mirdej/synkie/eagle/sk200-vcf-singlepole/sk200-vcf-singlepole.pdf

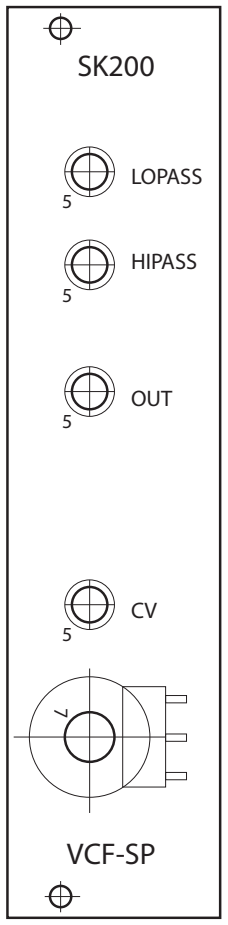
[picture p21: figure]
LOPASS; HIPASS; OUT; VCF-SP
