mirdej/synkie/kicad/synkie_footprint_models/PTL20-10G0-103B2.STEP

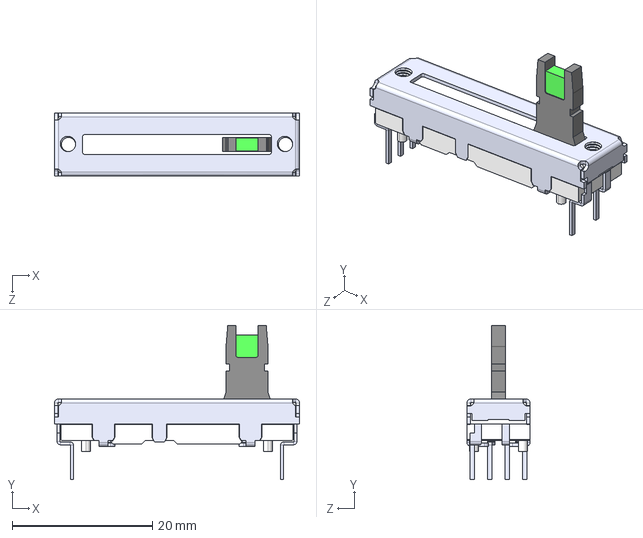
[picture p37: CAD file, 2025-10-26]
kicad/synkie_footprint_models/PTL20-10G0-103B2.STEP
35.0 x 22.0 x 9.00 mm
