mirdej/synkie/kicad/synkie_footprint_models/RK09K1130A70.stp

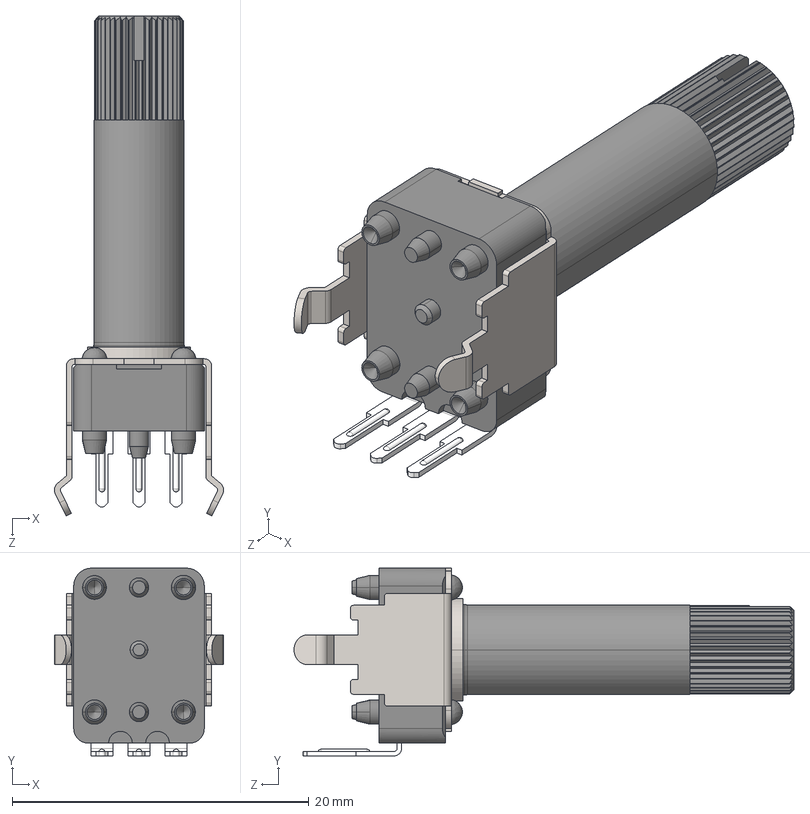
[picture p38: CAD file, 2025-10-26]
kicad/synkie_footprint_models/RK09K1130A70.stp
11.4 x 12.7 x 33.7 mm
