mirdej/synkie/kicad/synkie_footprint_models/SKQGAKE010.stp

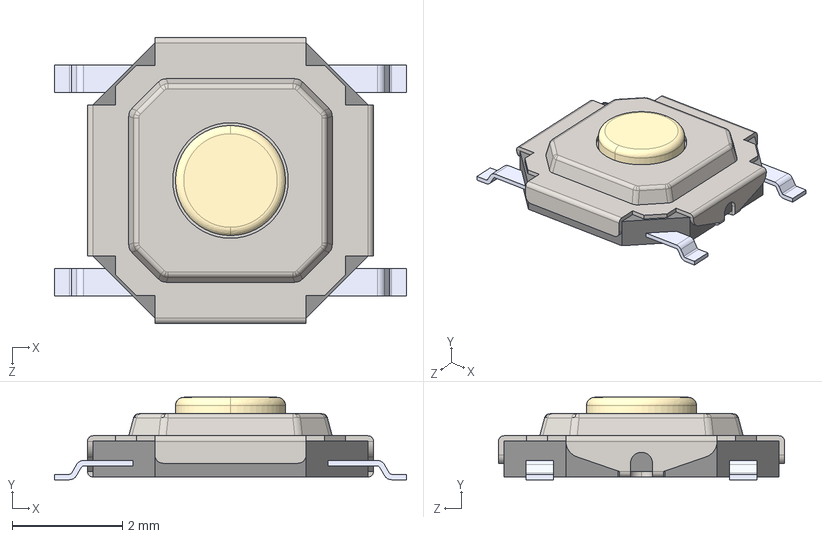
[picture p39: CAD file, 2025-10-26]
kicad/synkie_footprint_models/SKQGAKE010.stp
6.40 x 1.50 x 5.20 mm
SKQGADE010
SKQGADE010_4
SKQGADE010_3
SKQGADE010_7
SKQGADE010_2
SKQGADE010_6
SKQGADE010_5
