mirdej/synkie/kicad/synkie_footprint_models/PJ301M-12 Thonkiconn v0.2.stp

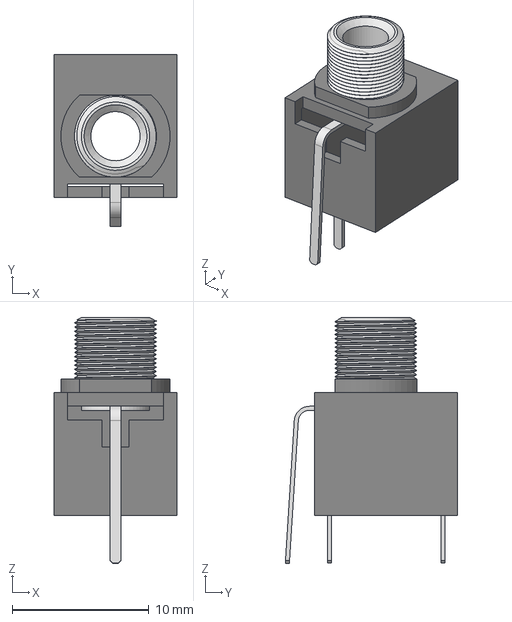
[picture p40: CAD file, 2025-10-26]
kicad/synkie_footprint_models/PJ301M-12 Thonkiconn v0.2.stp
9.00 x 12.6 x 18.0 mm
