mirdej/synkie/eagle/sk160-6channel-mixer/sk160-6channel-faders_pcb.pdf

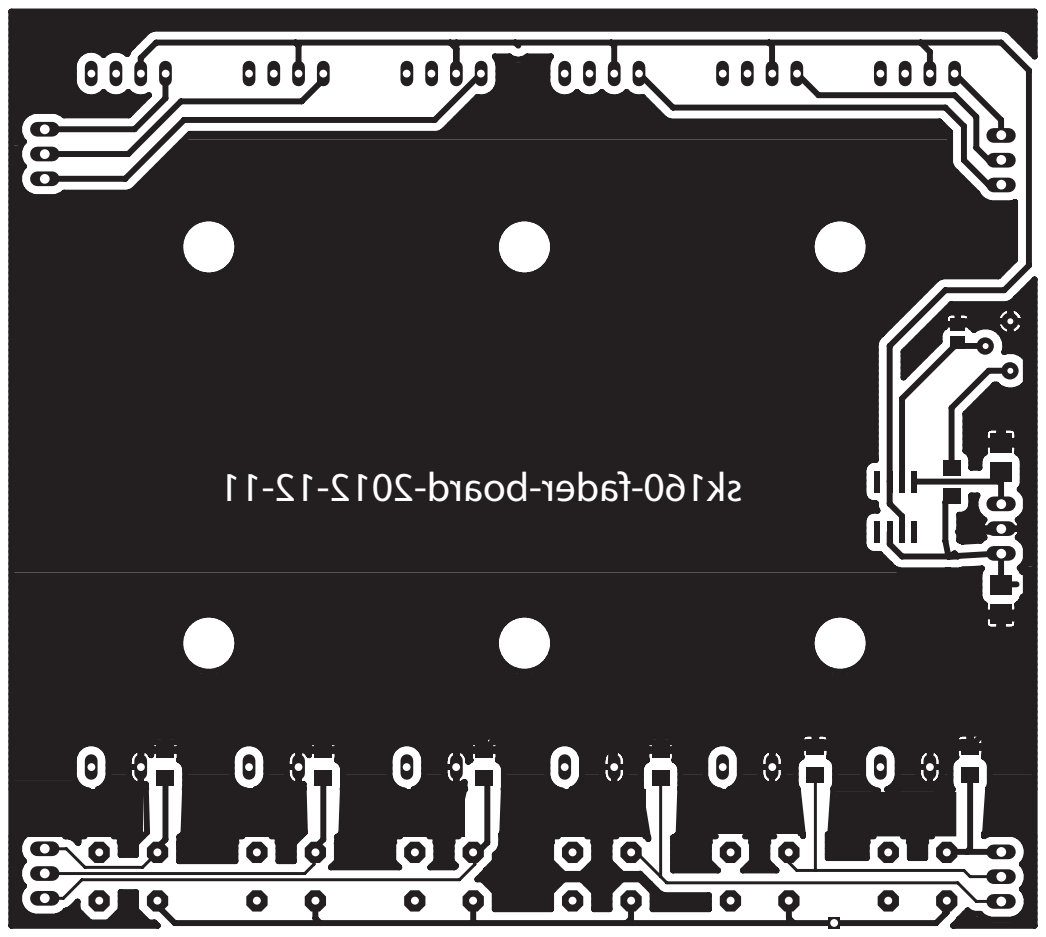
[picture p41: page 1]
sk160-fader-board-2012-12-11
