mirdej/synkie/kicad/digipotitest/digipotitest-F.Cu.pdf

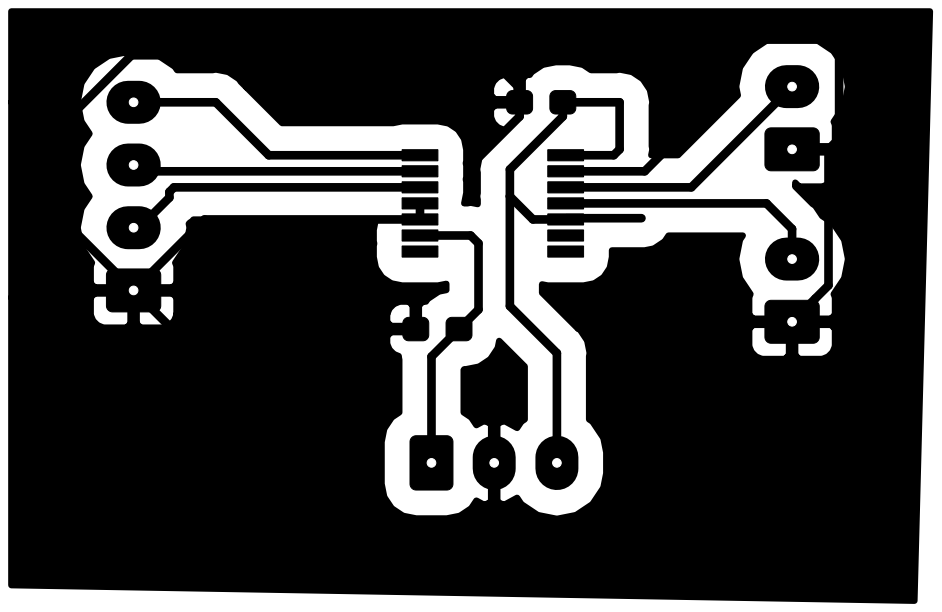
[picture p49: page 1]
