mirdej/synkie/kicad/digipotitest/digipotitest-F.Mask.pdf

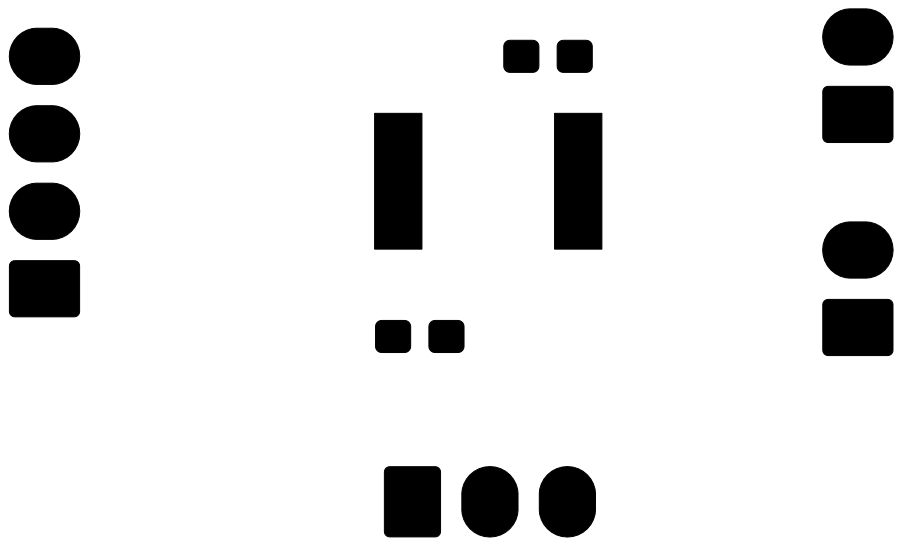
[picture p50: page 1]
