mirdej/synkie/kicad/digipotitest/digipotitest-F.Paste.pdf

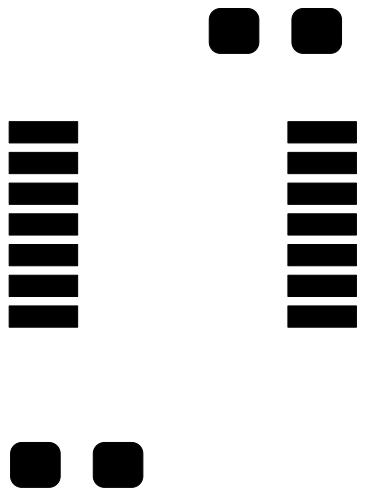
[picture p51: page 1]
