mirdej/synkie/kicad/digipotitest/digipotitest-F.SilkS.pdf

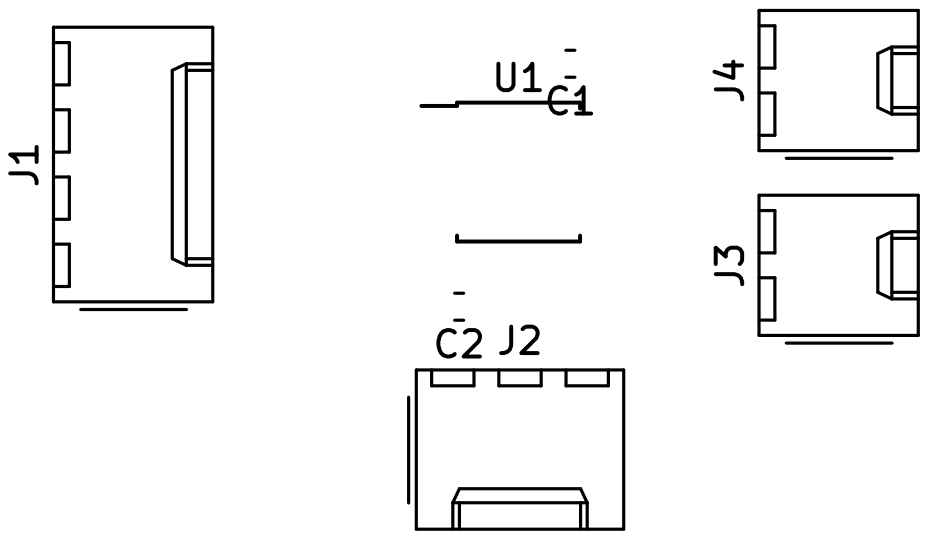
[picture p52: page 1]
