mirdej/synkie/kicad/sk950-teensy-osc/sk950-teensy-osc-B.Cu.pdf

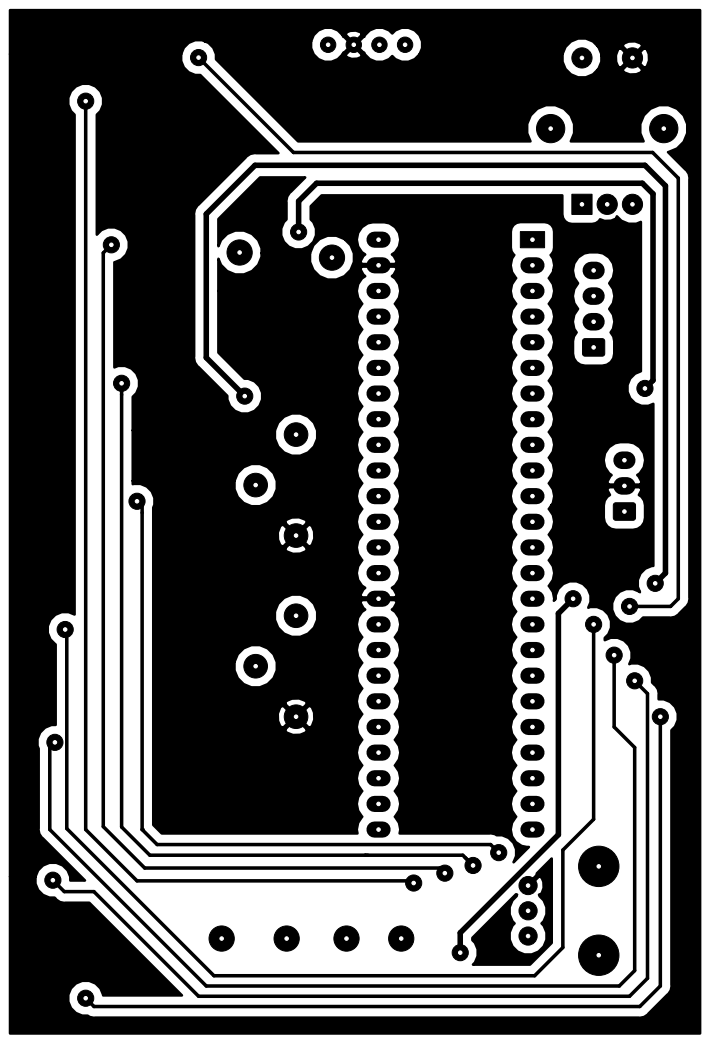
[picture p53: page 1]
