mirdej/synkie/kicad/sk950-teensy-osc/sk950-teensy-osc-F.Cu.pdf

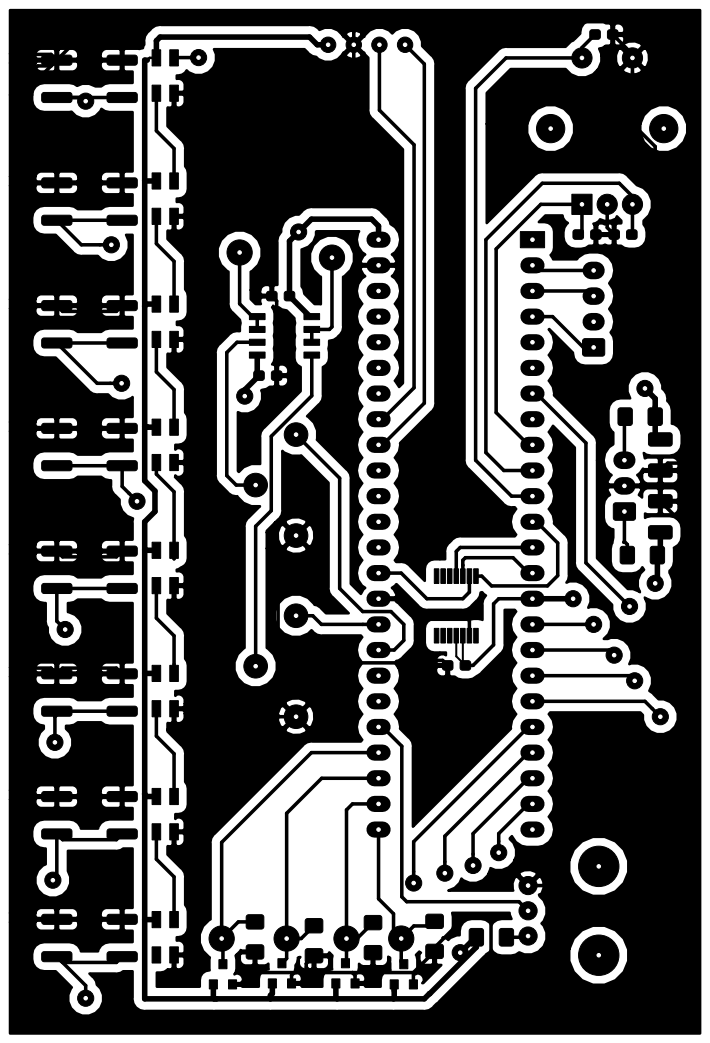
[picture p54: page 1]
