mirdej/synkie/eagle/sk53-audio2cv/sk53-frontplate.pdf

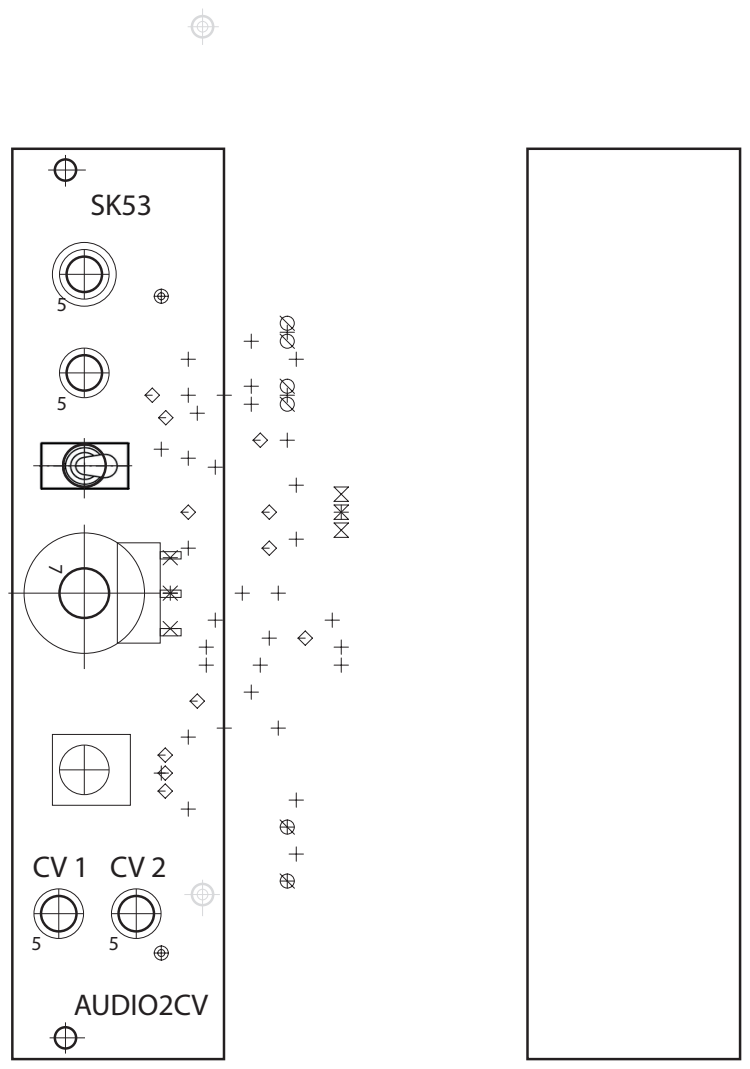
[picture p55: page 1]
AUDIO2CV
