mirdej/synkie/eagle/sk800-rgb/sk800-rgb-frontplate.pdf

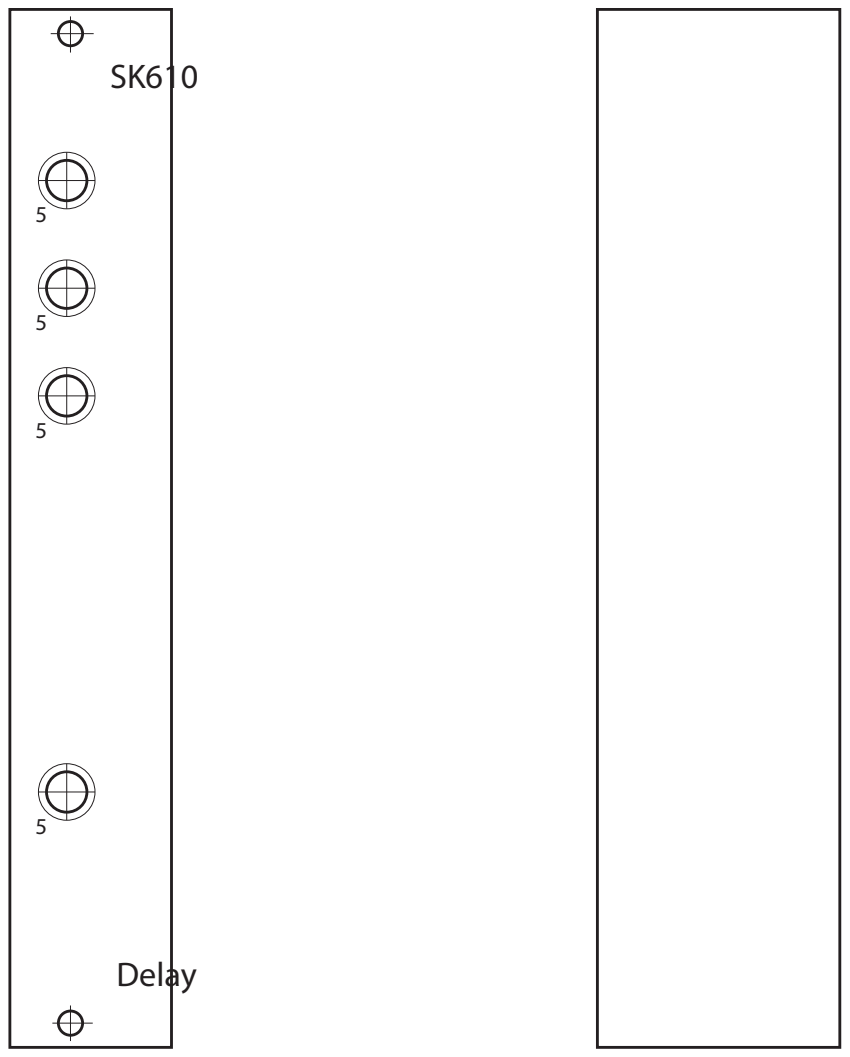
[picture p57: page 1]
Delay
