mirdej/synkie/eagle/sk500-6-cv-pots/sk500-6-cv-pots.pdf

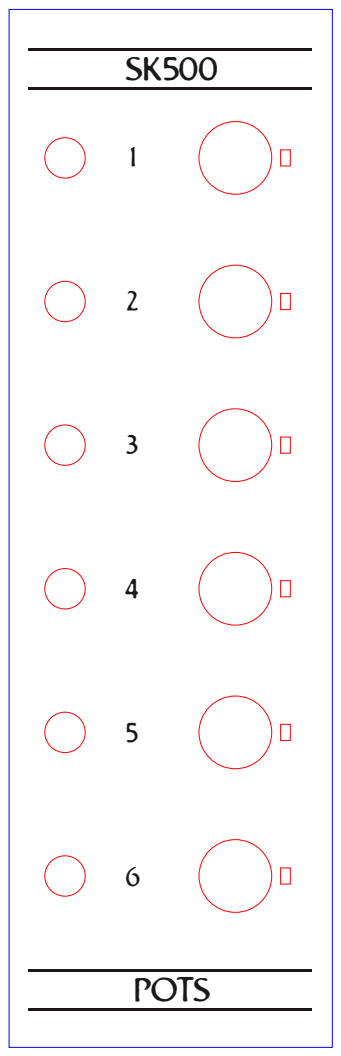
[picture p58: page 1]
SCABI; POTS
