mirdej/synkie/eagle/sk506-cv-looper/sk506-frontplate.pdf

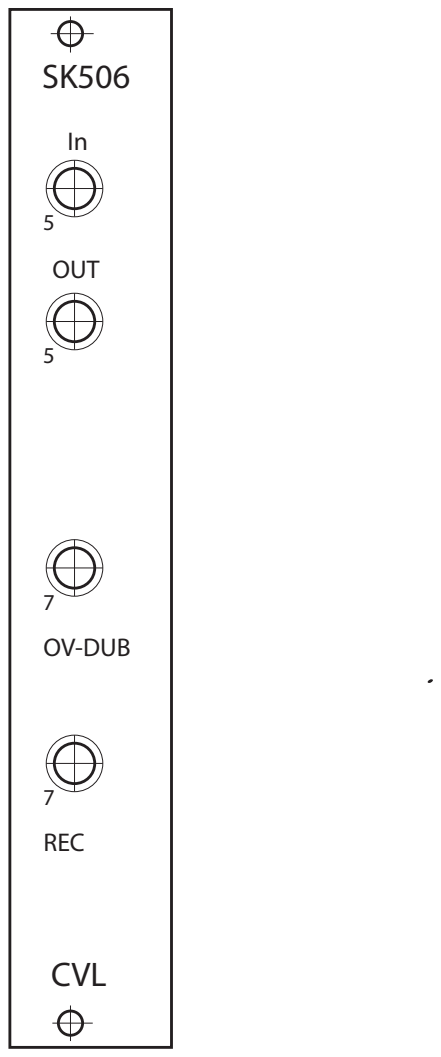
[picture p59: page 1]
REC; OV-DUB; OUT; CVL
