mirdej/synkie/eagle/sk505-lut/sk505-lut-frontplate.pdf

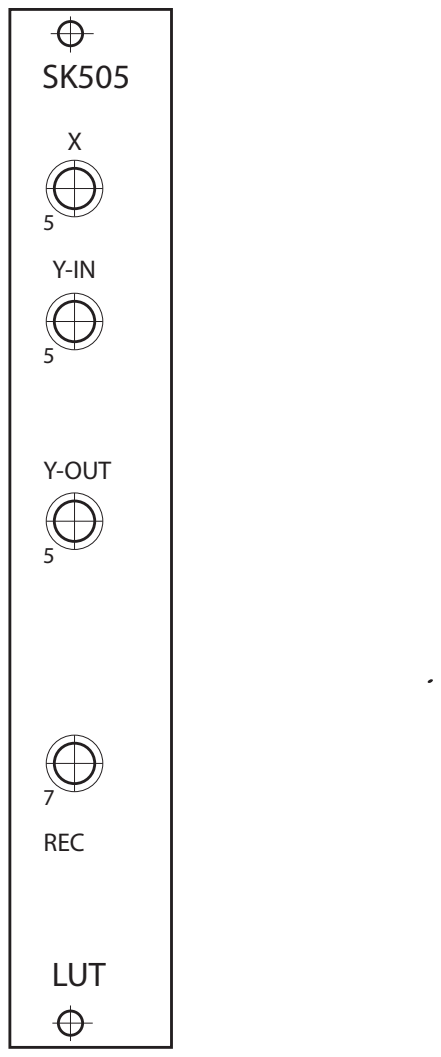
[picture p60: page 1]
Y-OUT; REC; LUT
