mirdej/synkie/eagle/sk610-delay/sk610-delay-frontplate.pdf

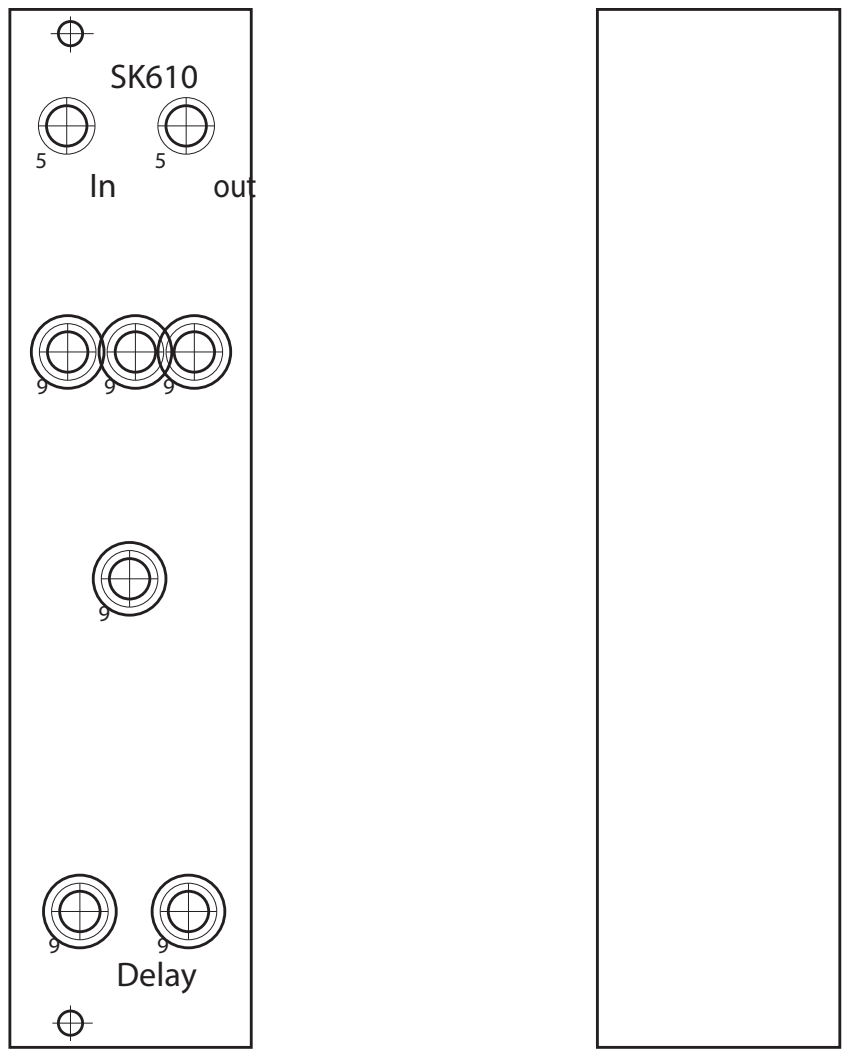
[picture p61: page 1]
Delay; out
