mirdej/synkie/eagle/sk535-audio-envelope/sk535-frontplate.pdf

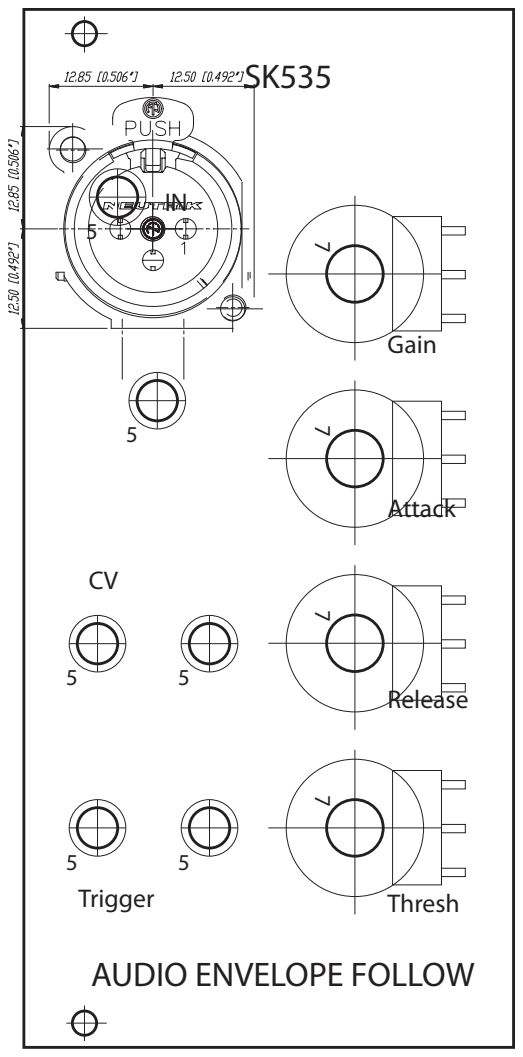
[picture p62: page 1]
Gain; Attack; Release; Thresh

Trigger
AUDIO ENVELOPE FOLLOW
