mirdej/synkie/eagle/sk08-inverter/sk08-inverter.pdf

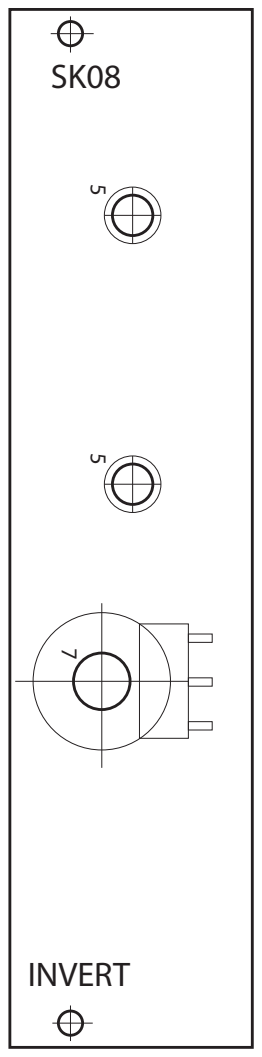
[picture p63: page 1]
INVERT
