mirdej/synkie/eagle/sk50-lfo_triple/sk50-lfo-frontplate.pdf

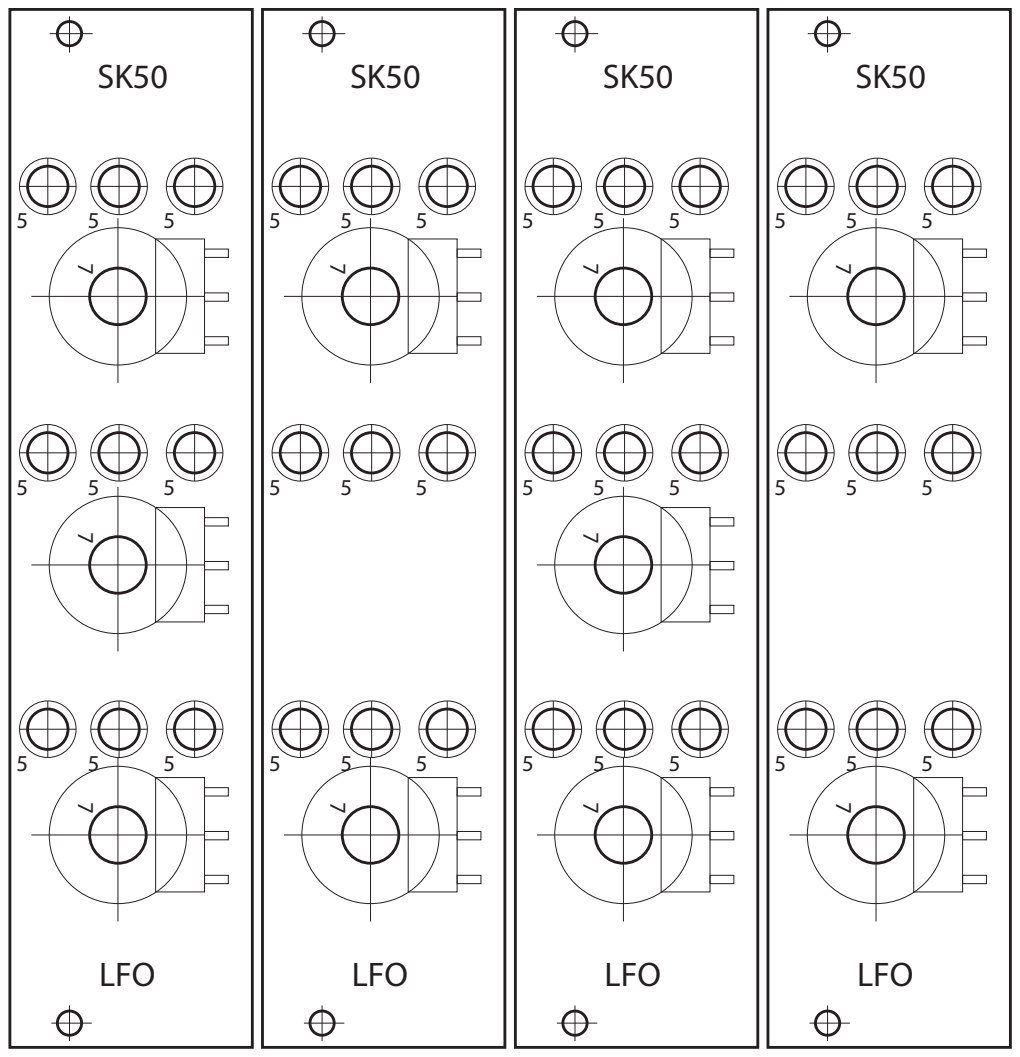
[picture p64: page 1]
LFO
