mirdej/synkie/eagle/sk165-3x3-matrix-mixer/sk165-3x3-matrix.pdf

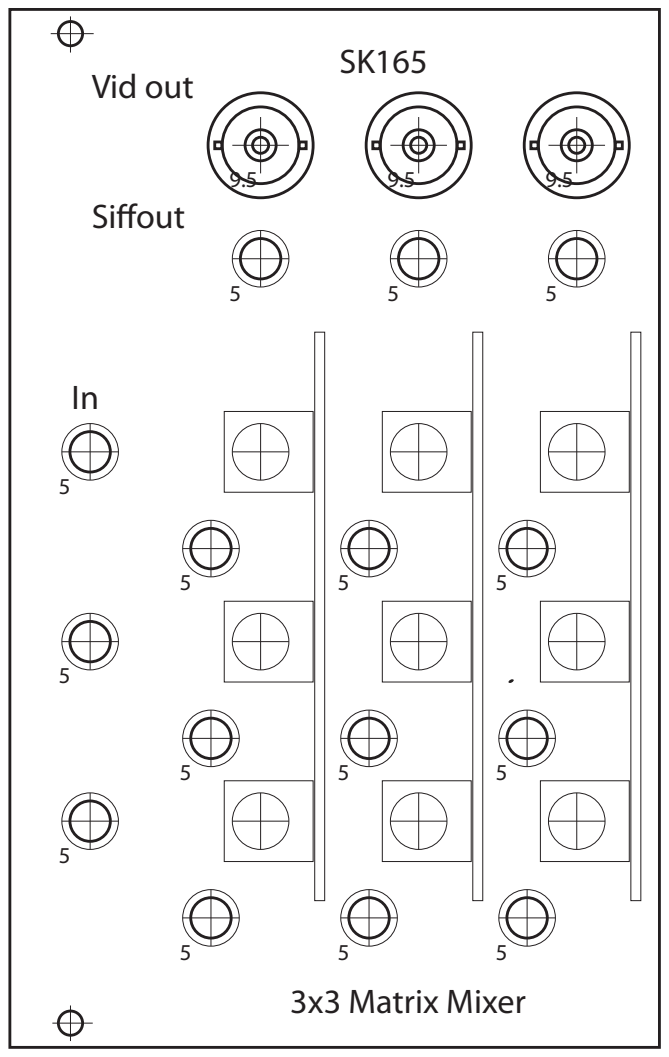
[picture p65: page 1]
Vid out; Siout; 3x3 Matrix Mixer
