mirdej/synkie/eagle/sk160-6channel-mixer/sk160-frontplate.pdf

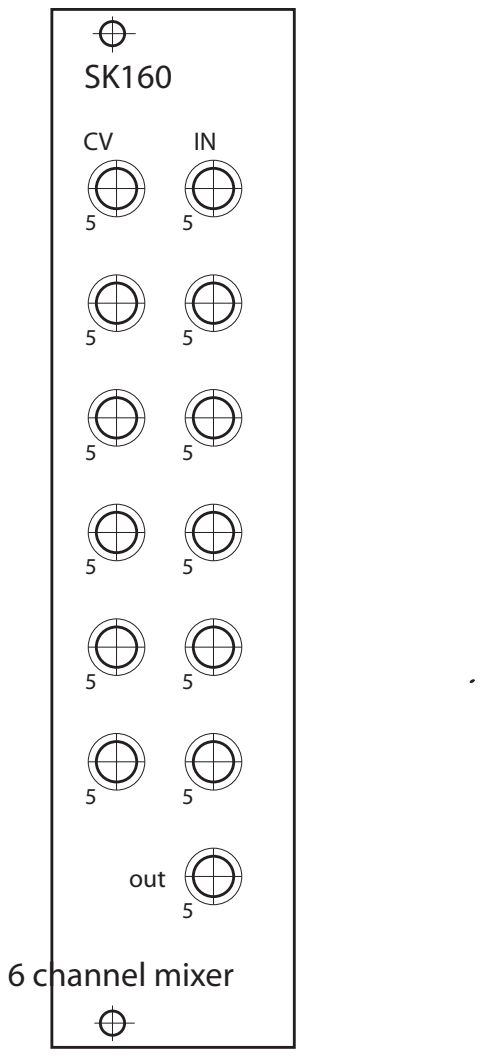
[picture p66: page 1]
out; 6 channel mixer
