mirdej/synkie/eagle/sk109-scale-bias/top_place.pdf

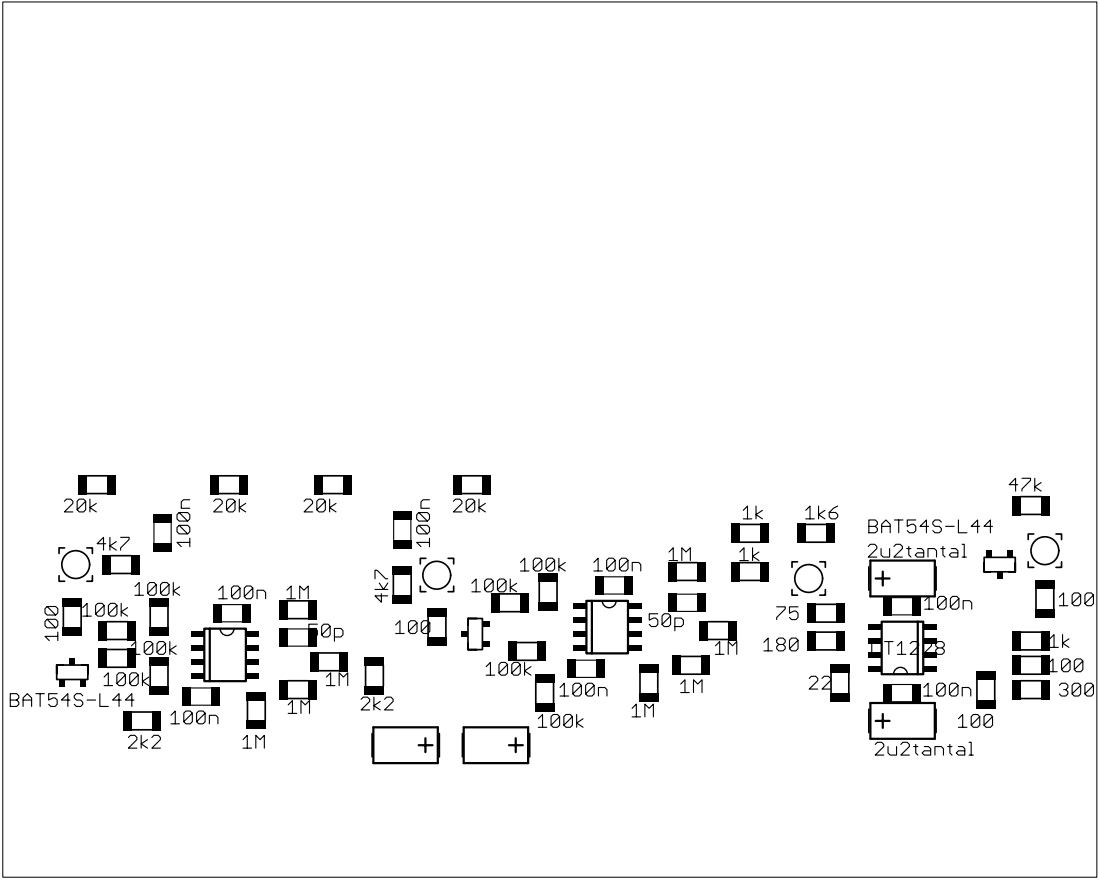
[picture p67: page 1]
