mirdej/synkie/eagle/sk00-supply/sk00-supply.pdf

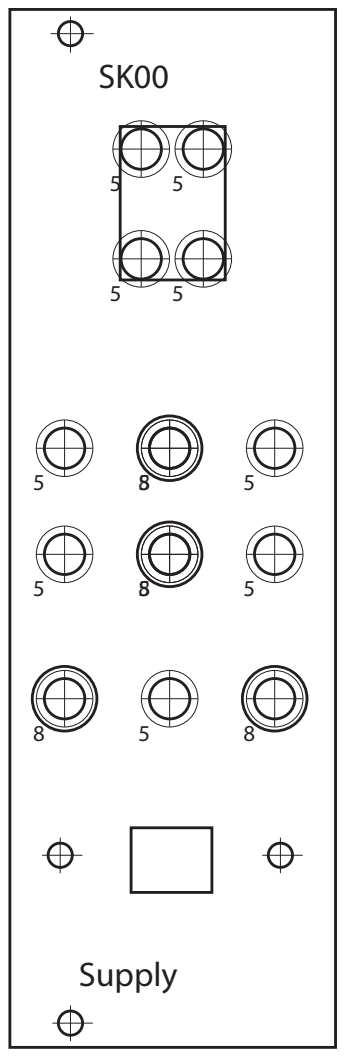
[picture p68: page 1]
Supply
