mirdej/synkie/eagle/sk130-gamma/sk130-gamma-frontplate.pdf

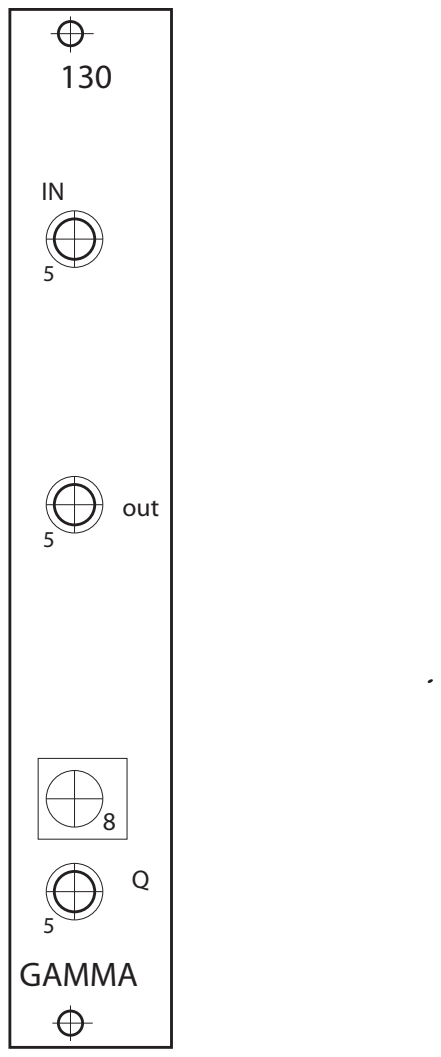
[picture p69: page 1]
out; GAMMA
