mirdej/synkie/eagle/sk210-state-variable-filter/sk210-state-variable-filter-frontplate.pdf

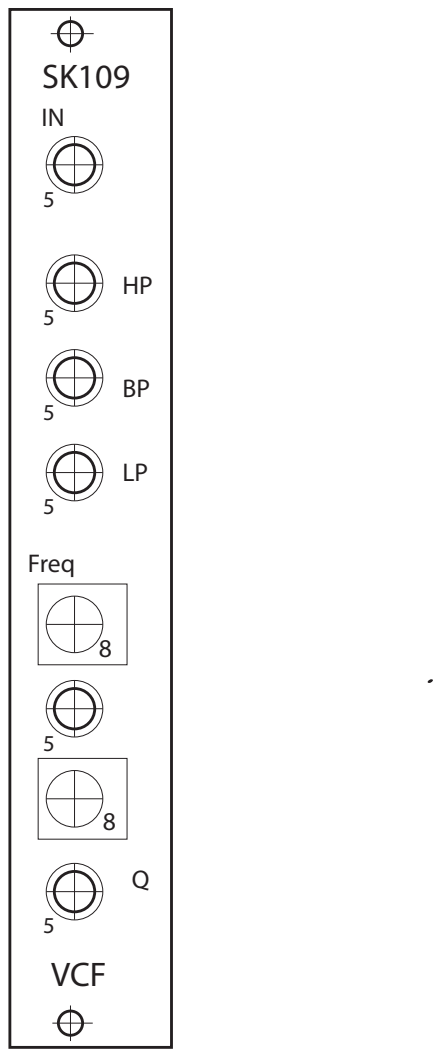
[picture p70: page 1]
Freq; VCF
