mirdej/synkie/eagle/sk-base-bus/sk-base-bus-pcb.pdf

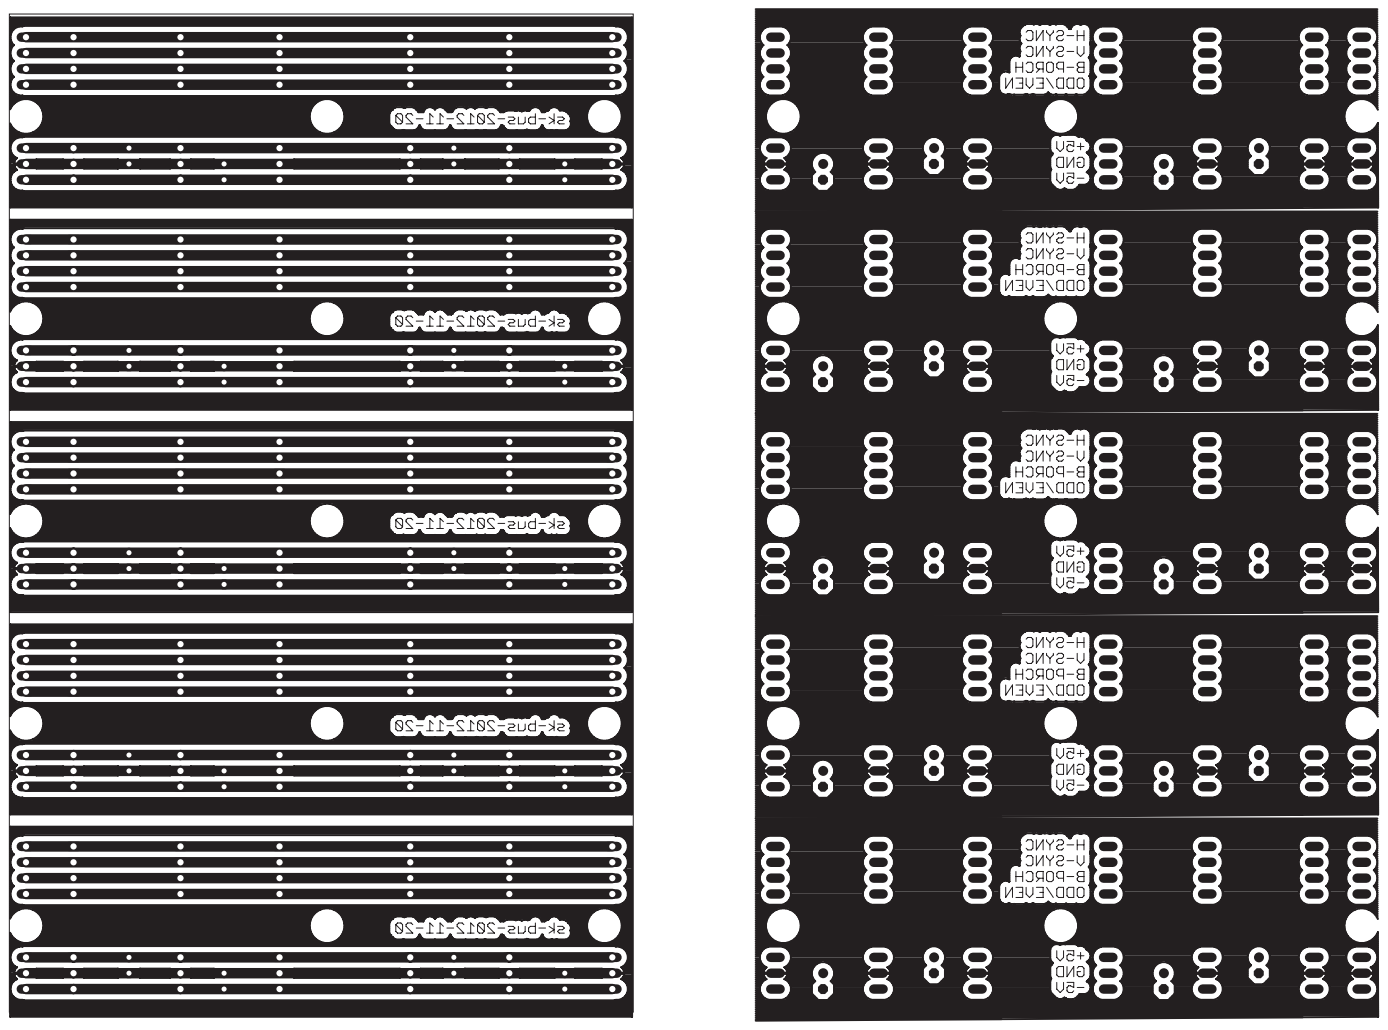
[picture p71: page 1]
