mirdej/synkie/eagle/sk520-adsr/sk520-frontplate.pdf

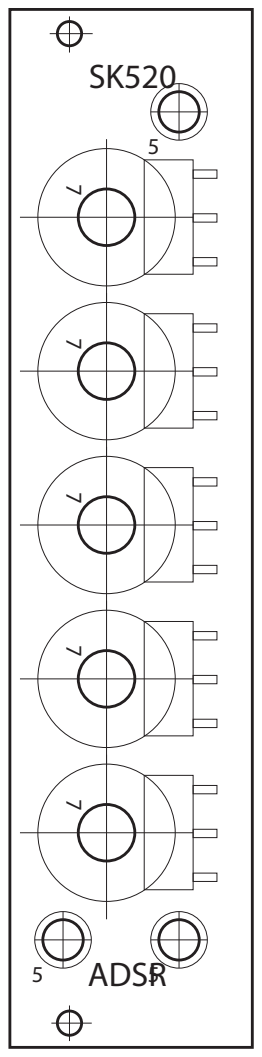
[picture p72: page 1]
ADSR
