mirdej/synkie/eagle/sk109-scale-bias/sk109-scale-bias.pdf

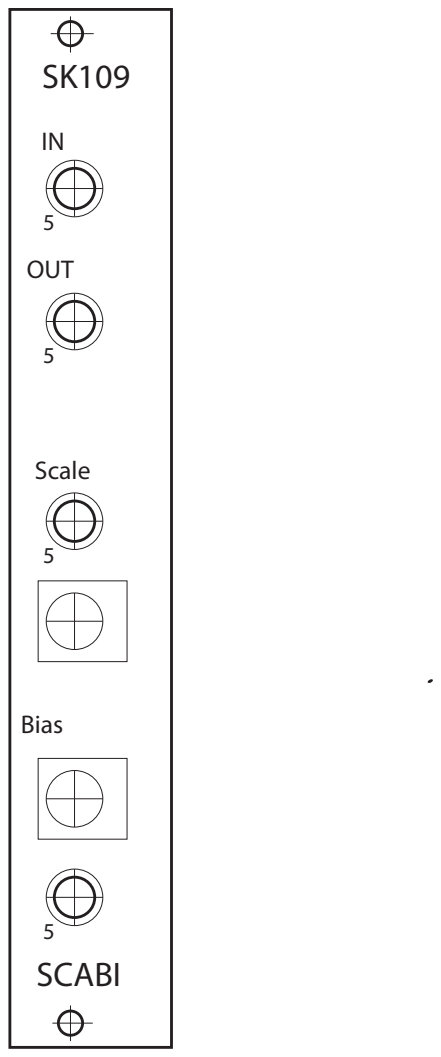
[picture p73: page 1]
Scale; Bias; OUT; SCABI
