mirdej/synkie/eagle/sk100-vca/sk100-vca-frontplate.pdf

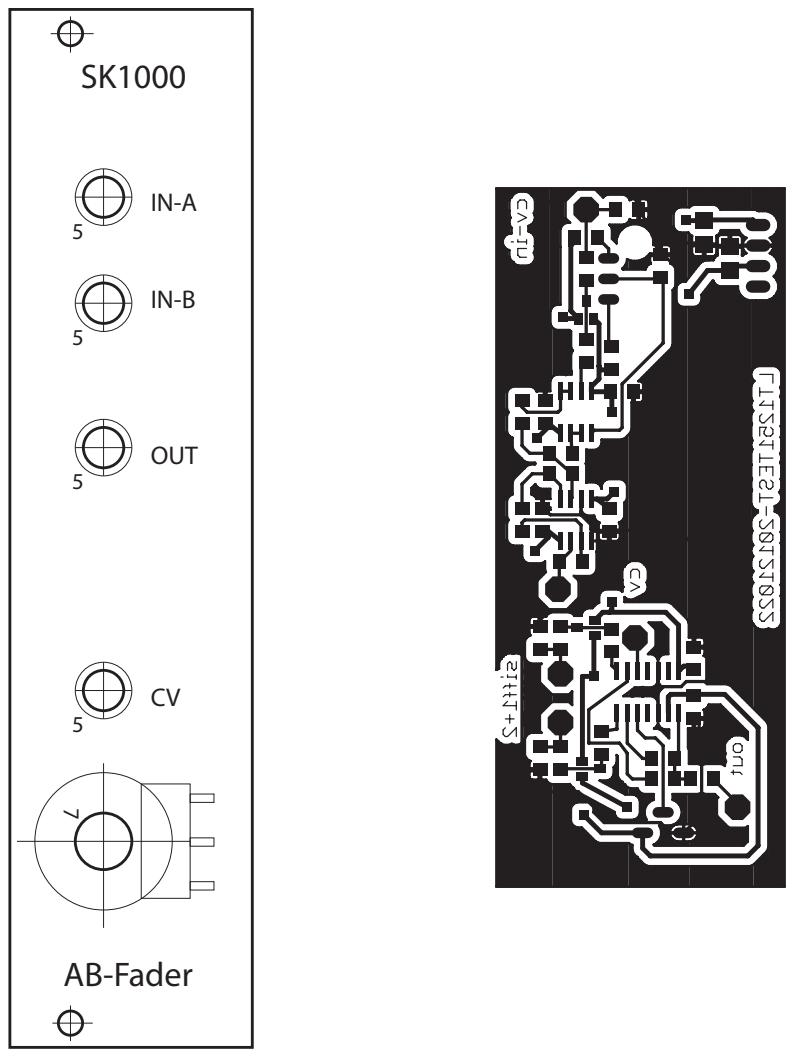
[picture p74: page 1]
OUT; AB-Fader
