mirdej/synkie/eagle/sk006-sync-buf/sk006-frontplate.pdf

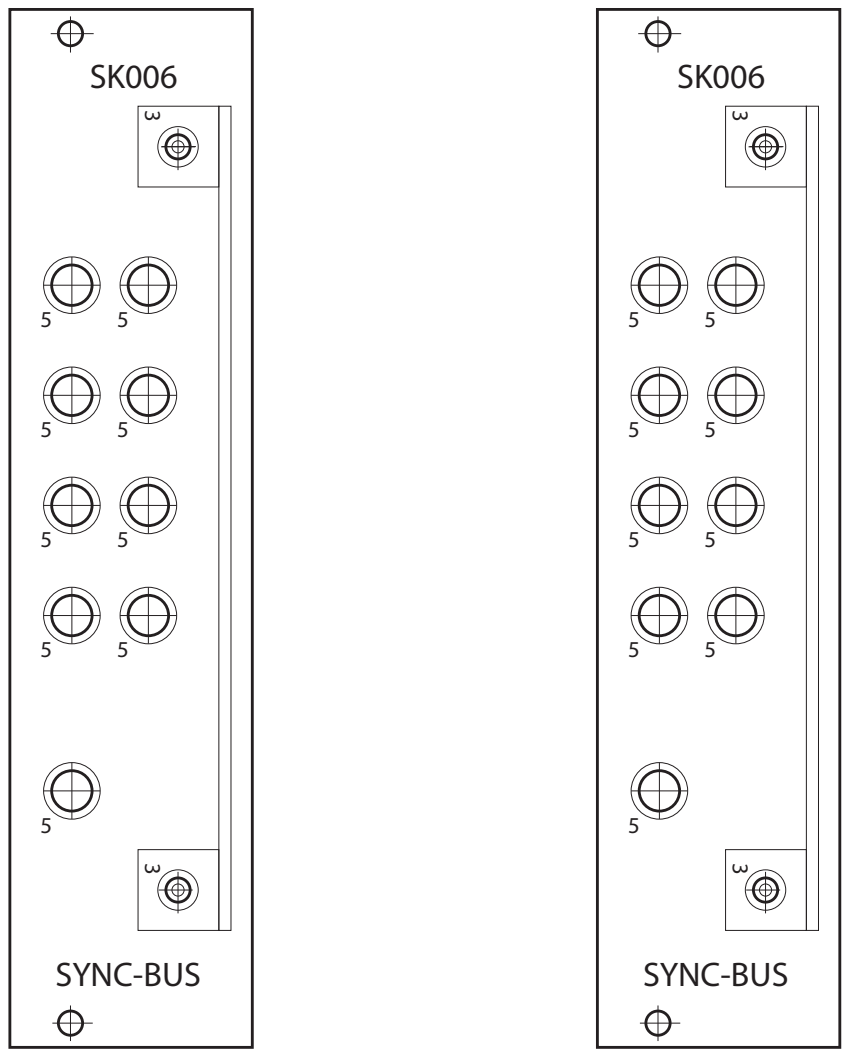
[picture p75: page 1]
SYNC-BUS
