mirdej/synkie/kicad/sk101-inAndOut-frontplate/sk101-inAndOut-frontplate.kicad_pcb

## KiCad design kicad/sk101-inAndOut-frontplate/sk101-inAndOut-frontplate.kicad_pcb (2026-09-02)

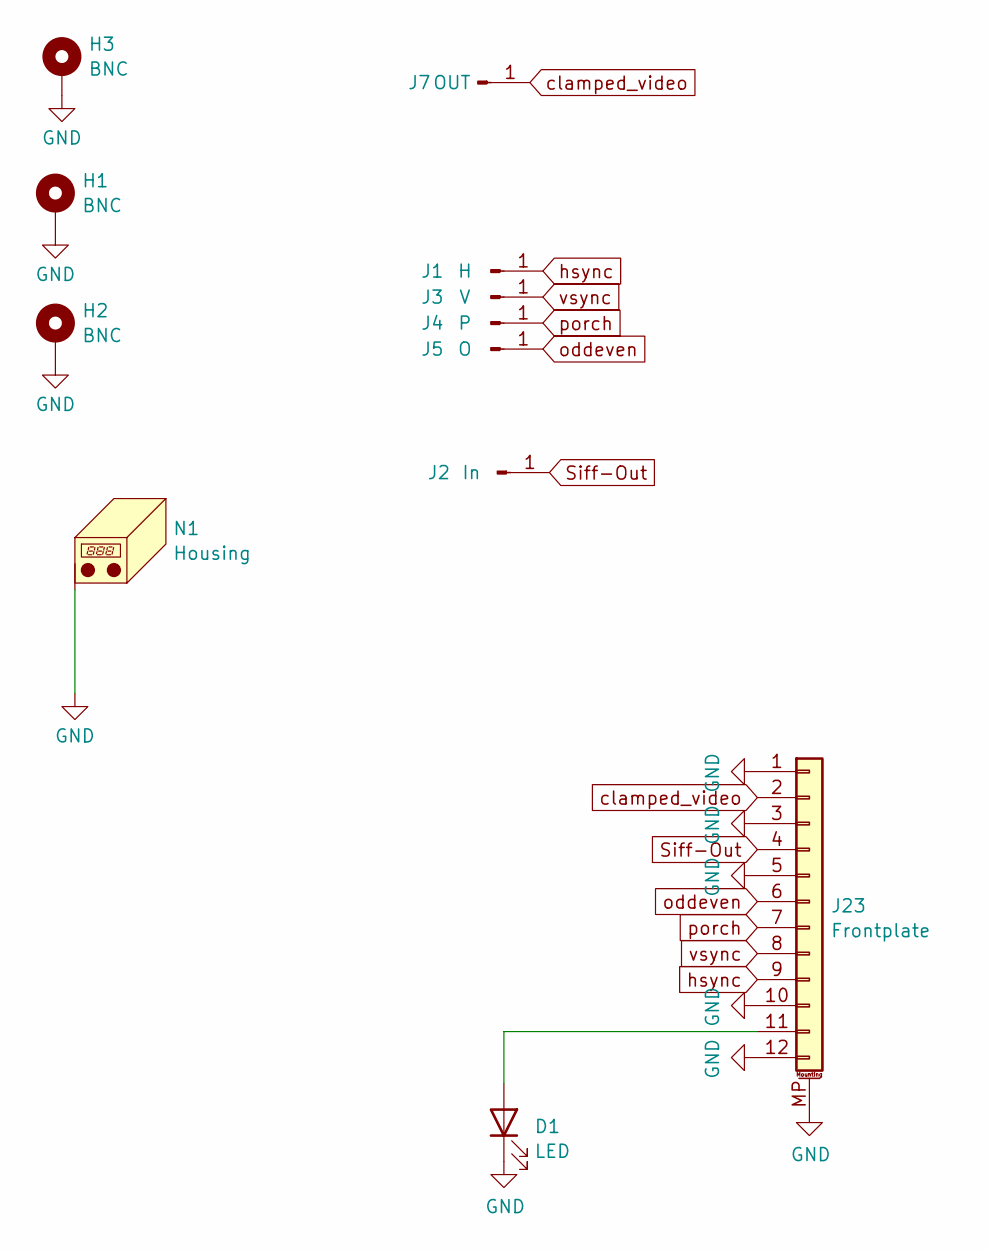
[picture p115: schematic sk101-inAndOut-frontplate.kicad_sch]

Parts:
D1: LED; LED_1206_3216Metric_ReverseMount_Hole1.8x2.4mm; LCSC C125108
H1, H2, H3: BNC; BNC_Ali_Frontplate
J1: H; Banana2mm-Löthülse
J2: In; Banana2mm-Löthülse
J3: V; Banana2mm-Löthülse
J4: P; Banana2mm-Löthülse
J5: O; Banana2mm-Löthülse
J7: OUT; Banana2mm-Löthülse
J23: Frontplate; AFC04-S12FCC-00; LCSC C21275
N1: Housing; Frontplate_20mm

Connections:
GND: D1.1 (K), H1.1 (1_1), H2.1 (1_1), H3.1 (1_1), J23.1, J23.3, J23.5, J23.10, J23.12, J23.MP (MountPin), N1.1 (PAD_1)
unnamed: D1.2 (A), J23.11
Siff-Out: J2.1 (Pin_1_1), J23.4
clamped_video: J7.1 (Pin_1_1), J23.2
hsync: J1.1 (Pin_1_1), J23.9
oddeven: J5.1 (Pin_1_1), J23.6
porch: J4.1 (Pin_1_1), J23.7
vsync: J3.1 (Pin_1_1), J23.8

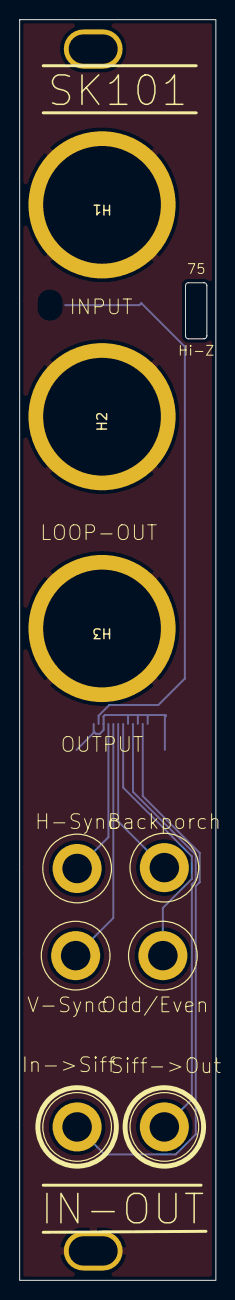
[picture p116: board sk101-inAndOut-frontplate.kicad_pcb from above]

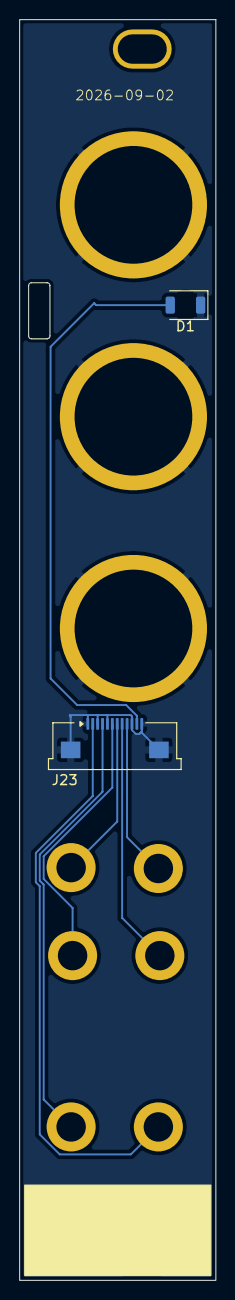
[picture p117: board sk101-inAndOut-frontplate.kicad_pcb from below]

Board: 2 copper layers, 20.0 x 128.5 mm, 12 parts (2 on the bottom side), 8 nets.
