mirdej/synkie/kicad/sk532-verticals/sk532-verticals.kicad_pcb

## KiCad design kicad/sk532-verticals/sk532-verticals.kicad_pcb (2026-09-01)

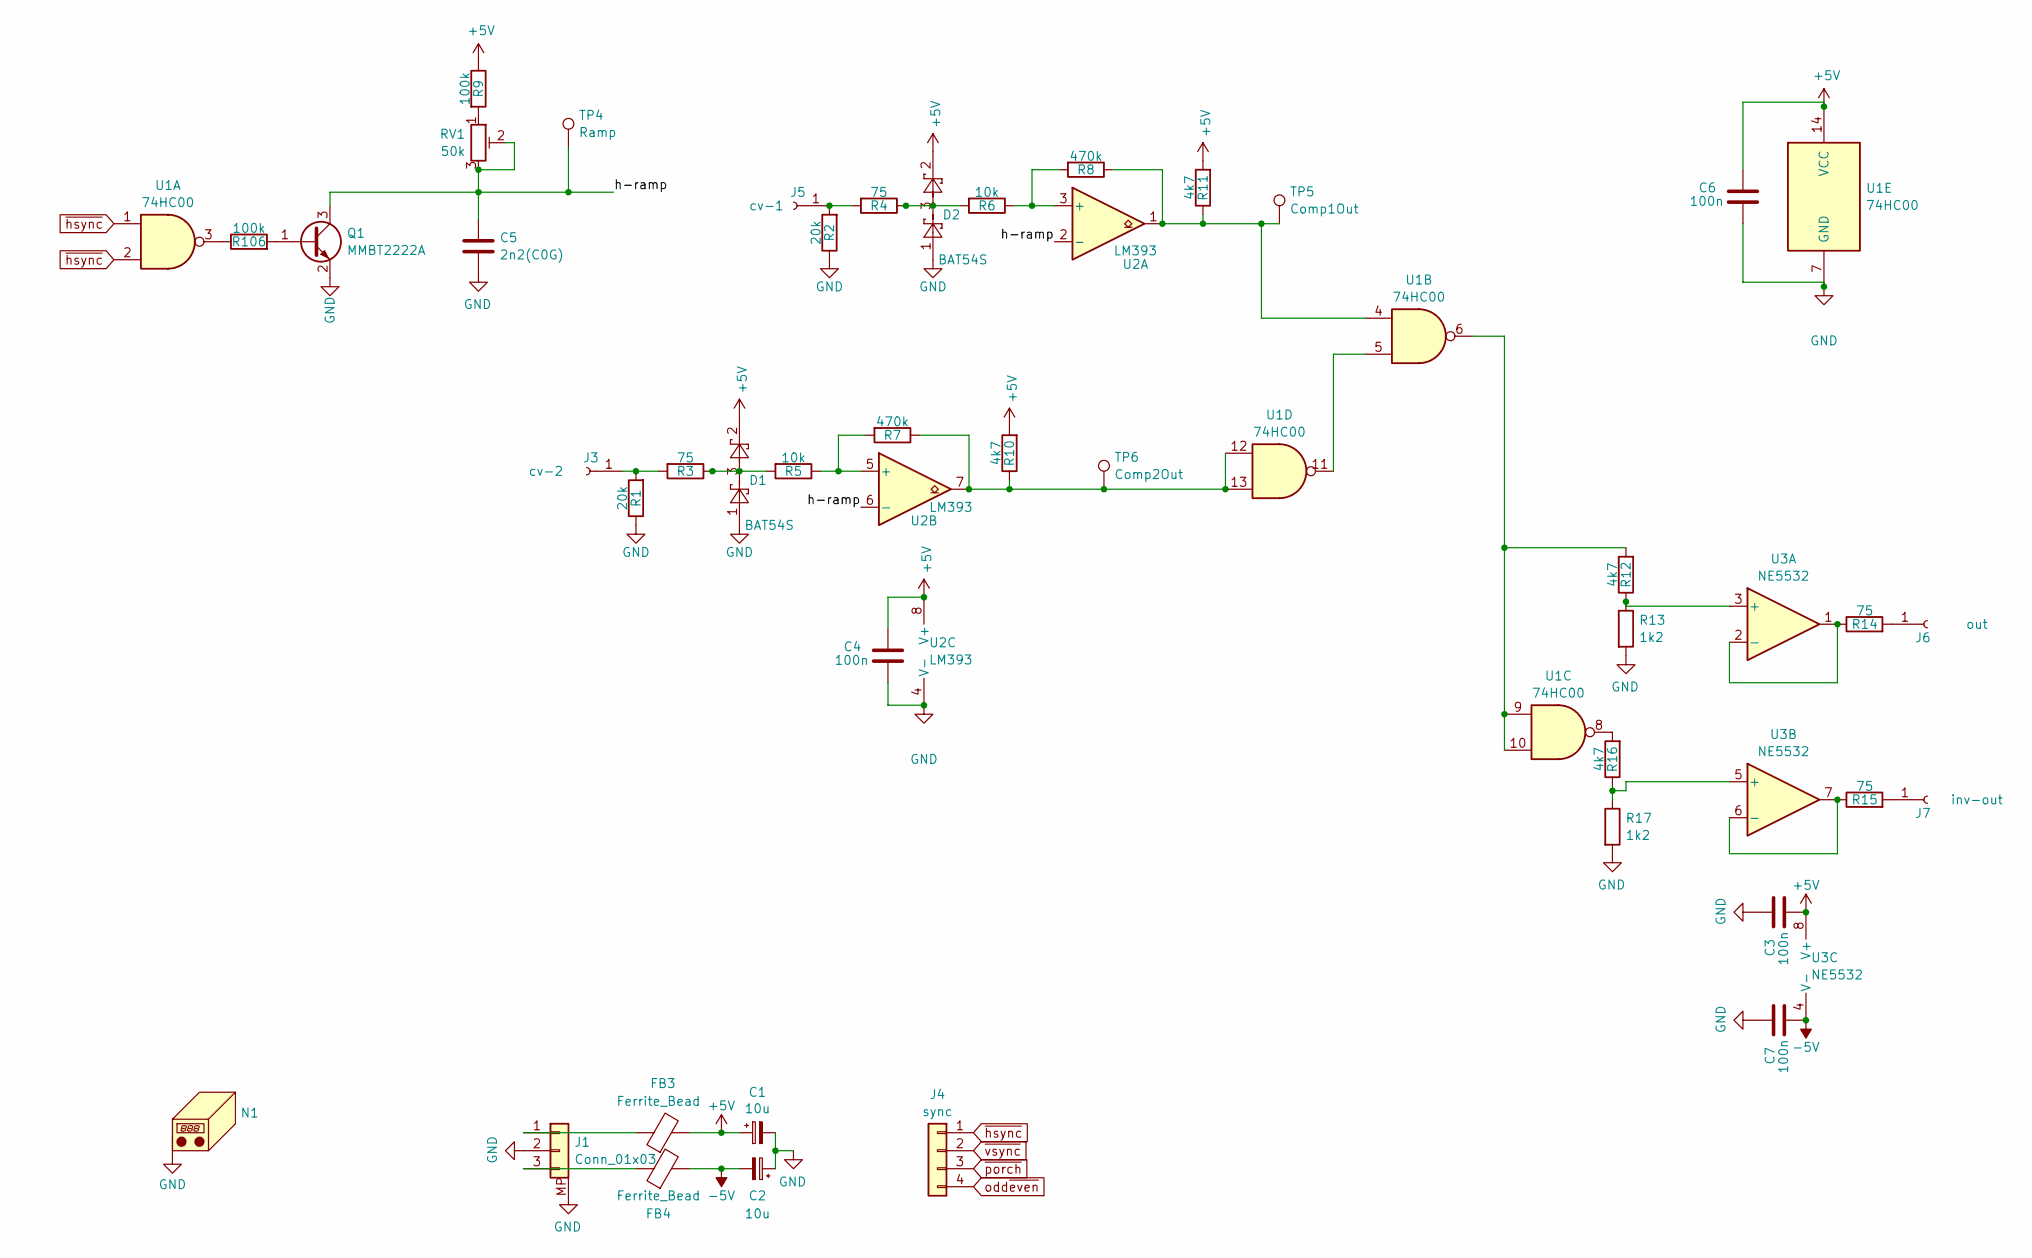
[picture p118: schematic sk532-verticals.kicad_sch]

Parts:
C1, C2: 10u; C_0805_2012Metric; LCSC C15850
C3, C4, C6, C7: 100n; C_0603_1608Metric; LCSC C14663
C5: 2n2(C0G); C_0805_2012Metric; LCSC C28260
D1, D2: BAT54S; SOT-23; LCSC C8592
FB3, FB4: Ferrite_Bead; L_0805_2012Metric; LCSC C1017
J1: Conn_01x03; Molex_PicoBlade_53398-0371_1x03-1MP_P1.25mm_Vertical; LCSC C293633
J3: cv-2; Banana2mm-Löthülse
J4: sync; Molex_PicoBlade_53398-0471_1x04-1MP_P1.25mm_Vertical; LCSC C17617036
J5: cv-1; Banana2mm-Löthülse
J6: out; Banana2mm-Löthülse
J7: inv-out; Banana2mm-Löthülse
N1: Housing_Pad; Frontplate_10mm
Q1: MMBT2222A; SOT-23; LCSC C8512
R1, R2: 20k; R_0603_1608Metric; LCSC C4184
R3, R4, R14, R15: 75; R_0603_1608Metric; LCSC C4275
R5, R6: 10k; R_0603_1608Metric; LCSC C25804
R7, R8: 470k; R_0603_1608Metric; LCSC C23178
R9, R106: 100k; R_0603_1608Metric; LCSC C25803
R10, R11, R12, R16: 4k7; R_0603_1608Metric; LCSC C23162
R13, R17: 1k2; LCSC C22765
RV1: 50k; Potentiometer_Bourns_3314J_Vertical; LCSC C50895
TP4: Ramp; TestPoint_Pad_D1.0mm
TP5: Comp1Out; TestPoint_Pad_D1.0mm
TP6: Comp2Out; TestPoint_Pad_D1.0mm
U1: 74HC00; SOIC-14_3.9x8.7mm_P1.27mm; LCSC C10090
U2: LM393; SOIC-8_3.9x4.9mm_P1.27mm; LCSC C7955
U3: NE5532; SOIC-8_3.9x4.9mm_P1.27mm; LCSC C7426

Connections:
+5V: C1.1, C3.2, C4.1, C6.1, D1.2, D2.2, FB3.2, R9.1, R10.2, R11.2, U1.14 (VCC), U2.8 (V+), U3.8 (V+)
-5V: C2.2, C7.2, FB4.2, U3.4 (V-)
/h-ramp: C5.1, Q1.3 (C), RV1.2, RV1.3, TP4.1 (1_1), U2.2 (-), U2.6 (-)
GND: C1.2, C2.1, C3.1, C4.2, C5.2, C6.2, C7.1, D1.1, D2.1, J1.2, J1.MP, N1.1 (PAD_1), Q1.2 (E), R1.1, R2.1, R13.2, R17.2, U1.7 (GND), U2.4 (V-)
unnamed: D1.3, R3.1, R5.2
unnamed: D2.3, R4.1, R6.2
unnamed: FB3.1, J1.1
unnamed: FB4.1, J1.3
unnamed: J3.1 (Pin_1_1), R1.2, R3.2
unnamed: J5.1 (Pin_1_1), R2.2, R4.2
unnamed: J6.1 (Pin_1_1), R14.2
unnamed: J7.1 (Pin_1_1), R15.2
unnamed: Q1.1 (B), R106.2
unnamed: R9.2, RV1.1
unnamed: R7.1, R10.1, TP6.1 (1_1), U1.12, U1.13, U2.7
unnamed: R8.1, R11.1, TP5.1 (1_1), U1.4, U2.1
unnamed: R12.2, U1.6, U1.9, U1.10
unnamed: R16.2, U1.8
unnamed: R106.1, U1.3
unnamed: U1.5, U1.11
unnamed: R6.1, R8.2, U2.3 (+)
unnamed: R5.1, R7.2, U2.5 (+)
unnamed: R12.1, R13.1, U3.3 (+)
unnamed: R14.1, U3.1, U3.2 (-)
unnamed: R16.1, R17.1, U3.5 (+)
unnamed: R15.1, U3.6 (-), U3.7
odd~even: J4.4
~hsync: J4.1, U1.1, U1.2
~porch: J4.3
~vsync: J4.2

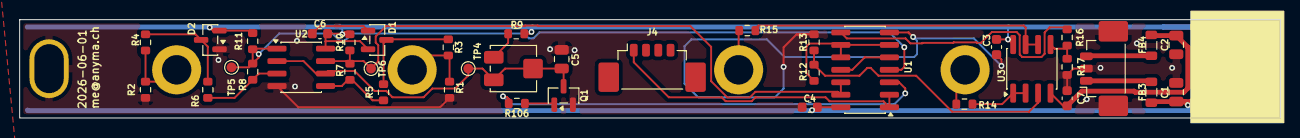
[picture p119: board sk532-verticals.kicad_pcb from above]

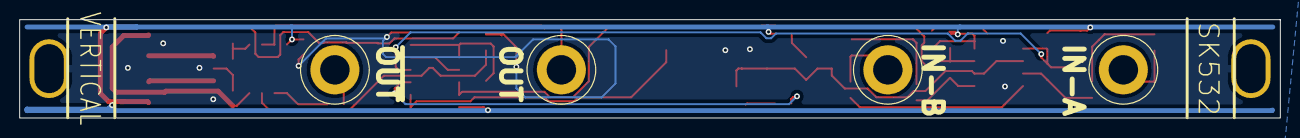
[picture p120: board sk532-verticals.kicad_pcb from below]

Board: 2 copper layers, 128.5 x 10.0 mm, 44 parts (5 on the bottom side), 27 nets.
