mirdej/synkie/kicad/sk003a-outputs-frontplate/sk003a-outputs-frontplate.kicad_pcb

## KiCad design kicad/sk003a-outputs-frontplate/sk003a-outputs-frontplate.kicad_pcb (2026-08-08)

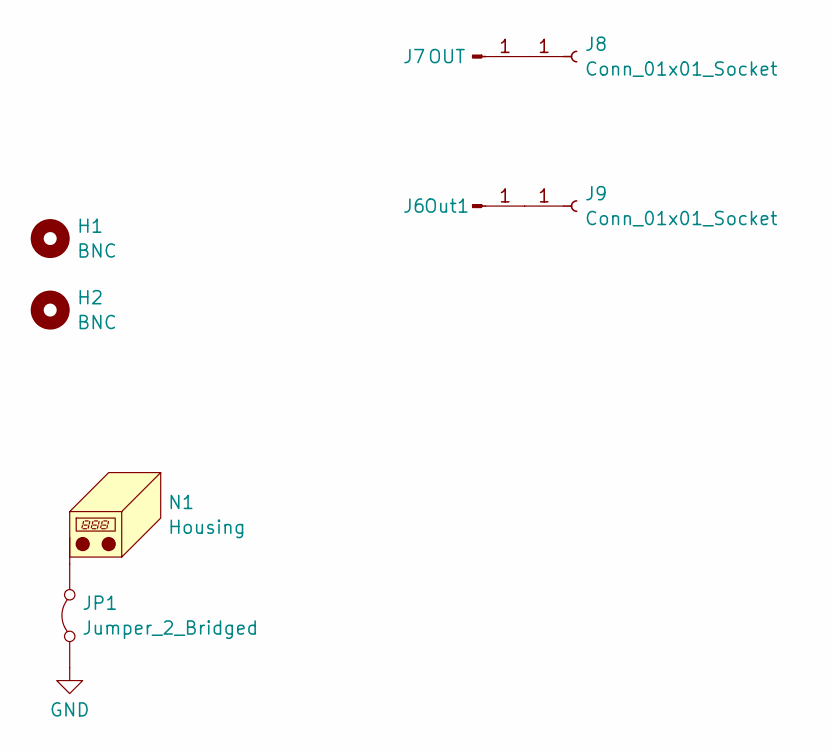
[picture p121: schematic sk003a-outputs-frontplate.kicad_sch]

Parts:
H1, H2: BNC; MolexBNCFrontpanel
J6: Out1; Banana2mm-Löthülse
J7: OUT; Banana2mm-Löthülse
J8, J9: Conn_01x01_Socket; smd-1pin
JP1: Jumper_2_Bridged; SolderJumper-2_P1.3mm_Bridged2Bar_Pad1.0x1.5mm
N1: Housing; Frontplate_20mm

Connections:
GND: JP1.1 (A)
unnamed: J6.1 (Pin_1_1), J9.1 (Pin_1_1)
unnamed: J7.1 (Pin_1_1), J8.1 (Pin_1_1)
unnamed: JP1.2 (B), N1.1 (PAD_1)

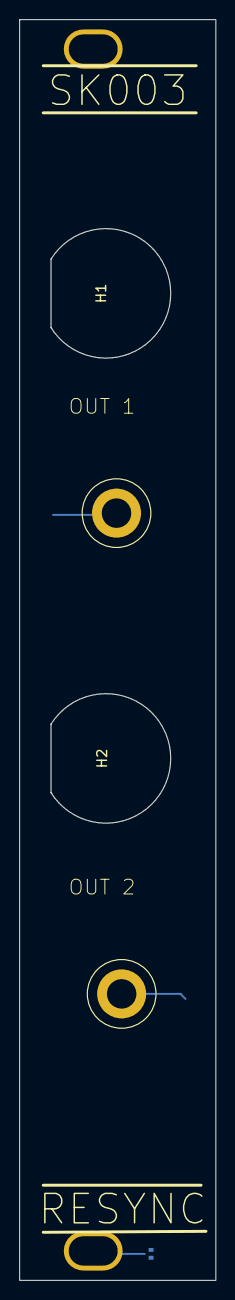
[picture p122: board sk003a-outputs-frontplate.kicad_pcb from above]

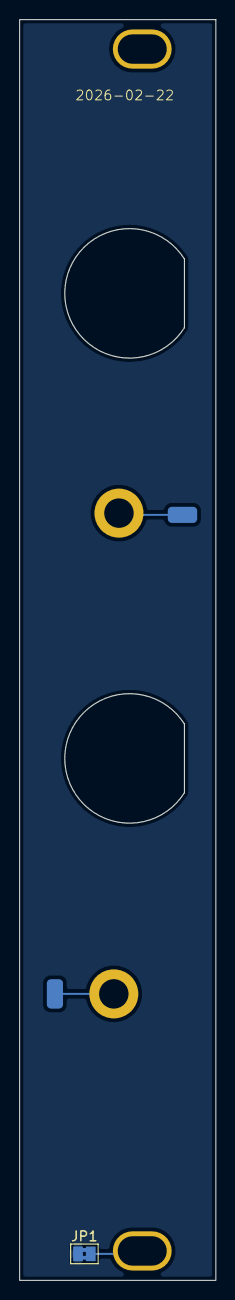
[picture p123: board sk003a-outputs-frontplate.kicad_pcb from below]

Board: 2 copper layers, 20.0 x 128.5 mm, 8 parts (3 on the bottom side), 3 nets.
