mirdej/synkie/kicad/sk003a-outbasic/sk003a-outbasic.kicad_pcb

## KiCad design kicad/sk003a-outbasic/sk003a-outbasic.kicad_pcb (2026-08-08)

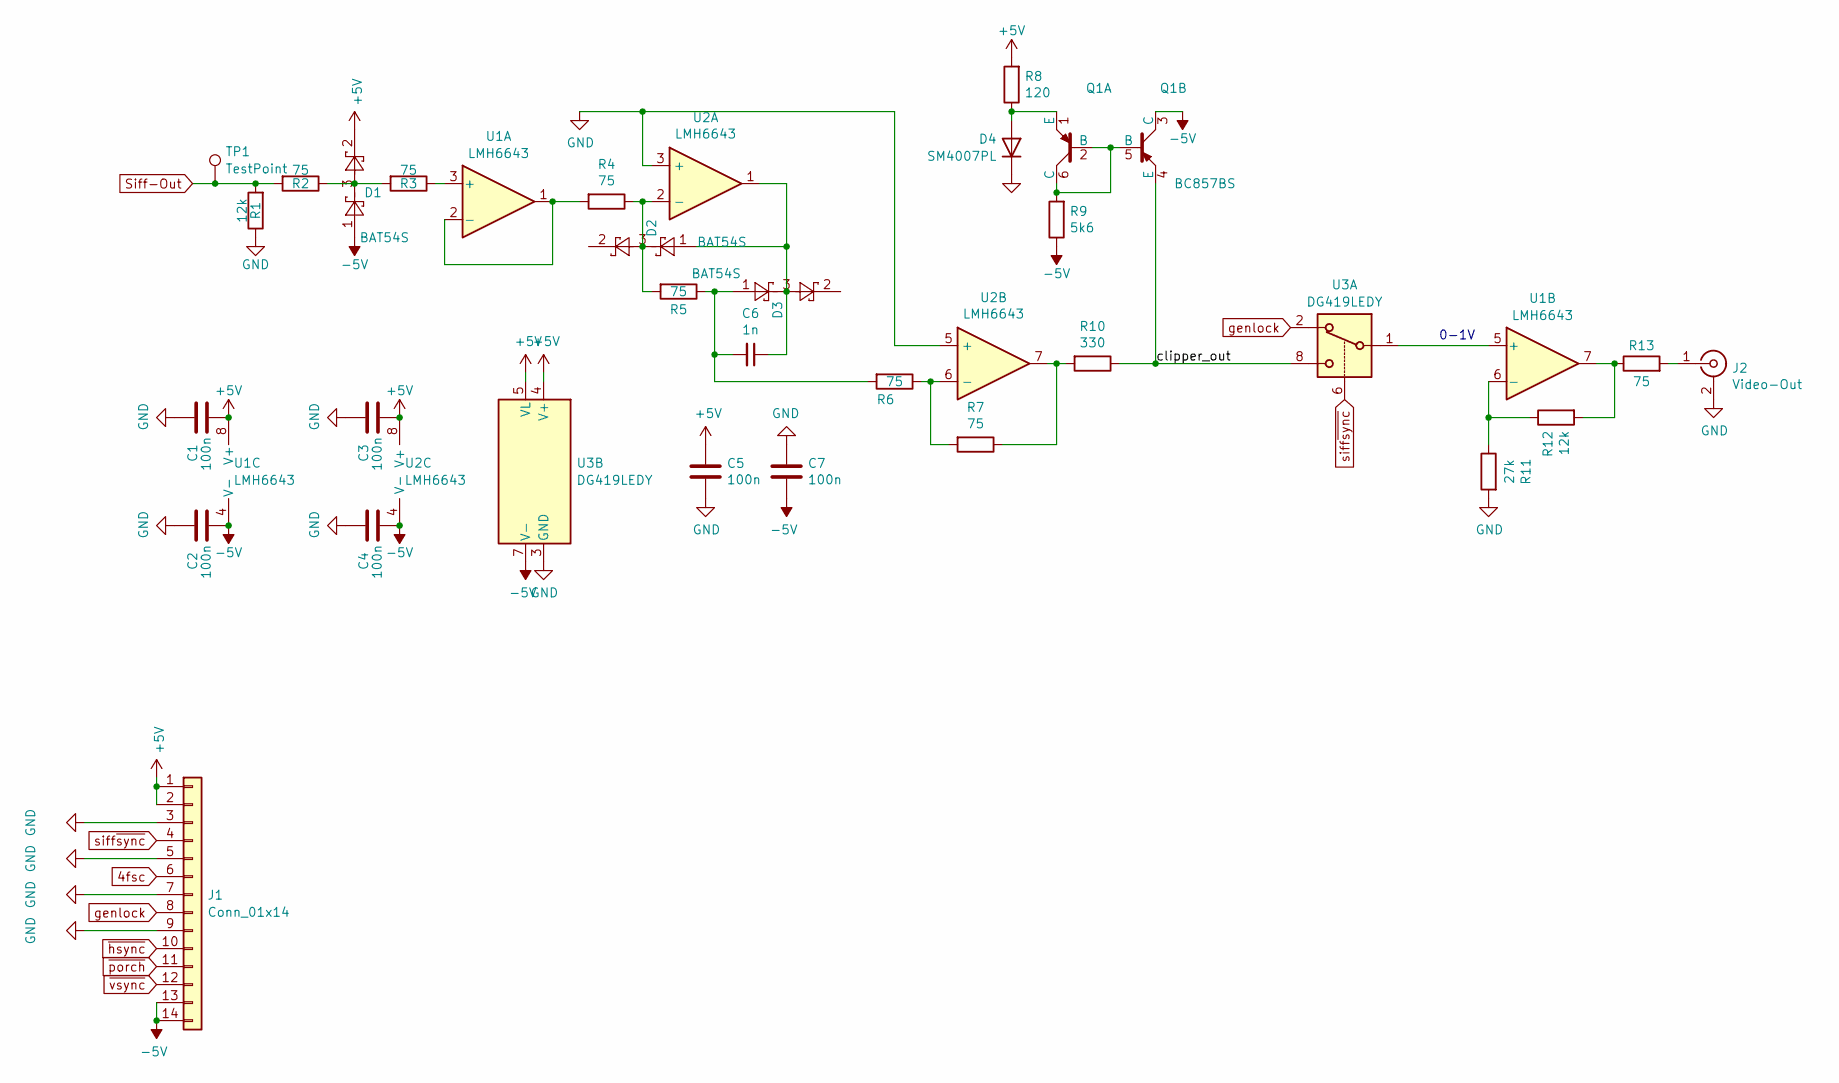
[picture p124: schematic sk003a-outbasic.kicad_sch]

Parts:
C1, C2, C3, C4, C5, C7: 100n; C_0603_1608Metric; LCSC C14663
C6: 1n; C_0603_1608Metric; LCSC C1588
D1, D2, D3: BAT54S; SOT-23; LCSC C7420333
D4: SM4007PL; D_SOD-123F; LCSC C64898
J1: Conn_01x14; SYNKIE-BUS.v3
J2: Video-Out; BNC_Aliexpress
Q1: BC857BS; SOT-363_SC-70-6_Handsoldering; LCSC C22381405
R1, R12: 12k; R_0603_1608Metric; LCSC C22790
R2, R3, R4, R5, R6, R7, R13: 75; R_0603_1608Metric; LCSC C4275
R8: 120; R_0603_1608Metric; LCSC C22787
R9: 5k6; R_0603_1608Metric; LCSC C23189
R10: 330; R_0603_1608Metric; LCSC C23138
R11: 27k; R_0603_1608Metric; LCSC C22967
TP1: TestPoint; TestPoint_THTPad_D4.0mm_Drill2.0mm
U1, U2: LMH6643; VSSOP-8_3x3mm_P0.65mm; LCSC C478382
U3: DG419LEDY; SOIC-8_3.9x4.9mm_P1.27mm; LCSC C2673265

Connections:
4fsc: J1.6
+5V: C1.2, C3.2, C5.1, D1.2, J1.1, J1.2, R8.2, U1.8 (V+), U2.8 (V+), U3.4 (V+), U3.5 (VL)
-5V: C2.2, C4.2, C7.2, D1.1, J1.13, J1.14, Q1.3 (C), R9.1, U1.4 (V-), U2.4 (V-), U3.7 (V-)
/clipper_out: Q1.4 (E), R10.1, U3.8
GND: C1.1, C2.1, C3.1, C4.1, C5.2, C7.1, D4.1 (K), J1.3, J1.5, J1.7, J1.9, J2.2 (Ext), R1.1, R11.2, U2.3 (+), U2.5 (+), U3.3 (GND)
unnamed: C6.1, D2.1, D3.3, U2.1
unnamed: C6.2, D3.1, R5.1, R6.2
unnamed: D1.3, R2.1, R3.2
unnamed: D4.2 (A), Q1.1 (E), R8.1
unnamed: J2.1 (In), R13.2
unnamed: Q1.2 (B), Q1.5 (B), Q1.6 (C), R9.2
unnamed: R7.1, R10.2, U2.7
unnamed: R12.2, R13.1, U1.7
unnamed: R3.1, U1.3 (+)
unnamed: R4.2, U1.1, U1.2 (-)
unnamed: U1.5 (+), U3.1
unnamed: R11.1, R12.1, U1.6 (-)
unnamed: D2.3, R4.1, R5.2, U2.2 (-)
unnamed: R6.1, R7.2, U2.6 (-)
Siff-Out: R1.2, R2.2, TP1.1 (1_1)
genlock: J1.8, U3.2
siff~sync: J1.4, U3.6
~hsync: J1.10
~porch: J1.11
~vsync: J1.12

Notes on the sheet:
0-1V

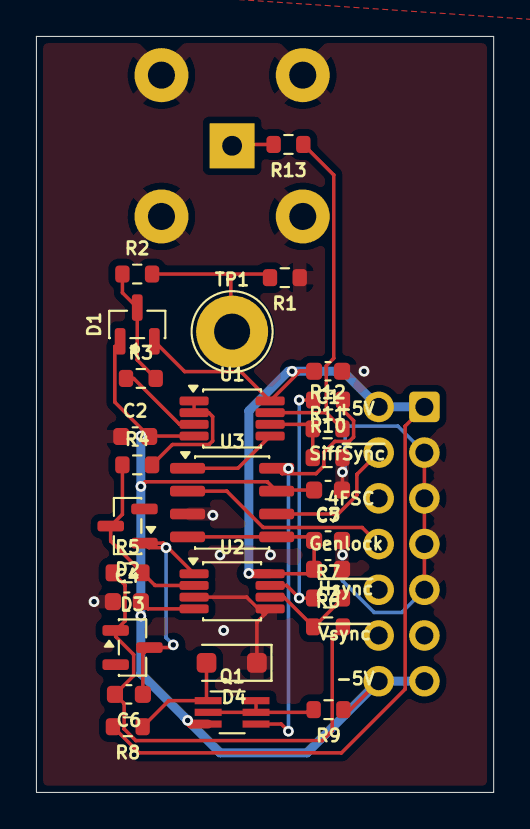
[picture p125: board sk003a-outbasic.kicad_pcb from above]

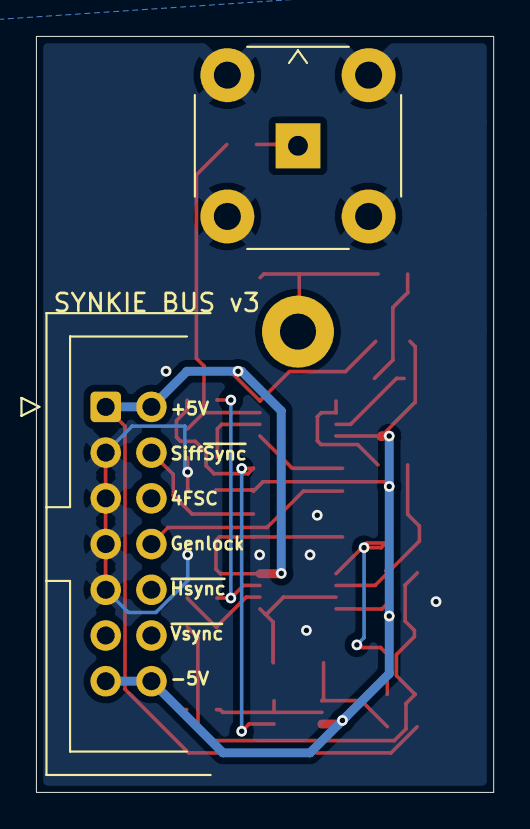
[picture p126: board sk003a-outbasic.kicad_pcb from below]

Board: 2 copper layers, 25.4 x 42.0 mm, 31 parts (2 on the bottom side), 21 nets.
