mirdej/synkie/kicad/sk300-Jack/sk300-Jack.kicad_pcb

## KiCad design kicad/sk300-Jack/sk300-Jack.kicad_pcb (2026-08-08)

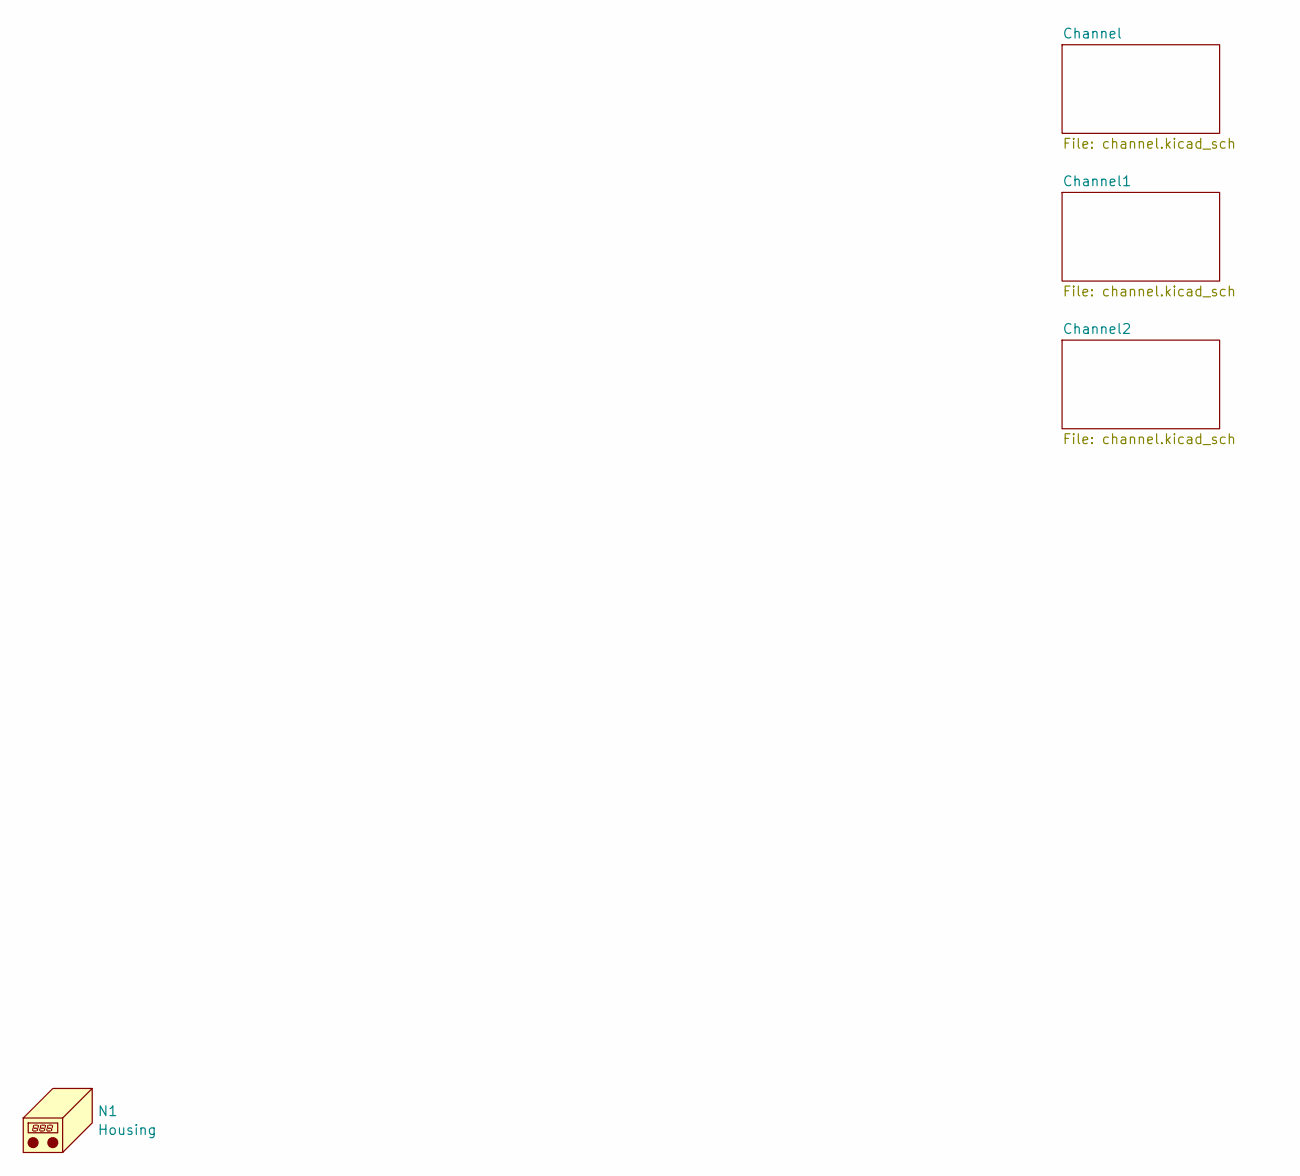
[picture p127: schematic sk300-Jack.kicad_sch]

Parts:
N1: Housing; Frontplate_15mm

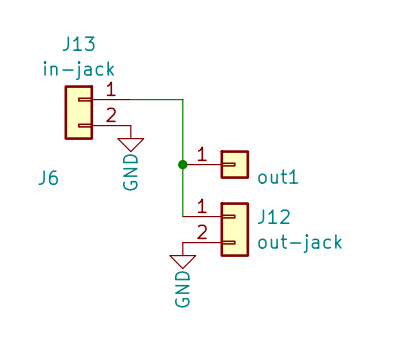
[picture p128: schematic channel.kicad_sch]

Parts:
J6: out1; Banana2mm-Löthülse
J12: out-jack; MiniJack-PJ301M_1
J13: in-jack; MiniJack-PJ301M_1

Connections:
GND: J12.2, J13.2; also elsewhere on the board
unnamed: J6.1 (Pin_1_1), J12.1, J13.1

Parts of its further copies:
J7, J8: out1; Banana2mm-Löthülse
J14, J16: in-jack; MiniJack-PJ301M_1
J15, J17: out-jack; MiniJack-PJ301M_1

Connections of its further copies:
GND: J14.2, J15.2, J16.2, J17.2; also elsewhere on the board
unnamed: J7.1 (Pin_1_1), J14.1, J15.1
unnamed: J8.1 (Pin_1_1), J16.1, J17.1

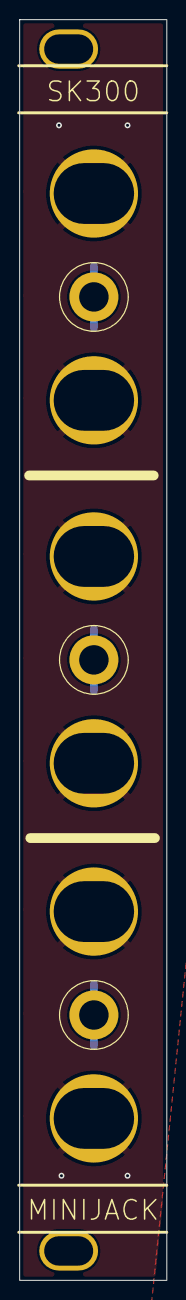
[picture p129: board sk300-Jack.kicad_pcb from above]

Board: 2 copper layers, 15.0 x 128.5 mm, 10 parts (0 on the bottom side), 4 nets.
