mirdej/synkie/kicad/sk166-poor-mans-matrix-mixer/sk166-poor-mans-matrix-mixer.kicad_pcb

## KiCad design kicad/sk166-poor-mans-matrix-mixer/sk166-poor-mans-matrix-mixer.kicad_pcb (2026-08-08)

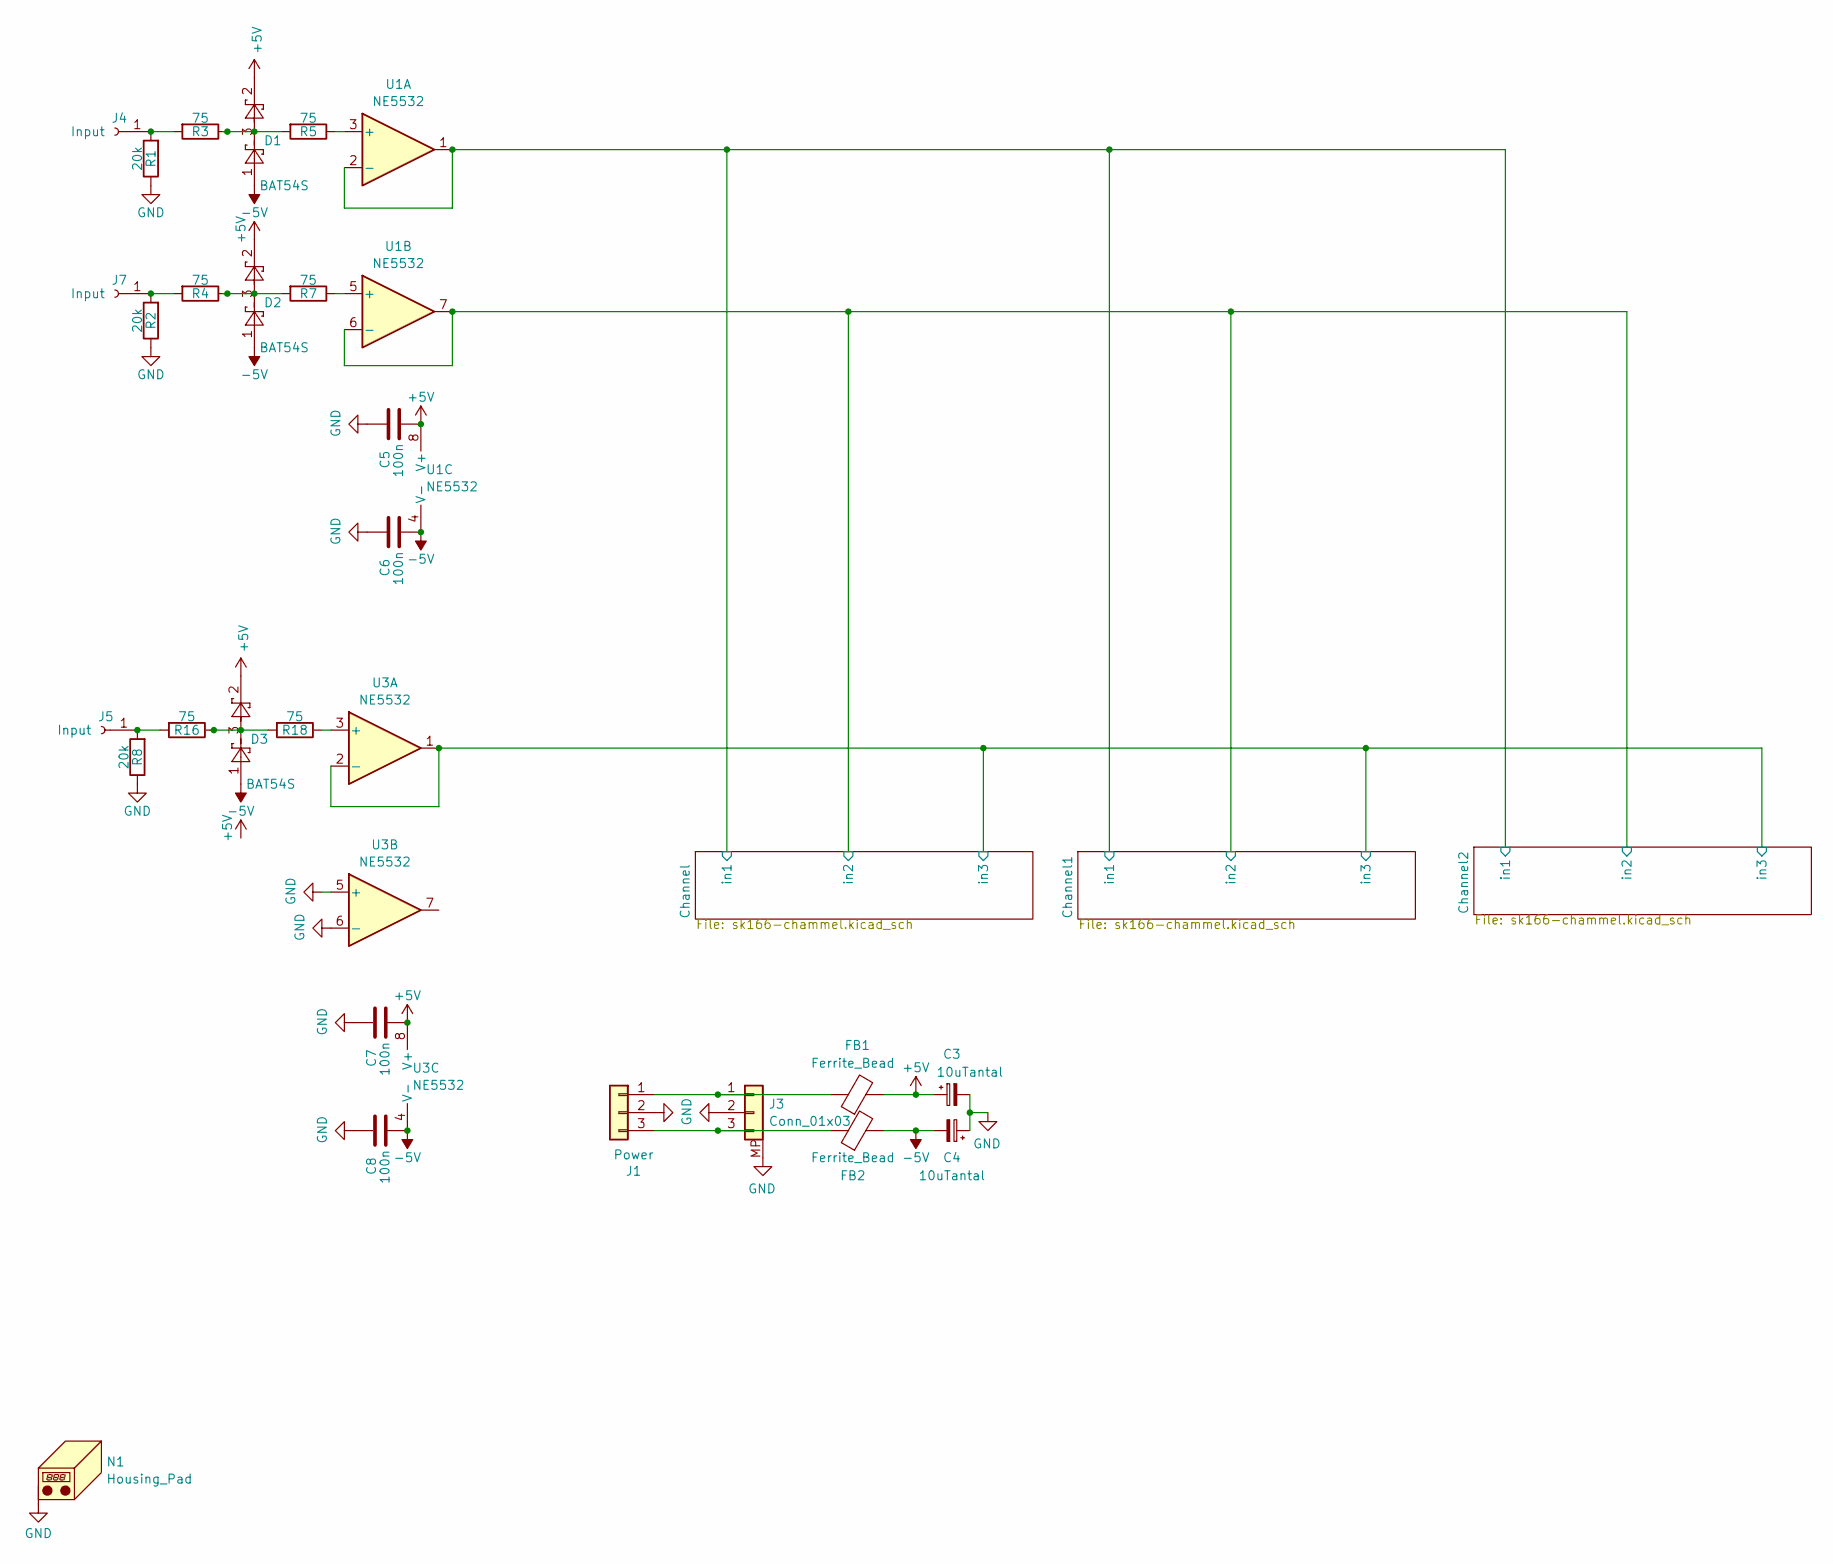
[picture p130: schematic sk166-poor-mans-matrix-mixer.kicad_sch]

Parts:
C3, C4: 10uTantal; CP_EIA-3216-18_Kemet-A; LCSC C7171
C5, C6, C7, C8: 100n; C_0603_1608Metric; LCSC C14663
D1, D2, D3: BAT54S; SOT-23; LCSC C7420333
FB1, FB2: Ferrite_Bead; L_0805_2012Metric; LCSC C1017
J1: Power; Molex_KK-254_AE-6410-03A_1x03_P2.54mm_Vertical_SMD
J3: Conn_01x03; Molex_PicoBlade_53398-0371_1x03-1MP_P1.25mm_Vertical; LCSC C293633
J4, J5, J7: Input; Banana2mm-Löthülse
N1: Housing_Pad; Frontplate_40mm
R1, R2, R8: 20k; R_0603_1608Metric; LCSC C4184
R3, R4, R5, R7, R16, R18: 75; R_0603_1608Metric; LCSC C4275
U1, U3: NE5532; SOIC-8_3.9x4.9mm_P1.27mm; LCSC C7426

Connections:
+5V: C3.1, C5.2, C7.2, D1.2, D2.2, D3.2, FB1.2, U1.8 (V+), U3.8 (V+); also elsewhere on the board
-5V: C4.2, C6.2, C8.2, D1.1, D2.1, D3.1, FB2.2, U1.4 (V-), U3.4 (V-); also elsewhere on the board
/Channel/in1: U1.1, U1.2 (-); also elsewhere on the board
/Channel/in2: U1.6 (-), U1.7; also elsewhere on the board
/Channel/in3: U3.1, U3.2 (-); also elsewhere on the board
GND: C3.2, C4.1, C5.1, C6.1, C7.1, C8.1, J1.2, J3.2, J3.MP, N1.1 (PAD_1), R1.1, R2.1, R8.1, U3.5 (+), U3.6 (-); also elsewhere on the board
unnamed: D1.3, R3.1, R5.2
unnamed: D2.3, R4.1, R7.2
unnamed: D3.3, R16.1, R18.2
unnamed: FB1.1, J1.1, J3.1
unnamed: FB2.1, J1.3, J3.3
unnamed: J4.1 (Pin_1_1), R1.2, R3.2
unnamed: J5.1 (Pin_1_1), R8.2, R16.2
unnamed: J7.1 (Pin_1_1), R2.2, R4.2
unnamed: R5.1, U1.3 (+)
unnamed: R7.1, U1.5 (+)
unnamed: R18.1, U3.3 (+)

Parts of its further copies:
C12: 100n; C_0603_1608Metric; LCSC C14663
R26: 75; R_0603_1608Metric; LCSC C4275

Connections of its further copies:
-5V: C12.2; also elsewhere on the board
GND: C12.1; also elsewhere on the board
unnamed 14: R26.1; also elsewhere on the board
unnamed 26: R26.2; also elsewhere on the board

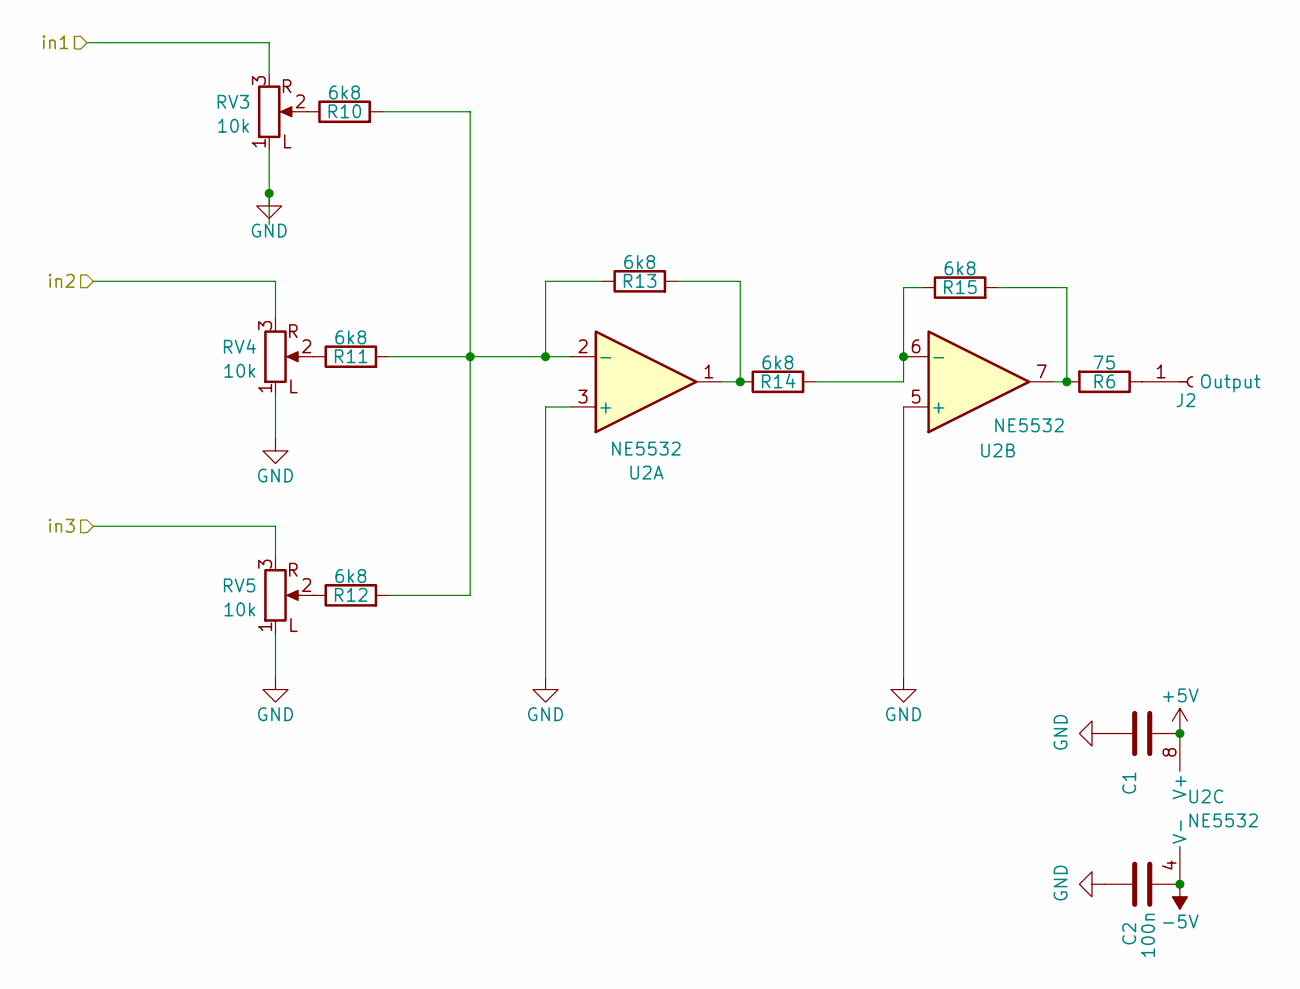
[picture p131: schematic sk166-chammel.kicad_sch]

Parts:
C1, C2: 100n; C_0402_1005Metric; LCSC C1525
J2: Output; Banana2mm-Löthülse
R6: 75; R_0603_1608Metric; LCSC C4275
R10, R11, R12, R13, R14, R15: 6k8; R_0603_1608Metric; LCSC C23212
RV3, RV4, RV5: 10k; Alps_RK097_Frontplate; LCSC C115340
U2: NE5532; SOIC-8_3.9x4.9mm_P1.27mm; LCSC C7426

Connections:
+5V: C1.2, U2.8 (V+); also elsewhere on the board
-5V: C2.2, U2.4 (V-); also elsewhere on the board
/Channel/in1: RV3.3; also elsewhere on the board
/Channel/in2: RV4.3; also elsewhere on the board
/Channel/in3: RV5.3; also elsewhere on the board
GND: C1.1, C2.1, RV3.1 (L), RV4.1 (L), RV5.1 (L), U2.3 (+), U2.5 (+); also elsewhere on the board
unnamed: J2.1 (Pin_1_1), R6.1
unnamed: R10.1, RV3.2
unnamed: R11.1, RV4.2
unnamed: R12.1, RV5.2
unnamed: R13.2, R14.1, U2.1
unnamed: R6.2, R15.2, U2.7
unnamed: R10.2, R11.2, R12.2, R13.1, U2.2 (-)
unnamed: R14.2, R15.1, U2.6 (-)

Parts of its further copies:
C9, C10, C11, C12: 100n; C_0402_1005Metric; LCSC C1525
J6, J9: Output; Banana2mm-Löthülse
R20, R21, R22, R23, R24, R25, R27, R28, R29, R30, R31, R32: 6k8; R_0603_1608Metric; LCSC C23212
R26, R33: 75; R_0603_1608Metric; LCSC C4275
RV6, RV7, RV8, RV9, RV10, RV11: 10k; Alps_RK097_Frontplate; LCSC C115340
U4, U5: NE5532; SOIC-8_3.9x4.9mm_P1.27mm; LCSC C7426

Connections of its further copies:
+5V: C9.2, C11.2, U4.8 (V+), U5.8 (V+); also elsewhere on the board
-5V: C10.2, C12.2, U4.4 (V-), U5.4 (V-); also elsewhere on the board
/Channel/in1: RV6.3, RV9.3; also elsewhere on the board
/Channel/in2: RV7.3, RV10.3; also elsewhere on the board
/Channel/in3: RV8.3, RV11.3; also elsewhere on the board
GND: C9.1, C10.1, C11.1, C12.1, RV6.1 (L), RV7.1 (L), RV8.1 (L), RV9.1 (L), RV10.1 (L), RV11.1 (L), U4.3 (+), U4.5 (+), U5.3 (+), U5.5 (+); also elsewhere on the board
unnamed: J6.1 (Pin_1_1), R26.1
unnamed: J9.1 (Pin_1_1), R33.1
unnamed: R20.1, RV6.2
unnamed: R21.1, RV7.2
unnamed: R22.1, RV8.2
unnamed: R23.2, R24.1, U4.1
unnamed: R25.2, R26.2, U4.7
unnamed: R27.1, RV9.2
unnamed: R28.1, RV10.2
unnamed: R29.1, RV11.2
unnamed: R30.2, R31.1, U5.1
unnamed: R32.2, R33.2, U5.7
unnamed: R20.2, R21.2, R22.2, R23.1, U4.2 (-)
unnamed: R24.2, R25.1, U4.6 (-)
unnamed: R27.2, R28.2, R29.2, R30.1, U5.2 (-)
unnamed: R31.2, R32.1, U5.6 (-)

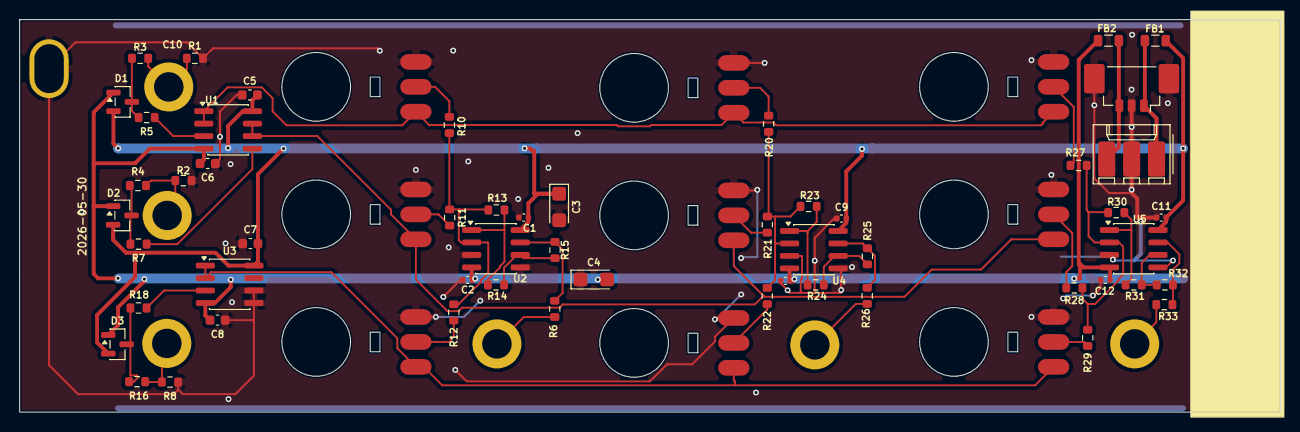
[picture p132: board sk166-poor-mans-matrix-mixer.kicad_pcb from above]

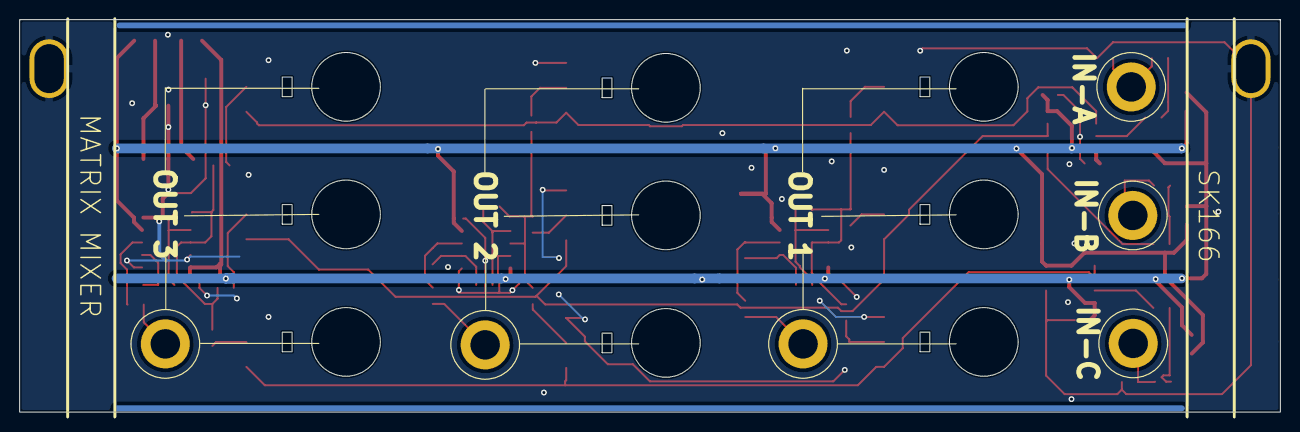
[picture p133: board sk166-poor-mans-matrix-mixer.kicad_pcb from below]

Board: 2 copper layers, 128.5 x 40.0 mm, 70 parts (16 on the bottom side), 41 nets.
