mirdej/synkie/kicad/building blocks/building blocks.kicad_pcb

## KiCad design kicad/building blocks/building blocks.kicad_pcb (2026-06-17)

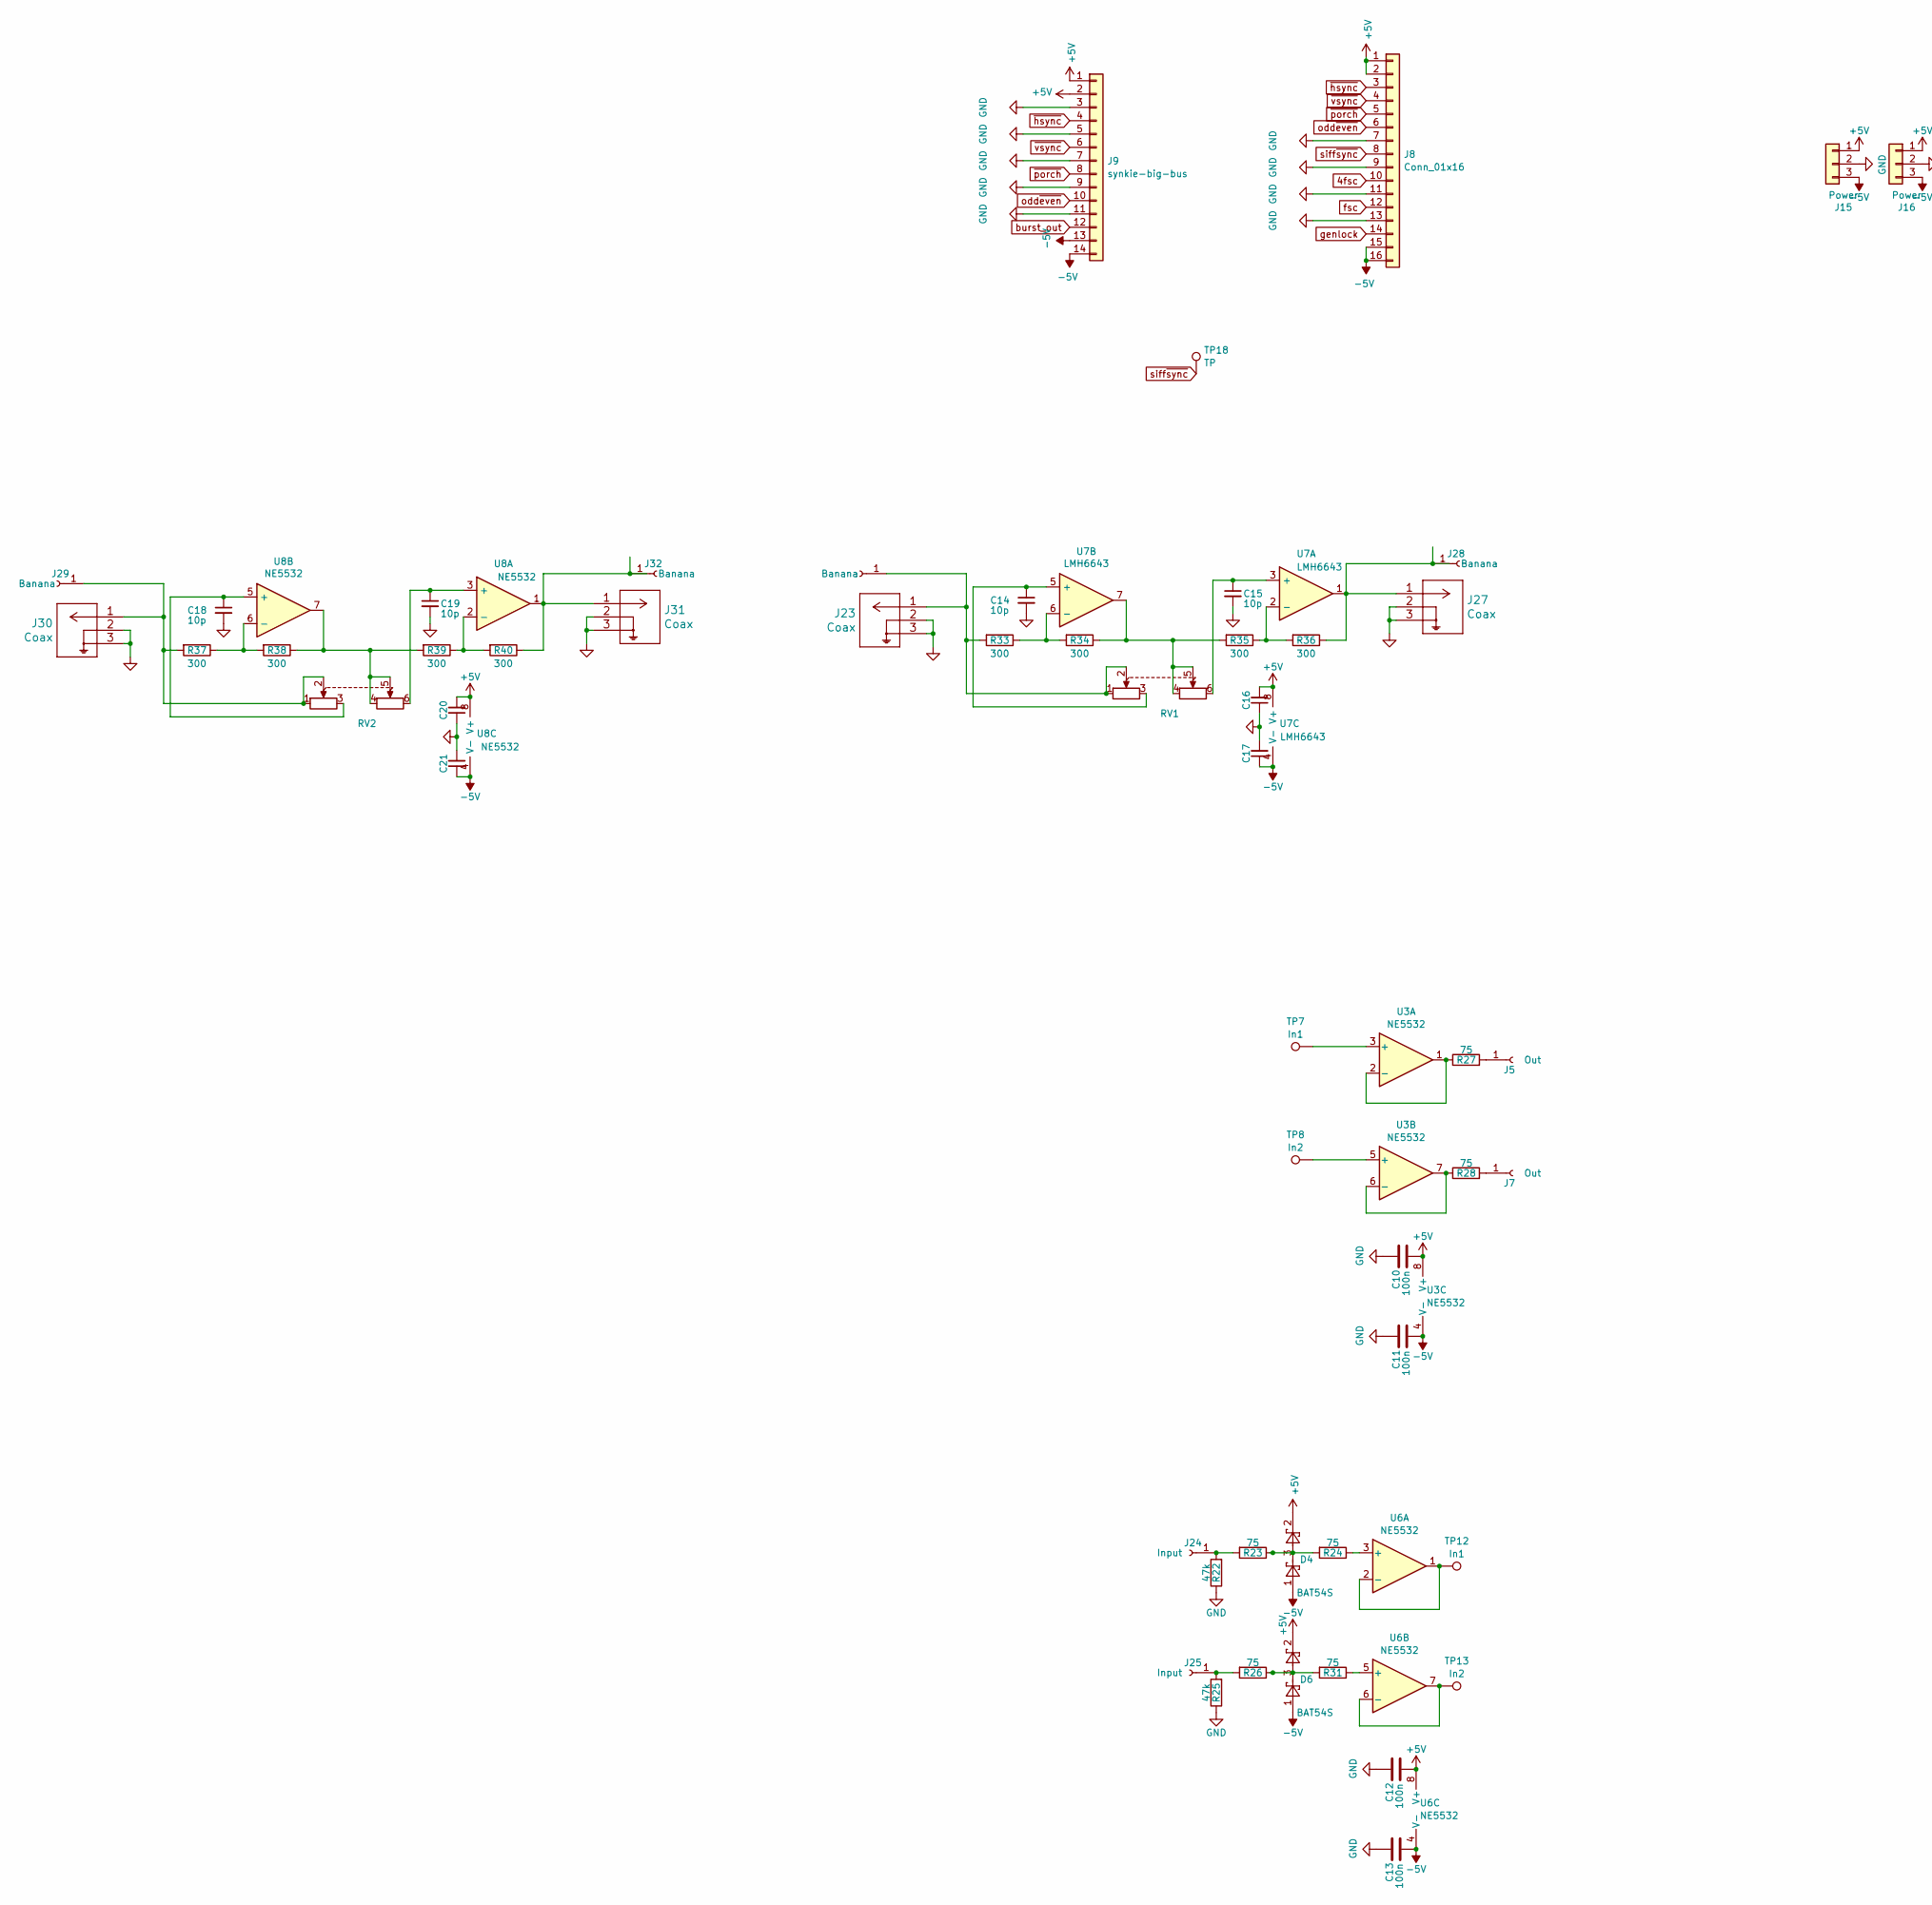
[picture p134: schematic building blocks.kicad_sch, part in row 1, column 1]

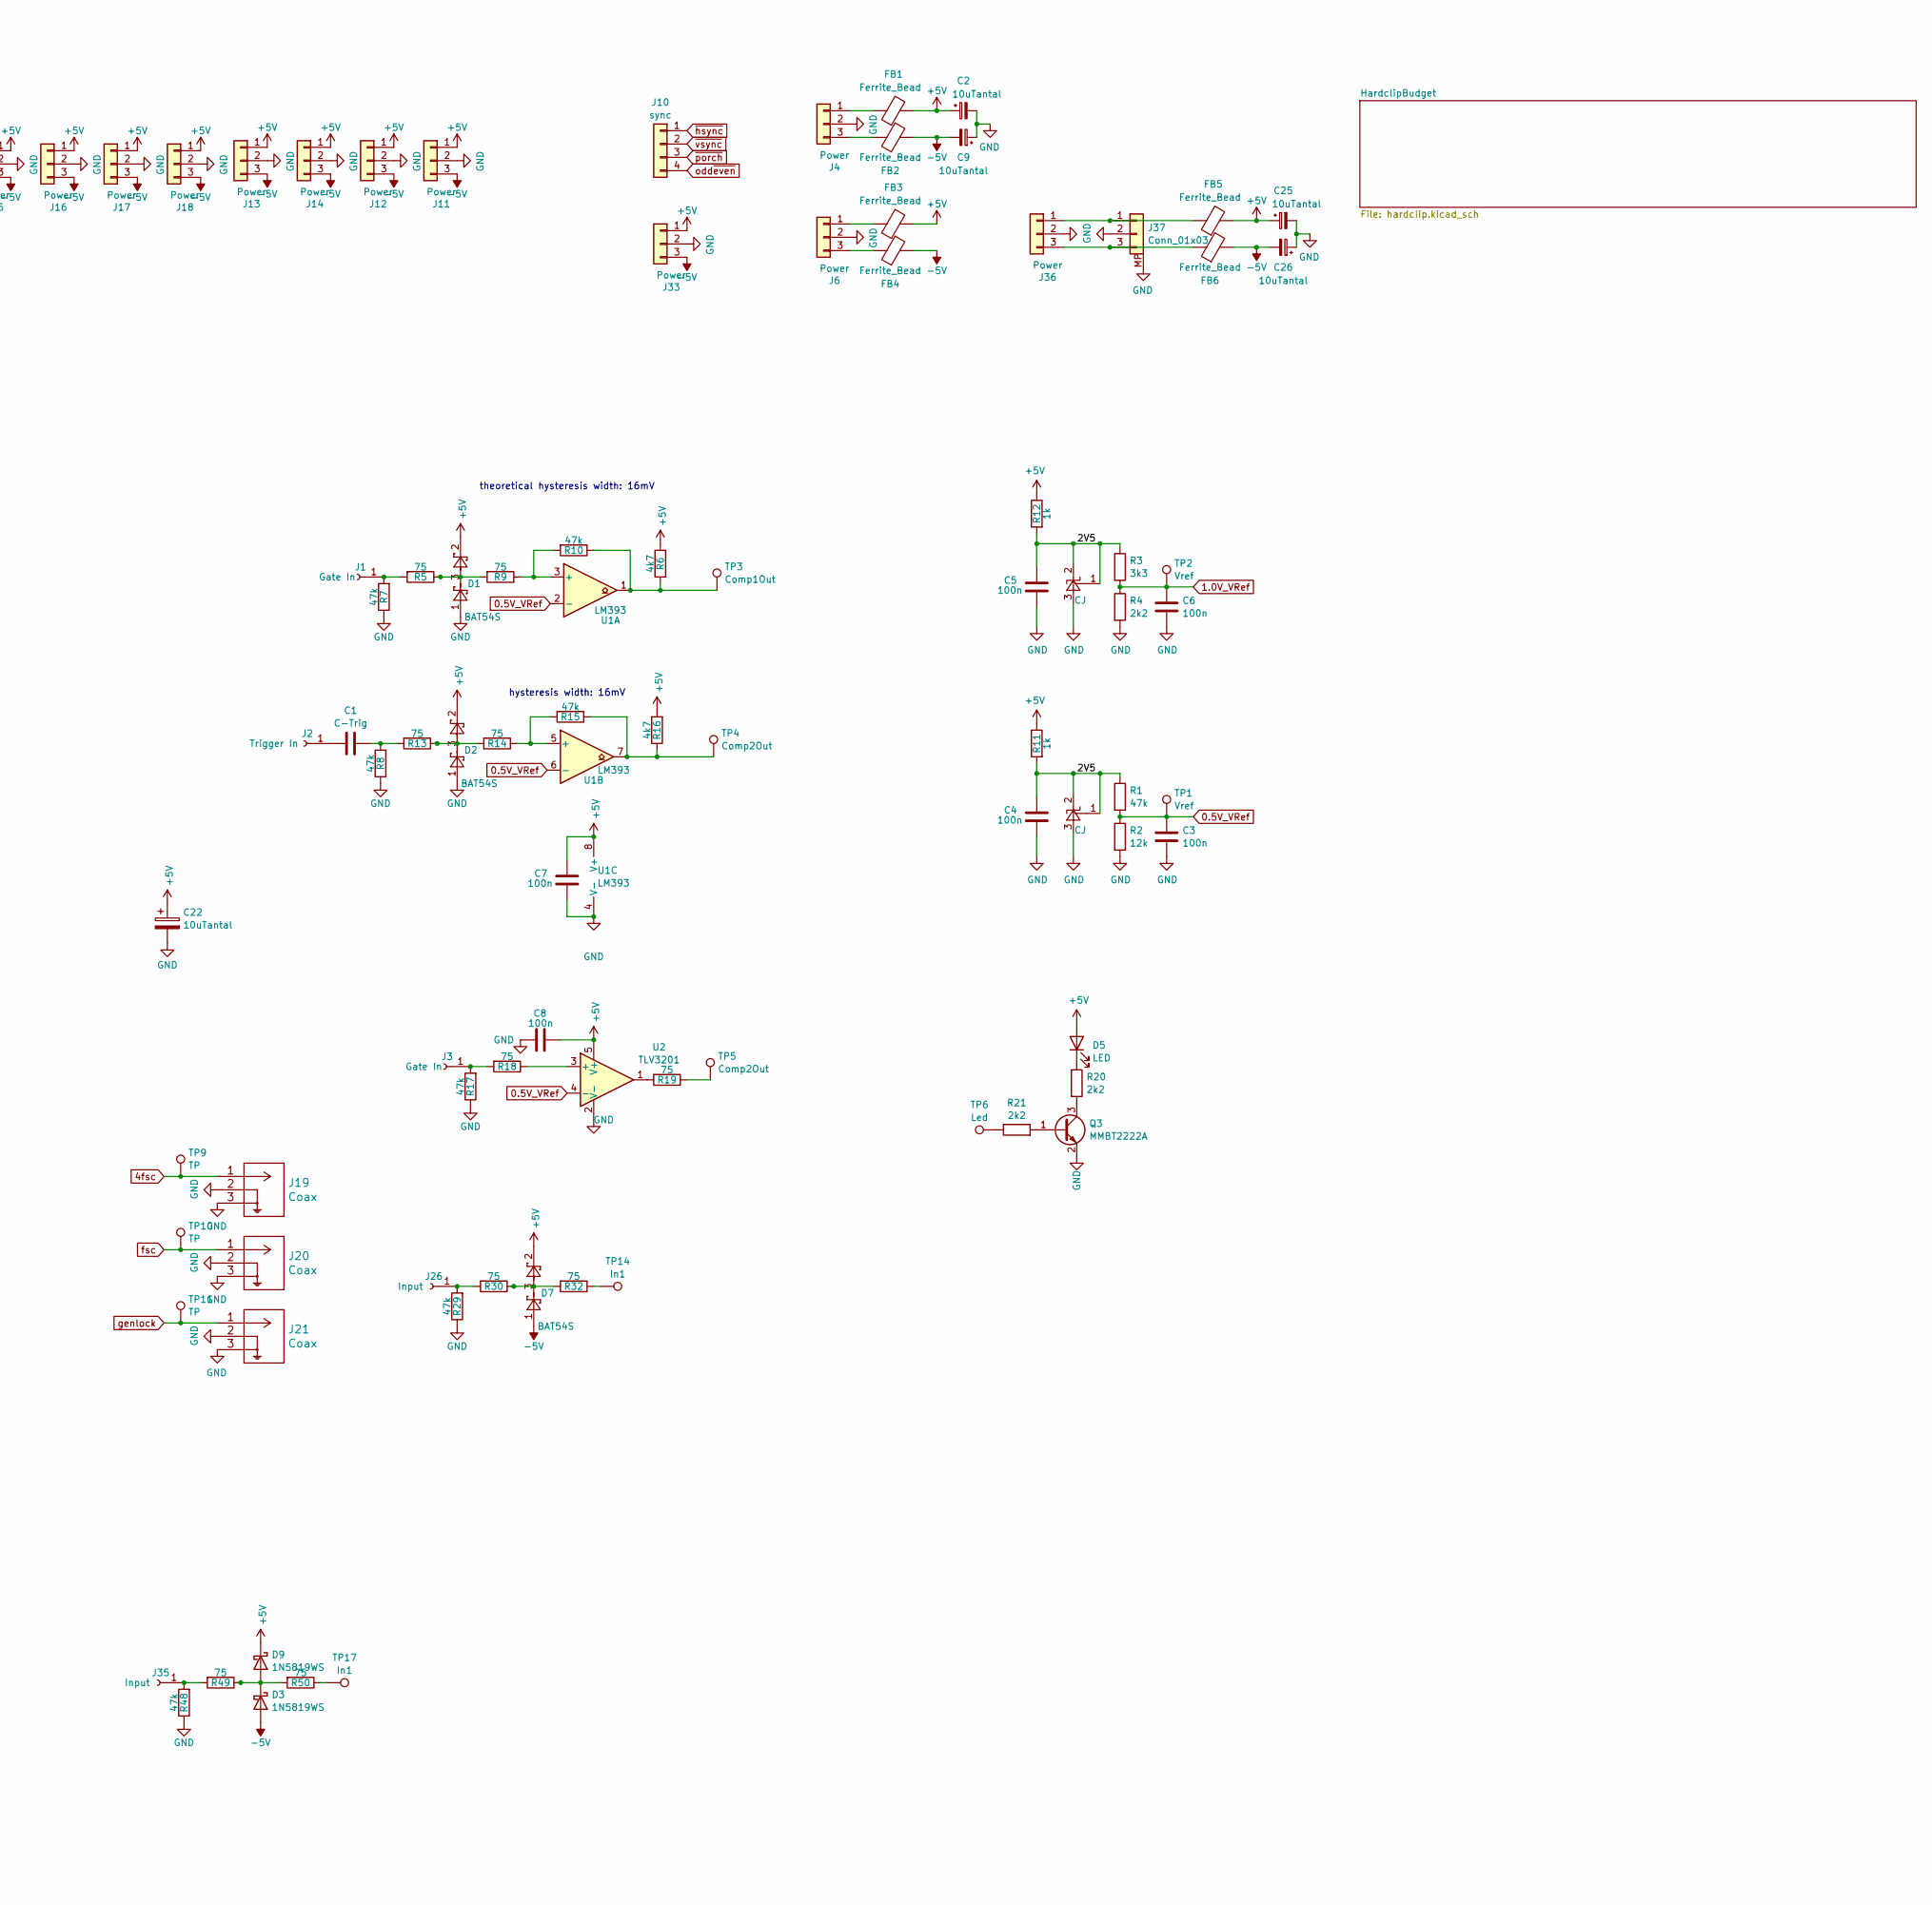
[picture p135: schematic building blocks.kicad_sch, part in row 1, column 2]

Parts:
C1: C-Trig; C_0805_2012Metric
C2, C9, C22, C25, C26: 10uTantal; CP_EIA-3216-18_Kemet-A; LCSC C7171
C3, C4, C5, C6, C7, C8, C10, C11, C12, C13: 100n; C_0603_1608Metric; LCSC C14663
C14, C15, C18, C19: 10p; C_0603_1608Metric; LCSC C1634
C16, C17, C20, C21: 100n; C_0402_1005Metric; LCSC C1525
D1, D2, D4, D6, D7: BAT54S; SOT-23; LCSC C8592
D3, D9: 1N5819WS; D_SOD-323; LCSC C191023
D5: LED; LED_1206_3216Metric_ReverseMount_Hole1.8x2.4mm; LCSC C125108
FB1, FB2, FB3, FB4, FB5, FB6: Ferrite_Bead; L_0805_2012Metric; LCSC C1017
J1, J3: Gate In; TestPoint_THTPad_D4.0mm_Drill2.0mm
J2: Trigger In; TestPoint_THTPad_D4.0mm_Drill2.0mm
J4, J33: Power; Molex_KK-254_AE-6410-03A_1x03_P2.54mm_Vertical
J5, J7: Out; TestPoint_THTPad_D4.0mm_Drill2.0mm
J6, J11, J12, J13, J14, J15, J16, J17, J18: Power; Molex_PicoBlade_53398-0371_1x03-1MP_P1.25mm_Vertical; LCSC C293633
J8: Conn_01x16; IDC-Header_2x08_P2.54mm_Vertical
J9: synkie-big-bus; IDC-Header_2x07_P2.54mm_Vertical
J10: sync; Molex_KK-254_AE-6410-04A_1x04_P2.54mm_Vertical
J19, J20, J21, J23, J27, J30, J31: Coax; TE_UMCC_2337019-1; LCSC C5137195
J22, J28, J29, J32: Banana; TestPoint_THTPad_D4.0mm_Drill2.0mm
J24, J25, J26, J35: Input; TestPoint_THTPad_D4.0mm_Drill2.0mm
J36: Power; Molex_KK-254_AE-6410-03A_1x03_P2.54mm_Vertical_SMD
J37: Conn_01x03; Molex_PicoBlade_53398-0371_1x03-1MP_P1.25mm_Vertical; LCSC C293633
Q3: MMBT2222A; SOT-23; LCSC C8512
R1, R7, R8, R10, R15, R17, R22, R25, R29, R48: 47k; R_0603_1608Metric; LCSC C25819
R2: 12k; R_0603_1608Metric; LCSC C22790
R3: 3k3; R_0603_1608Metric; LCSC C22978
R4, R20, R21: 2k2; R_0603_1608Metric; LCSC C4190
R5, R9, R13, R14, R18, R19, R23, R24, R26, R27, R28, R30, R31, R32, R49, R50: 75; R_0603_1608Metric; LCSC C4275
R6, R16: 4k7; R_0603_1608Metric; LCSC C23162
R11, R12: 1k; R_0603_1608Metric; LCSC C21190
R33, R34, R35, R36, R37, R38, R39, R40: 300; R_0603_1608Metric; LCSC C23025
RV1, RV2: PRS12R-2
TP1, TP2: Vref; TestPoint_THTPad_D4.0mm_Drill2.0mm
TP3: Comp1Out; TestPoint_THTPad_D4.0mm_Drill2.0mm
TP4, TP5: Comp2Out; TestPoint_THTPad_D4.0mm_Drill2.0mm
TP6: Led; TestPoint_THTPad_D4.0mm_Drill2.0mm
TP7, TP12, TP14, TP17: In1; TestPoint_THTPad_D4.0mm_Drill2.0mm
TP8, TP13: In2; TestPoint_THTPad_D4.0mm_Drill2.0mm
TP9, TP10, TP11, TP18: TP; TestPoint_THTPad_D4.0mm_Drill2.0mm
U1: LM393; SOIC-8_3.9x4.9mm_P1.27mm; LCSC C7955
U2: TLV3201; SOT-23-5; LCSC C105188
U3, U6, U8: NE5532; SOIC-8_3.9x4.9mm_P1.27mm; LCSC C7426
U4, U5: CJ; SOT-23; LCSC C3113
U7: LMH6643; VSSOP-8_3x3mm_P0.65mm; LCSC C478382

Connections:
0.5V_VRef: C3.1, R1.2, R2.1, TP1.1 (1_1), U1.2 (-), U1.6 (-), U2.4 (-)
1.0V_VRef: C6.1, R3.2, R4.1, TP2.1 (1_1); also elsewhere on the board
4fsc: J8.10, J19.1, TP9.1 (1_1)
+5V: C2.1, C7.1, C8.2, C10.2, C12.2, C16.2, C20.2, C22.1, C25.1, D1.2, D2.2, D4.2, D5.2 (A), D6.2, D7.2, D9.1 (K), FB1.2, FB3.2, FB5.2, J8.1, J8.2, J9.1, J9.2, J11.1, J12.1, J13.1, J14.1, J15.1, J16.1, J17.1, J18.1, J33.1, R6.2, R11.1, R12.1, R16.2, U1.8 (V+), U2.5 (V+), U3.8 (V+), U6.8 (V+), U7.8 (V+), U8.8 (V+); also elsewhere on the board
-5V: C9.2, C11.2, C13.2, C17.1, C21.1, C26.2, D3.2 (A), D4.1, D6.1, D7.1, FB2.2, FB4.2, FB6.2, J8.15, J8.16, J9.13, J9.14, J11.3, J12.3, J13.3, J14.3, J15.3, J16.3, J17.3, J18.3, J33.3, U3.4 (V-), U6.4 (V-), U7.4 (V-), U8.4 (V-); also elsewhere on the board
/2V5: C4.1, C5.1, R1.1, R3.1, R11.2, R12.2, U4.1 (R), U4.2 (K), U5.1 (R), U5.2 (K)
GND: C2.2, C3.2, C4.2, C5.2, C6.2, C7.2, C8.1, C9.1, C10.1, C11.1, C12.1, C13.1, C14.2, C15.2, C16.1, C17.2, C18.2, C19.2, C20.1, C21.2, C22.2, C25.2, C26.1, D1.1, D2.1, J4.2, J6.2, J8.7, J8.9, J8.11, J8.13, J9.3, J9.5, J9.7, J9.9, J9.11, J11.2, J12.2, J13.2, J14.2, J15.2, J16.2, J17.2, J18.2, J19.2, J19.3, J20.2, J20.3, J21.2, J21.3, J23.2, J23.3, J27.2, J27.3, J30.2, J30.3, J31.2, J31.3, J33.2, J36.2, J37.2, J37.MP, Q3.2 (E), R2.2, R4.2, R7.1, R8.1, R17.1, R22.1, R25.1, R29.1, R48.1, U1.4 (V-), U2.2 (V-), U4.3 (A), U5.3 (A); also elsewhere on the board
unnamed: C1.2, R8.2, R13.2
unnamed: D1.3, R5.1, R9.2
unnamed: D2.3, R13.1, R14.2
unnamed: D3.1 (K), D9.2 (A), R49.1, R50.2
unnamed: D4.3, R23.1, R24.2
unnamed: D5.1 (K), R20.1
unnamed: D6.3, R26.1, R31.2
unnamed: D7.3, R30.1, R32.2
unnamed: J1.1 (Pin_1_1), R5.2, R7.2
unnamed: C1.1, J2.1 (Pin_1_1)
unnamed: J3.1 (Pin_1_1), R17.2, R18.2
unnamed: FB1.1, J4.1
unnamed: FB2.1, J4.3
unnamed: J5.1 (Pin_1_1), R27.2
unnamed: FB3.1, J6.1
unnamed: FB4.1, J6.3
unnamed: J7.1 (Pin_1_1), R28.2
unnamed: J22.1 (Pin_1_1), J23.1, R33.2, RV1.1, RV1.2
unnamed: J24.1 (Pin_1_1), R22.2, R23.2
unnamed: J25.1 (Pin_1_1), R25.2, R26.2
unnamed: J26.1 (Pin_1_1), R29.2, R30.2
unnamed: J27.1, J28.1 (Pin_1_1), R36.1, U7.1
unnamed: J29.1 (Pin_1_1), J30.1, R37.2, RV2.1, RV2.2
unnamed: J31.1, J32.1 (Pin_1_1), R40.1, U8.1
unnamed: J35.1 (Pin_1_1), R48.2, R49.2
unnamed: FB5.1, J36.1, J37.1
unnamed: FB6.1, J36.3, J37.3
unnamed: Q3.1 (B), R21.2
unnamed: Q3.3 (C), R20.2
unnamed: R6.1, R10.1, TP3.1 (1_1), U1.1
unnamed: R15.1, R16.1, TP4.1 (1_1), U1.7
unnamed: R19.1, TP5.1 (1_1)
unnamed: R19.2, U2.1
unnamed: R21.1, TP6.1 (1_1)
unnamed: R32.1, TP14.1 (1_1)
unnamed: R34.1, R35.2, RV1.4, RV1.5, U7.7
unnamed: R38.1, R39.2, RV2.4, RV2.5, U8.7
unnamed: R50.1, TP17.1 (1_1)
unnamed: R9.1, R10.2, U1.3 (+)
unnamed: R14.1, R15.2, U1.5 (+)
unnamed: R18.1, U2.3 (+)
unnamed: TP7.1 (1_1), U3.3 (+)
unnamed: R27.1, U3.1, U3.2 (-)
unnamed: TP8.1 (1_1), U3.5 (+)
unnamed: R28.1, U3.6 (-), U3.7
unnamed: R24.1, U6.3 (+)
unnamed: TP12.1 (1_1), U6.1, U6.2 (-)
unnamed: R31.1, U6.5 (+)
unnamed: TP13.1 (1_1), U6.6 (-), U6.7
unnamed: C15.1, RV1.6, U7.3 (+)
unnamed: R35.1, R36.2, U7.2 (-)
unnamed: C14.1, RV1.3, U7.5 (+)
unnamed: R33.1, R34.2, U7.6 (-)
unnamed: C19.1, RV2.6, U8.3 (+)
unnamed: R39.1, R40.2, U8.2 (-)
unnamed: C18.1, RV2.3, U8.5 (+)
unnamed: R37.1, R38.2, U8.6 (-)
burst_out: J9.12
fsc: J8.12, J20.1, TP10.1 (1_1)
genlock: J8.14, J21.1, TP11.1 (1_1)
odd~even: J8.6, J9.10, J10.4
siff~sync: J8.8, TP18.1 (1_1)
~hsync: J8.3, J9.4, J10.1
~porch: J8.5, J9.8, J10.3
~vsync: J8.4, J9.6, J10.2

Notes on the sheet:
hysteresis width: 16mV
theoretical hysteresis width: 16mV

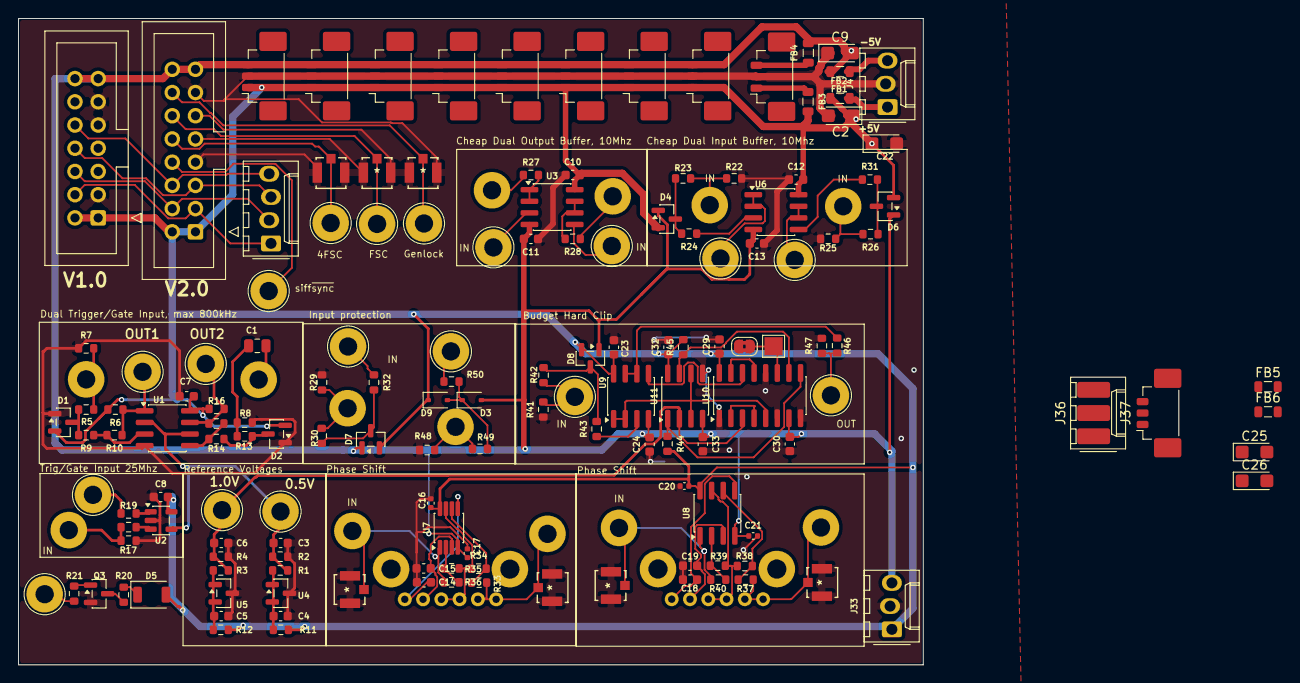
[picture p136: board building blocks.kicad_pcb from above]

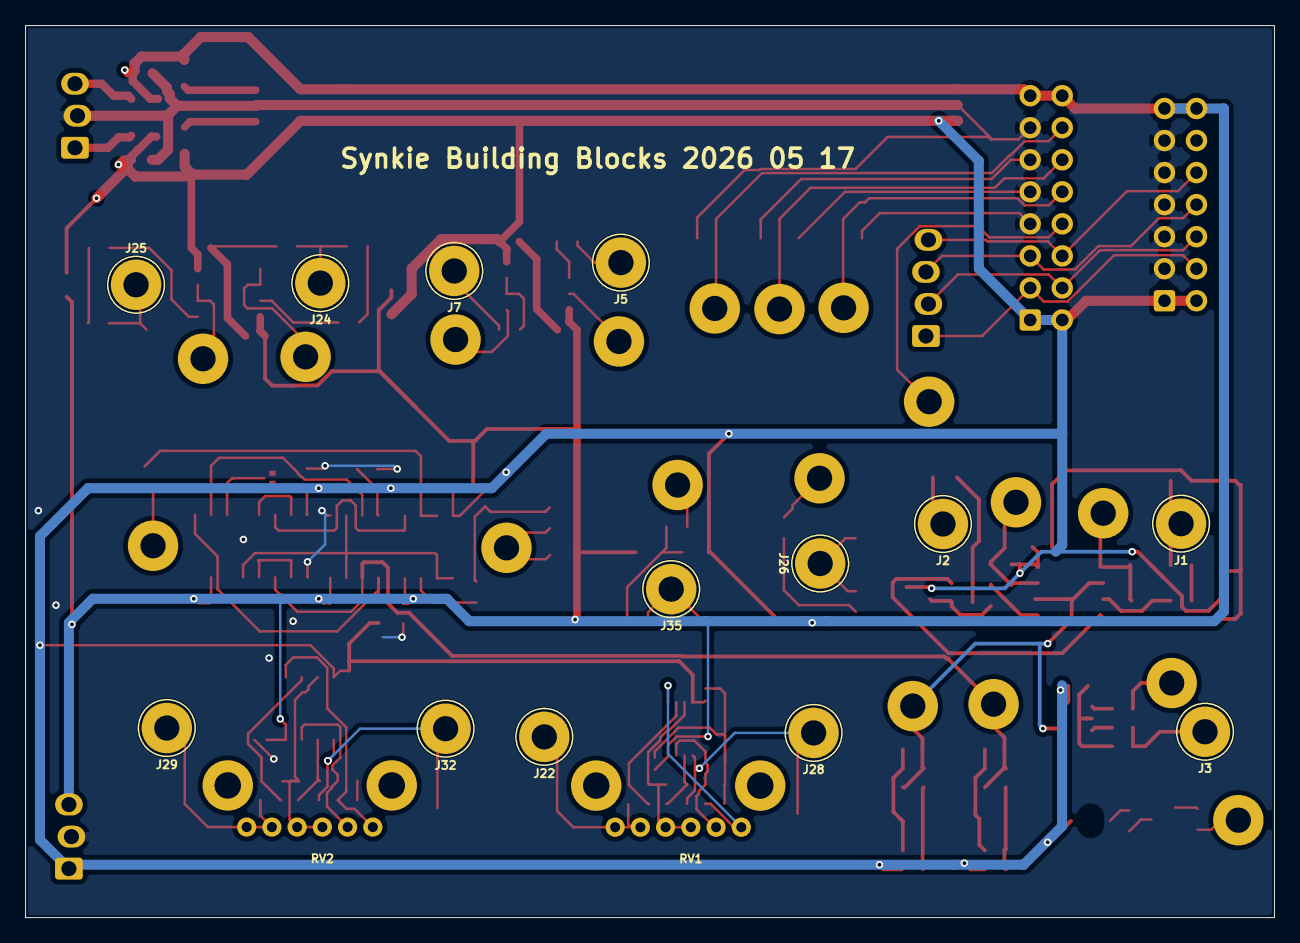
[picture p137: board building blocks.kicad_pcb from below]

Board: 2 copper layers, 99.0 x 70.7 mm, 165 parts (15 on the bottom side), 83 nets.

Other parts of the board:
C23, C24, C29, C30, C32, C33: 100n; C_0603_1608Metric
D8: BAT54S; SOT-23
J34: Input; TestPoint_THTPad_D4.0mm_Drill2.0mm
JP1: Jumper_2_Bridged; SolderJumper-2_P1.3mm_Bridged2Bar_RoundedPad1.0x1.5mm
R41: 47k; R_0603_1608Metric
R42, R43: 75; R_0603_1608Metric
R44, R45: 6k8; R_0603_1608Metric
R46: 4k7; R_0603_1608Metric
R47: 12k; R_0603_1608Metric
TP15: TP; TestPoint_THTPad_D4.0mm_Drill2.0mm
TP16: TestPoint; TestPoint_Pad_2.0x2.0mm
U9: NE5532; SOIC-8_3.9x4.9mm_P1.27mm
U10: TPW4053-SR; SOIC-16_3.9x9.9mm_P1.27mm
U11: LM393; SOIC-8_3.9x4.9mm_P1.27mm

Their connections:
1.0V_VRef: U10.3 (Z1), U11.2 (-); also elsewhere on the board
+5V: C23.2, C29.1, C32.1, D8.2, R44.2, R45.2, U9.8 (V+), U10.16 (VDD), U11.8 (V+); also elsewhere on the board
-5V: C24.2, C30.2, C33.1, D8.1, U9.4 (V-), U10.7 (VEE), U11.4 (V-); also elsewhere on the board
/HardclipBudget/out: R46.1, R47.1, TP15.1 (1_1)
GND: C23.1, C24.1, C29.2, C30.1, C32.2, C33.2, R41.1, R47.2, U10.1 (Y1), U10.6 (Inh), U10.8 (VSS), U10.12 (X0), U11.5 (+); also elsewhere on the board
unnamed: D8.3, R42.1, R43.2
unnamed: J34.1 (Pin_1_1), R41.2, R42.2
unnamed: JP1.2 (B), TP16.1 (1_1), U10.11 (A)
unnamed: R43.1, U9.3 (+)
unnamed: R46.2, U9.6 (-), U9.7
unnamed: R45.1, U10.10 (B), U11.7
unnamed: R44.1, U10.9 (C), U11.1
unnamed: U10.13 (X1), U10.15 (Y)
unnamed: U9.5 (+), U10.14 (X)
unnamed: U10.2 (Y0), U10.4 (Z)
unnamed: U9.1, U9.2 (-), U10.5 (Z0), U11.3 (+), U11.6 (-)
