mirdej/synkie/kicad/sk169-3way-out/sk169-3way-out.kicad_pcb

## KiCad design kicad/sk169-3way-out/sk169-3way-out.kicad_pcb (2026-05-16)

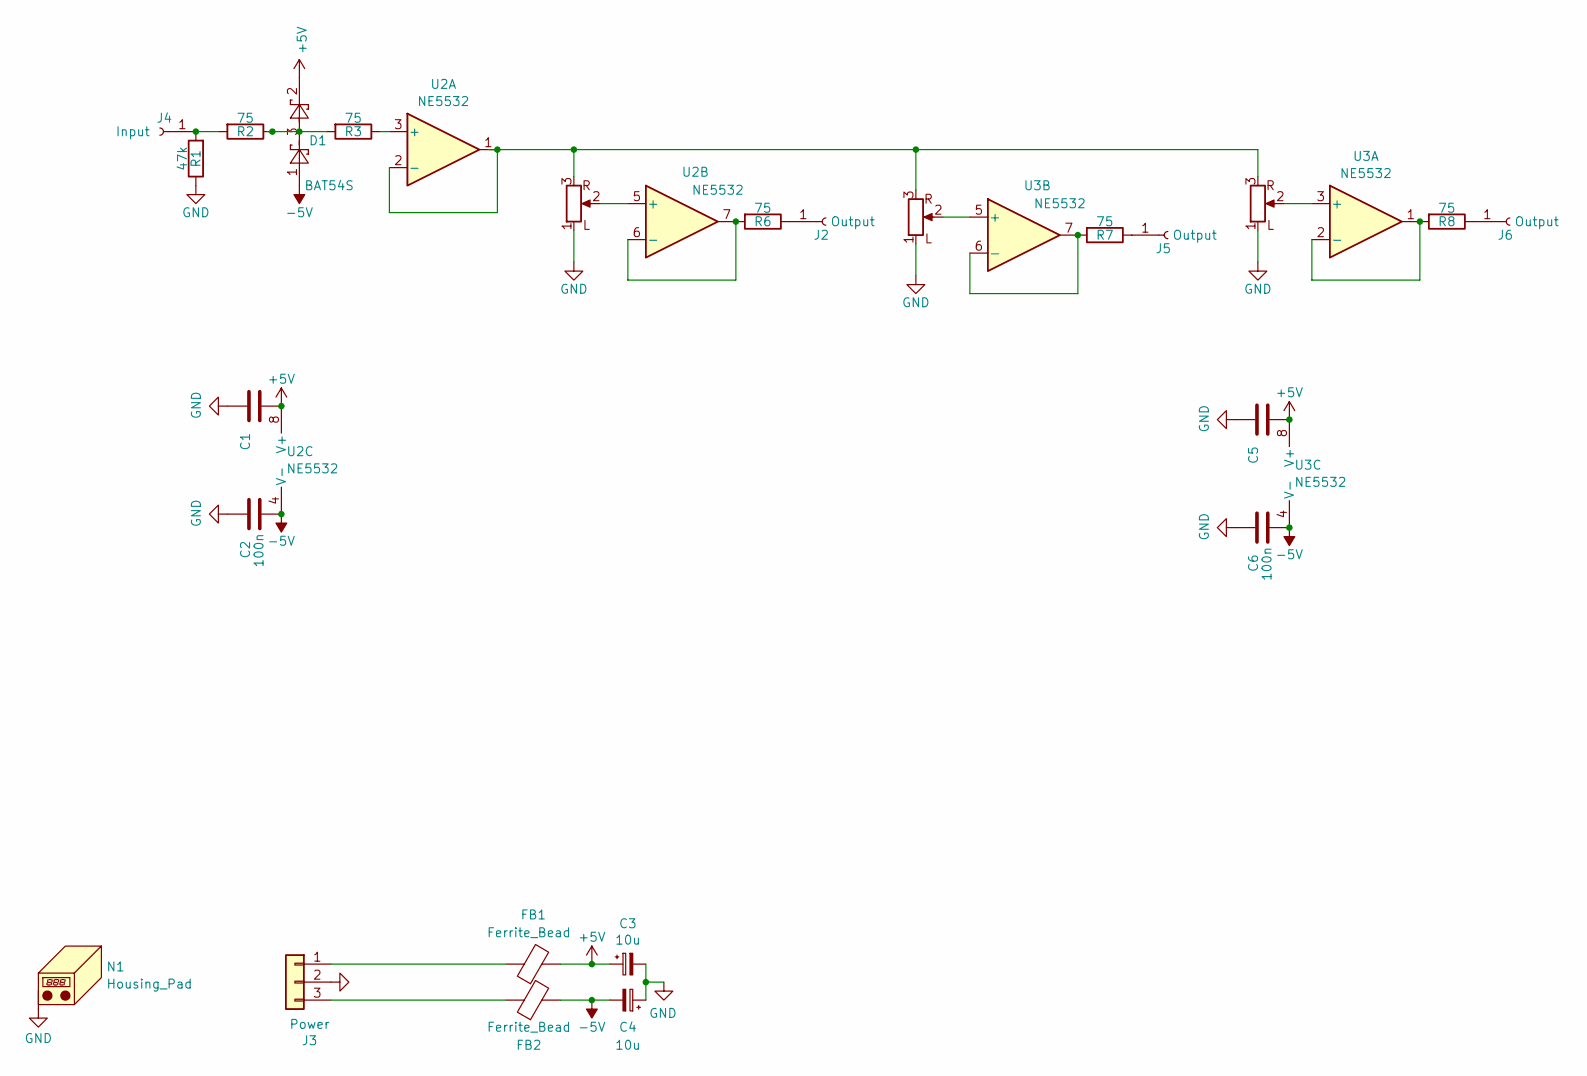
[picture p138: schematic sk169-3way-out.kicad_sch]

Parts:
C1, C2, C5, C6: 100n; C_0402_1005Metric; LCSC C1525
C3, C4: 10u; C_0805_2012Metric; LCSC C15850
D1: BAT54S; SOT-23; LCSC C8592
FB1, FB2: Ferrite_Bead; L_0805_2012Metric; LCSC C1017
J2, J5, J6: Output; Banana2mm-Löthülse
J3: Power; Molex_KK-254_AE-6410-03A_1x03_P2.54mm_Vertical_SMD
J4: Input; Banana2mm-Löthülse
N1: Housing_Pad; Frontplate_10mm
R1: 47k; R_0603_1608Metric; LCSC C25819
R2, R3, R6, R7, R8: 75; R_0603_1608Metric; LCSC C4275
RV3, RV4, RV5: 10k; Alps_RK097_Frontplate
U2, U3: NE5532; SOIC-8_3.9x4.9mm_P1.27mm; LCSC C7426

Connections:
+5V: C1.2, C3.1, C5.2, D1.2, FB1.2, U2.8 (V+), U3.8 (V+)
-5V: C2.2, C4.2, C6.2, D1.1, FB2.2, U2.4 (V-), U3.4 (V-)
GND: C1.1, C2.1, C3.2, C4.1, C5.1, C6.1, J3.2, N1.1 (PAD_1), R1.1, RV3.1 (L), RV4.1 (L), RV5.1 (L)
unnamed: D1.3, R2.1, R3.2
unnamed: J2.1 (Pin_1_1), R6.1
unnamed: FB1.1, J3.1
unnamed: FB2.1, J3.3
unnamed: J4.1 (Pin_1_1), R1.2, R2.2
unnamed: J5.1 (Pin_1_1), R7.1
unnamed: J6.1 (Pin_1_1), R8.1
unnamed: R3.1, U2.3 (+)
unnamed: RV3.3, RV4.3, RV5.3, U2.1, U2.2 (-)
unnamed: RV3.2, U2.5 (+)
unnamed: R6.2, U2.6 (-), U2.7
unnamed: RV5.2, U3.3 (+)
unnamed: R8.2, U3.1, U3.2 (-)
unnamed: RV4.2, U3.5 (+)
unnamed: R7.2, U3.6 (-), U3.7

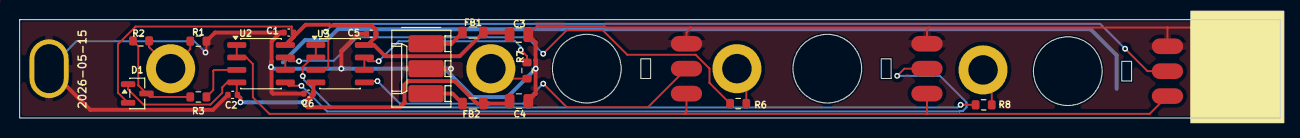
[picture p139: board sk169-3way-out.kicad_pcb from above]

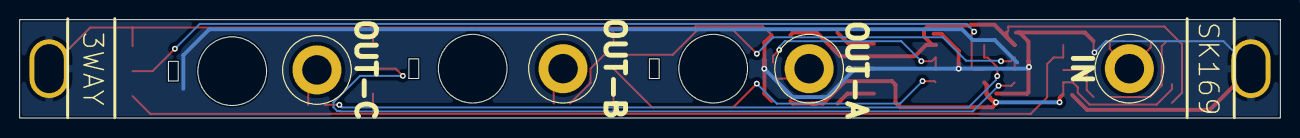
[picture p140: board sk169-3way-out.kicad_pcb from below]

Board: 2 copper layers, 128.5 x 10.0 mm, 26 parts (8 on the bottom side), 18 nets.
