mirdej/synkie/kicad/sk500-pots/sk500-pots.kicad_pcb

## KiCad design kicad/sk500-pots/sk500-pots.kicad_pcb (2026-05-15)

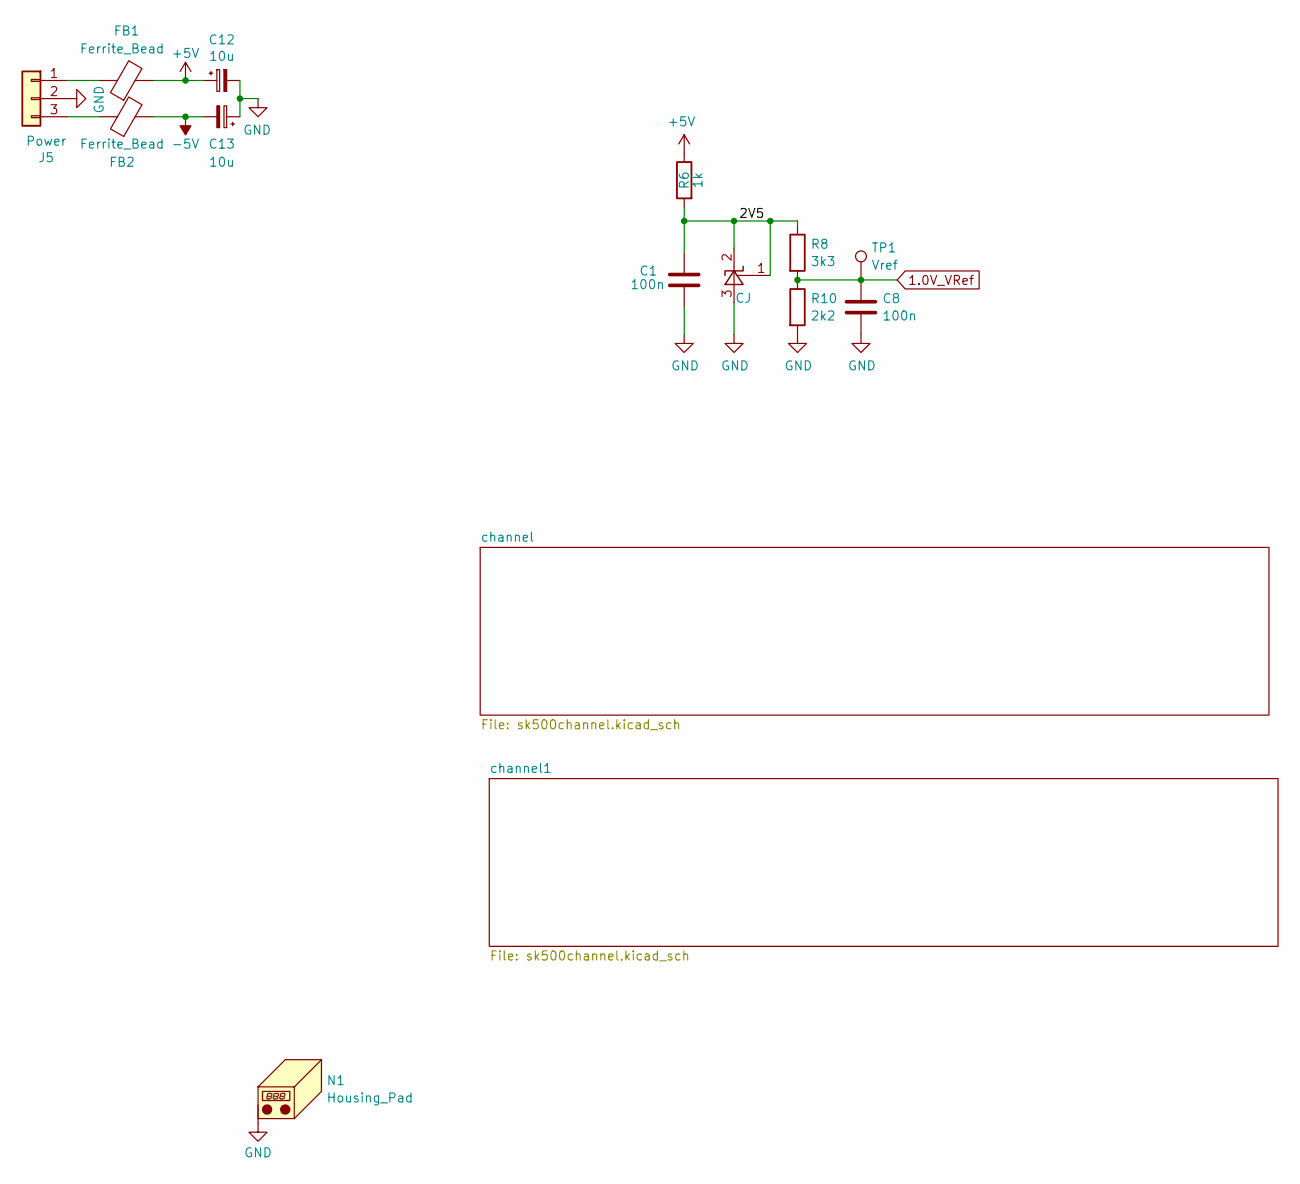
[picture p141: schematic sk500-pots.kicad_sch]

Parts:
C1, C8: 100n; C_0402_1005Metric; LCSC C1525
C12, C13: 10u; C_0805_2012Metric; LCSC C15850
FB1, FB2: Ferrite_Bead; L_0805_2012Metric; LCSC C1017
J5: Power; Molex_KK-254_AE-6410-03A_1x03_P2.54mm_Vertical_SMD
N1: Housing_Pad
R6: 1k; R_0603_1608Metric; LCSC C21190
R8: 3k3; R_0603_1608Metric; LCSC C22978
R10: 2k2; R_0603_1608Metric; LCSC C4190
TP1: Vref; TestPoint_Pad_D1.0mm
U3: CJ; SOT-23; LCSC C3113

Connections:
1.0V_VRef: C8.1, R8.2, R10.1, TP1.1 (1_1); also elsewhere on the board
+5V: C12.1, FB1.2, R6.1; also elsewhere on the board
-5V: C13.2, FB2.2; also elsewhere on the board
/2V5: C1.1, R6.2, R8.1, U3.1 (R), U3.2 (K)
GND: C1.2, C8.2, C12.2, C13.1, J5.2, N1.1 (PAD_1), R10.2, U3.3 (A); also elsewhere on the board
unnamed: FB1.1, J5.1
unnamed: FB2.1, J5.3

Parts of its further copies:
C6: 100n; C_0402_1005Metric; LCSC C1525

Connections of its further copies:
+5V: C6.1; also elsewhere on the board
GND: C6.2; also elsewhere on the board

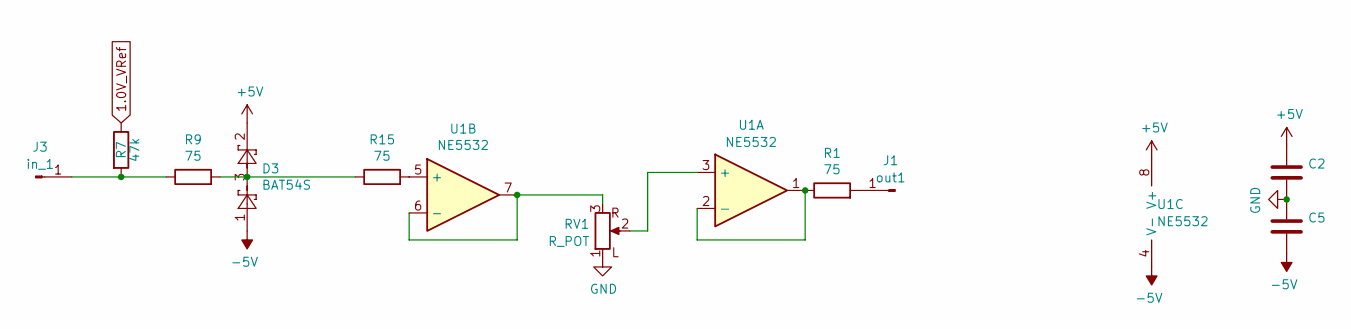
[picture p142: schematic sk500channel.kicad_sch]

Parts:
C2, C5: 100n; C_0402_1005Metric; LCSC C1525
D3: BAT54S; SOT-23; LCSC C8592
J1: out1; Banana2mm-Löthülse
J3: in_1; Banana2mm-Löthülse
R1, R9, R15: 75; R_0603_1608Metric; LCSC C4275
R7: 47k; R_0603_1608Metric; LCSC C25819
RV1: R_POT; Alps_RK097_Frontplate
U1: NE5532; SOIC-8_3.9x4.9mm_P1.27mm; LCSC C7426

Connections:
1.0V_VRef: R7.1; also elsewhere on the board
+5V: C2.1, D3.2, U1.8 (V+); also elsewhere on the board
-5V: C5.2, D3.1, U1.4 (V-); also elsewhere on the board
GND: C2.2, C5.1, RV1.1 (L); also elsewhere on the board
unnamed: D3.3, R9.2, R15.1
unnamed: J1.1 (Pin_1_1), R1.2
unnamed: J3.1 (Pin_1_1), R7.2, R9.1
unnamed: RV1.2, U1.3 (+)
unnamed: R1.1, U1.1, U1.2 (-)
unnamed: R15.2, U1.5 (+)
unnamed: RV1.3, U1.6 (-), U1.7

Parts of its further copies:
C6, C7: 100n; C_0402_1005Metric; LCSC C1525
D2: BAT54S; SOT-23; LCSC C8592
J2: in_1; Banana2mm-Löthülse
J4: out1; Banana2mm-Löthülse
R2: 47k; R_0603_1608Metric; LCSC C25819
R3, R4, R5: 75; R_0603_1608Metric; LCSC C4275
RV2: R_POT; Alps_RK097_Frontplate
U2: NE5532; SOIC-8_3.9x4.9mm_P1.27mm; LCSC C7426

Connections of its further copies:
1.0V_VRef: R2.1; also elsewhere on the board
+5V: C6.1, D2.2, U2.8 (V+); also elsewhere on the board
-5V: C7.2, D2.1, U2.4 (V-); also elsewhere on the board
GND: C6.2, C7.1, RV2.1 (L); also elsewhere on the board
unnamed: D2.3, R3.2, R4.1
unnamed: J2.1 (Pin_1_1), R2.2, R3.1
unnamed: J4.1 (Pin_1_1), R5.2
unnamed: RV2.2, U2.3 (+)
unnamed: R5.1, U2.1, U2.2 (-)
unnamed: R4.2, U2.5 (+)
unnamed: RV2.3, U2.6 (-), U2.7

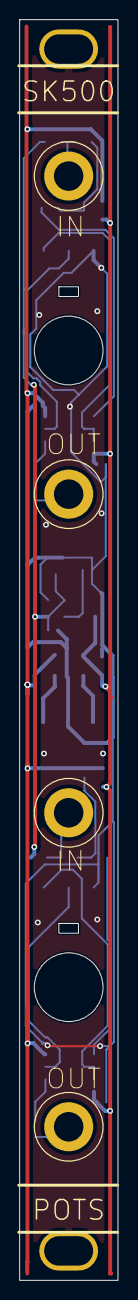
[picture p143: board sk500-pots.kicad_pcb from above]

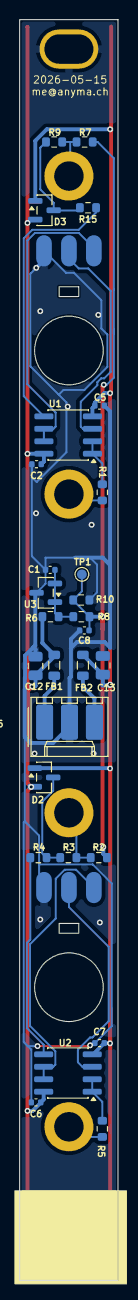
[picture p144: board sk500-pots.kicad_pcb from below]

Board: 2 copper layers, 10.0 x 128.5 mm, 35 parts (28 on the bottom side), 21 nets.
