mirdej/synkie/kicad/SynkieDesignBlocks.kicad_blocks/Power-KK-Picoblade-combined.kicad_block/Power-KK-Picoblade-combined.kicad_pcb

## KiCad design kicad/SynkieDesignBlocks.kicad_blocks/Power-KK-Picoblade-combined.kicad_block/Power-KK-Picoblade-combined.kicad_pcb (2026-05-15)

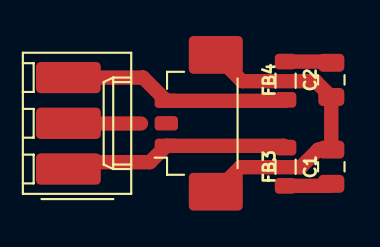
[picture p145: board Power-KK-Picoblade-combined.kicad_pcb from above]

Board: 2 copper layers, 6 parts (0 on the bottom side), 5 nets.

Parts:
C1, C2: 10u; C_0805_2012Metric
FB3, FB4: Ferrite_Bead; L_0805_2012Metric
J1: Conn_01x03; Molex_PicoBlade_53398-0371_1x03-1MP_P1.25mm_Vertical
J2: Power; Molex_KK-254_AE-6410-03A_1x03_P2.54mm_Vertical_SMD

Connections:
+5V: C1.1, FB3.2
-5V: C2.2, FB4.2
GND: C1.2, C2.1, J1.2, J1.MP, J2.2
unnamed: FB3.1, J1.1, J2.1
unnamed: FB4.1, J1.3, J2.3
