mirdej/synkie/kicad/SynkieDesignBlocks.kicad_blocks/ReferenceVoltage_1V.kicad_block/ReferenceVoltage_1V.kicad_pcb

## KiCad design kicad/SynkieDesignBlocks.kicad_blocks/ReferenceVoltage_1V.kicad_block/ReferenceVoltage_1V.kicad_pcb (2026-05-15)

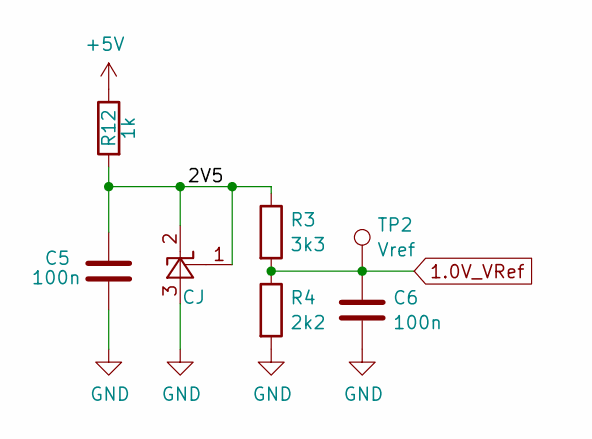
[picture p146: schematic ReferenceVoltage_1V.kicad_sch]

Parts:
C5, C6: 100n; C_0603_1608Metric; LCSC C14663
R3: 3k3; R_0603_1608Metric; LCSC C22978
R4: 2k2; R_0603_1608Metric; LCSC C4190
R12: 1k; R_0603_1608Metric; LCSC C21190
TP2: Vref; TestPoint_Pad_D1.0mm
U5: CJ; SOT-23; LCSC C3113

Connections:
1.0V_VRef: C6.1, R3.2, R4.1, TP2.1 (1_1)
+5V: R12.1
/2V5: C5.1, R3.1, R12.2, U5.1 (R), U5.2 (K)
GND: C5.2, C6.2, R4.2, U5.3 (A)

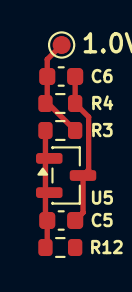
[picture p147: board ReferenceVoltage_1V.kicad_pcb from above]

Board: 2 copper layers, 7 parts (0 on the bottom side), 3 nets.
