mirdej/synkie/kicad/SynkieDesignBlocks.kicad_blocks/Power-MolexKK.kicad_block/Power-MolexKK.kicad_pcb

## KiCad design kicad/SynkieDesignBlocks.kicad_blocks/Power-MolexKK.kicad_block/Power-MolexKK.kicad_pcb (2026-05-15)

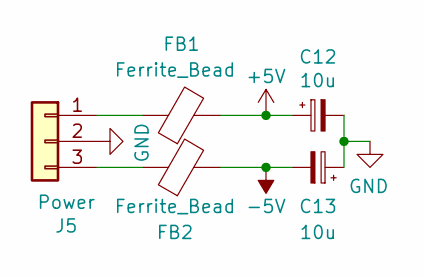
[picture p148: schematic Power-MolexKK.kicad_sch]

Parts:
C12, C13: 10u; C_0805_2012Metric; LCSC C15850
FB1, FB2: Ferrite_Bead; L_0805_2012Metric; LCSC C1017
J5: Power; Molex_KK-254_AE-6410-03A_1x03_P2.54mm_Vertical_SMD

Connections:
+5V: C12.1, FB1.2
-5V: C13.2, FB2.2
GND: C12.2, C13.1, J5.2
unnamed: FB1.1, J5.1
unnamed: FB2.1, J5.3

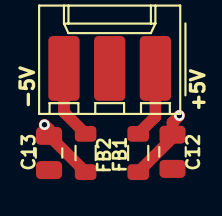
[picture p149: board Power-MolexKK.kicad_pcb from above]

Board: 2 copper layers, 5 parts (0 on the bottom side), 5 nets.
