mirdej/synkie/kicad/SynkieDesignBlocks.kicad_blocks/ReferenceVoltage_0.5V.kicad_block/ReferenceVoltage_0.5V.kicad_pcb

## KiCad design kicad/SynkieDesignBlocks.kicad_blocks/ReferenceVoltage_0.5V.kicad_block/ReferenceVoltage_0.5V.kicad_pcb (2026-05-15)

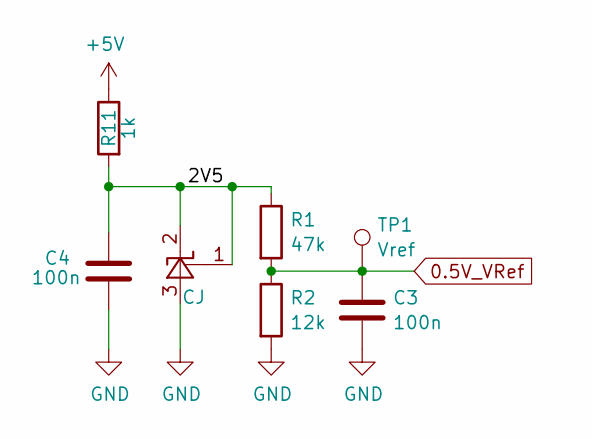
[picture p150: schematic ReferenceVoltage_0.5V.kicad_sch]

Parts:
C3, C4: 100n; C_0603_1608Metric; LCSC C14663
R1: 47k; R_0603_1608Metric; LCSC C25819
R2: 12k; R_0603_1608Metric; LCSC C22790
R11: 1k; R_0603_1608Metric; LCSC C21190
TP1: Vref; TestPoint_Pad_D1.0mm
U4: CJ; SOT-23; LCSC C3113

Connections:
0.5V_VRef: C3.1, R1.2, R2.1, TP1.1 (1_1)
+5V: R11.1
/2V5: C4.1, R1.1, R11.2, U4.1 (R), U4.2 (K)
GND: C3.2, C4.2, R2.2, U4.3 (A)

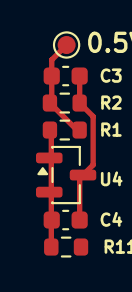
[picture p151: board ReferenceVoltage_0.5V.kicad_pcb from above]

Board: 2 copper layers, 7 parts (0 on the bottom side), 3 nets.
