mirdej/synkie/kicad/sk107-comparator/sk107-comparator.kicad_pcb

## KiCad design kicad/sk107-comparator/sk107-comparator.kicad_pcb (2026-05-13)

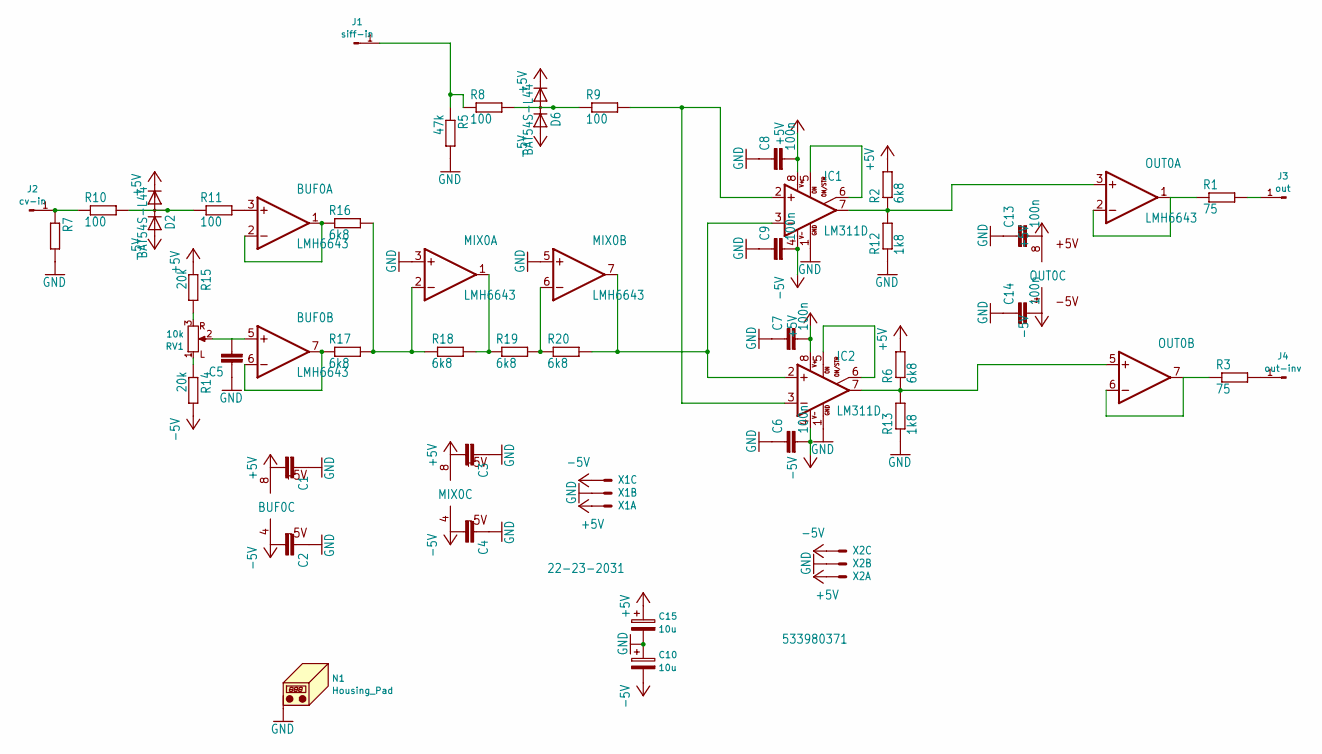
[picture p152: schematic sk107-comparator.kicad_sch]

Parts:
BUF0: LMH6643; VSSOP-8_3x3mm_P0.65mm; LCSC C478382
C1, C2, C3, C4, C5, C6, C7, C8, C9, C13, C14: 100n; C_0603_1608Metric_Pad1.05x0.95mm_HandSolder; LCSC C14663
C10, C15: 10u; C_1206_3216Metric_Pad1.42x1.75mm_HandSolder; LCSC C13585
D2, D6: BAT54S-L44; SOT-23; LCSC C8592
IC1, IC2: LM311D; SOIC-8_3.9x4.9mm_P1.27mm; LCSC C12597
J1: siff-in; Banana2mm-Löthülse
J2: cv-in; Banana2mm-Löthülse
J3: out; Banana2mm-Löthülse
J4: out-inv; Banana2mm-Löthülse
MIX0: LMH6643; VSSOP-8_3x3mm_P0.65mm; LCSC C478382
N1: Housing_Pad; Frontplate_20mm
OUT0: LMH6643; VSSOP-8_3x3mm_P0.65mm; LCSC C478382
R1, R3: 75; R_0603_1608Metric; LCSC C4275
R2, R6, R16, R17, R18, R19, R20: 6k8; R_0603_1608Metric; LCSC C23212
R5, R7: 47k; R_0603_1608Metric; LCSC C25819
R8, R9, R10, R11: 100; R_0603_1608Metric; LCSC C22775
R12, R13: 1k8; R_0603_1608Metric; LCSC C4177
R14, R15: 20k; R_0603_1608Metric; LCSC C4184
RV1: 10k; Alps_RK097_Frontplate
X1: 22-23-2031; Molex_KK-254_AE-6410-03A_1x03_P2.54mm_Vertical_SMD
X2: 533980371; Molex_PicoBlade_53398-0371_1x03-1MP_P1.25mm_Vertical; LCSC C293633

Connections:
+5V: BUF0.8 (+5V), C1.2, C3.2, C7.2, C8.2, C13.2, C15.1, D2.2 (C), D6.2 (C), IC1.8 (V+), IC2.8 (V+), MIX0.8 (+5V), OUT0.8 (+5V), R2.2, R6.2, R15.1, X1.1 (S), X2.1 (S)
-5V: BUF0.4 (-5V), C2.2, C4.2, C6.2, C9.2, C10.2, C14.2, D2.1 (A), D6.1 (A), IC1.4 (V-), IC2.4 (V-), MIX0.4 (-5V), OUT0.4 (-5V), R14.2, X1.3 (S), X2.3 (S)
GND: C1.1, C2.1, C3.1, C4.1, C5.1, C6.1, C7.1, C8.1, C9.1, C10.1, C13.1, C14.1, C15.2, IC1.1 (GND), IC2.1 (GND), MIX0.3 (+IN), MIX0.5 (+IN), N1.1 (PAD_1), R5.2, R7.2, R12.1, R13.1, X1.2 (S), X2.2 (S)
unnamed: BUF0.3 (+IN), R11.2
unnamed: BUF0.1 (OUT), BUF0.2 (-IN), R16.1
unnamed: BUF0.5 (+IN), C5.2, RV1.2
unnamed: BUF0.6 (-IN), BUF0.7 (OUT), R17.1
unnamed: D2.3 (AC), R10.2, R11.1
unnamed: D6.3 (AC), R8.2, R9.1
unnamed: IC1.2 (+IN), IC2.3 (-IN), R9.2
unnamed: IC1.3 (-IN), IC2.2 (+IN), MIX0.7 (OUT), R20.2
unnamed: IC1.5 (ON), IC1.6 (ON/STR)
unnamed: IC1.7 (OUT), OUT0.3 (+IN), R2.1, R12.2
unnamed: IC2.5 (ON), IC2.6 (ON/STR)
unnamed: IC2.7 (OUT), OUT0.5 (+IN), R6.1, R13.2
unnamed: J1.1 (Pin_1_1), R5.1, R8.1
unnamed: J2.1 (Pin_1_1), R7.1, R10.1
unnamed: J3.1 (Pin_1_1), R1.2
unnamed: J4.1 (Pin_1_1), R3.2
unnamed: MIX0.2 (-IN), R16.2, R17.2, R18.1
unnamed: MIX0.1 (OUT), R18.2, R19.1
unnamed: MIX0.6 (-IN), R19.2, R20.1
unnamed: OUT0.1 (OUT), OUT0.2 (-IN), R1.1
unnamed: OUT0.6 (-IN), OUT0.7 (OUT), R3.1
unnamed: R15.2, RV1.3
unnamed: R14.1, RV1.1 (L)

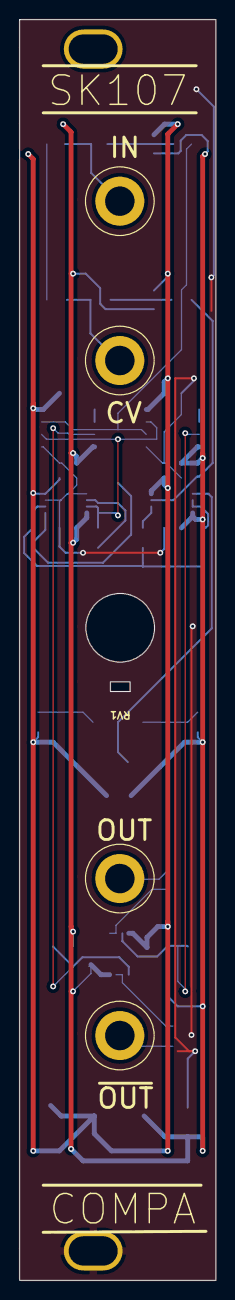
[picture p153: board sk107-comparator.kicad_pcb from above]

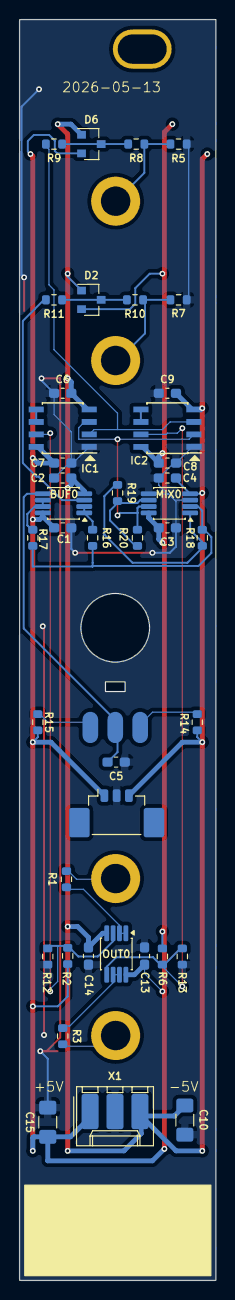
[picture p154: board sk107-comparator.kicad_pcb from below]

Board: 2 copper layers, 20.0 x 128.5 mm, 47 parts (41 on the bottom side), 26 nets.
