mirdej/synkie/kicad/sk009-multiple-bnc/sk009-multiple-bnc.kicad_pcb

## KiCad design kicad/sk009-multiple-bnc/sk009-multiple-bnc.kicad_pcb (2026-04-18)

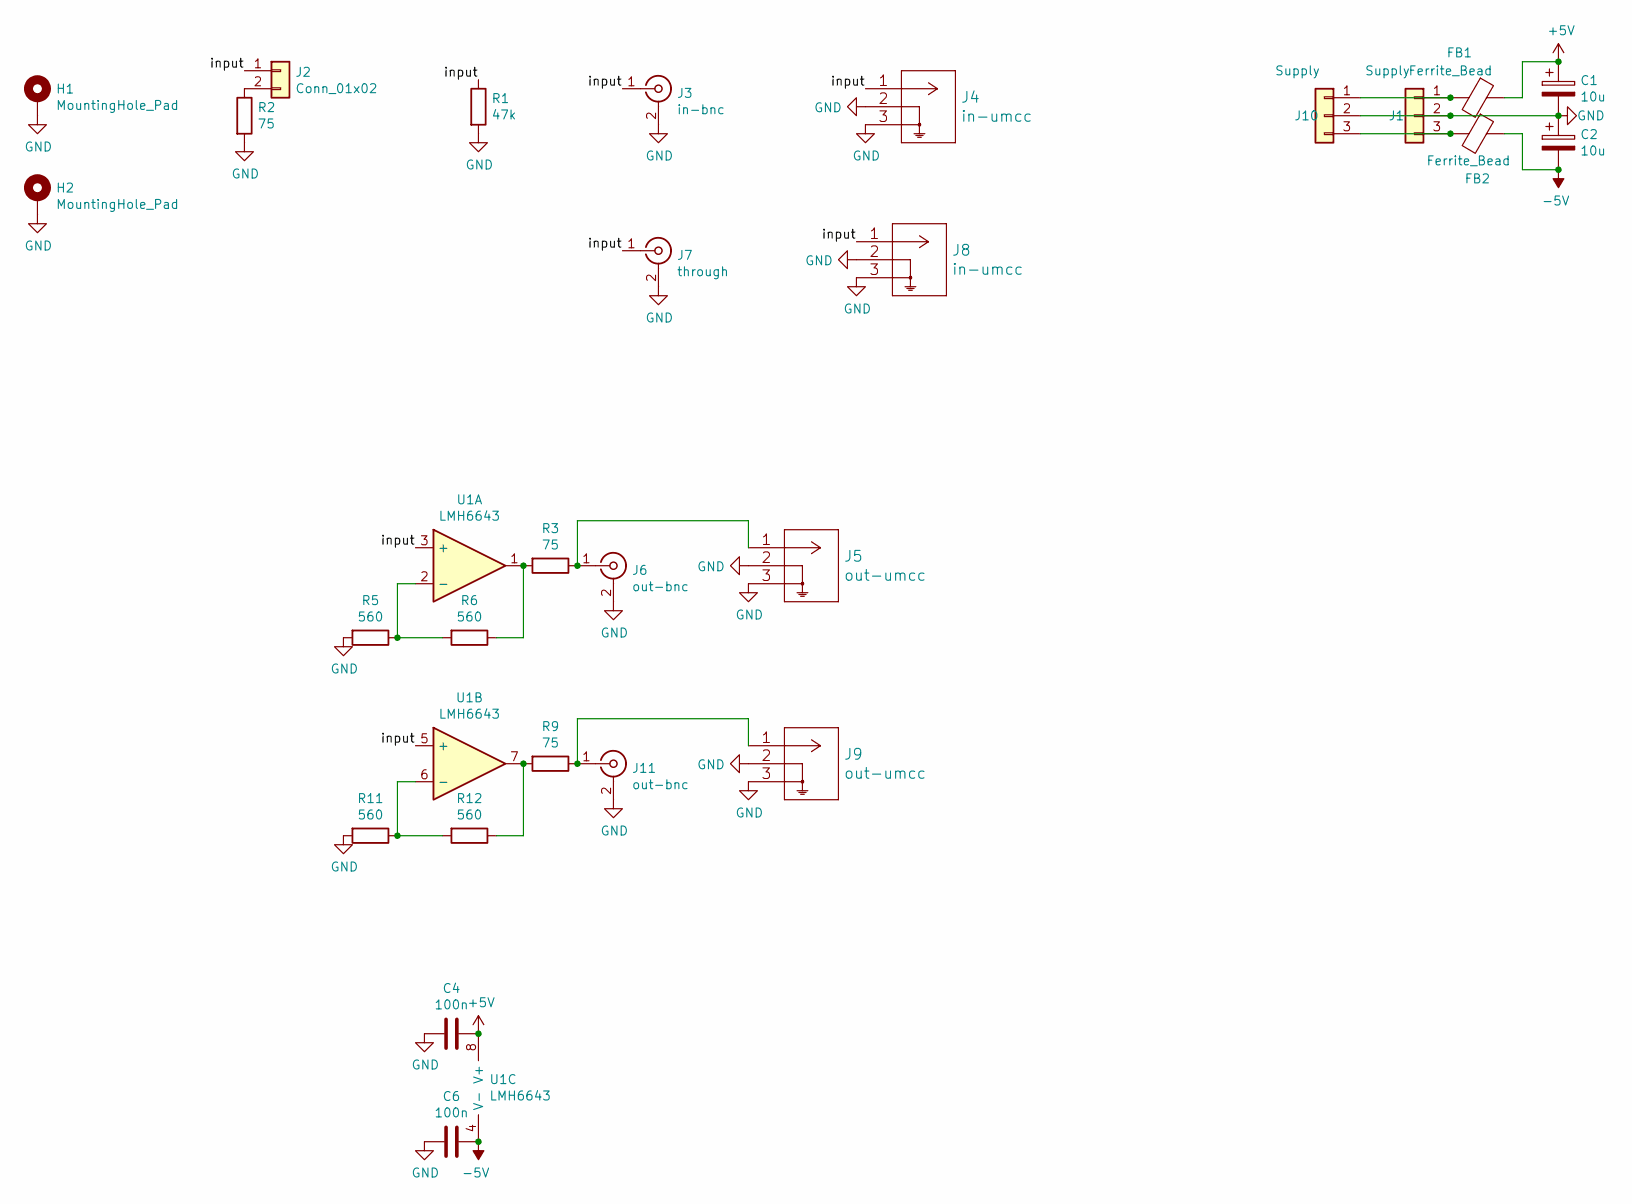
[picture p155: schematic sk009-multiple-bnc.kicad_sch]

Parts:
C1, C2: 10u; C_0805_2012Metric; LCSC C15850
C4, C6: 100n; C_0603_1608Metric; LCSC C14663
FB1, FB2: Ferrite_Bead; L_0805_2012Metric; LCSC C1017
H1, H2: MountingHole_Pad; MountingHole_3.2mm_M3_DIN965_Pad
J1, J10: Supply; Molex_KK-254_AE-6410-03A_1x03_P2.54mm_Vertical
J2: Conn_01x02; PinHeader_1x02_P2.54mm_Vertical
J3: in-bnc; BNC_Aliexpress
J4, J8: in-umcc; TE_UMCC_2337019-1
J5, J9: out-umcc; TE_UMCC_2337019-1
J6, J11: out-bnc; BNC_Aliexpress
J7: through; BNC_Aliexpress
R1: 47k; R_0603_1608Metric; LCSC C25819
R2, R3, R9: 75; R_0603_1608Metric; LCSC C4275
R5, R6, R11, R12: 560; R_0603_1608Metric; LCSC C23204
U1: LMH6643; VSSOP-8_3x3mm_P0.65mm; LCSC C478382

Connections:
+5V: C1.1, C4.1, FB1.1, U1.8 (V+)
-5V: C2.2, C6.1, FB2.1, U1.4 (V-)
/input: J2.1, J3.1 (In), J4.1, J7.1 (In), J8.1, R1.1, U1.3 (+), U1.5 (+)
GND: C1.2, C2.1, C4.2, C6.2, H1.1 (1_1), H2.1 (1_1), J1.2, J3.2 (Ext), J4.2, J4.3, J5.2, J5.3, J6.2 (Ext), J7.2 (Ext), J8.2, J8.3, J9.2, J9.3, J10.2, J11.2 (Ext), R1.2, R2.2, R5.2, R11.2
unnamed: FB1.2, J1.1, J10.1
unnamed: FB2.2, J1.3, J10.3
unnamed: J2.2, R2.1
unnamed: J5.1, J6.1 (In), R3.1
unnamed: J9.1, J11.1 (In), R9.1
unnamed: R3.2, R6.1, U1.1
unnamed: R9.2, R12.1, U1.7
unnamed: R5.1, R6.2, U1.2 (-)
unnamed: R11.1, R12.2, U1.6 (-)

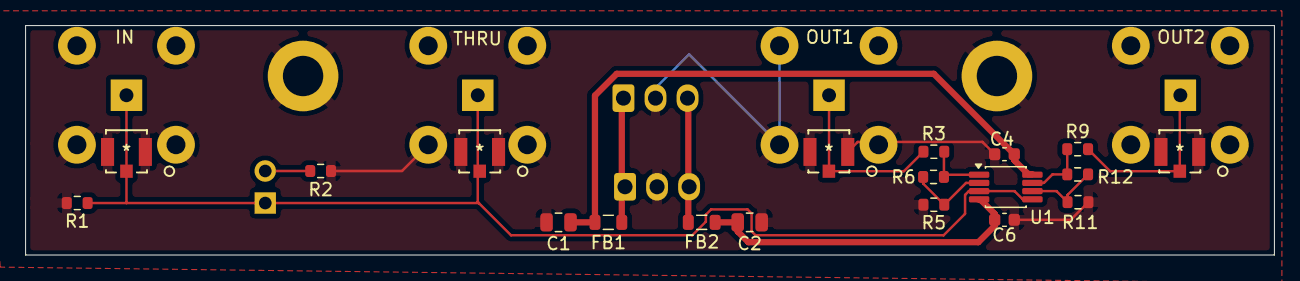
[picture p156: board sk009-multiple-bnc.kicad_pcb from above]

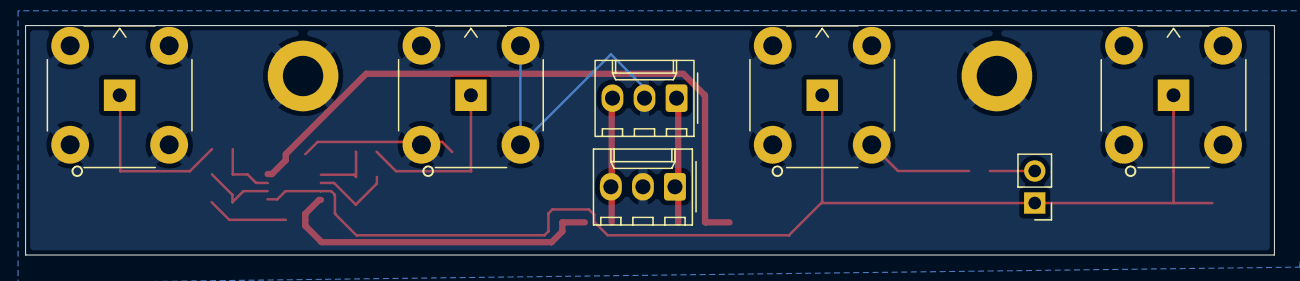
[picture p157: board sk009-multiple-bnc.kicad_pcb from below]

Board: 2 copper layers, 99.0 x 18.2 mm, 28 parts (7 on the bottom side), 13 nets.
