mirdej/synkie/kicad/sk040-3x2mux/sk040-3x2mux.kicad_pcb

## KiCad design kicad/sk040-3x2mux/sk040-3x2mux.kicad_pcb (2026-04-18)

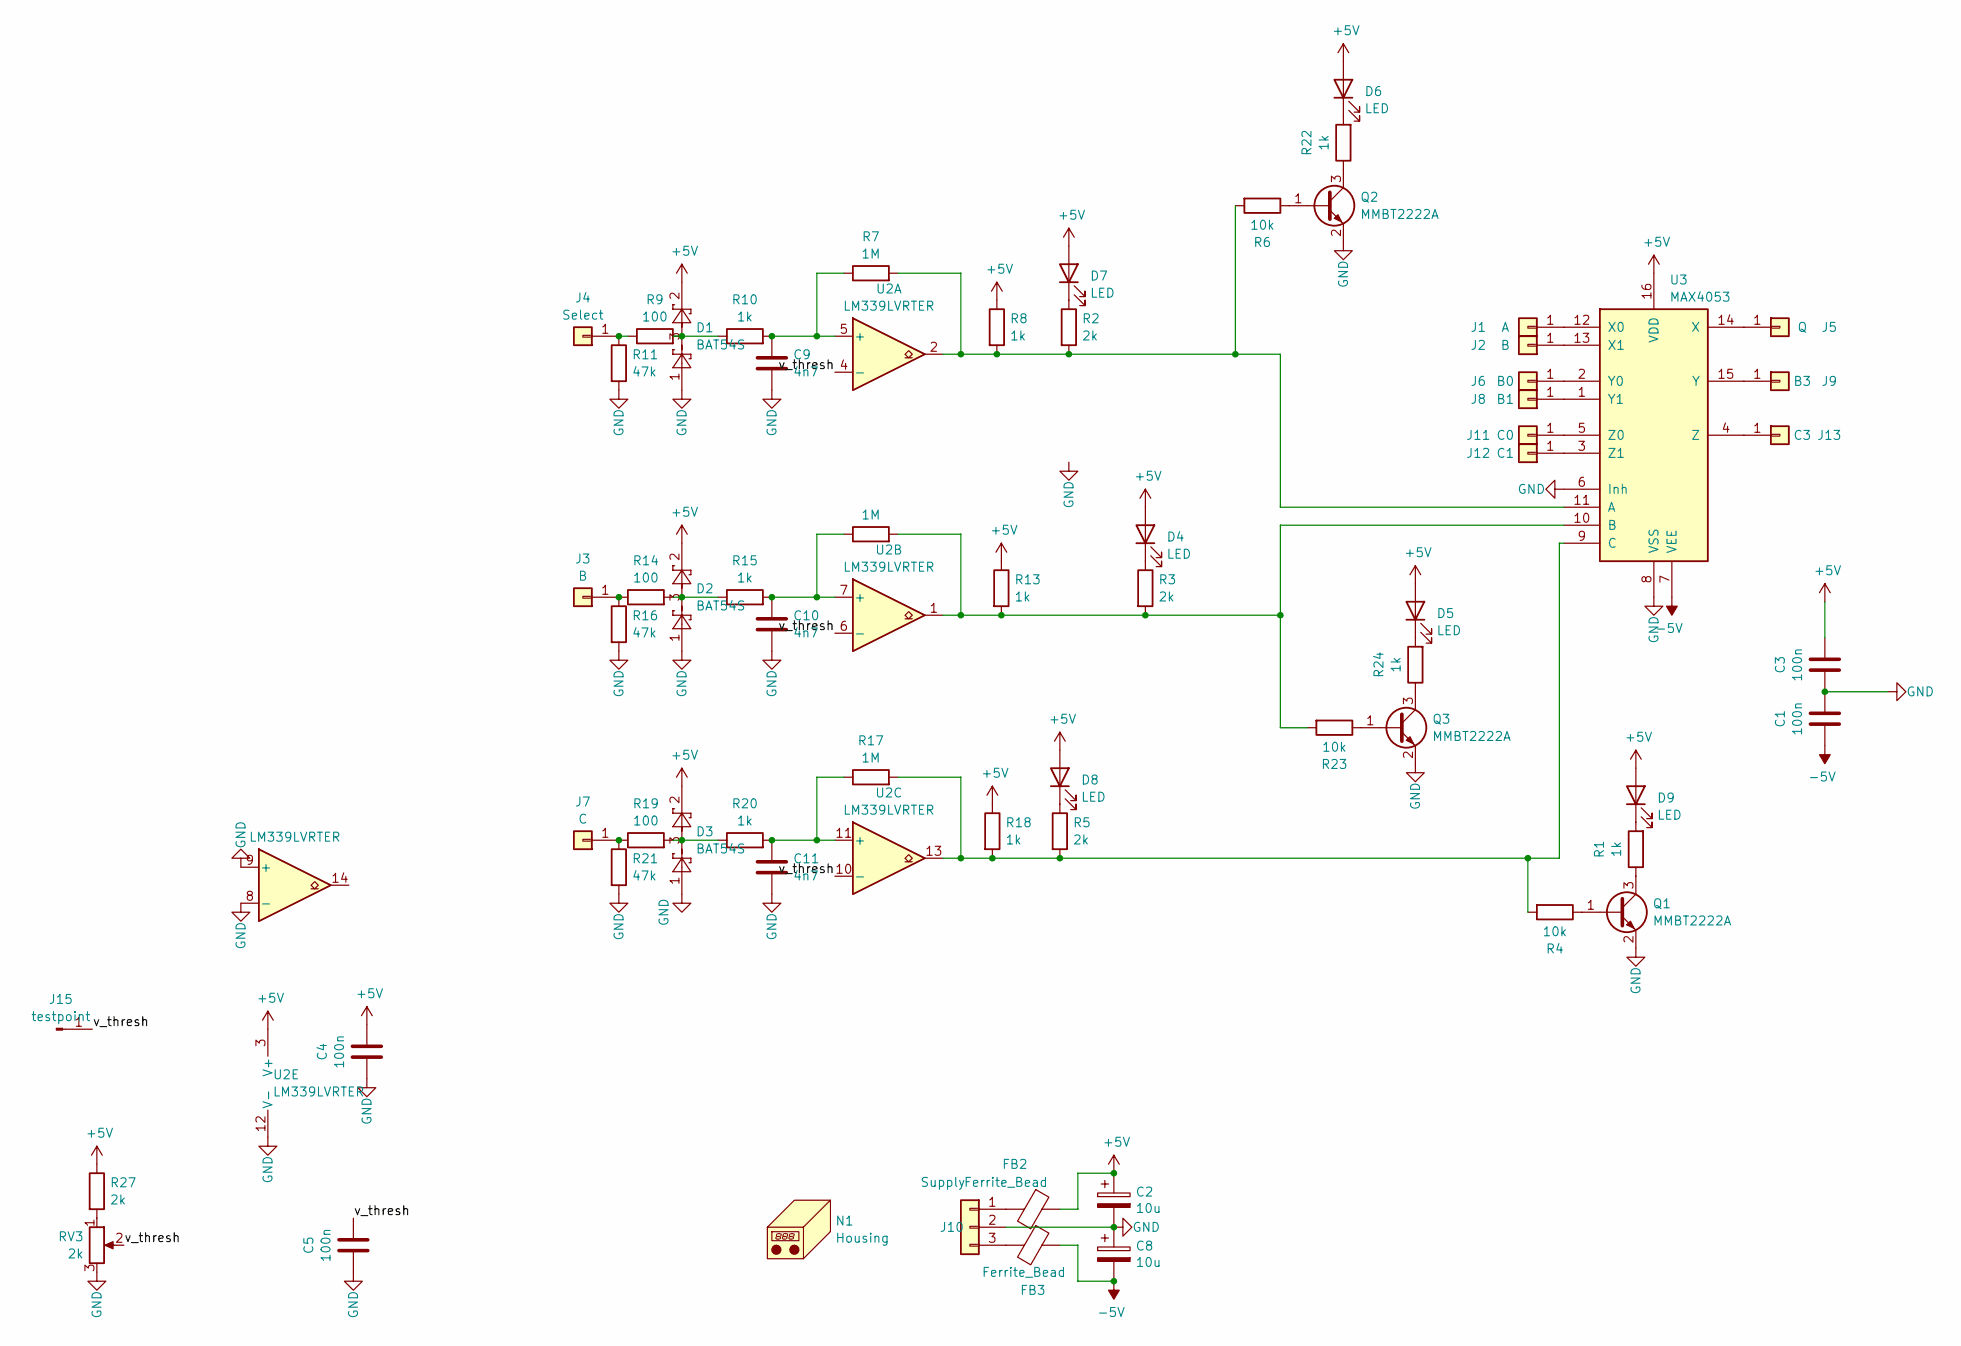
[picture p158: schematic sk040-3x2mux.kicad_sch]

Parts:
C1, C3, C4, C5: 100n; R_0603_1608Metric_Pad1.05x0.95mm_HandSolder; LCSC C14663
C2, C8: 10u; C_1206_3216Metric_Pad1.42x1.75mm_HandSolder; LCSC C13585
C9, C10, C11: 4n7; C_0805_2012Metric_Pad1.15x1.40mm_HandSolder; LCSC C1744
D1, D2, D3: BAT54S; SOT-23; LCSC C8592
D4, D5, D6, D7, D8, D9: LED; LED_1206_3216Metric_ReverseMount_Hole1.8x2.4mm; LCSC C125108
FB2, FB3: Ferrite_Bead; L_0805_2012Metric_Pad1.05x1.20mm_HandSolder; LCSC C1017
J1: A; Banana2mm-Löthülse
J2, J3: B; Banana2mm-Löthülse
J4: Select; Banana2mm-Löthülse
J5: Q; Banana2mm-Löthülse
J6: B0; Banana2mm-Löthülse
J7: C; Banana2mm-Löthülse
J8: B1; Banana2mm-Löthülse
J9: B3; Banana2mm-Löthülse
J10: Supply; smd-3pin
J11: C0; Banana2mm-Löthülse
J12: C1; Banana2mm-Löthülse
J13: C3; Banana2mm-Löthülse
J15: testpoint; TestPoint_Pad_D2.0mm
N1: Housing; Frontplate_20mm
Q1, Q2, Q3: MMBT2222A; SOT-23; LCSC C82460
R1, R8, R10, R13, R15, R18, R20, R22, R24: 1k; R_0805_2012Metric_Pad1.15x1.40mm_HandSolder; LCSC C17513
R2, R3, R5, R27: 2k; R_0805_2012Metric_Pad1.15x1.40mm_HandSolder; LCSC C17604
R4, R6, R23: 10k; R_0805_2012Metric_Pad1.15x1.40mm_HandSolder; LCSC C25804
R7, R12, R17: 1M; R_0805_2012Metric_Pad1.15x1.40mm_HandSolder; LCSC C17514
R9, R14, R19: 100; R_0805_2012Metric_Pad1.15x1.40mm_HandSolder; LCSC C17408
R11, R16, R21: 47k; R_0805_2012Metric_Pad1.15x1.40mm_HandSolder; LCSC C17713
RV3: 2k; Potentiometer_Bourns_3224X_Vertical; LCSC C22384649
U2: LM339LVRTER; WQFN-16-1EP_3x3mm_P0.5mm_EP1.6x1.6mm; LCSC C3658606
U3: MAX4053; SOIC-16_3.9x9.9mm_P1.27mm; LCSC C2673376

Connections:
+5V: C2.1, C3.1, C4.1, D1.2, D2.2, D3.2, D4.2 (A), D5.2 (A), D6.2 (A), D7.2 (A), D8.2 (A), D9.2 (A), FB2.1, R8.1, R13.1, R18.1, R27.1, U2.3 (V+), U3.16 (VDD)
-5V: C1.2, C8.2, FB3.1, U3.7 (VEE)
/v_thresh: C5.1, J15.1, RV3.2, U2.4 (-), U2.6 (-), U2.10 (-)
GND: C1.1, C2.2, C3.2, C4.2, C5.2, C8.1, C9.2, C10.2, C11.2, D1.1, D2.1, D3.1, J10.2, Q1.2 (E), Q2.2 (E), Q3.2 (E), R11.2, R16.2, R21.2, RV3.3, U2.8 (-), U2.9 (+), U2.12 (V-), U3.6 (Inh), U3.8 (VSS)
unnamed: D1.3, R9.2, R10.1
unnamed: D2.3, R14.2, R15.1
unnamed: D3.3, R19.2, R20.1
unnamed: D4.1 (K), R3.1
unnamed: D5.1 (K), R24.2
unnamed: D6.1 (K), R22.2
unnamed: D7.1 (K), R2.1
unnamed: D8.1 (K), R5.1
unnamed: D9.1 (K), R1.2
unnamed: J1.1, U3.12 (X0)
unnamed: J2.1, U3.13 (X1)
unnamed: J3.1, R14.1, R16.1
unnamed: J4.1, R9.1, R11.1
unnamed: J5.1, U3.14 (X)
unnamed: J6.1, U3.2 (Y0)
unnamed: J7.1, R19.1, R21.1
unnamed: J8.1, U3.1 (Y1)
unnamed: J9.1, U3.15 (Y)
unnamed: FB2.2, J10.1
unnamed: FB3.2, J10.3
unnamed: J11.1, U3.5 (Z0)
unnamed: J12.1, U3.3 (Z1)
unnamed: J13.1, U3.4 (Z)
unnamed: Q1.1 (B), R4.1
unnamed: Q1.3 (C), R1.1
unnamed: Q2.1 (B), R6.1
unnamed: Q2.3 (C), R22.1
unnamed: Q3.1 (B), R23.1
unnamed: Q3.3 (C), R24.1
unnamed: R27.2, RV3.1
unnamed: C9.1, R7.1, R10.2, U2.5 (+)
unnamed: C10.1, R12.1, R15.2, U2.7 (+)
unnamed: C11.1, R17.1, R20.2, U2.11 (+)
unnamed: R2.2, R6.2, R7.2, R8.2, U2.2, U3.11 (A)
unnamed: R3.2, R12.2, R13.2, R23.2, U2.1, U3.10 (B)
unnamed: R4.2, R5.2, R17.2, R18.2, U2.13, U3.9 (C)

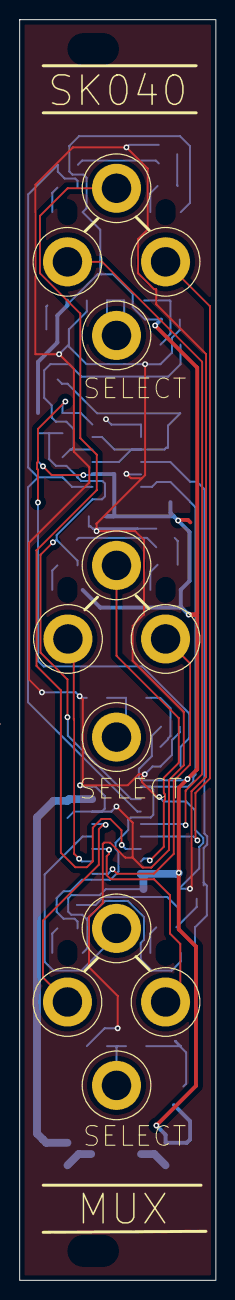
[picture p159: board sk040-3x2mux.kicad_pcb from above]

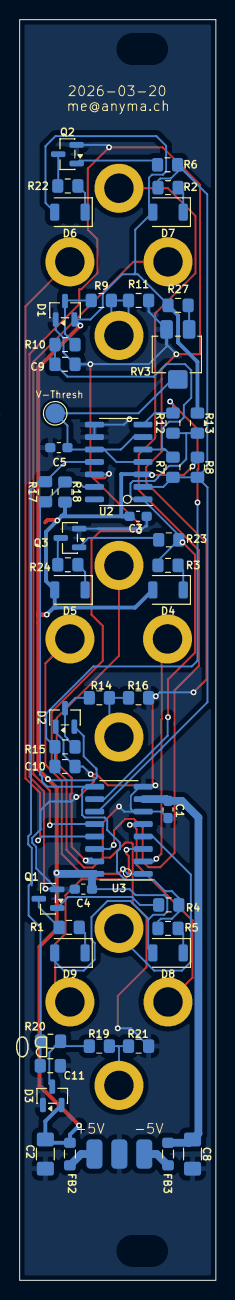
[picture p160: board sk040-3x2mux.kicad_pcb from below]

Board: 2 copper layers, 20.0 x 128.5 mm, 66 parts (53 on the bottom side), 40 nets.
