mirdej/synkie/kicad/sk119-boolean/sk119-boolean.kicad_pcb

## KiCad design kicad/sk119-boolean/sk119-boolean.kicad_pcb (2026-04-14)

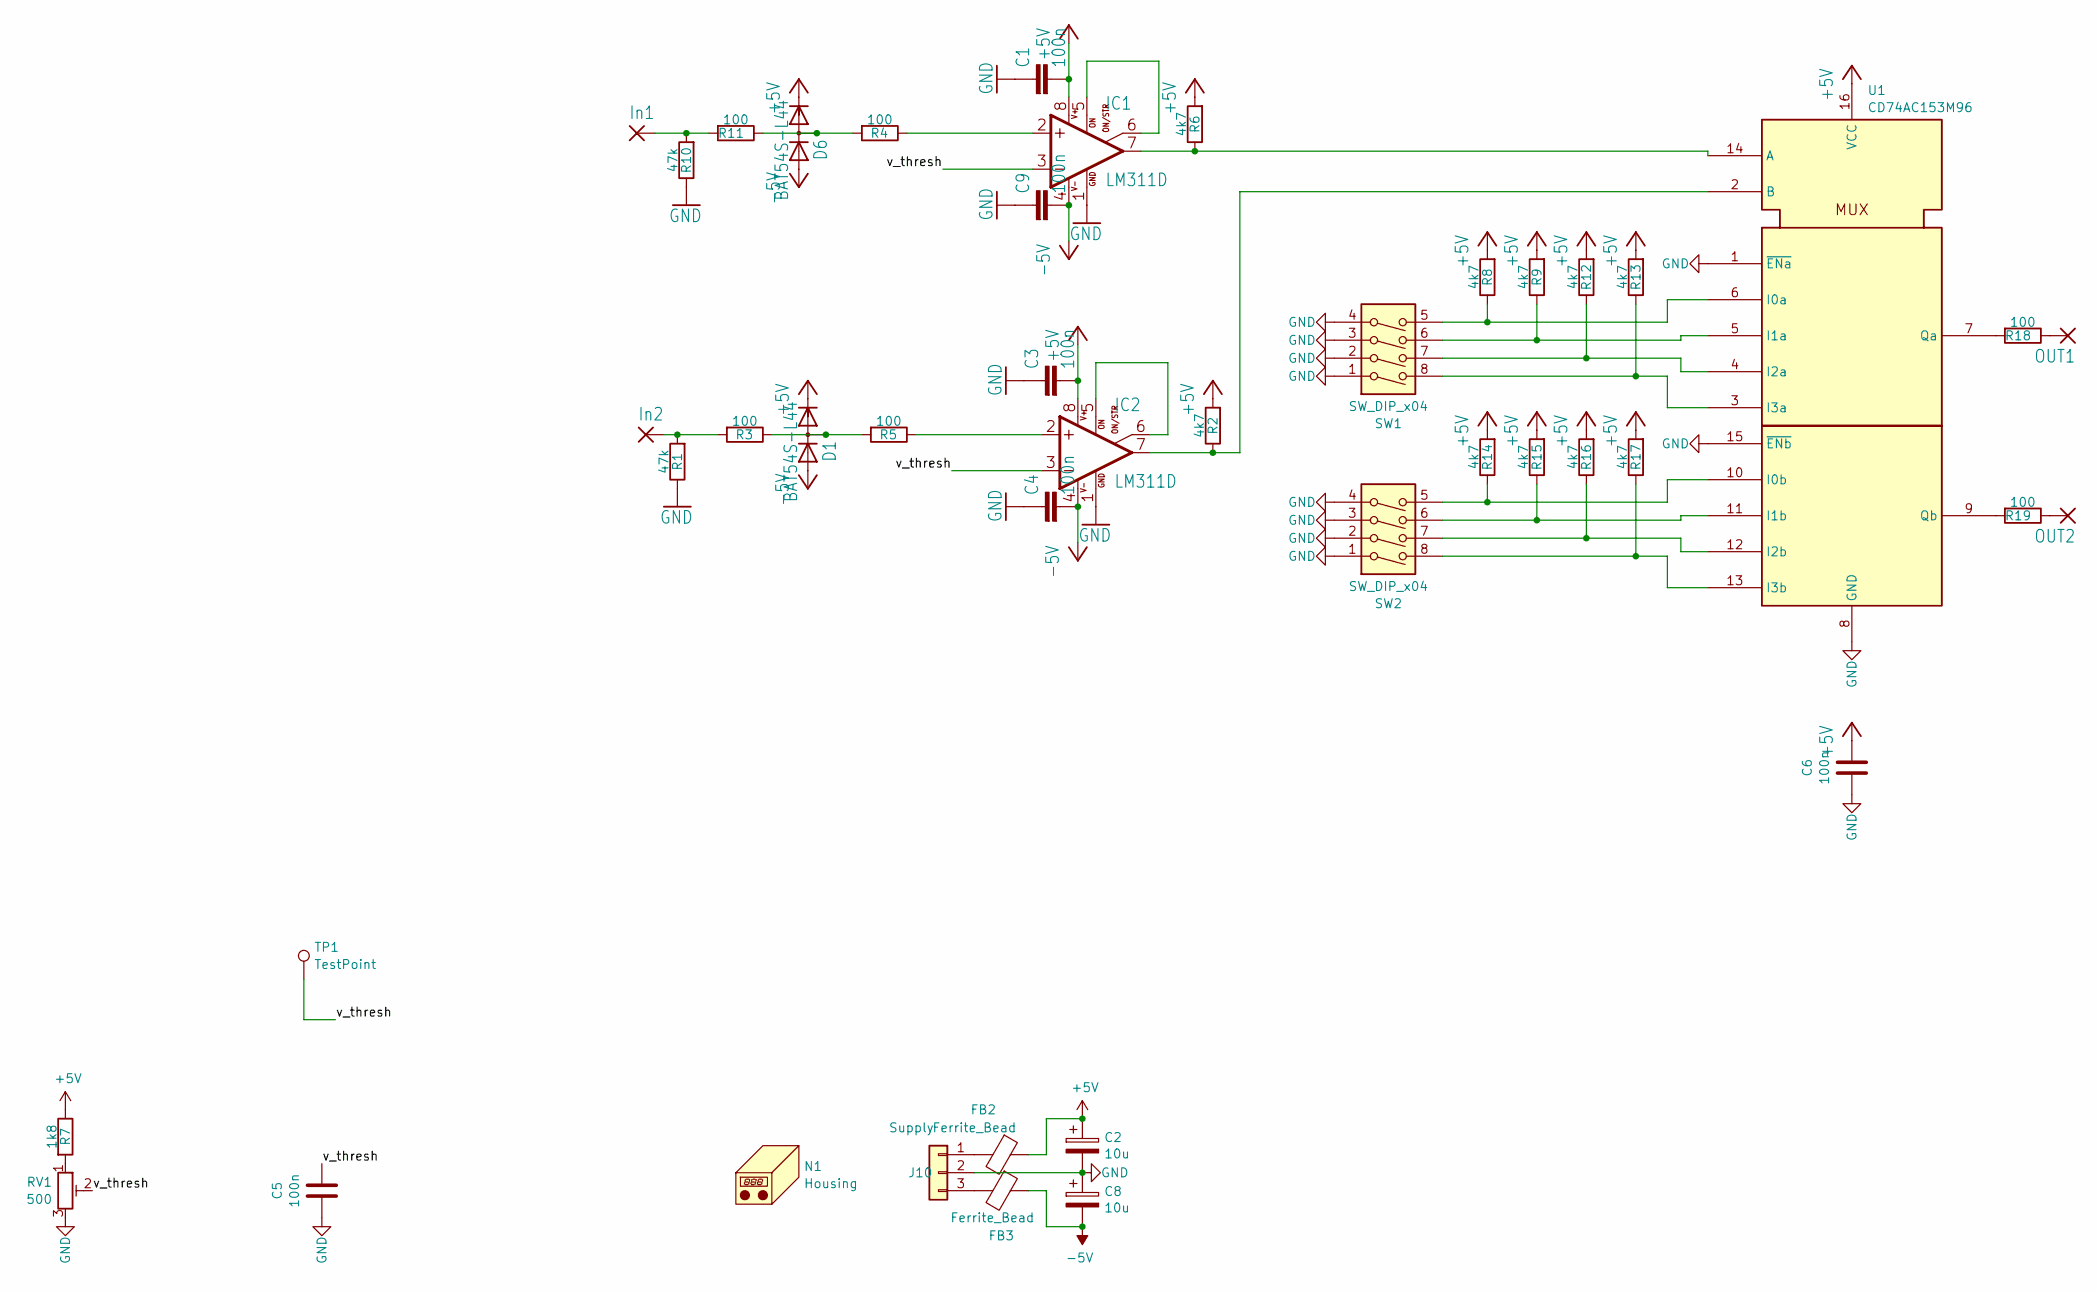
[picture p161: schematic sk119-boolean.kicad_sch]

Parts:
C1, C3, C4, C9: 100n; C_0603_1608Metric_Pad1.05x0.95mm_HandSolder; LCSC C14663
C2, C8: 10u; C_1206_3216Metric_Pad1.42x1.75mm_HandSolder; LCSC C13585
C5, C6: 100n; R_0603_1608Metric_Pad1.05x0.95mm_HandSolder; LCSC C14663
D1, D6: BAT54S-L44; SOT-23; LCSC C8592
FB2, FB3: Ferrite_Bead; L_0805_2012Metric_Pad1.05x1.20mm_HandSolder; LCSC C1017
IC1, IC2: LM311D; SOIC-8_3.9x4.9mm_P1.27mm; LCSC C12597
In1, In2: 3,17/1,1; Banana2mm-Löthülse
J10: Supply; smd-3pin
N1: Housing; Frontplate_20mm
OUT1, OUT2: 3,17/1,1; Banana2mm-Löthülse
R1, R10: 47k; R_0603_1608Metric; LCSC C25819
R2, R6, R8, R9, R12, R13, R14, R15, R16, R17: 4k7; R_0603_1608Metric; LCSC C23162
R3, R4, R5, R11, R18, R19: 100; R_0603_1608Metric; LCSC C22775
R7: 1k8; R_0603_1608Metric; LCSC C4177
RV1: 500; Potentiometer_Bourns_3314J_Vertical; LCSC C123873
SW1, SW2: SW_DIP_x04; CFS-0403TB-Bottom-Entry
TP1: TestPoint; TestPoint_Pad_D2.5mm
U1: CD74AC153M96; SOP-16_4.4x10.4mm_P1.27mm; LCSC C553188

Connections:
+5V: C1.2, C2.1, C3.2, C6.1, D1.2 (C), D6.2 (C), FB2.1, IC1.8 (V+), IC2.8 (V+), R2.2, R6.2, R7.1, R8.2, R9.2, R12.2, R13.2, R14.2, R15.2, R16.2, R17.2, U1.16 (VCC)
-5V: C4.2, C8.2, C9.2, D1.1 (A), D6.1 (A), FB3.1, IC1.4 (V-), IC2.4 (V-)
/v_thresh: C5.1, IC1.3 (-IN), IC2.3 (-IN), RV1.2, TP1.1
GND: C1.1, C2.2, C3.1, C4.1, C5.2, C6.2, C8.1, C9.1, IC1.1 (GND), IC2.1 (GND), J10.2, R1.1, R10.1, RV1.3, SW1.1, SW1.2, SW1.3, SW1.4, SW2.1, SW2.2, SW2.3, SW2.4, U1.1 (~ENa), U1.8 (GND), U1.15 (~ENb)
unnamed: D1.3 (AC), R3.1, R5.2
unnamed: D6.3 (AC), R4.2, R11.1
unnamed: IC1.2 (+IN), R4.1
unnamed: IC1.5 (ON), IC1.6 (ON/STR)
unnamed: IC1.7 (OUT), R6.1, U1.14 (A)
unnamed: IC2.2 (+IN), R5.1
unnamed: IC2.5 (ON), IC2.6 (ON/STR)
unnamed: IC2.7 (OUT), R2.1, U1.2 (B)
unnamed: In1.1, R10.2, R11.2
unnamed: In2.1, R1.2, R3.2
unnamed: FB2.2, J10.1
unnamed: FB3.2, J10.3
unnamed: OUT1.1, R18.1
unnamed: OUT2.1, R19.1
unnamed: R7.2, RV1.1
unnamed: R8.1, SW1.5, U1.6 (I0a)
unnamed: R14.1, SW2.5, U1.10 (I0b)
unnamed: R9.1, SW1.6, U1.5 (I1a)
unnamed: R15.1, SW2.6, U1.11 (I1b)
unnamed: R12.1, SW1.7, U1.4 (I2a)
unnamed: R16.1, SW2.7, U1.12 (I2b)
unnamed: R13.1, SW1.8, U1.3 (I3a)
unnamed: R17.1, SW2.8, U1.13 (I3b)
unnamed: R18.2, U1.7 (Qa)
unnamed: R19.2, U1.9 (Qb)

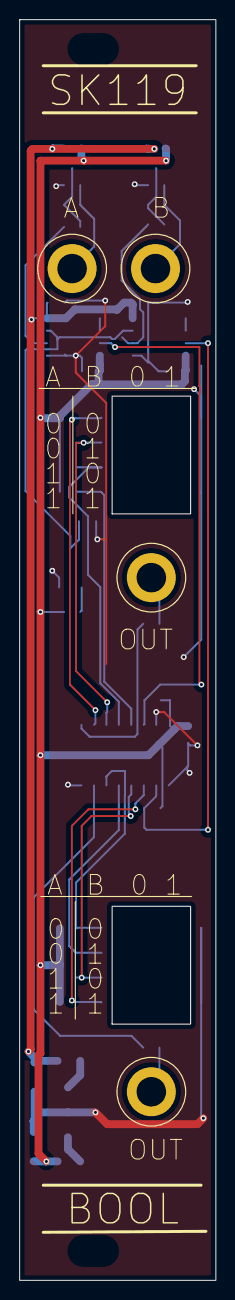
[picture p162: board sk119-boolean.kicad_pcb from above]

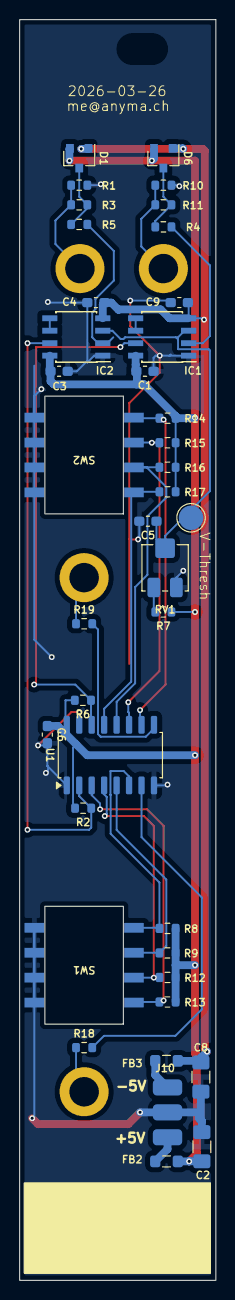
[picture p163: board sk119-boolean.kicad_pcb from below]

Board: 2 copper layers, 20.0 x 128.5 mm, 44 parts (39 on the bottom side), 29 nets.
