mirdej/synkie/kicad/sk003-output/sk003-output.kicad_pcb

## KiCad design kicad/sk003-output/sk003-output.kicad_pcb (2026-03-27)

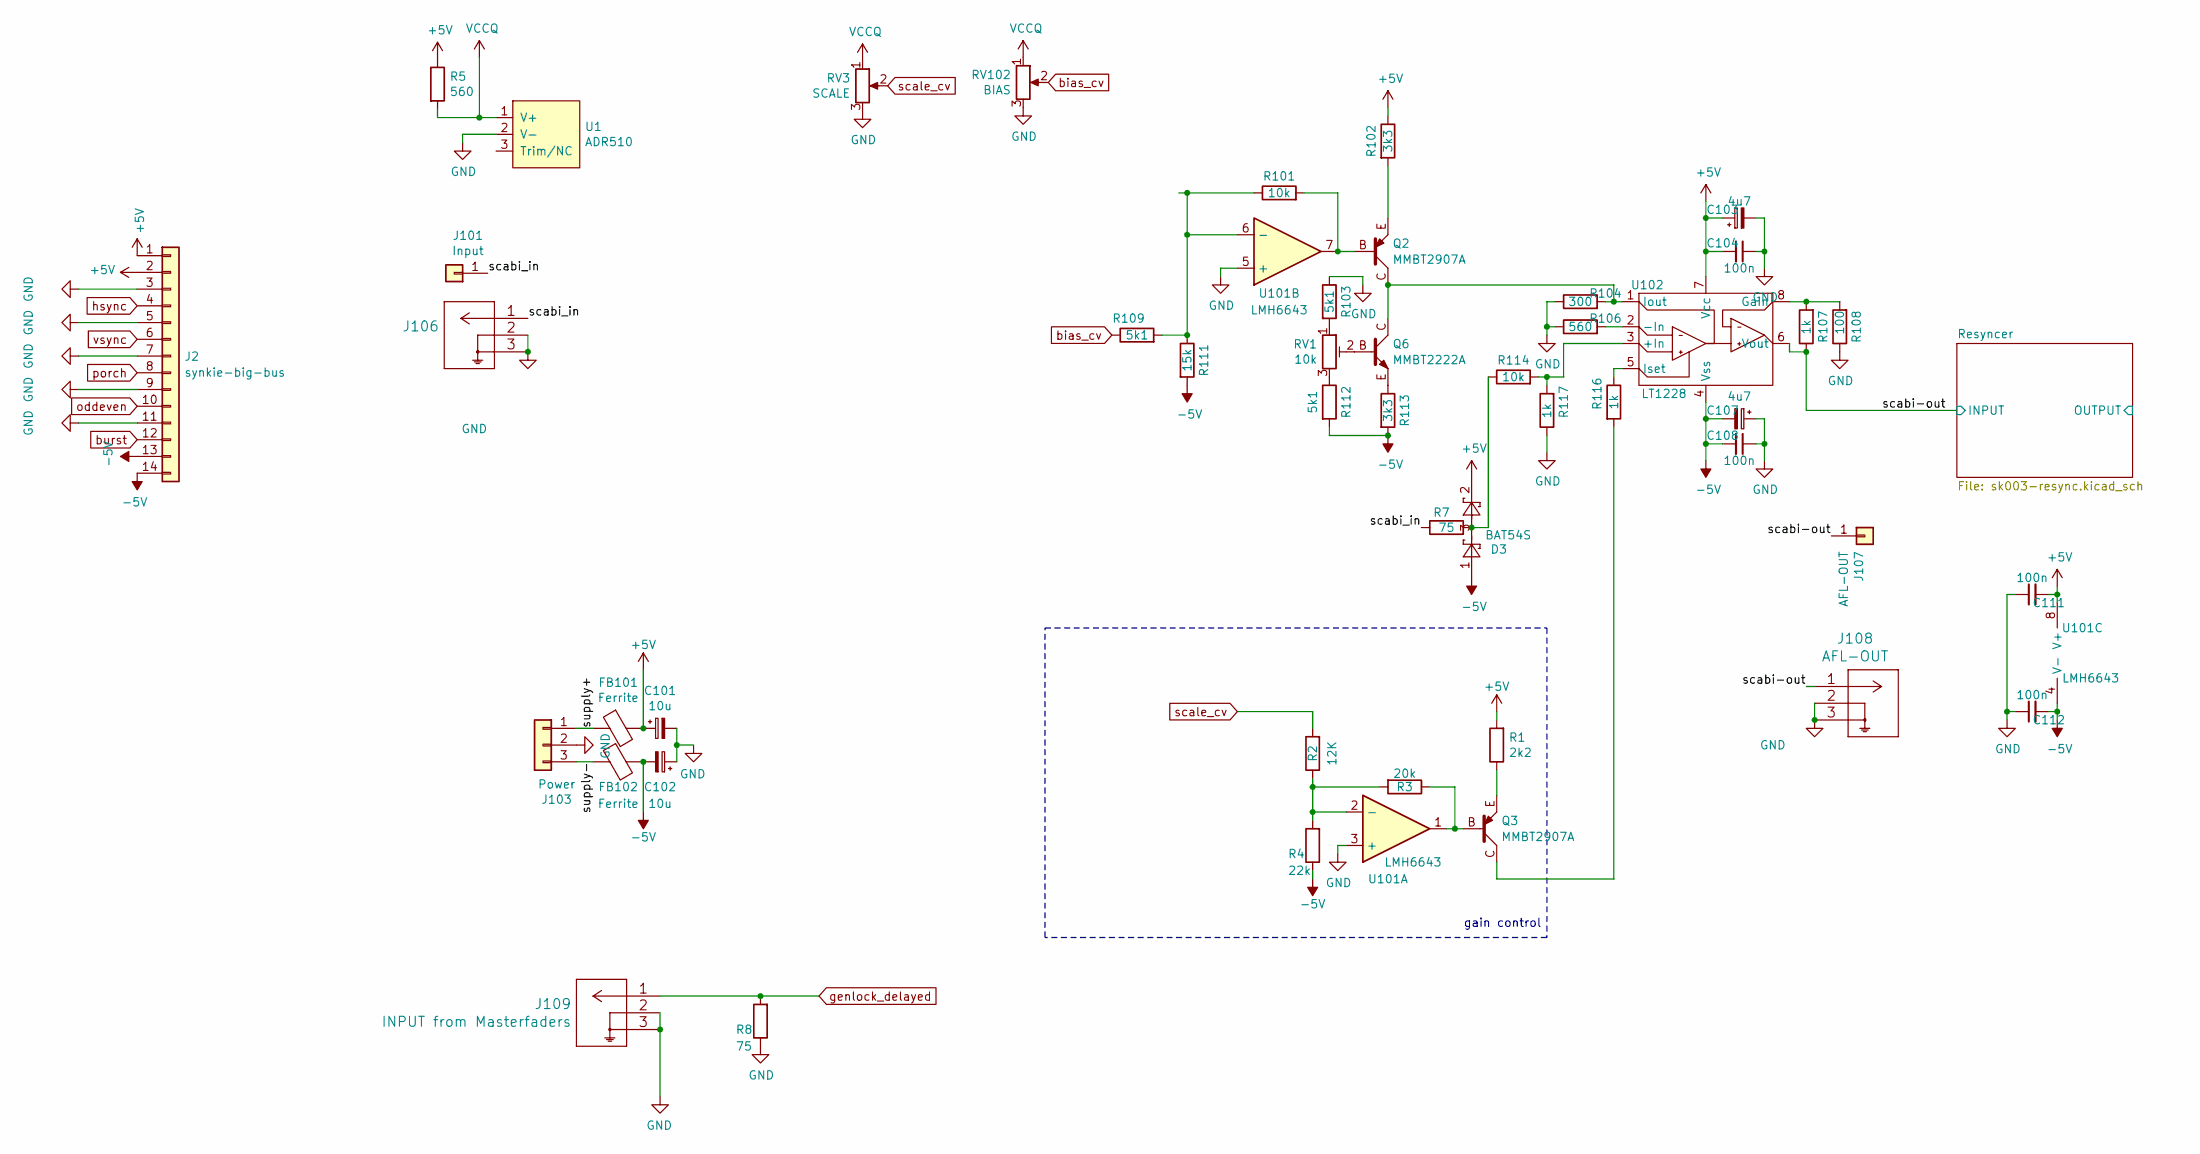
[picture p164: schematic sk003-output.kicad_sch, sk002-output]

Parts:
C101, C102: 10u; C_0805_2012Metric; LCSC C15850
C103, C107: 4u7; C_1206_3216Metric; LCSC C29823
C104, C108, C111, C112: 100n; C_0603_1608Metric; LCSC C14663
D3: BAT54S; SOT-23; LCSC C8592
FB101, FB102: Ferrite; L_0805_2012Metric_Pad1.15x1.40mm_HandSolder; LCSC C1017
J2: synkie-big-bus; IDC-Header_2x07_P2.54mm_Vertical
J101: Input; TestPoint_THTPad_D4.0mm_Drill2.0mm
J103: Power; Molex_KK-254_AE-6410-03A_1x03_P2.54mm_Vertical
J106: INPUT from Mixbus; TE_UMCC_2337019-1
J107: AFL-OUT; TestPoint_THTPad_D4.0mm_Drill2.0mm
J108: AFL-OUT; TE_UMCC_2337019-1; LCSC C5137195
J109: INPUT from Masterfaders; TE_UMCC_2337019-1; LCSC C5137195
Q2, Q3: MMBT2907A; SOT-23_BEC; LCSC C40752
Q6: MMBT2222A; SOT-23_BEC; LCSC C82460
R1: 2k2; R_0603_1608Metric; LCSC C4190
R2: 12K; R_0603_1608Metric; LCSC C22790
R3: 20k; R_0603_1608Metric; LCSC C4184
R4: 22k; R_0603_1608Metric; LCSC C31850
R5, R106: 560; R_0603_1608Metric; LCSC C23204
R7, R8: 75; R_0603_1608Metric; LCSC C4275
R101, R114: 10k; R_0603_1608Metric; LCSC C25804
R102, R113: 3k3; R_0603_1608Metric; LCSC C22978
R103, R109, R112: 5k1; R_0603_1608Metric; LCSC C23186
R104: 300; R_0603_1608Metric; LCSC C23025
R107, R116, R117: 1k; R_0603_1608Metric; LCSC C21190
R108: 100; R_0603_1608Metric; LCSC C22775
R111: 15k; R_0603_1608Metric; LCSC C22809
RV1: 10k; Potentiometer_Bourns_3296Y_Vertical; LCSC C25804
RV3: SCALE; Potentiometer_Alps_RK09L_Single_Horizontal
RV102: BIAS; Potentiometer_Alps_RK09L_Single_Horizontal
U1: ADR510; SOT-23; LCSC C77651
U101: LMH6643; VSSOP-8_3x3mm_P0.65mm; LCSC C478382
U102: LT1228; SOIC-8_3.9x4.9mm_P1.27mm

Connections:
+5V: C101.1, C103.1, C104.2, C111.2, D3.2, FB101.2, J2.1, J2.2, R1.2, R5.1, R102.1, U101.8 (V+), U102.7 (Vcc); also elsewhere on the board
-5V: C102.2, C107.2, C108.2, C112.2, D3.1, FB102.2, J2.13, J2.14, R4.1, R111.2, R112.2, R113.2, U101.4 (V-), U102.4 (Vss); also elsewhere on the board
/scabi-out: J107.1, J108.1, R107.1, U102.6 (Vout); also elsewhere on the board
/scabi_in: J101.1, J106.1, R7.1
/supply+: FB101.1, J103.1
/supply-: FB102.1, J103.3
GND: C101.2, C102.1, C103.2, C104.1, C107.1, C108.1, C111.1, C112.1, J2.3, J2.5, J2.7, J2.9, J2.11, J103.2, J106.2, J106.3, J108.2, J108.3, J109.2, J109.3, R8.1, R103.1, R104.1, R106.1, R108.1, R117.1, RV3.3, RV102.3, U1.2 (V-), U101.3 (+), U101.5 (+); also elsewhere on the board
unnamed: D3.3, R7.2, R114.1
unnamed: Q2.B, R101.2, U101.7
unnamed: Q2.E, R102.2
unnamed: Q3.B, R3.1, U101.1
unnamed: Q3.C, R116.2
unnamed: Q3.E, R1.1
unnamed: Q6.B, RV1.2
unnamed: Q6.E, R113.1
unnamed: R103.2, RV1.1
unnamed: R112.1, RV1.3
unnamed: R2.1, R3.2, R4.2, U101.2 (-)
unnamed: R101.1, R109.2, R111.1, U101.6 (-)
unnamed: R114.2, R117.2, U102.3 (+In)
unnamed: R106.2, U102.2 (-In)
unnamed: R107.2, R108.2, U102.8 (Gain)
unnamed: Q2.C, Q6.C, R104.2, U102.1 (Iout)
unnamed: R116.1, U102.5 (Iset)
VCCQ: R5.2, RV3.1, RV102.1, U1.1 (V+)
bias_cv: R109.1, RV102.2
burst: J2.12; also elsewhere on the board
genlock_delayed: J109.1, R8.2; also elsewhere on the board
hsync: J2.4; also elsewhere on the board
oddeven: J2.10
porch: J2.8; also elsewhere on the board
scale_cv: R2.2, RV3.2
vsync: J2.6

Notes on the sheet:
gain control

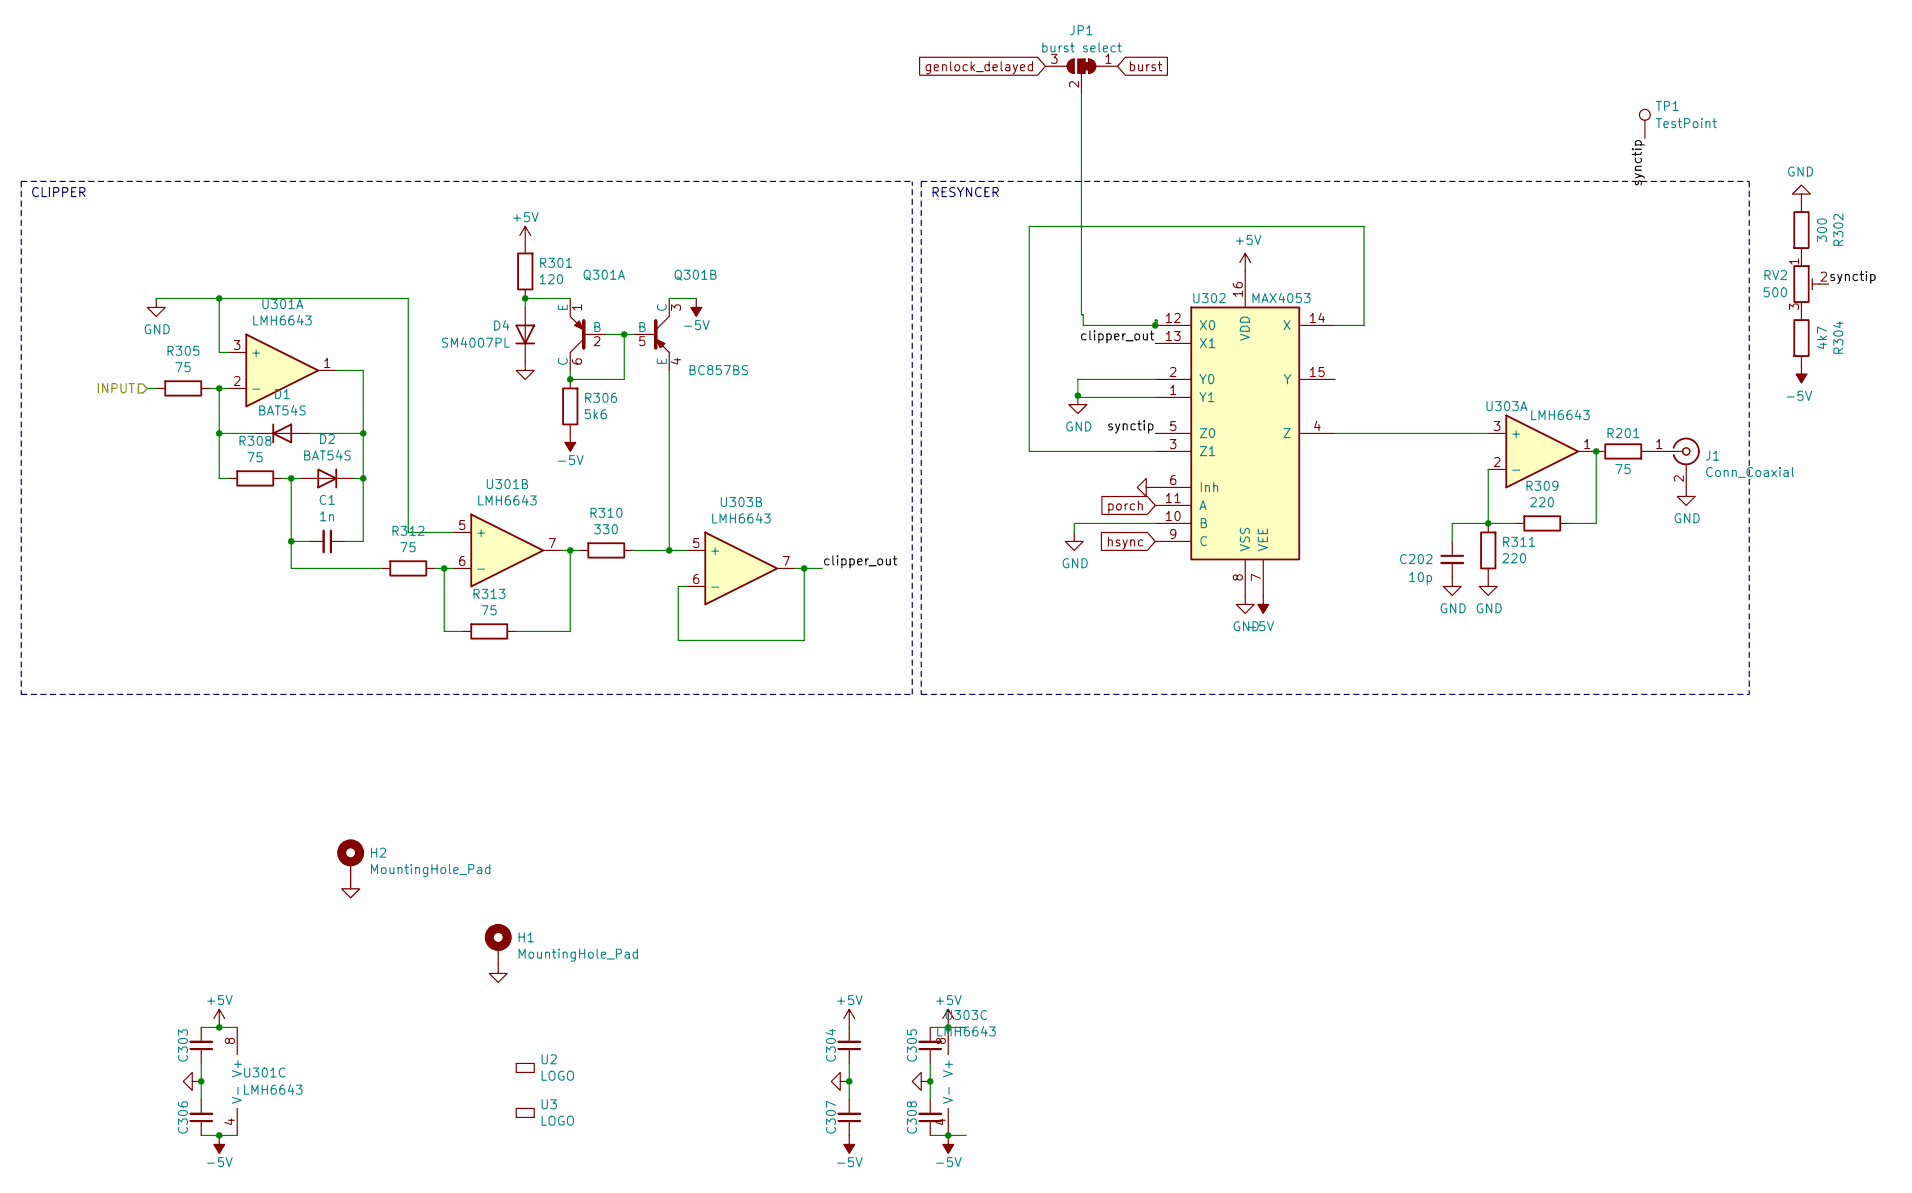
[picture p165: schematic sk003-resync.kicad_sch, vMIX20-Resyncer]

Parts:
C1: 1n; C_0603_1608Metric; LCSC C1588
C202: 10p; C_0603_1608Metric; LCSC C1634
C303, C304, C305, C306, C307, C308: 100n; C_0603_1608Metric; LCSC C14663
D1, D2: BAT54S; SOT-23; LCSC C8592
D4: SM4007PL; D_SOD-123F; LCSC C64898
H1: MountingHole_Pad; MountingHole_2.7mm_M2.5_DIN965_Pad
H2: MountingHole_Pad; CrocodileGroundPad
J1: Conn_Coaxial; BNC_Aliexpress
JP1: burst select; SolderJumper-3_P1.3mm_Bridged12_Pad1.0x1.5mm_NumberLabels
Q301: BC857BS; SOT-363_SC-70-6_Handsoldering; LCSC C22381405
R201, R305, R308, R312, R313: 75; R_0603_1608Metric; LCSC C4275
R301: 120; R_0603_1608Metric; LCSC C22787
R302: 300; R_0603_1608Metric; LCSC C23025
R304: 4k7; R_0603_1608Metric; LCSC C23162
R306: 5k6; R_0603_1608Metric; LCSC C23189
R309, R311: 220; R_0603_1608Metric; LCSC C22962
R310: 330; R_0603_1608Metric; LCSC C23138
RV2: 500; Potentiometer_Bourns_3314J_Vertical; LCSC C123873
TP1: TestPoint; TestPoint_Pad_2.0x2.0mm
U2: LOGO; logo_anyma
U3: LOGO; OSHW-Logo2_9.8x8mm_SilkScreen
U301, U303: LMH6643; VSSOP-8_3x3mm_P0.65mm; LCSC C478382
U302: MAX4053; SOIC-16_3.9x9.9mm_P1.27mm; LCSC C1545882

Connections:
+5V: C303.2, C304.2, C305.2, R301.2, U301.8 (V+), U302.16 (VDD), U303.8 (V+); also elsewhere on the board
-5V: C306.1, C307.1, C308.1, Q301.3 (C), R304.2, R306.1, U301.4 (V-), U302.7 (VEE), U303.4 (V-); also elsewhere on the board
/Resyncer/clipper_out: U302.13 (X1), U303.6 (-), U303.7
/Resyncer/synctip: RV2.2, TP1.1, U302.5 (Z0)
/scabi-out: R305.2; also elsewhere on the board
GND: C202.2, C303.1, C304.1, C305.1, C306.2, C307.2, C308.2, D4.1 (K), H1.1, H2.1, J1.2 (Ext), R302.1, R311.1, U301.3 (+), U301.5 (+), U302.1 (Y1), U302.2 (Y0), U302.6 (Inh), U302.8 (VSS), U302.10 (B); also elsewhere on the board
unnamed: C1.1, D1.2 (A), D2.1 (K), U301.1
unnamed: D1.1 (K), R305.1, R308.2, U301.2 (-)
unnamed: C1.2, D2.2 (A), R308.1, R312.2
unnamed: D4.2 (A), Q301.1 (E), R301.1
unnamed: J1.1 (In), R201.2
unnamed: JP1.2 (C), U302.12 (X0)
unnamed: Q301.2 (B), Q301.5 (B), Q301.6 (C), R306.2
unnamed: Q301.4 (E), R310.1, U303.5 (+)
unnamed: R201.1, R309.1, U303.1
unnamed: R302.2, RV2.1
unnamed: R304.1, RV2.3
unnamed: R310.2, R313.1, U301.7
unnamed: R312.1, R313.2, U301.6 (-)
unnamed: U302.3 (Z1), U302.14 (X)
unnamed: U302.4 (Z), U303.3 (+)
unnamed: C202.1, R309.2, R311.2, U303.2 (-)
burst: JP1.1 (A); also elsewhere on the board
genlock_delayed: JP1.3 (B); also elsewhere on the board
hsync: U302.9 (C); also elsewhere on the board
porch: U302.11 (A); also elsewhere on the board

Notes on the sheet:
CLIPPER
RESYNCER

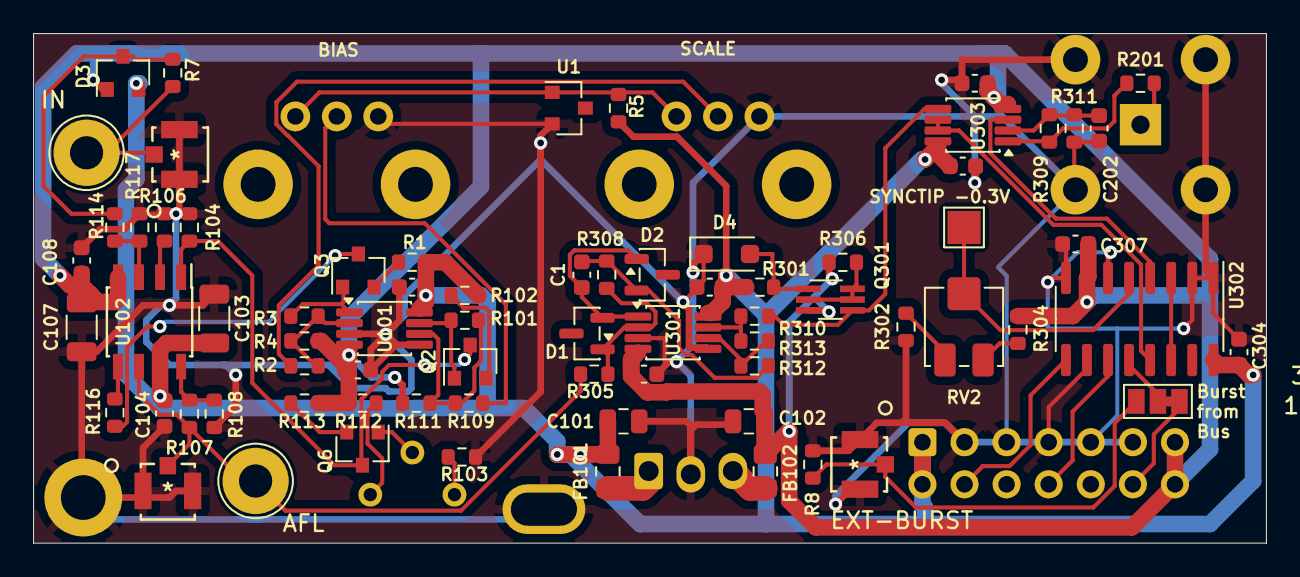
[picture p166: board sk003-output.kicad_pcb from above]

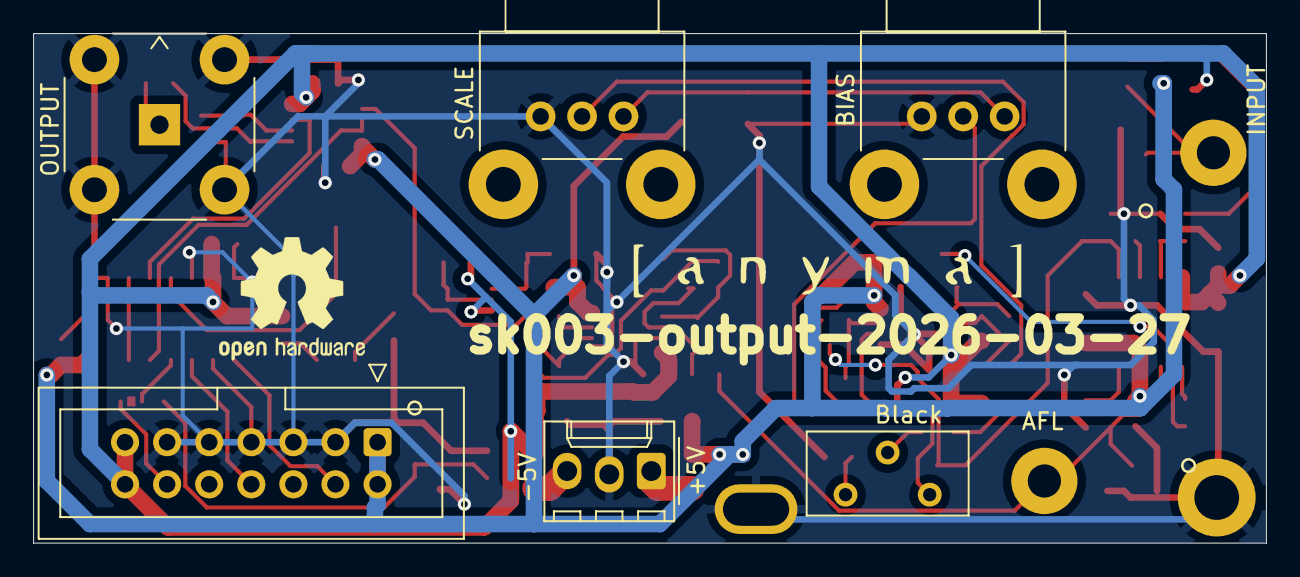
[picture p167: board sk003-output.kicad_pcb from below]

Board: 2 copper layers, 74.4 x 30.8 mm, 83 parts (8 on the bottom side), 49 nets.
