mirdej/synkie/kicad/sk050-triple-lfo/sk050-triple-lfo.kicad_pcb

## KiCad design kicad/sk050-triple-lfo/sk050-triple-lfo.kicad_pcb (2026-03-26)

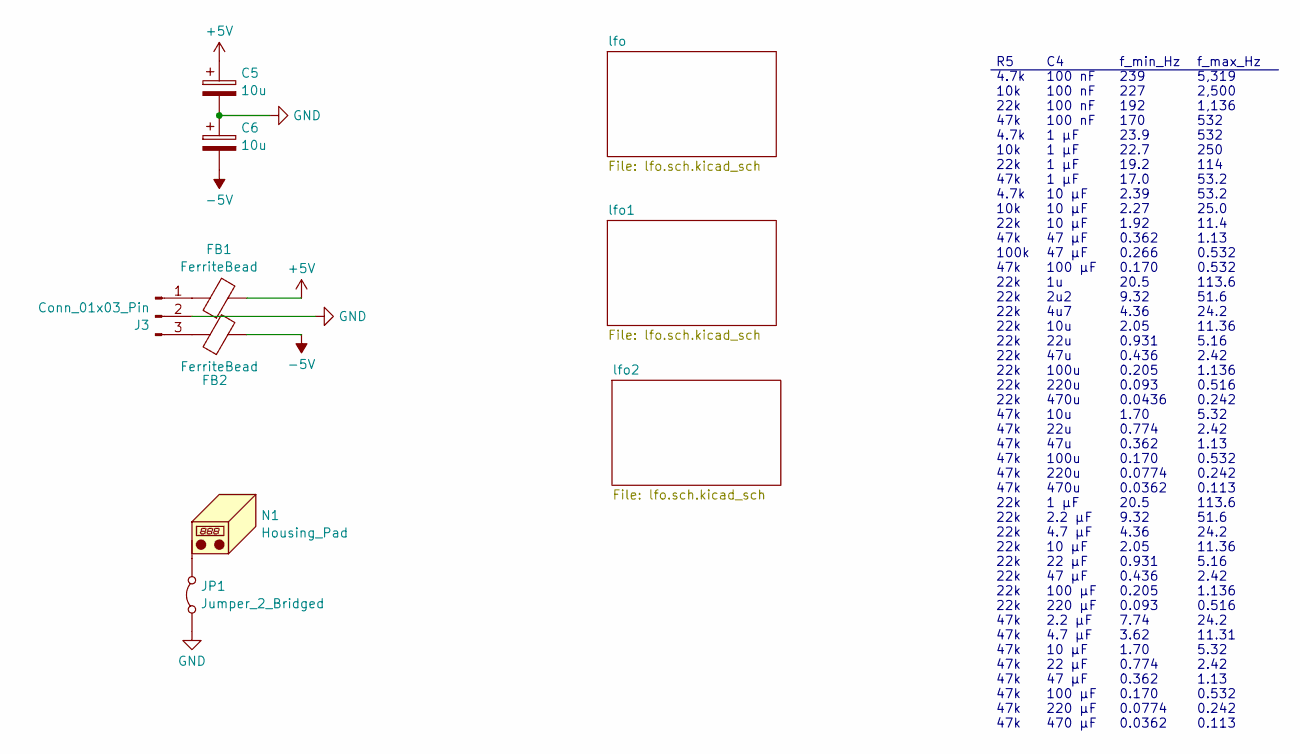
[picture p168: schematic sk050-triple-lfo.kicad_sch]

Parts:
C5, C6: 10u; C_0805_2012Metric; LCSC C15850
FB1, FB2: FerriteBead; L_0805_2012Metric_Pad1.15x1.40mm_HandSolder; LCSC C1017
J3: Conn_01x03_Pin; Molex_KK-254_AE-6410-03A_1x03_P2.54mm_Vertical_SMD
JP1: Jumper_2_Bridged; SolderJumper-2_P1.3mm_Bridged2Bar_Pad1.0x1.5mm
N1: Housing_Pad; Frontplate_20mm

Connections:
+5V: C5.1, FB1.2; also elsewhere on the board
-5V: C6.2, FB2.2; also elsewhere on the board
GND: C5.2, C6.1, J3.2, JP1.1 (A); also elsewhere on the board
unnamed: FB1.1, J3.1
unnamed: FB2.1, J3.3
unnamed: JP1.2 (B), N1.1 (PAD)

Notes on the sheet:
R5 4.7k 10k 22k 47k 4.7k 10k 22k 47k 4.7k 10k 22k 47k 100k 47k 22k 22k 22k 22k 22k 22k 22k 22k 22k 47k 47k 47k 47k 47k 47k 22k 22k 22k 22k 22k 22k 22k 22k 47k 47k 47k 47k 47k 47k 47k 47k
f_max_Hz 5,319 2,500 1,136 532 532 250 114 53.2 53.2 25.0 11.4 1.13 0.532 0.532 113.6 51.6 24.2 11.36 5.16 2.42 1.136 0.516 0.242 5.32 2.42 1.13 0.532 0.242 0.113 113.6 51.6 24.2 11.36 5.16 2.42 1.136 0.516 24.2 11.31 5.32 2.42 1.13 0.532 0.242 0.113
f_min_Hz 239 227 192 170 23.9 22.7 19.2 17.0 2.39 2.27 1.92 0.362 0.266 0.170 20.5 9.32 4.36 2.05 0.931 0.436 0.205 0.093 0.0436 1.70 0.774 0.362 0.170 0.0774 0.0362 20.5 9.32 4.36 2.05 0.931 0.436 0.205 0.093 7.74 3.62 1.70 0.774 0.362 0.170 0.0774 0.0362
C4 100 nF 100 nF 100 nF 100 nF 1 µF 1 µF 1 µF 1 µF 10 µF 10 µF 10 µF 47 µF 47 µF 100 µF 1u 2u2 4u7 10u 22u 47u 100u 220u 470u 10u 22u 47u 100u 220u 470u 1 µF 2.2 µF 4.7 µF 10 µF 22 µF 47 µF 100 µF 220 µF 2.2 µF 4.7 µF 10 µF 22 µF 47 µF 100 µF 220 µF 470 µF
