mirdej/synkie/kicad/sk050-triple-lfo/sk050-triple-lfo.kicad_pcb

## KiCad design kicad/sk050-triple-lfo/sk050-triple-lfo.kicad_pcb (continued)

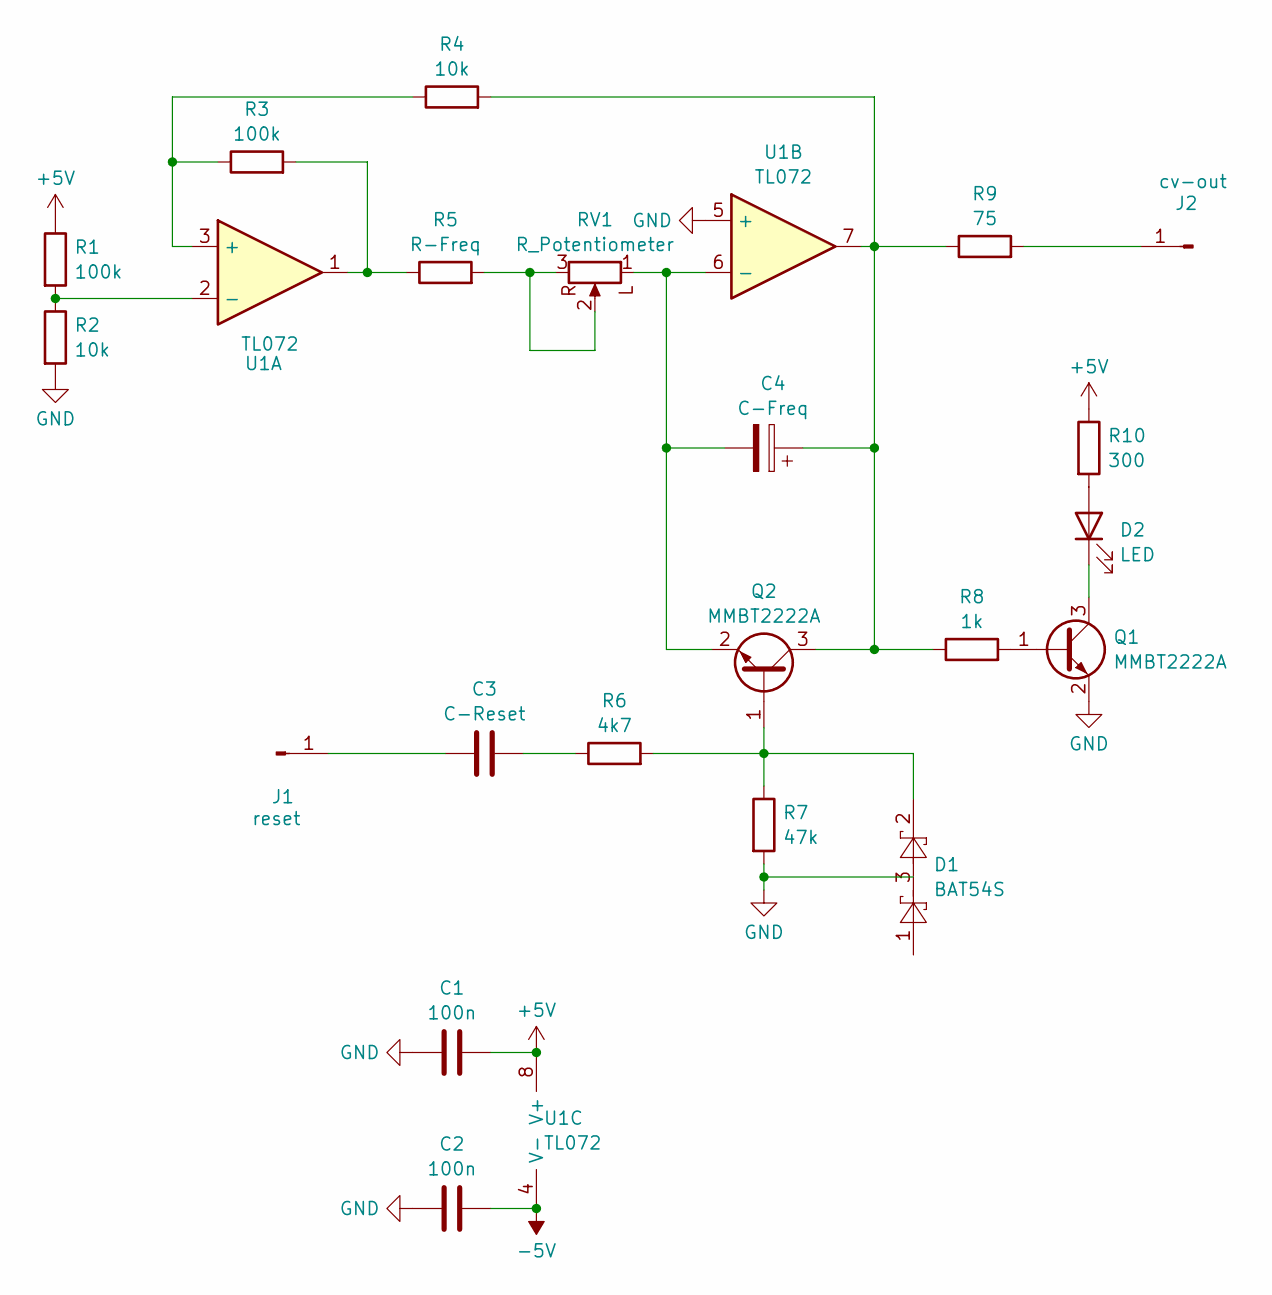
[picture p169: schematic lfo.sch.kicad_sch]

Parts:
C1, C2: 100n; C_0603_1608Metric; LCSC C14663
C3: C-Reset; C-Universal-0603-3528
C4: C-Freq; C-Universal-0603-3528
D1: BAT54S; SOT-23; LCSC C8592
D2: LED; LED_1206_3216Metric_ReverseMount_Hole1.8x2.4mm; LCSC C125108
J1: reset; Banana2mm-Löthülse
J2: cv-out; Banana2mm-Löthülse
Q1, Q2: MMBT2222A; SOT-23; LCSC C82460
R1, R3: 100k; R_0603_1608Metric; LCSC C25803
R2, R4: 10k; R_0603_1608Metric; LCSC C25804
R5: R-Freq; R_0805_2012Metric_Pad1.15x1.40mm_HandSolder
R6: 4k7; R_0603_1608Metric; LCSC C23162
R7: 47k; R_0603_1608Metric; LCSC C25819
R8: 1k; R_0603_1608Metric; LCSC C21190
R9: 75; R_0603_1608Metric; LCSC C4275
R10: 300; R_0603_1608Metric; LCSC C23025
RV1: R_Potentiometer; Potentiometer_Uwe_100k_frontplate
U1: TL072; SOIC-8_3.9x4.9mm_P1.27mm; LCSC C6961

Connections:
+5V: C1.2, R1.1, R10.1, U1.8 (V+); also elsewhere on the board
-5V: C2.2, U1.4 (V-); also elsewhere on the board
GND: C1.1, C2.1, D1.3, Q1.2 (E), R2.2, R7.2, U1.5 (+); also elsewhere on the board
unnamed: C3.1, R6.1
unnamed: D2.2 (A), R10.2
unnamed: D2.1 (K), Q1.3 (C)
unnamed: C3.2, J1.1
unnamed: J2.1, R9.2
unnamed: Q1.1 (B), R8.2
unnamed: D1.2, Q2.1 (B), R6.2, R7.1
unnamed: C4.1, Q2.3 (C), R4.2, R8.1, R9.1, U1.7
unnamed: C4.2, Q2.2 (E), RV1.1 (L), U1.6 (-)
unnamed: R3.2, R5.1, U1.1
unnamed: R5.2, RV1.2, RV1.3
unnamed: R3.1, R4.1, U1.3 (+)
unnamed: R1.2, R2.1, U1.2 (-)

Parts of its further copies:
C7, C8, C11, C12: 100n; C_0603_1608Metric; LCSC C14663
C9, C13: C-Reset; C-Universal-0603-3528
C10, C14: C-Freq; C-Universal-0603-3528
D3, D5: BAT54S; SOT-23; LCSC C8592
D4, D6: LED; LED_1206_3216Metric_ReverseMount_Hole1.8x2.4mm; LCSC C125108
J4, J6: reset; Banana2mm-Löthülse
J5, J7: cv-out; Banana2mm-Löthülse
Q3, Q4, Q5, Q6: MMBT2222A; SOT-23; LCSC C82460
R11, R13, R21, R23: 100k; R_0603_1608Metric; LCSC C25803
R12, R15, R22, R25: 10k; R_0603_1608Metric; LCSC C25804
R14, R24: R-Freq; R_0805_2012Metric_Pad1.15x1.40mm_HandSolder
R16, R26: 4k7; R_0603_1608Metric; LCSC C23162
R17, R27: 47k; R_0603_1608Metric; LCSC C25819
R18, R28: 1k; R_0603_1608Metric; LCSC C21190
R19, R29: 75; R_0603_1608Metric; LCSC C4275
R20, R30: 300; R_0603_1608Metric; LCSC C23025
RV2, RV3: R_Potentiometer; Potentiometer_Uwe_100k_frontplate
U2, U3: TL072; SOIC-8_3.9x4.9mm_P1.27mm; LCSC C6961

Connections of its further copies:
+5V: C7.2, C11.2, R11.1, R20.1, R21.1, R30.1, U2.8 (V+), U3.8 (V+); also elsewhere on the board
-5V: C8.2, C12.2, U2.4 (V-), U3.4 (V-); also elsewhere on the board
GND: C7.1, C8.1, C11.1, C12.1, D3.3, D5.3, Q4.2 (E), Q6.2 (E), R12.2, R17.2, R22.2, R27.2, U2.5 (+), U3.5 (+); also elsewhere on the board
unnamed: C9.1, R16.1
unnamed: C13.1, R26.1
unnamed: D4.2 (A), R20.2
unnamed: D4.1 (K), Q4.3 (C)
unnamed: D6.2 (A), R30.2
unnamed: D6.1 (K), Q6.3 (C)
unnamed: C9.2, J4.1
unnamed: J5.1, R19.2
unnamed: C13.2, J6.1
unnamed: J7.1, R29.2
unnamed: D3.2, Q3.1 (B), R16.2, R17.1
unnamed: C10.1, Q3.3 (C), R15.2, R18.1, R19.1, U2.7
unnamed: C10.2, Q3.2 (E), RV2.1 (L), U2.6 (-)
unnamed: Q4.1 (B), R18.2
unnamed: D5.2, Q5.1 (B), R26.2, R27.1
unnamed: C14.1, Q5.3 (C), R25.2, R28.1, R29.1, U3.7
unnamed: C14.2, Q5.2 (E), RV3.1 (L), U3.6 (-)
unnamed: Q6.1 (B), R28.2
unnamed: R13.2, R14.1, U2.1
unnamed: R14.2, RV2.2, RV2.3
unnamed: R23.2, R24.1, U3.1
unnamed: R24.2, RV3.2, RV3.3
unnamed: R13.1, R15.1, U2.3 (+)
unnamed: R11.2, R12.1, U2.2 (-)
unnamed: R23.1, R25.1, U3.3 (+)
unnamed: R21.2, R22.1, U3.2 (-)

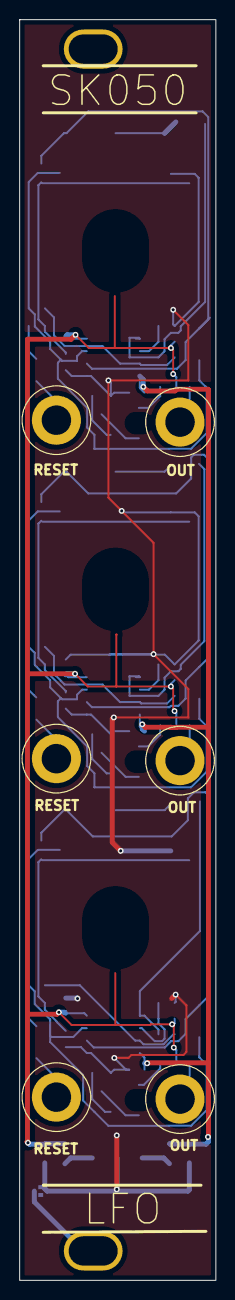
[picture p170: board sk050-triple-lfo.kicad_pcb from above]

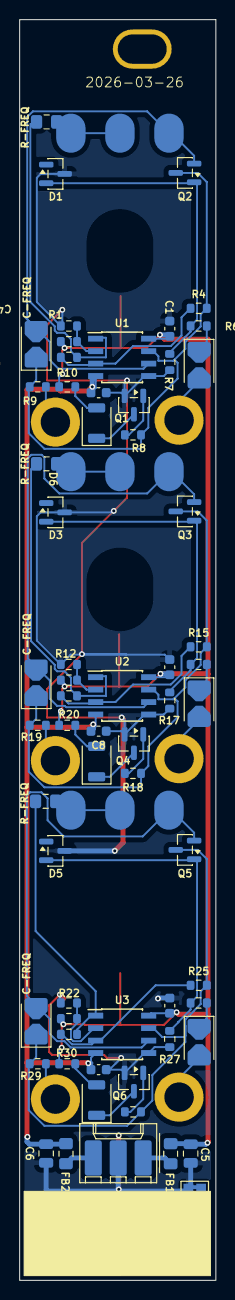
[picture p171: board sk050-triple-lfo.kicad_pcb from below]

Board: 2 copper layers, 20.0 x 128.5 mm, 73 parts (63 on the bottom side), 45 nets.
