mirdej/synkie/kicad/sk542-samplehold/sk542-samplehold.kicad_pcb

## KiCad design kicad/sk542-samplehold/sk542-samplehold.kicad_pcb (2026-03-26)

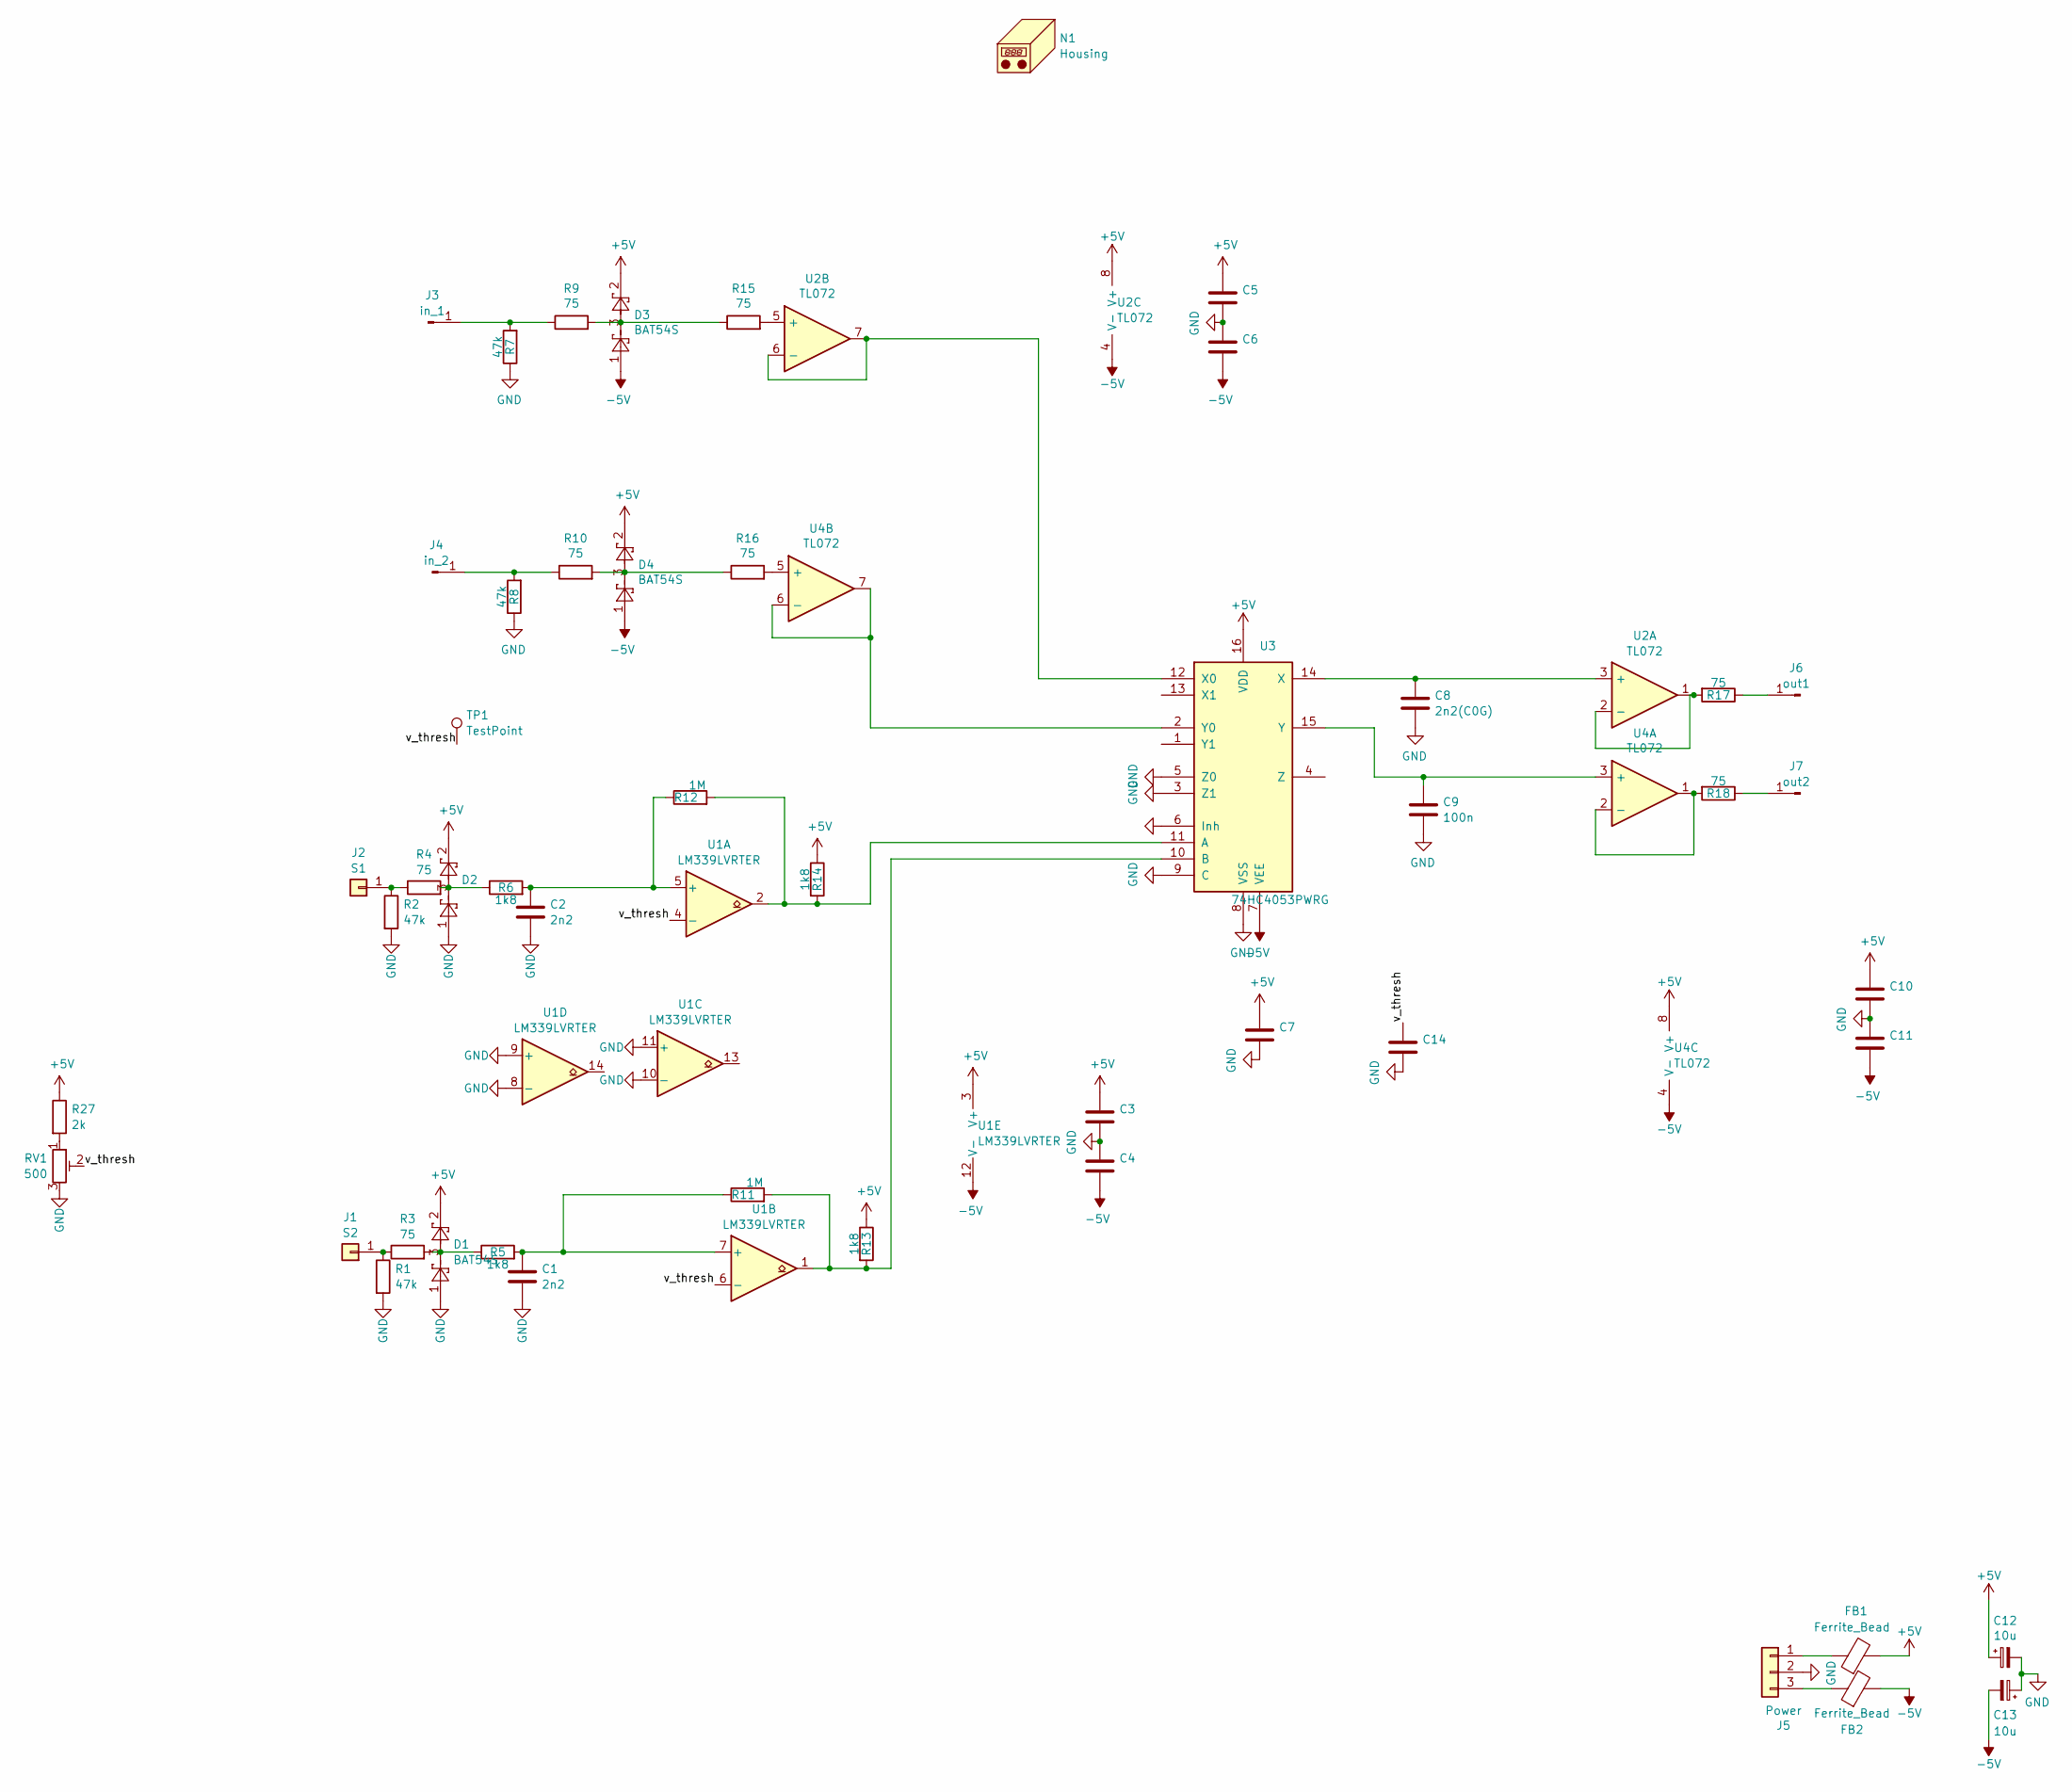
[picture p172: schematic sk542-samplehold.kicad_sch]

Parts:
C1, C2: 2n2; C_0603_1608Metric; LCSC C1604
C3, C4, C5, C6, C7, C9, C10, C11, C14: 100n; C_0603_1608Metric; LCSC C14663
C8: 2n2(C0G); C_0805_2012Metric; LCSC C28260
C12, C13: 10u; C_0805_2012Metric; LCSC C15850
D1, D2, D3, D4: BAT54S; SOT-23; LCSC C8592
FB1, FB2: Ferrite_Bead; L_0805_2012Metric; LCSC C1017
J1: S2; Banana2mm-Löthülse
J2: S1; Banana2mm-Löthülse
J3: in_1; Banana2mm-Löthülse
J4: in_2; Banana2mm-Löthülse
J5: Power; Molex_KK-254_AE-6410-03A_1x03_P2.54mm_Vertical_SMD
J6: out1; Banana2mm-Löthülse
J7: out2; Banana2mm-Löthülse
N1: Housing; Frontplate_10mm
R1, R2, R7, R8: 47k; R_0603_1608Metric; LCSC C25819
R3, R4, R9, R10, R15, R16, R17, R18: 75; R_0603_1608Metric; LCSC C4275
R5, R6, R13, R14: 1k8; R_0603_1608Metric; LCSC C4177
R11, R12: 1M; R_0603_1608Metric; LCSC C22935
R27: 2k; R_0805_2012Metric_Pad1.15x1.40mm_HandSolder; LCSC C17604
RV1: 500; Potentiometer_Bourns_3314J_Vertical; LCSC C123873
TP1: TestPoint; TestPoint_Pad_2.5x2.5mm
U1: LM339LVRTER; WQFN-16-1EP_3x3mm_P0.5mm_EP1.6x1.6mm; LCSC C3658606
U2, U4: TL072; SO-8_3.9x4.9mm_P1.27mm; LCSC C6961
U3: 74HC4053PWRG; TSSOP-16_4.4x5mm_P0.65mm; LCSC C19723809

Connections:
+5V: C3.1, C5.1, C7.1, C10.1, C12.1, D1.2, D2.2, D3.2, D4.2, FB1.2, R13.1, R14.1, R27.1, U1.3 (V+), U2.8 (V+), U3.16 (VDD), U4.8 (V+)
-5V: C4.2, C6.2, C11.2, C13.2, D3.1, D4.1, FB2.2, U1.12 (V-), U2.4 (V-), U3.7 (VEE), U4.4 (V-)
/v_thresh: C14.1, RV1.2, TP1.1, U1.4 (-), U1.6 (-)
GND: C1.2, C2.2, C3.2, C4.1, C5.2, C6.1, C7.2, C8.2, C9.1, C10.2, C11.1, C12.2, C13.1, C14.2, D1.1, D2.1, J5.2, R1.2, R2.2, R7.1, R8.1, RV1.3, U1.8 (-), U1.9 (+), U1.10 (-), U1.11 (+), U3.3 (Z1), U3.5 (Z0), U3.6 (Inh), U3.8 (VSS), U3.9 (C)
unnamed: D1.3, R3.2, R5.1
unnamed: D2.3, R4.2, R6.1
unnamed: D3.3, R9.2, R15.1
unnamed: D4.3, R10.2, R16.1
unnamed: J1.1, R1.1, R3.1
unnamed: J2.1, R2.1, R4.1
unnamed: J3.1, R7.2, R9.1
unnamed: J4.1, R8.2, R10.1
unnamed: FB1.1, J5.1
unnamed: FB2.1, J5.3
unnamed: J6.1, R17.1
unnamed: J7.1, R18.1
unnamed: R27.2, RV1.1
unnamed: C2.1, R6.2, R12.1, U1.5 (+)
unnamed: C1.1, R5.2, R11.1, U1.7 (+)
unnamed: C8.1, U2.3 (+), U3.14 (X)
unnamed: R17.2, U2.1, U2.2 (-)
unnamed: R15.2, U2.5 (+)
unnamed: U2.6 (-), U2.7, U3.12 (X0)
unnamed: R12.2, R14.2, U1.2, U3.11 (A)
unnamed: R11.2, R13.2, U1.1, U3.10 (B)
unnamed: U3.2 (Y0), U4.6 (-), U4.7
unnamed: C9.2, U3.15 (Y), U4.3 (+)
unnamed: R18.2, U4.1, U4.2 (-)
unnamed: R16.2, U4.5 (+)

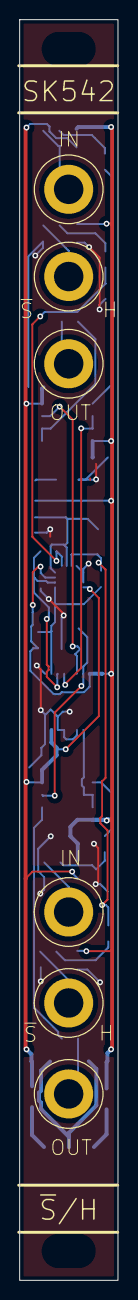
[picture p173: board sk542-samplehold.kicad_pcb from above]

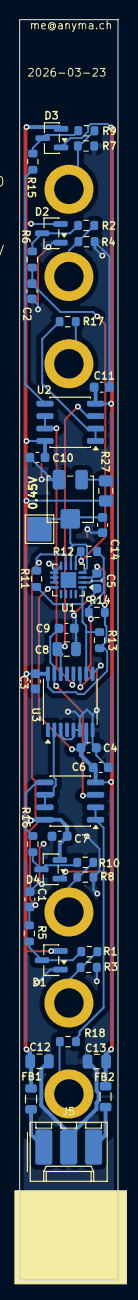
[picture p174: board sk542-samplehold.kicad_pcb from below]

Board: 2 copper layers, 10.0 x 128.5 mm, 53 parts (46 on the bottom side), 29 nets.
