mirdej/synkie/eagle/sk910-waveshape/sk910-waveshape.brd

## EAGLE design eagle/sk910-waveshape/sk910-waveshape.brd (2018-03-19)

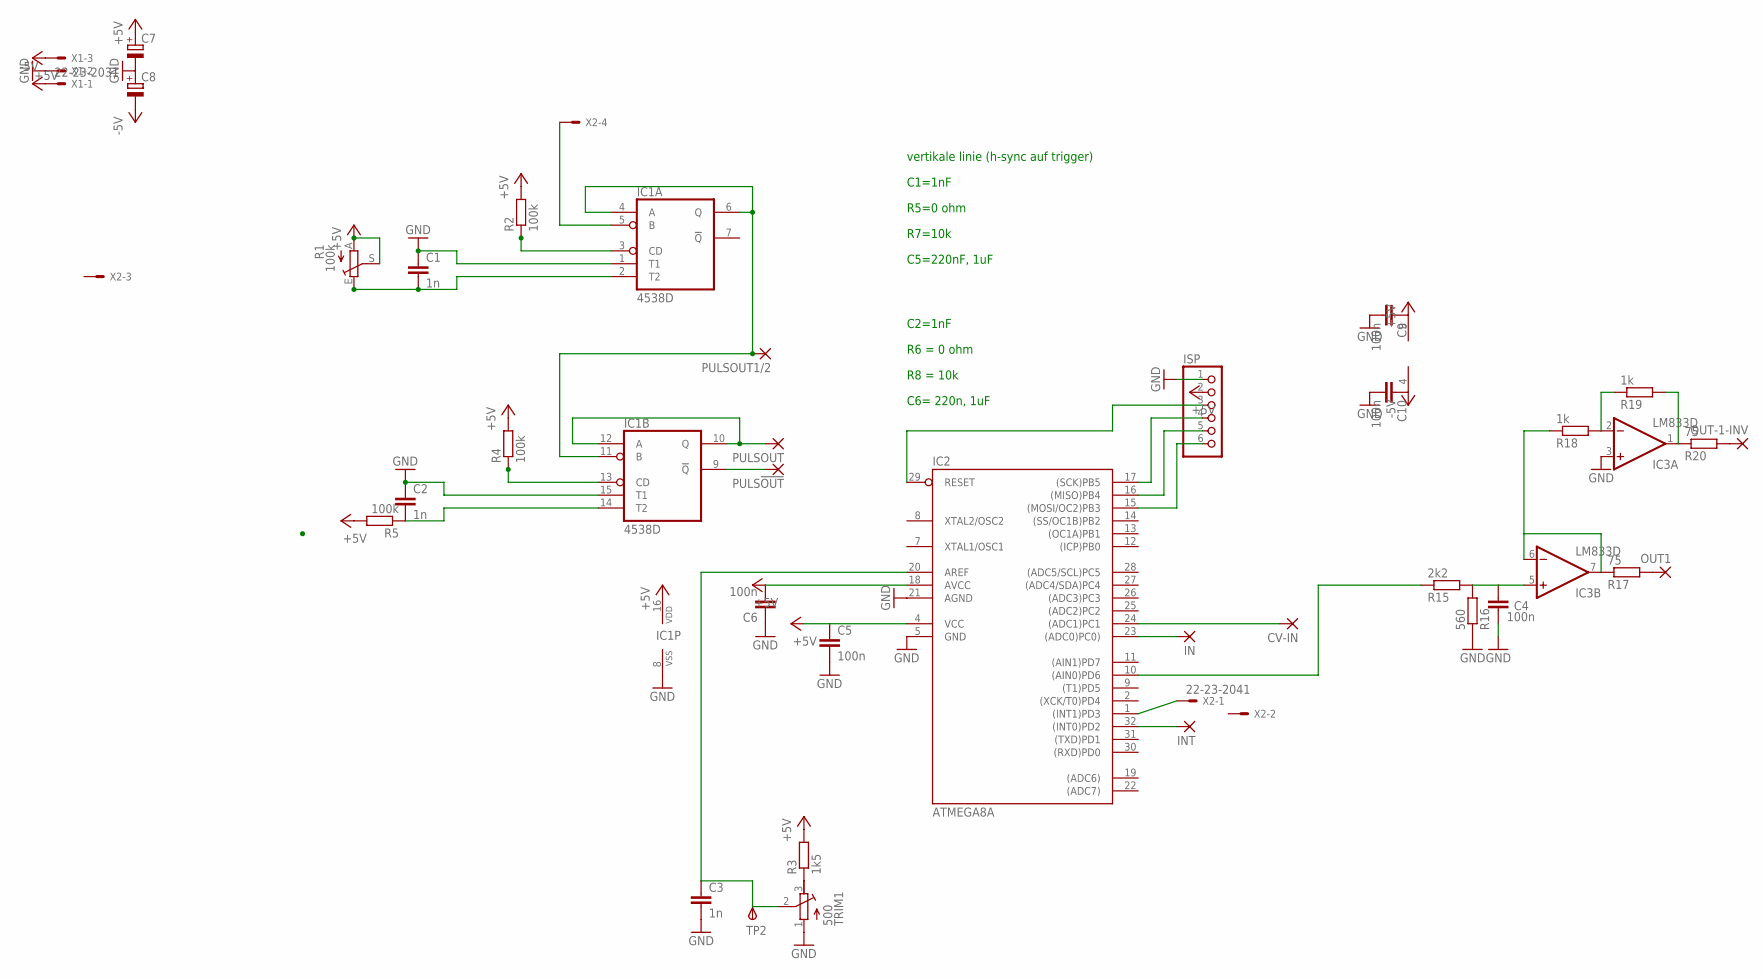
[picture p206: schematic sk910-waveshape.sch]

Parts:
C1, C2, C3: 1n; C1206
C4: 100n; C0805
C5: 100n; C1206
C6, C9, C10: 100n; C0603
C7, C8: CPOL-EUCT6032; CT6032
CV-IN: 3,17/1,1
IC1: 4538D; SO16
IC2: ATMEGA8A; TQFP32-08
IC3: LM833D; SO08
IN: 3,17/1,1
INT: 3,17/1,1
ISP: PINHD-1X6; 1X06
OUT1: 3,17/1,1
OUT-1-INV: 3,17/1,1
PULS!OUT: 3,17/1,1
PULSOUT, PULSOUT1/2: 3,17/1,1
R1: 100k; CIP20C-6MM
R2, R4, R5: 100k; R1206
R3: 1k5; R1206
R15: 2k2; R1206
R16: 560; R1206
R17, R20: 75; R1206
R18, R19: 1k; R1206
TP2: TPSPAD1-13; P1-13
TRIM1: 500; RTRIM64Y
X1: 22-23-2031
X2: 22-23-2041

Connections:
+5V: C2.2, C5.1, C6.2, C7.+, C9.1, IC1.14 (T2), IC1.16 (VDD), IC2.4 (VCC), IC2.18 (AVCC), IC3.8 (V+), ISP.2, R1.A, R1.S, R2.2, R3.2, R4.2, R5.1, R5.2, X1.3
-5V: C8.-, C10.1, IC3.4 (V-), X1.1
GND: C1.1, C2.1, C3.2, C4.2, C5.2, C6.1, C7.-, C8.+, C9.2, C10.2, IC1.1 (T1), IC1.8 (VSS), IC1.15 (T1), IC2.5 (GND), IC2.21 (AGND), IC3.3 (+IN), ISP.1, R16.1, TRIM1.1 (E), X1.2
unnamed: IC1.3 (CD), R2.1
unnamed: IC2.32 ((INT0)PD2), INT.1
unnamed: IC1.10 (Q), IC1.12 (A), PULSOUT.1
unnamed: IC1.4 (A), IC1.6 (Q), IC1.11 (B), PULSOUT1/2.1
unnamed: IC2.23 ((ADC0)PC0)), IN.1
unnamed: C1.2, IC1.2 (T2), R1.E
unnamed: IC2.1 ((INT1)PD3), X2.1
unnamed: R3.1, TRIM1.3 (A)
unnamed: CV-IN.1, IC2.24 ((ADC1)PC1)
unnamed: IC2.29 (RESET), ISP.3
unnamed: IC2.17 ((SCK)PB5), ISP.4
unnamed: IC1.13 (CD), R4.1
unnamed: IC1.9 (!Q), PULS!OUT.1
unnamed: IC2.16 ((MISO)PB4), ISP.5
unnamed: IC2.15 ((MOSI/OC2)PB3), ISP.6
unnamed: IC1.5 (B), X2.4
unnamed: IC2.10 ((AIN0)PD6), R15.1
unnamed: C4.1, IC3.5 (+IN), R15.2, R16.2
unnamed: IC3.6 (-IN), IC3.7 (OUT), R17.1, R18.1
unnamed: IC3.2 (-IN), R18.2, R19.1
unnamed: OUT-1-INV.1, R20.2
unnamed: OUT1.1, R17.2
unnamed: IC3.1 (OUT), R19.2, R20.1
unnamed: C3.1, IC2.20 (AREF), TP2.TP, TRIM1.2 (S)

Notes on the sheet:
vertikale linie (h-sync auf trigger)
C1=1nF
R5=0 ohm
R7=10k
C5=220nF, 1uF
C2=1nF
R6 = 0 ohm
R8 = 10k
C6= 220n, 1uF

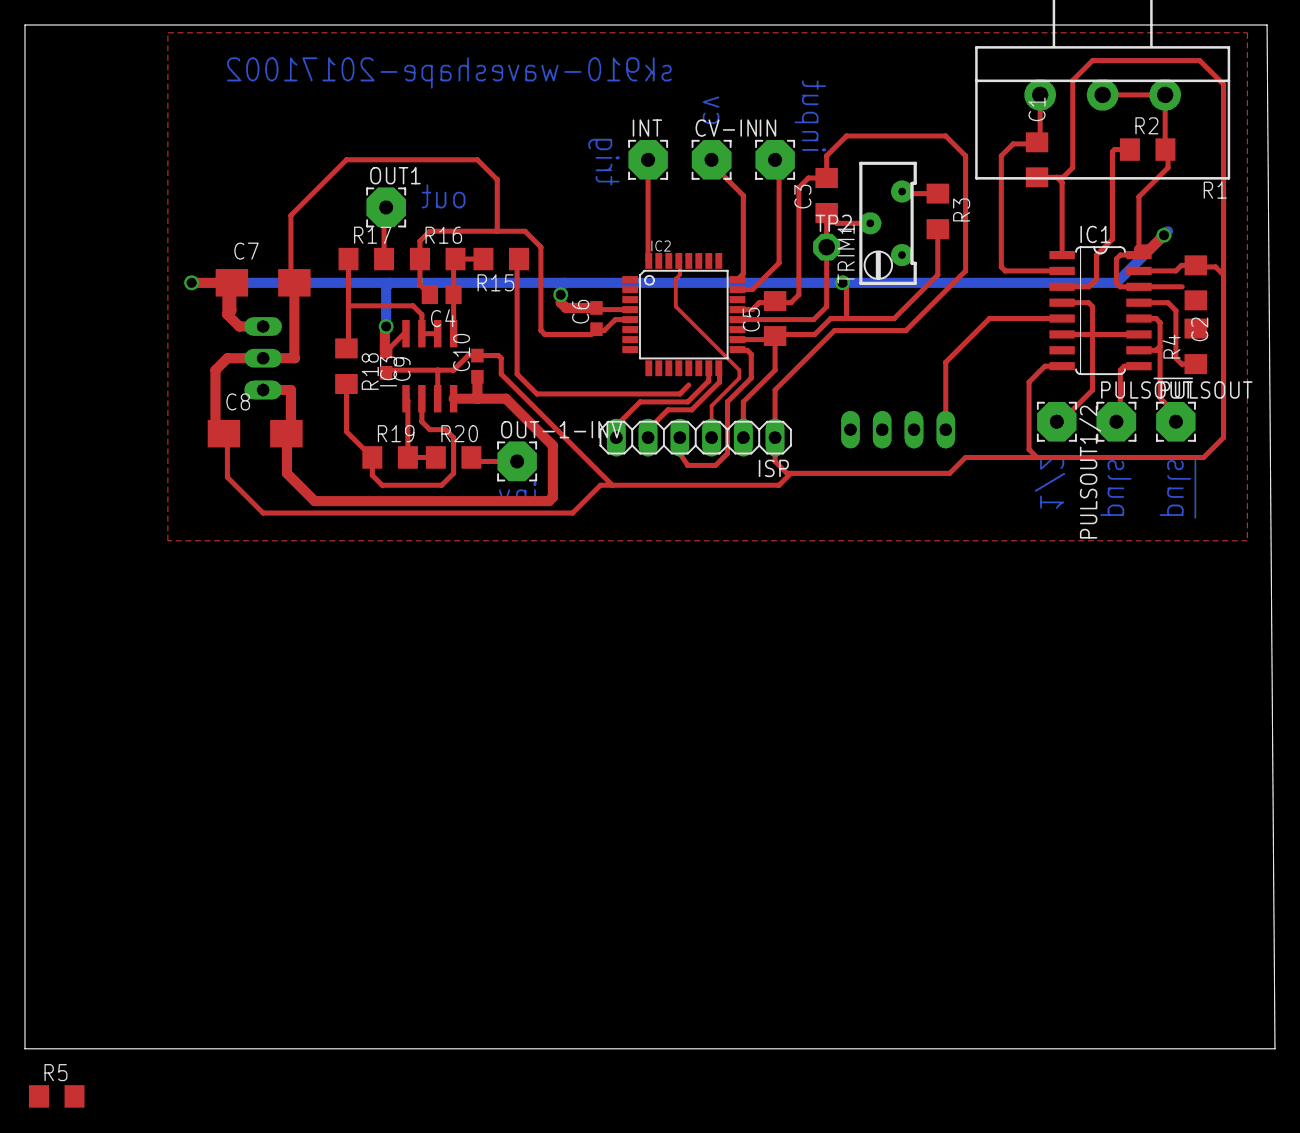
[picture p207: board sk910-waveshape.brd from above]

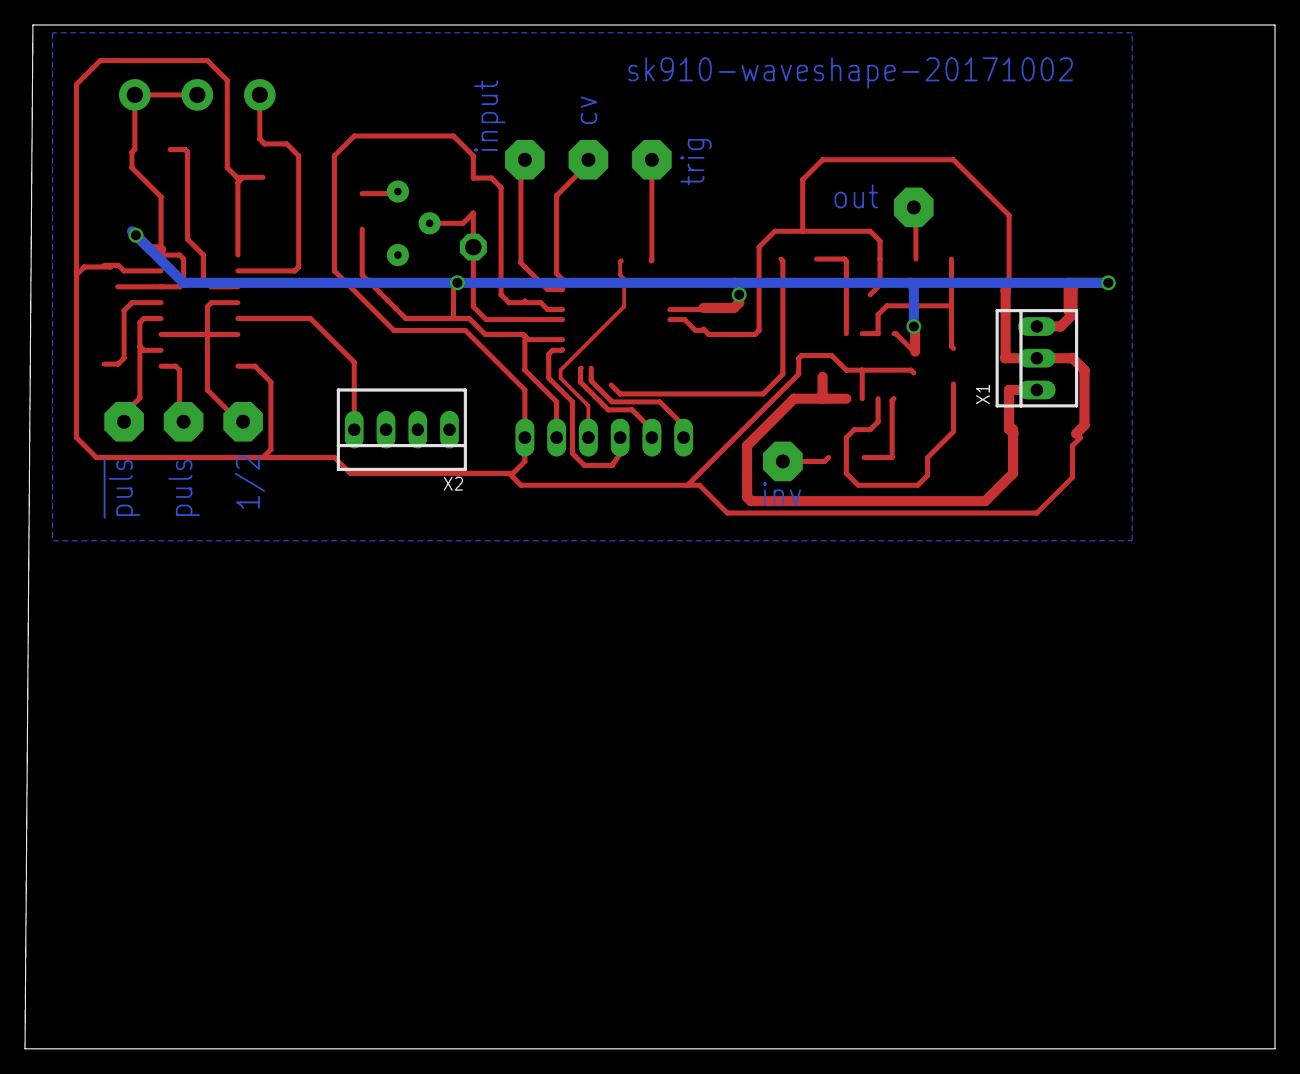
[picture p208: board sk910-waveshape.brd from below]

Board: 2 copper layers, 100.0 x 81.9 mm, 37 parts (2 on the bottom side), 27 nets.
