mirdej/synkie/eagle/sk240-chromafun/sk240-chromafun.brd

## EAGLE design eagle/sk240-chromafun/sk240-chromafun.brd (2018-03-19)

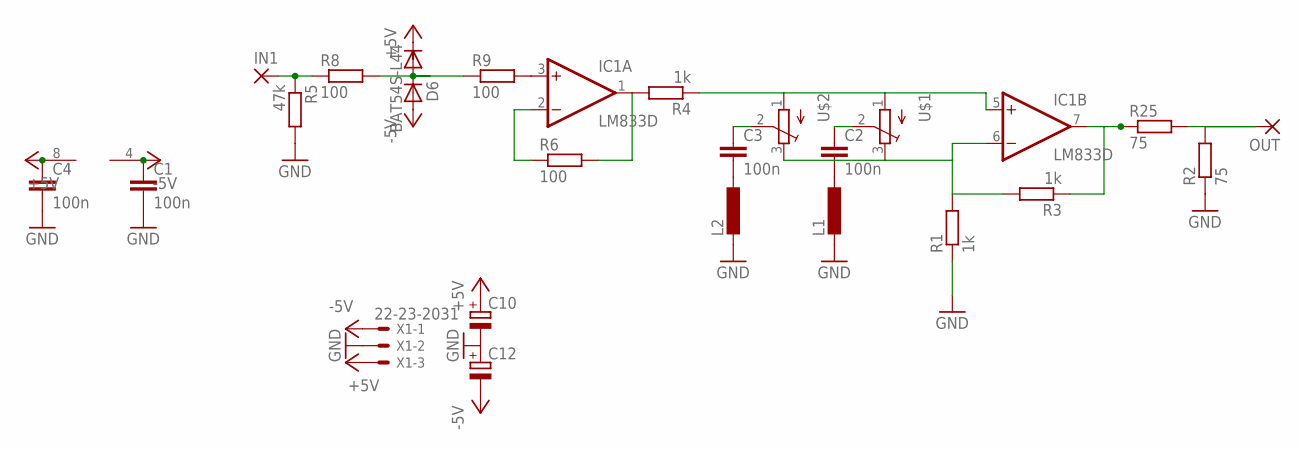
[picture p209: schematic sk240-chromafun.sch]

Parts:
C1, C2, C3, C4: 100n; C0603
C10, C12: CPOL-EUSMCB; SMC_B
D6: BAT54S-L44; SOT23
IC1: LM833D; SO08
IN1: 3,81/1,1
L1, L2: L-EU0207/12; 0207/12
OUT: 3,81/1,1
R1, R3, R4: 1k; R1206
R2, R25: 75; R1206
R5: 47k; R1206
R6, R8, R9: 100; R1206
U$1, U$2: ALPS_RK09K111_HOHNE-FüSSE; ALPS_RK09K111
X1: 22-23-2031

Connections:
+5V: C4.1, C10.+, D6.2 (C), IC1.8 (V+), X1.3
-5V: C1.1, C12.-, D6.1 (A), IC1.4 (V-), X1.1
GND: C1.2, C4.2, C10.-, C12.+, L1.2, L2.2, R1.1, R2.1, R5.2, X1.2
unnamed: IC1.1 (OUT), R4.2, R6.2
unnamed: OUT.1, R2.2, R25.2
unnamed: IC1.3 (+IN), R9.2
unnamed: IC1.7 (OUT), R3.1, R25.1
unnamed: IC1.6 (-IN), R1.2, R3.2, U$1.3 (E), U$2.3 (E)
unnamed: IC1.5 (+IN), R4.1, U$1.1 (S), U$2.1 (S)
unnamed: C2.1, U$1.2 (W)
unnamed: C2.2, L1.1
unnamed: C3.1, U$2.2 (W)
unnamed: C3.2, L2.1
unnamed: IC1.2 (-IN), R6.1
unnamed: IN1.1, R5.1, R8.1
unnamed: D6.3 (AC), R8.2, R9.1

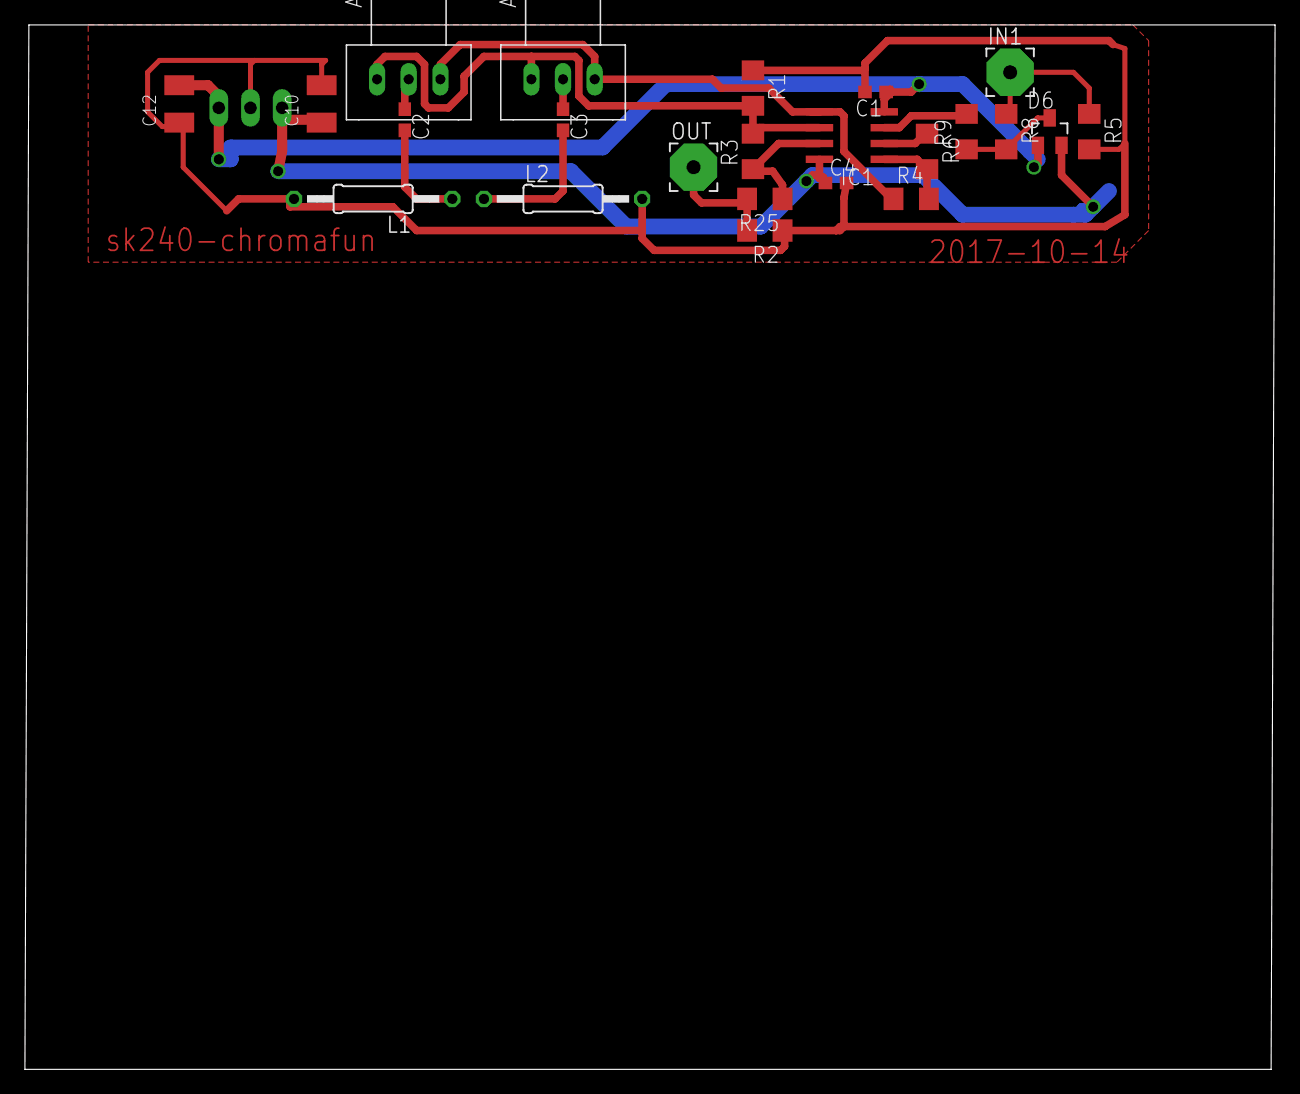
[picture p210: board sk240-chromafun.brd from above]

Board: 2 copper layers, 100.3 x 83.8 mm, 24 parts (1 on the bottom side), 16 nets.
