mirdej/synkie/eagle/sk536-audio-pfft/sk536-fft2cv-supplyAndOutputs2.brd

## EAGLE design eagle/sk536-audio-pfft/sk536-fft2cv-supplyAndOutputs2.brd (2018-03-19)

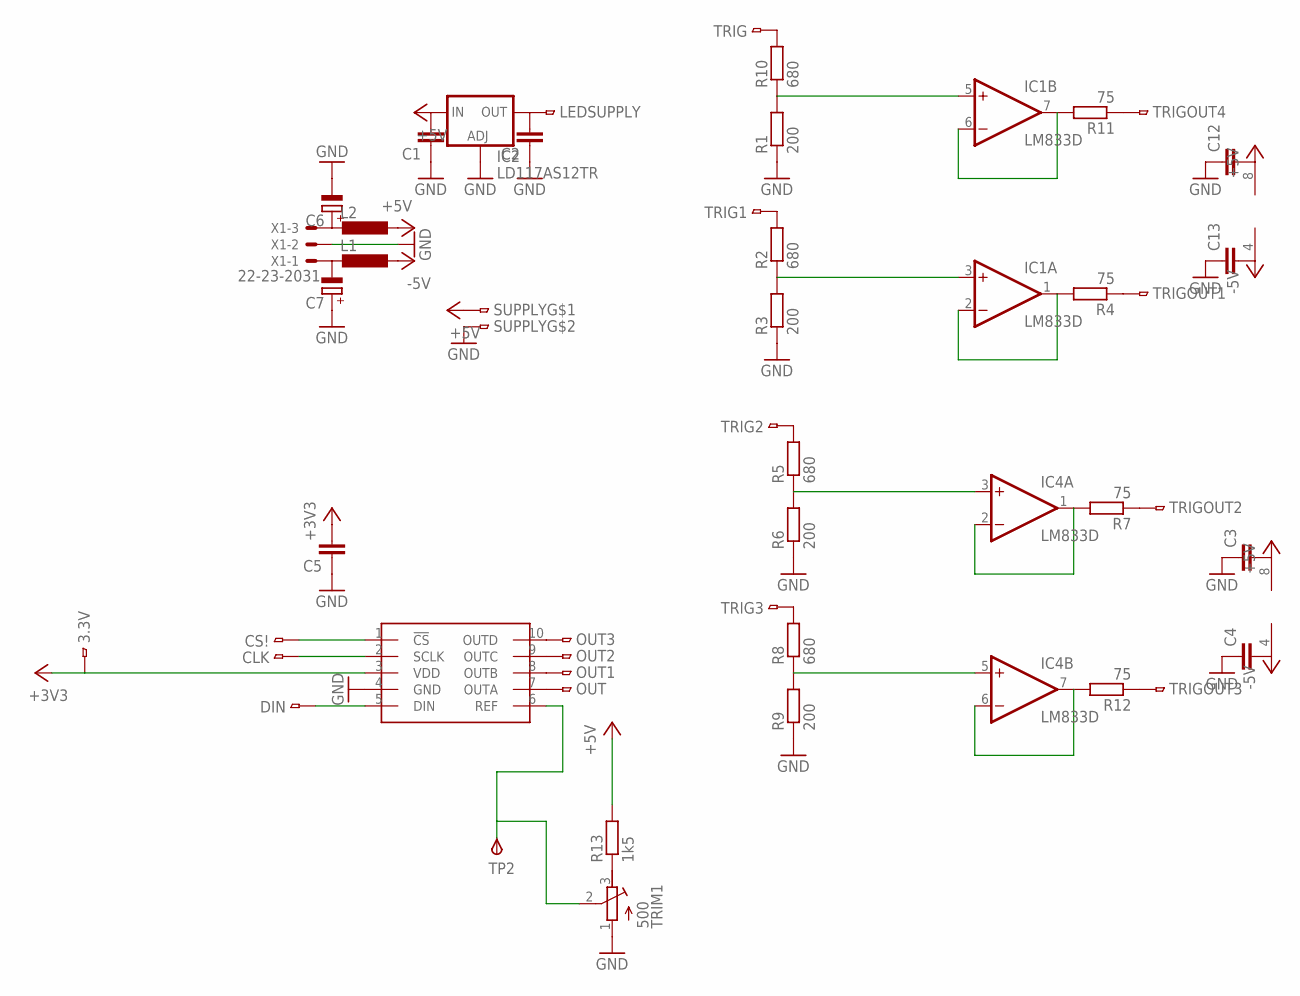
[picture p211: schematic sk536-fft2cv-supplyAndOutputs2.sch]

Parts:
3.3V: 1PINSMDSMALL; 1PINSMD-SMALL
C1, C2, C3, C4, C5, C12, C13: C-EUC0603; C0603
C6, C7: CPOL-EUCT3528; CT3528
CLK: 1PINSMDSMALL; 1PINSMD-SMALL
CS!: 1PINSMDSMALL; 1PINSMD-SMALL
DIN: 1PINSMDSMALL; 1PINSMD-SMALL
IC1, IC4: LM833D; SO08
IC2: LD117AS12TR; SOT223
L1, L2: L-EUL2012C; L2012C
LEDSUPPLY: 1PINSMD
OUT, OUT1, OUT2, OUT3: 1PINSMDSMALL; 1PINSMD-SMALL
R1, R3, R6, R9: 200; R1206
R2, R5, R8, R10: 680; R1206
R4, R7, R11, R12: 75; R1206
R13: 1k5; R1206
SUPPLY: 2PIN-SMD-2.54
TP2: TPSB2,54; B2,54
TRIG, TRIG1, TRIG2, TRIG3: 1PINSMDSMALL; 1PINSMD-SMALL
TRIGOUT1, TRIGOUT2, TRIGOUT3, TRIGOUT4: 1PINSMDSMALL; 1PINSMD-SMALL
TRIM1: 500; RTRIM64Y
U$1: MAX5741; UMAX10
X1: 22-23-2031

Connections:
+3V3: 3.3V.P$1, C5.2, U$1.3 (VDD)
+5V: C1.2, C3.2, C12.2, IC1.8 (V+), IC2.3 (IN), IC4.8 (V+), L2.1, R13.2, SUPPLY.2
-5V: C4.2, C13.2, IC1.4 (V-), IC4.4 (V-), L1.1
GND: C1.1, C2.1, C3.1, C4.1, C5.1, C6.-, C7.+, C12.1, C13.1, IC2.1 (ADJ), R1.1, R3.1, R6.1, R9.1, SUPPLY.3, TRIM1.1 (A), U$1.4 (GND), X1.2
unnamed: R10.2, TRIG.P$1
unnamed: C2.2, IC2.4 (OUT), LEDSUPPLY.2
unnamed: R2.2, TRIG1.P$1
unnamed: IC1.5 (+IN), R1.2, R10.1
unnamed: IC1.6 (-IN), IC1.7 (OUT), R11.2
unnamed: R5.2, TRIG2.P$1
unnamed: R8.2, TRIG3.P$1
unnamed: IC1.3 (+IN), R2.1, R3.2
unnamed: IC1.1 (OUT), IC1.2 (-IN), R4.2
unnamed: R11.1, TRIGOUT4.P$1
unnamed: R4.1, TRIGOUT1.P$1
unnamed: R7.1, TRIGOUT2.P$1
unnamed: IC4.3 (+IN), R5.1, R6.2
unnamed: IC4.1 (OUT), IC4.2 (-IN), R7.2
unnamed: R12.1, TRIGOUT3.P$1
unnamed: OUT.P$1, U$1.7 (OUTA)
unnamed: OUT1.P$1, U$1.8 (OUTB)
unnamed: IC4.5 (+IN), R8.1, R9.2
unnamed: IC4.6 (-IN), IC4.7 (OUT), R12.2
unnamed: OUT2.P$1, U$1.9 (OUTC)
unnamed: OUT3.P$1, U$1.10 (OUTD)
unnamed: DIN.P$1, U$1.5 (DIN)
unnamed: R13.1, TRIM1.3 (E)
unnamed: CLK.P$1, U$1.2 (SCLK)
unnamed: CS!.P$1, U$1.1 (!CS)
unnamed: C7.-, L1.2, X1.1
unnamed: C6.+, L2.2, X1.3
unnamed: TP2.TP, TRIM1.2 (S), U$1.6 (REF)

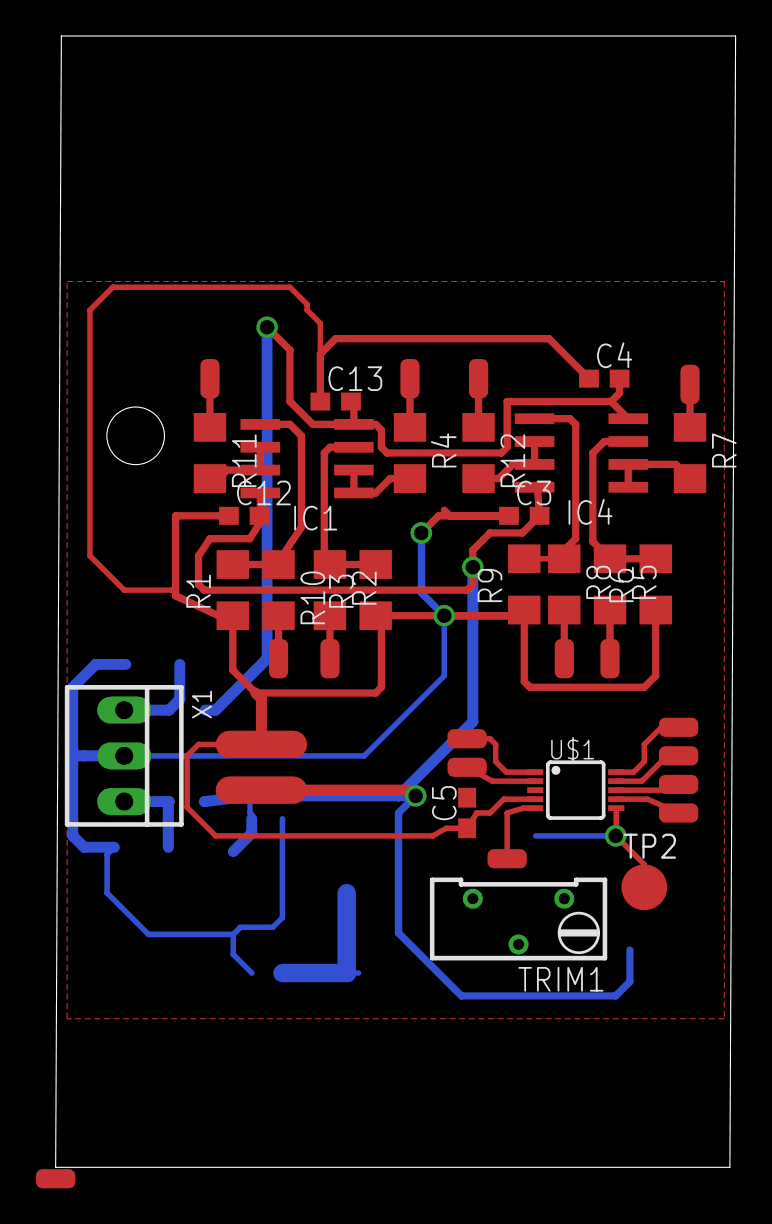
[picture p212: board sk536-fft2cv-supplyAndOutputs2.brd from above]

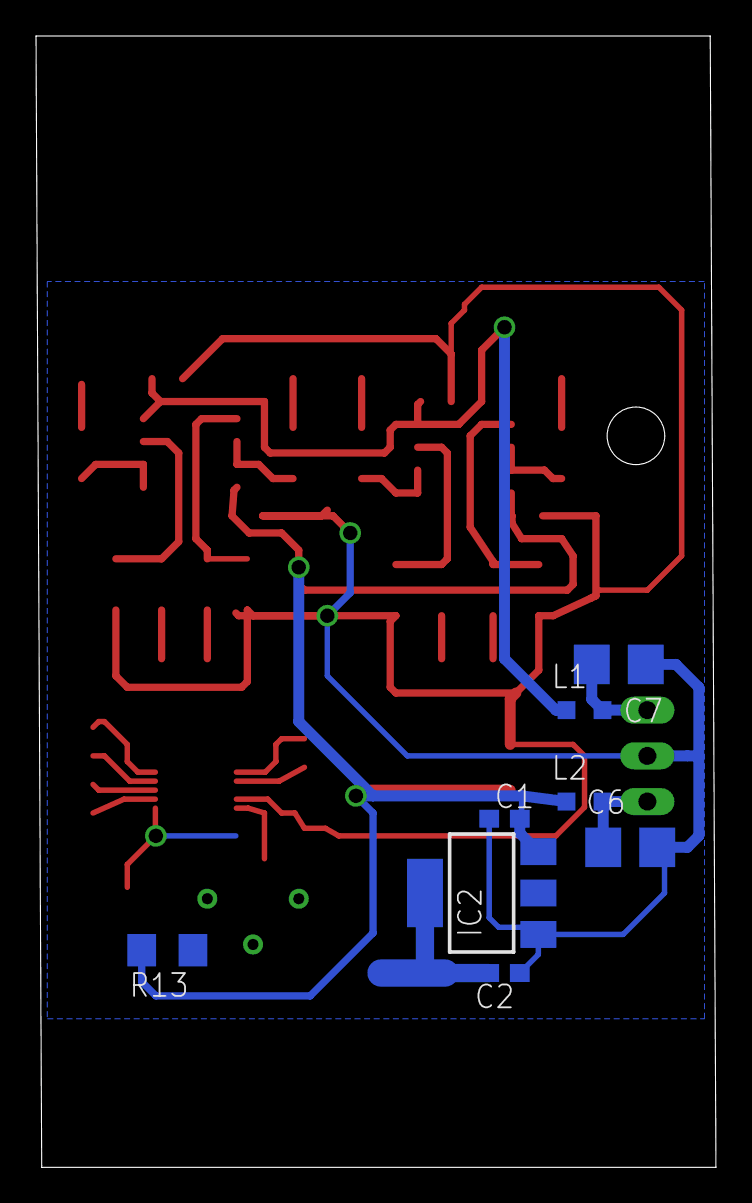
[picture p213: board sk536-fft2cv-supplyAndOutputs2.brd from below]

Board: 2 copper layers, 37.8 x 62.9 mm, 49 parts (9 on the bottom side), 32 nets.
