mirdej/synkie/eagle/sk536-audio-pfft/sk536-fft2cv-supplyAndOutputs.brd

## EAGLE design eagle/sk536-audio-pfft/sk536-fft2cv-supplyAndOutputs.brd (2018-03-19)

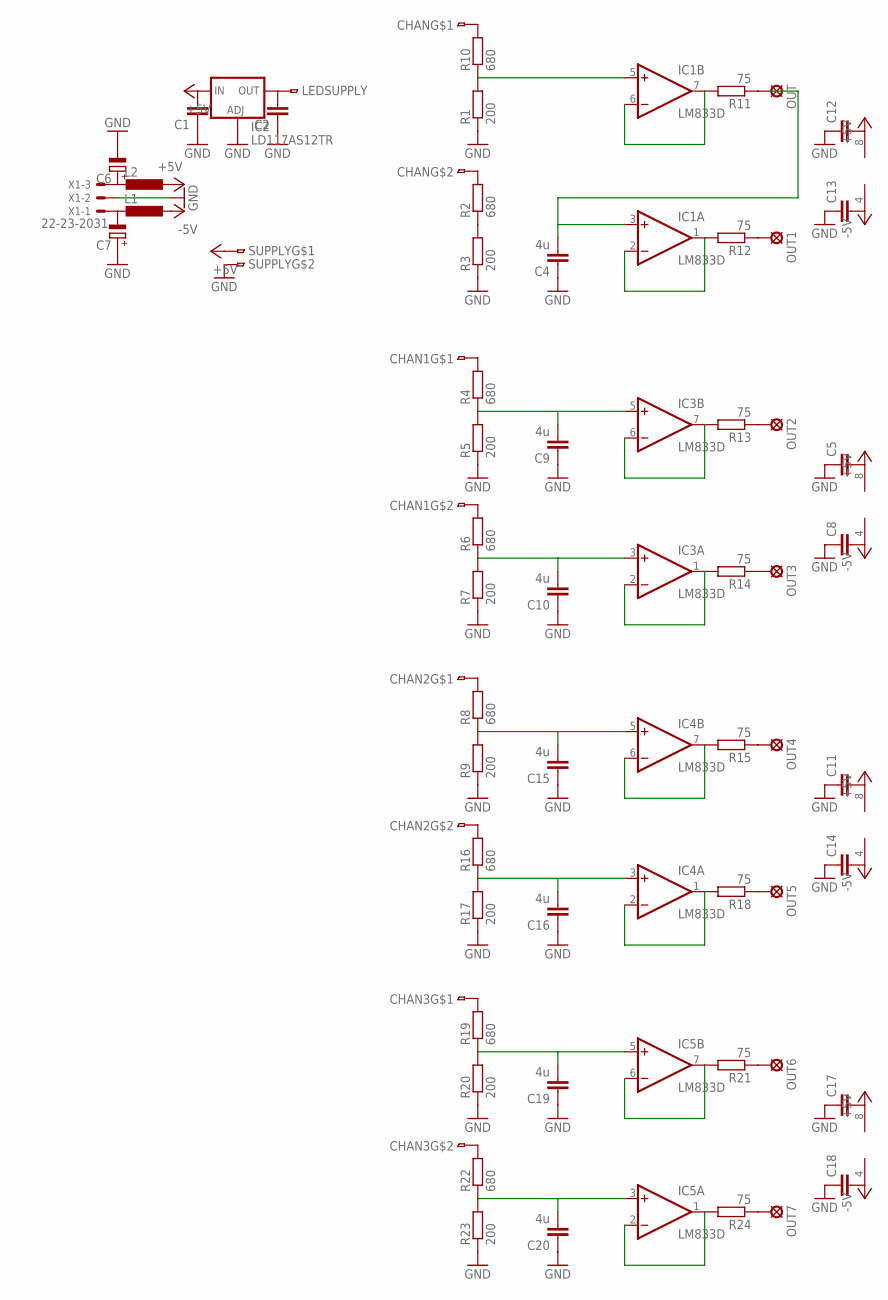
[picture p214: schematic sk536-fft2cv-supplyAndOutputs.sch]

Parts:
C1, C2, C5, C8, C11, C12, C13, C14, C17, C18: C-EUC0603; C0603
C4, C9, C10, C15, C16, C19, C20: 4u; C1206
C6, C7: CPOL-EUCT3528; CT3528
CHAN, CHAN1, CHAN2, CHAN3: 2PIN-SMD-2.54
IC1, IC3, IC4, IC5: LM833D; SO08
IC2: LD117AS12TR; SOT223
L1, L2: L-EUL2012C; L2012C
LEDSUPPLY: 1PINSMD
OUT, OUT1, OUT2, OUT3, OUT4, OUT5, OUT6, OUT7: LSP13
R1, R3, R5, R7, R9, R17, R20, R23: 200; R1206
R2, R4, R6, R8, R10, R16, R19, R22: 680; R1206
R11, R12, R13, R14, R15, R18, R21, R24: 75; R1206
SUPPLY: 2PIN-SMD-2.54
X1: 22-23-2031

Connections:
+5V: C1.2, C5.2, C11.2, C12.2, C17.2, IC1.8 (V+), IC2.3 (IN), IC3.8 (V+), IC4.8 (V+), IC5.8 (V+), L2.1, SUPPLY.2
-5V: C8.2, C13.2, C14.2, C18.2, IC1.4 (V-), IC3.4 (V-), IC4.4 (V-), IC5.4 (V-), L1.1
GND: C1.1, C2.1, C4.1, C5.1, C6.-, C7.+, C8.1, C9.1, C10.1, C11.1, C12.1, C13.1, C14.1, C15.1, C16.1, C17.1, C18.1, C19.1, C20.1, IC2.1 (ADJ), R1.1, R3.1, R5.1, R7.1, R9.1, R17.1, R20.1, R23.1, SUPPLY.3, X1.2
unnamed: CHAN.2, R10.2
unnamed: C2.2, IC2.4 (OUT), LEDSUPPLY.2
unnamed: OUT.MP, R11.1
unnamed: IC1.5 (+IN), R1.2, R10.1
unnamed: IC1.6 (-IN), IC1.7 (OUT), R11.2
unnamed: CHAN.3, R2.2
unnamed: C4.2, IC1.3 (+IN)
unnamed: IC1.1 (OUT), IC1.2 (-IN), R12.2
unnamed: OUT1.MP, R12.1
unnamed: CHAN1.2, R4.2
unnamed: C9.2, IC3.5 (+IN), R4.1, R5.2
unnamed: IC3.6 (-IN), IC3.7 (OUT), R13.2
unnamed: OUT2.MP, R13.1
unnamed: C10.2, IC3.3 (+IN), R6.1, R7.2
unnamed: IC3.1 (OUT), IC3.2 (-IN), R14.2
unnamed: CHAN1.3, R6.2
unnamed: OUT3.MP, R14.1
unnamed: CHAN2.2, R8.2
unnamed: C15.2, IC4.5 (+IN), R8.1, R9.2
unnamed: IC4.6 (-IN), IC4.7 (OUT), R15.2
unnamed: OUT4.MP, R15.1
unnamed: C16.2, IC4.3 (+IN), R16.1, R17.2
unnamed: IC4.1 (OUT), IC4.2 (-IN), R18.2
unnamed: CHAN2.3, R16.2
unnamed: OUT5.MP, R18.1
unnamed: CHAN3.2, R19.2
unnamed: C19.2, IC5.5 (+IN), R19.1, R20.2
unnamed: IC5.6 (-IN), IC5.7 (OUT), R21.2
unnamed: OUT6.MP, R21.1
unnamed: C20.2, IC5.3 (+IN), R22.1, R23.2
unnamed: IC5.1 (OUT), IC5.2 (-IN), R24.2
unnamed: CHAN3.3, R22.2
unnamed: OUT7.MP, R24.1
unnamed: R2.1, R3.2
unnamed: C7.-, L1.2, X1.1
unnamed: C6.+, L2.2, X1.3

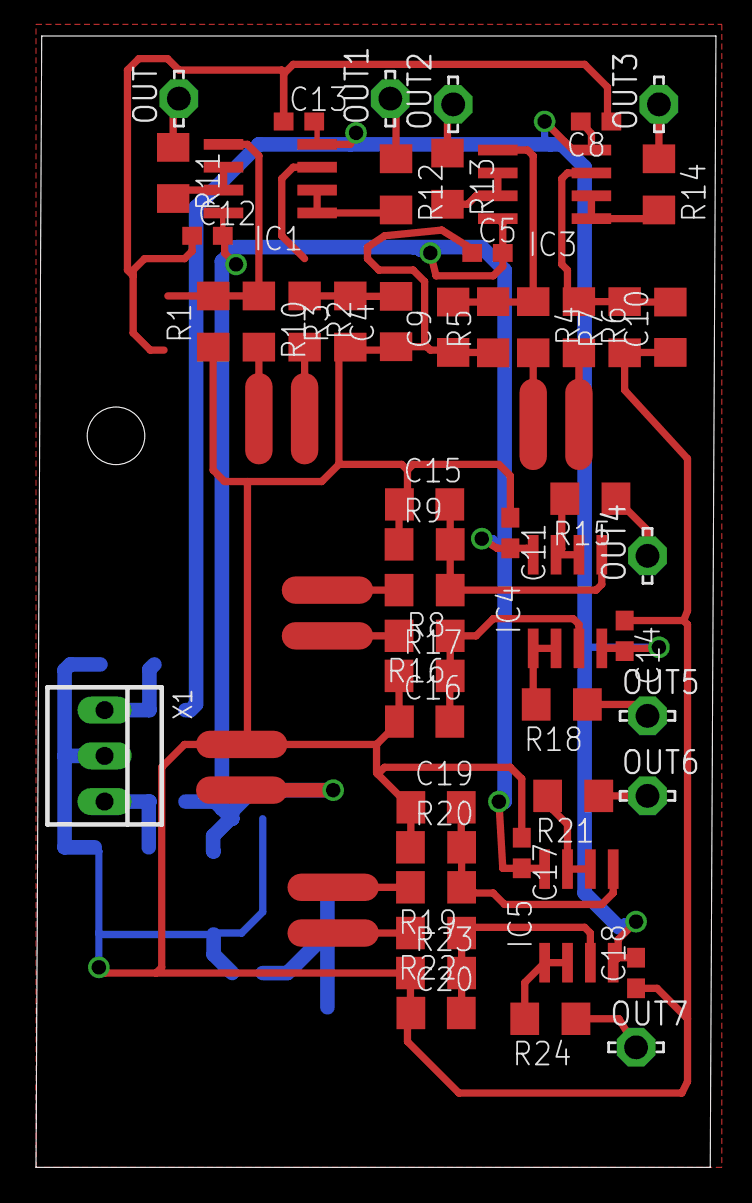
[picture p215: board sk536-fft2cv-supplyAndOutputs.brd from above]

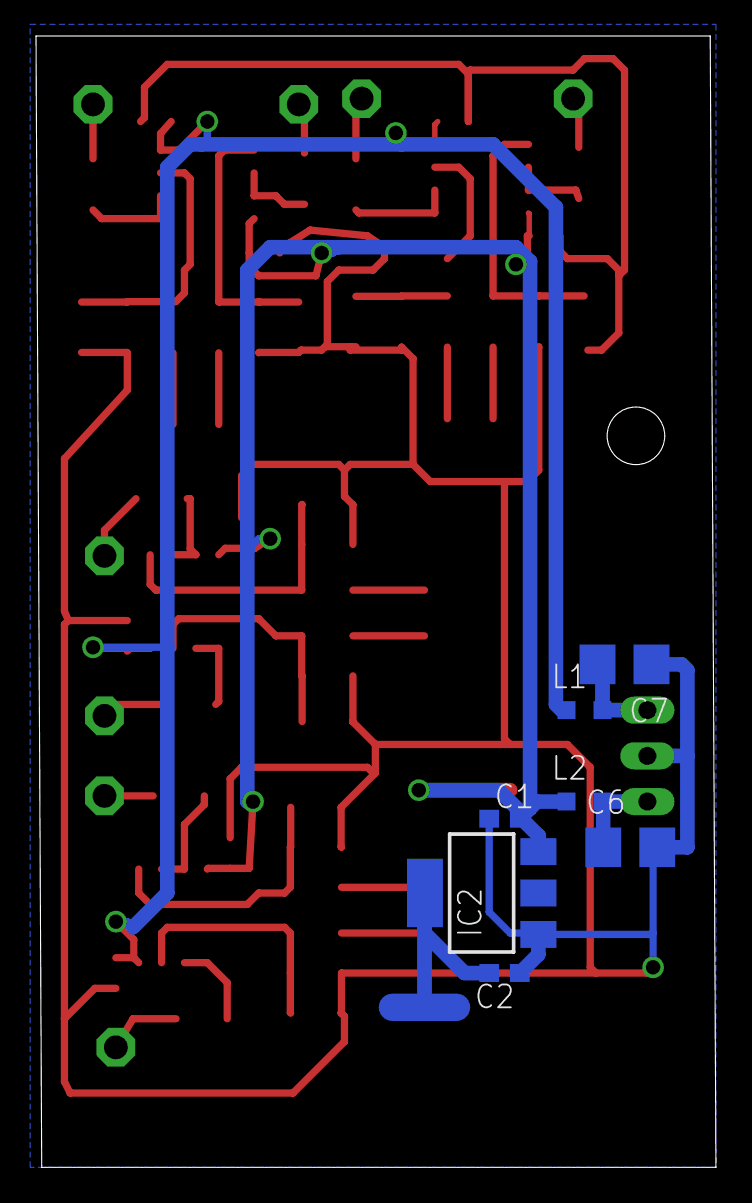
[picture p216: board sk536-fft2cv-supplyAndOutputs.brd from below]

Board: 2 copper layers, 37.8 x 62.9 mm, 65 parts (8 on the bottom side), 39 nets.
