mirdej/synkie/eagle/sk536-audio-pfft/sk536-fft2cv.brd

## EAGLE design eagle/sk536-audio-pfft/sk536-fft2cv.brd (2018-03-19)

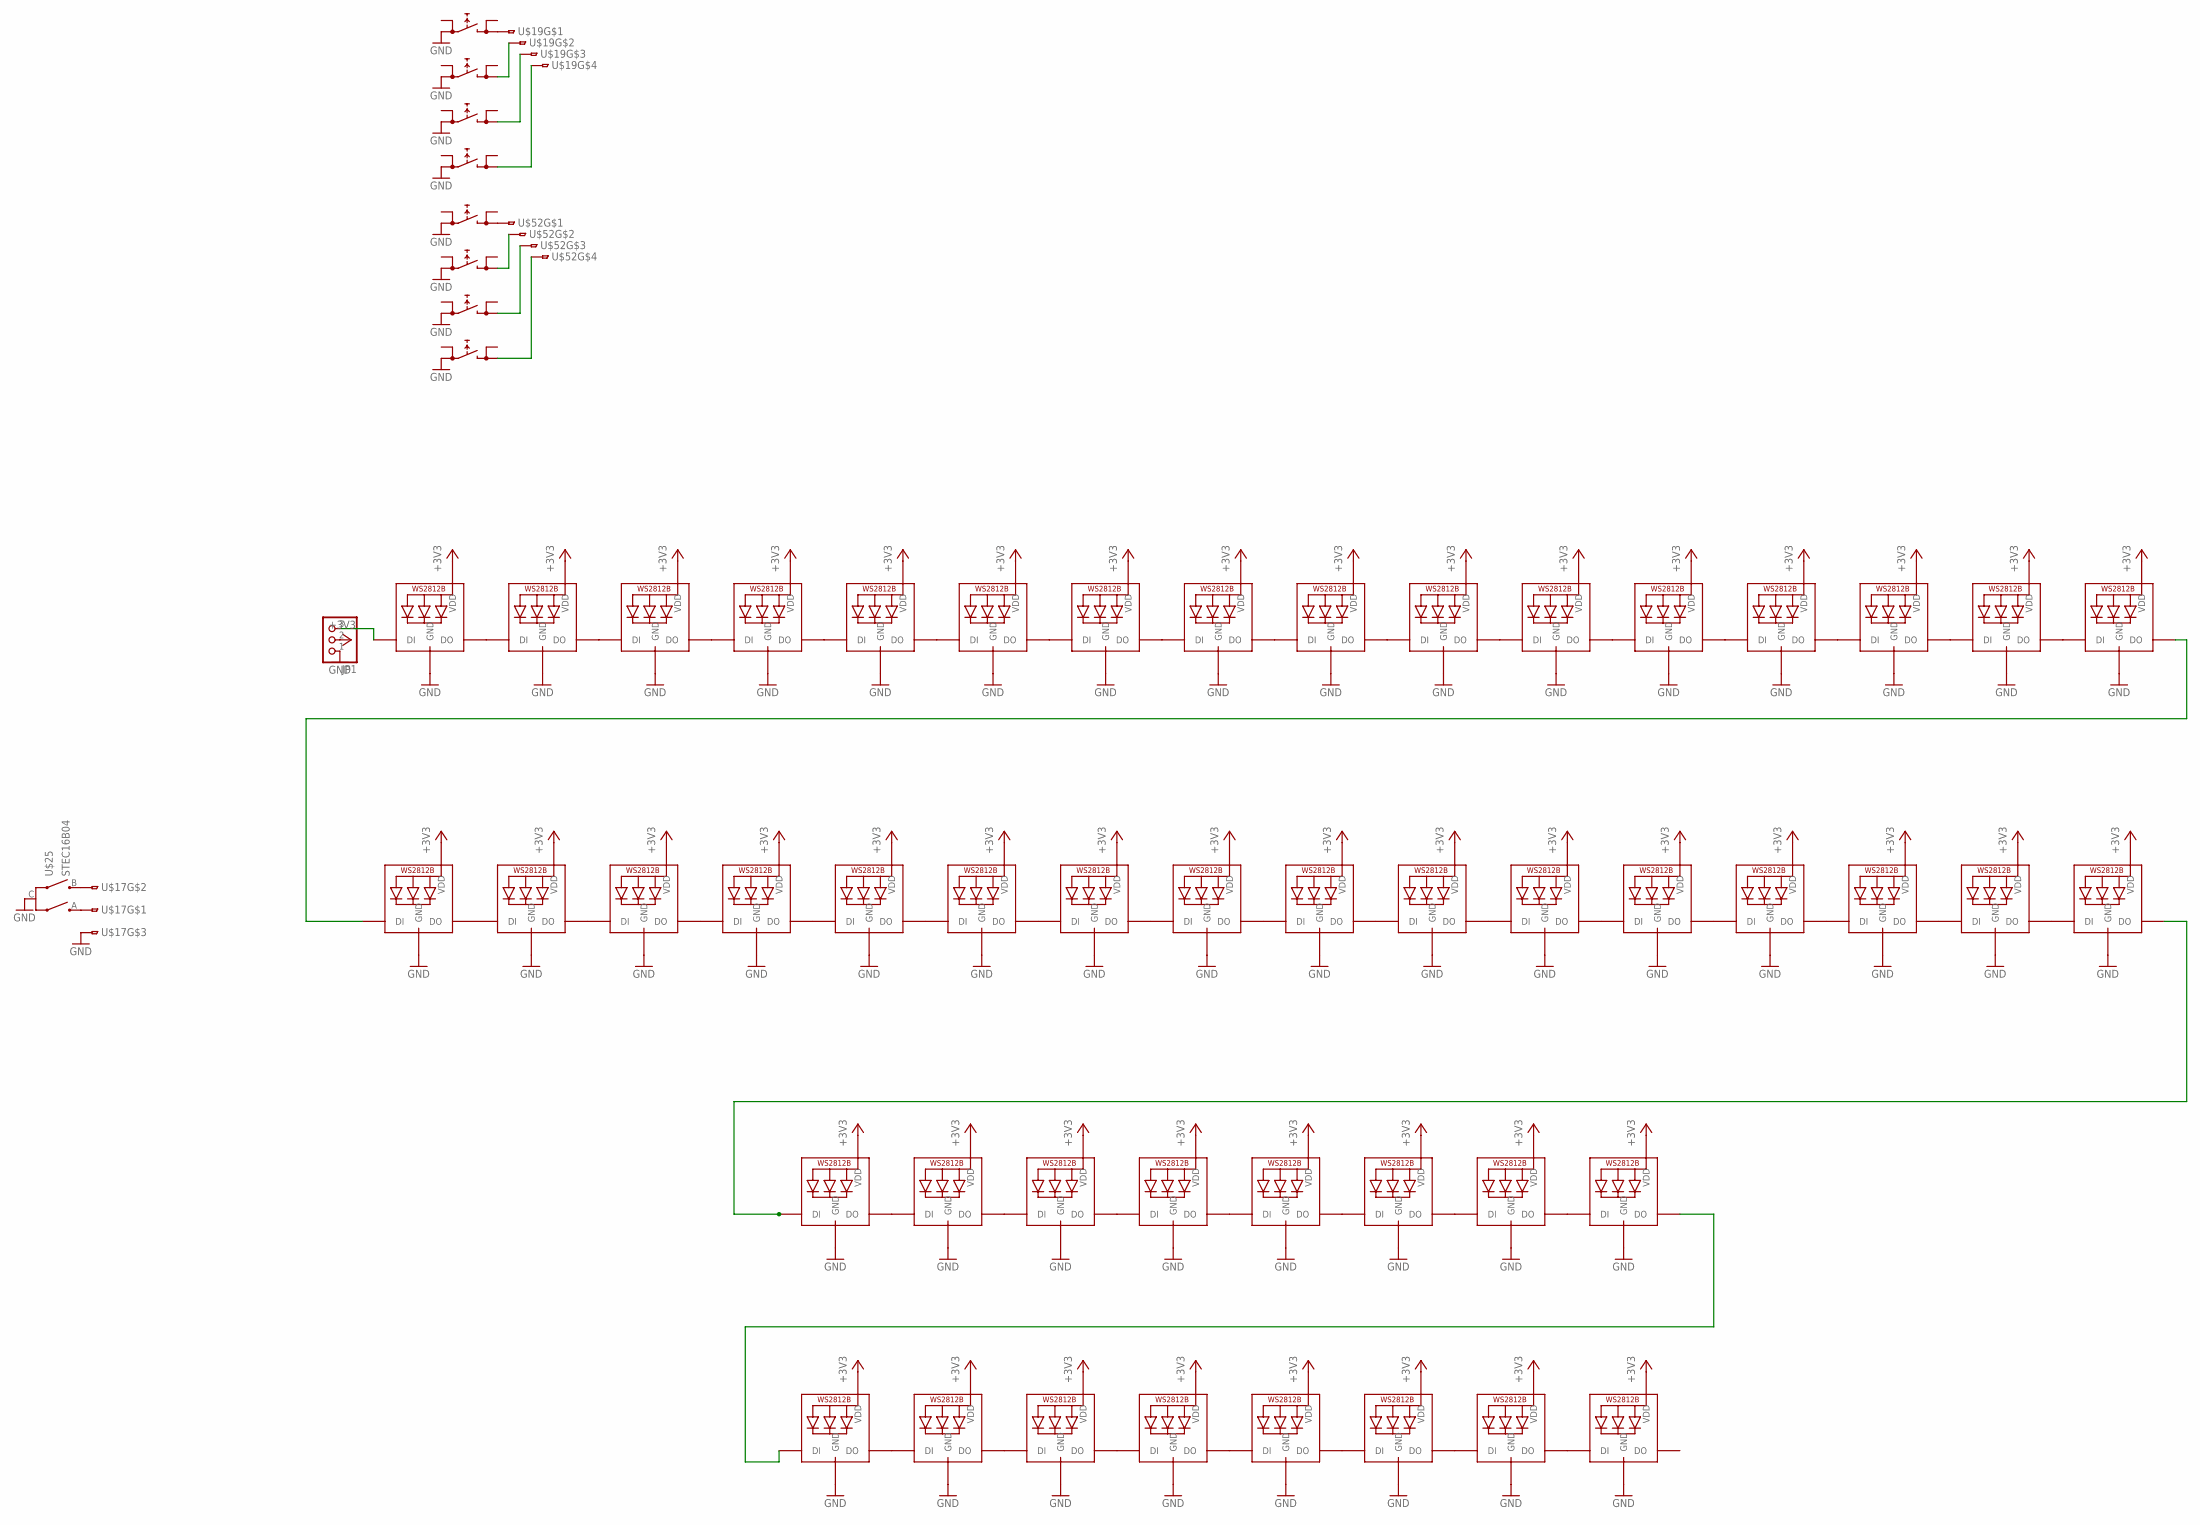
[picture p217: schematic sk536-fft2cv.sch]

Parts:
JP1: PINHD-1X3; 1X03
T1, T2, T3, T4, T5, T6, T7, T8: PRINTTASTER_SMDALPS-SKQ; SKQGAKE010
U$1, U$2, U$3, U$4, U$5, U$6, U$7, U$8, U$9, U$10, U$11, U$12, U$13, U$14, U$15, U$16, U$18, U$20, U$21, U$22, U$23, U$24, U$26, U$27, U$28, U$29, U$30, U$31, U$32, U$33, U$34, U$35, U$36, U$37, U$38, U$39, U$40, U$41, U$42, U$43, U$44, U$45, U$46, U$47, U$48, U$49, U$50, U$51: SK6812MINI
U$17: 3PIN-SMD-2.54
U$19, U$52: 4PIN-SMD; 4PIN-SMD-2.54
U$25: STEC16B04

Connections:
+3V3: JP1.2, U$1.4 (VDD), U$2.4 (VDD), U$3.4 (VDD), U$4.4 (VDD), U$5.4 (VDD), U$6.4 (VDD), U$7.4 (VDD), U$8.4 (VDD), U$9.4 (VDD), U$10.4 (VDD), U$11.4 (VDD), U$12.4 (VDD), U$13.4 (VDD), U$14.4 (VDD), U$15.4 (VDD), U$16.4 (VDD), U$18.4 (VDD), U$20.4 (VDD), U$21.4 (VDD), U$22.4 (VDD), U$23.4 (VDD), U$24.4 (VDD), U$26.4 (VDD), U$27.4 (VDD), U$28.4 (VDD), U$29.4 (VDD), U$30.4 (VDD), U$31.4 (VDD), U$32.4 (VDD), U$33.4 (VDD), U$34.4 (VDD), U$35.4 (VDD), U$36.4 (VDD), U$37.4 (VDD), U$38.4 (VDD), U$39.4 (VDD), U$40.4 (VDD), U$41.4 (VDD), U$42.4 (VDD), U$43.4 (VDD), U$44.4 (VDD), U$45.4 (VDD), U$46.4 (VDD), U$47.4 (VDD), U$48.4 (VDD), U$49.4 (VDD), U$50.4 (VDD), U$51.4 (VDD)
GND: JP1.1, T1.2 (0), T2.2 (0), T3.2 (0), T4.2 (0), T5.2 (0), T6.2 (0), T7.2 (0), T8.2 (0), U$1.2 (GND), U$2.2 (GND), U$3.2 (GND), U$4.2 (GND), U$5.2 (GND), U$6.2 (GND), U$7.2 (GND), U$8.2 (GND), U$9.2 (GND), U$10.2 (GND), U$11.2 (GND), U$12.2 (GND), U$13.2 (GND), U$14.2 (GND), U$15.2 (GND), U$16.2 (GND), U$17.3, U$18.2 (GND), U$20.2 (GND), U$21.2 (GND), U$22.2 (GND), U$23.2 (GND), U$24.2 (GND), U$25.C, U$26.2 (GND), U$27.2 (GND), U$28.2 (GND), U$29.2 (GND), U$30.2 (GND), U$31.2 (GND), U$32.2 (GND), U$33.2 (GND), U$34.2 (GND), U$35.2 (GND), U$36.2 (GND), U$37.2 (GND), U$38.2 (GND), U$39.2 (GND), U$40.2 (GND), U$41.2 (GND), U$42.2 (GND), U$43.2 (GND), U$44.2 (GND), U$45.2 (GND), U$46.2 (GND), U$47.2 (GND), U$48.2 (GND), U$49.2 (GND), U$50.2 (GND), U$51.2 (GND)
unnamed: U$1.1 (DO), U$2.3 (DI)
unnamed: U$2.1 (DO), U$3.3 (DI)
unnamed: U$3.1 (DO), U$4.3 (DI)
unnamed: U$4.1 (DO), U$5.3 (DI)
unnamed: U$5.1 (DO), U$6.3 (DI)
unnamed: U$6.1 (DO), U$7.3 (DI)
unnamed: U$7.1 (DO), U$8.3 (DI)
unnamed: U$8.1 (DO), U$9.3 (DI)
unnamed: U$9.1 (DO), U$10.3 (DI)
unnamed: U$10.1 (DO), U$11.3 (DI)
unnamed: U$13.1 (DO), U$14.3 (DI)
unnamed: U$14.1 (DO), U$15.3 (DI)
unnamed: U$15.1 (DO), U$16.3 (DI)
unnamed: U$11.1 (DO), U$12.3 (DI)
unnamed: U$12.1 (DO), U$13.3 (DI)
unnamed: U$26.1 (DO), U$27.3 (DI)
unnamed: U$27.1 (DO), U$28.3 (DI)
unnamed: U$28.1 (DO), U$29.3 (DI)
unnamed: U$29.1 (DO), U$30.3 (DI)
unnamed: U$30.1 (DO), U$31.3 (DI)
unnamed: U$31.1 (DO), U$32.3 (DI)
unnamed: U$32.1 (DO), U$33.3 (DI)
unnamed: U$33.1 (DO), U$34.3 (DI)
unnamed: U$34.1 (DO), U$35.3 (DI)
unnamed: U$35.1 (DO), U$36.3 (DI)
unnamed: U$38.1 (DO), U$39.3 (DI)
unnamed: U$39.1 (DO), U$40.3 (DI)
unnamed: U$40.1 (DO), U$41.3 (DI)
unnamed: U$36.1 (DO), U$37.3 (DI)
unnamed: U$37.1 (DO), U$38.3 (DI)
unnamed: U$16.1 (DO), U$26.3 (DI)
unnamed: U$18.3 (DI), U$41.1 (DO)
unnamed: U$18.1 (DO), U$20.3 (DI)
unnamed: U$20.1 (DO), U$21.3 (DI)
unnamed: U$23.1 (DO), U$24.3 (DI)
unnamed: U$24.1 (DO), U$42.3 (DI)
unnamed: U$42.1 (DO), U$43.3 (DI)
unnamed: U$21.1 (DO), U$22.3 (DI)
unnamed: U$22.1 (DO), U$23.3 (DI)
unnamed: U$17.1, U$25.A
unnamed: U$44.1 (DO), U$45.3 (DI)
unnamed: U$45.1 (DO), U$46.3 (DI)
unnamed: U$48.1 (DO), U$49.3 (DI)
unnamed: U$49.1 (DO), U$50.3 (DI)
unnamed: U$50.1 (DO), U$51.3 (DI)
unnamed: U$46.1 (DO), U$47.3 (DI)
unnamed: U$47.1 (DO), U$48.3 (DI)
unnamed: U$43.1 (DO), U$44.3 (DI)
unnamed: U$17.2, U$25.B
unnamed: JP1.3, U$1.3 (DI)
unnamed: T1.4 (1), U$19.1
unnamed: T2.4 (1), U$19.2
unnamed: T3.4 (1), U$19.3
unnamed: T4.4 (1), U$19.4
unnamed: T5.4 (1), U$52.1
unnamed: T6.4 (1), U$52.2
unnamed: T7.4 (1), U$52.3
unnamed: T8.4 (1), U$52.4
