mirdej/synkie/eagle/sk536-audio-pfft/sk536-fft2cv.brd

## EAGLE design eagle/sk536-audio-pfft/sk536-fft2cv.brd (continued)

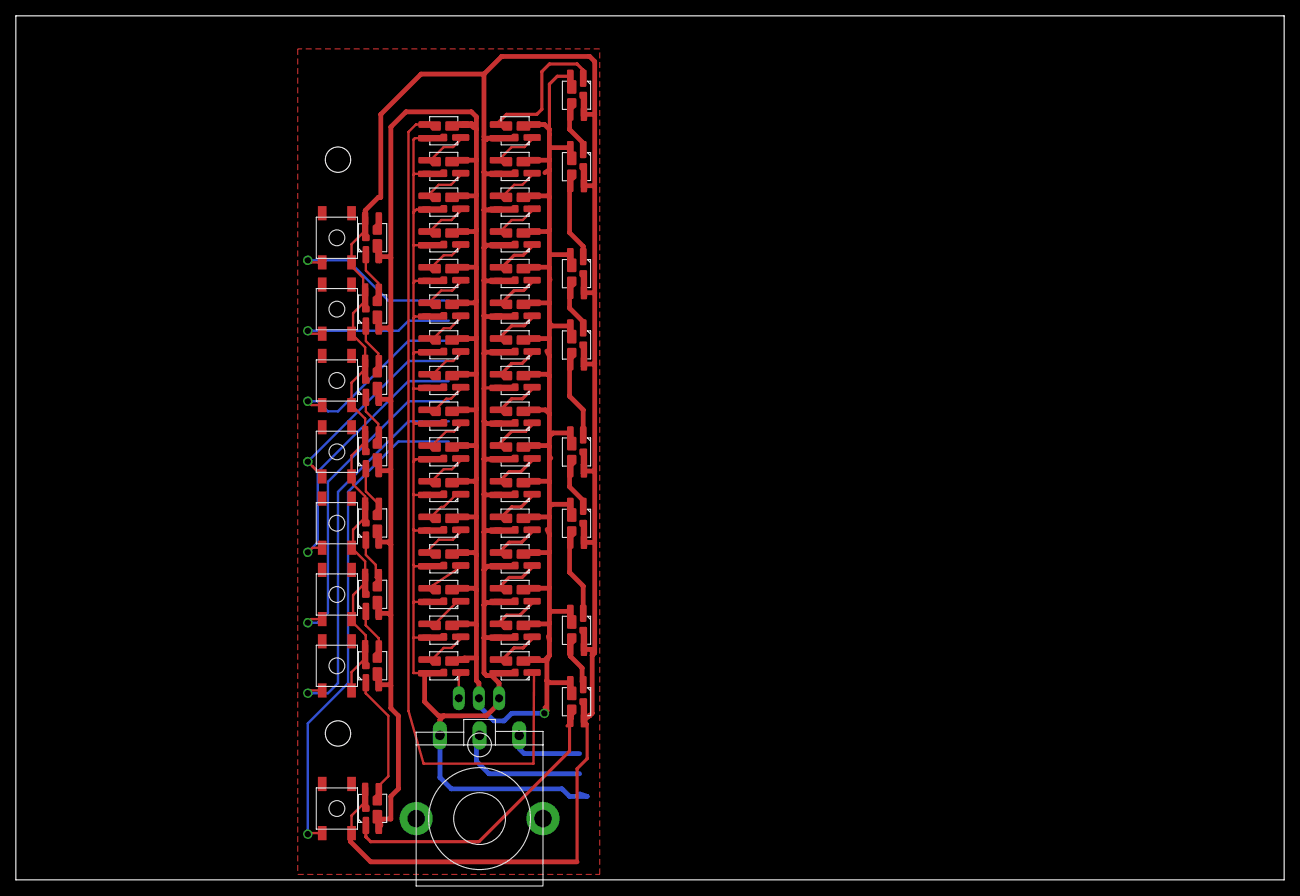
[picture p218: board sk536-fft2cv.brd from above]

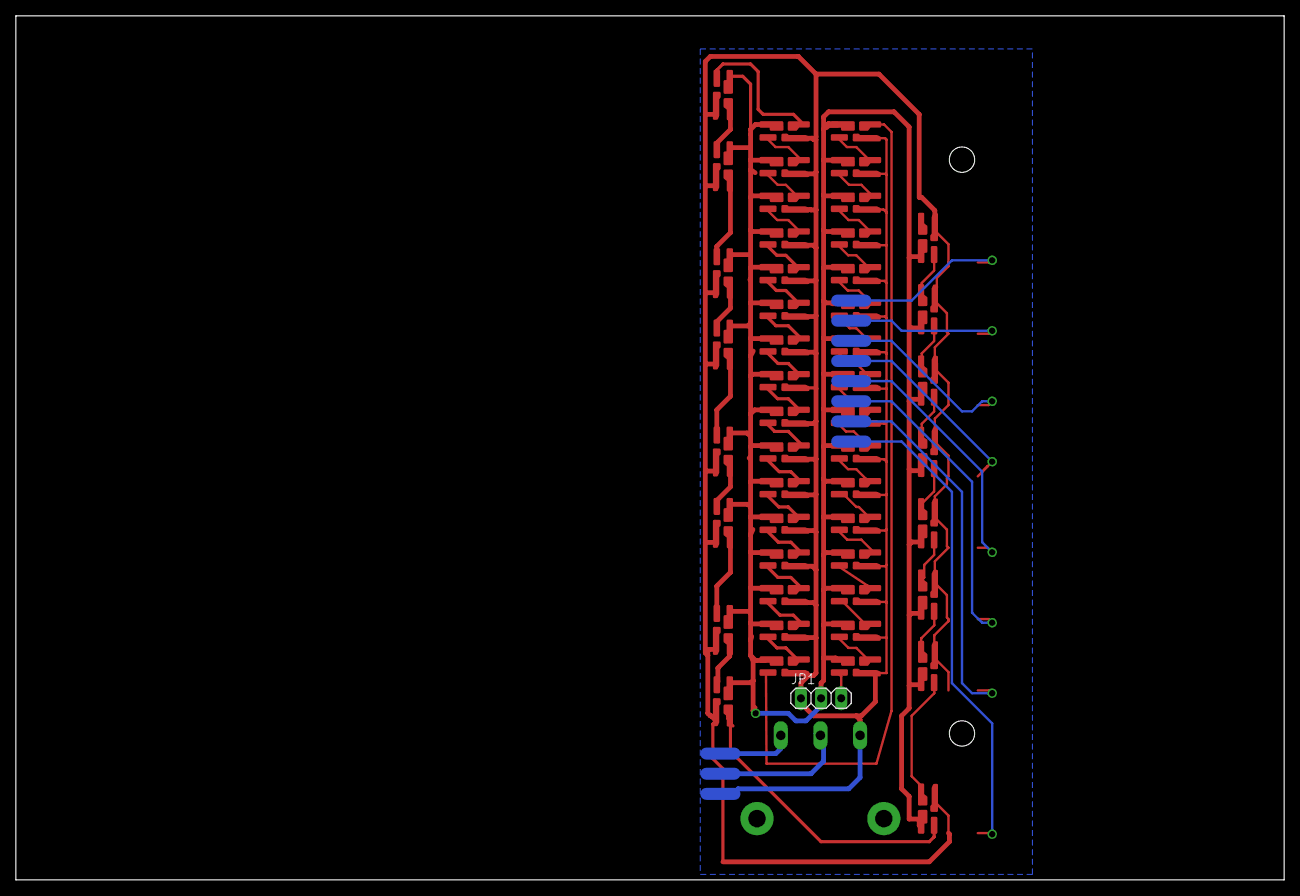
[picture p219: board sk536-fft2cv.brd from below]

Board: 2 copper layers, 160.0 x 109.0 mm, 61 parts (4 on the bottom side), 60 nets.
