mirdej/synkie/eagle/sk720-step-sequencer/sk720-step-sequencer.brd

## EAGLE design eagle/sk720-step-sequencer/sk720-step-sequencer.brd (2018-03-19)

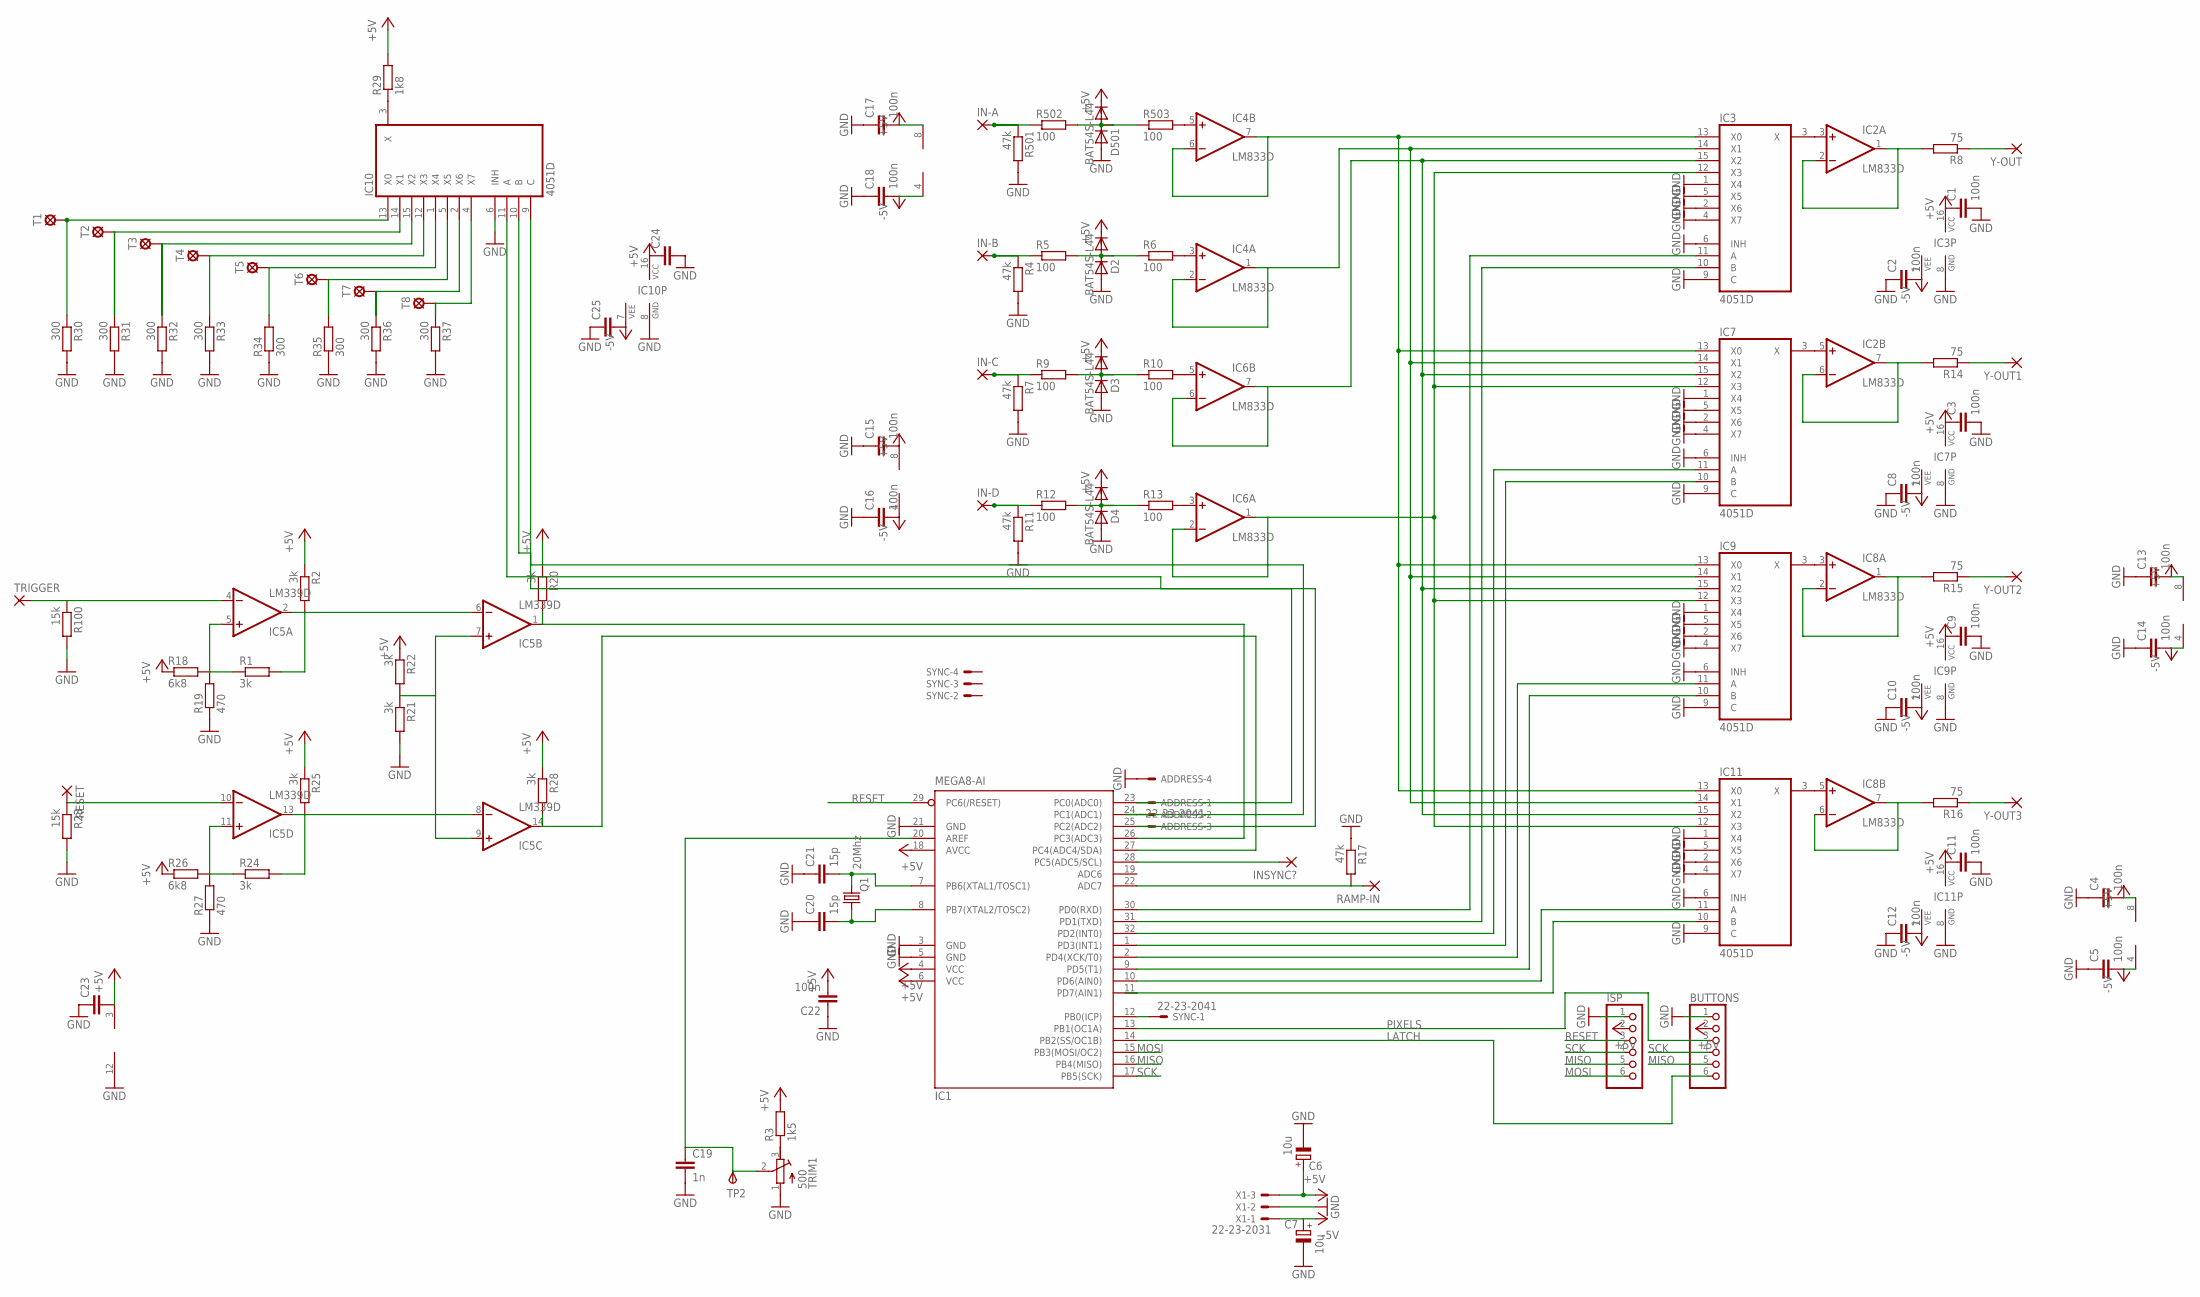
[picture p220: schematic sk720-step-sequencer.sch]

Parts:
ADDRESS: 22-23-2041
BUTTONS: PINHD-1X6; 1X06
C1, C2, C3, C4, C5, C8, C9, C10, C11, C12, C13, C14, C15, C16, C17, C18, C22: 100n; C0603
C6, C7: 10u; CT3528
C19: 1n; C1206
C20, C21: 15p; C1206
C23: C-EUC1206; C1206
C24, C25: C-EUC0603; C0603
D2, D3, D4, D501: BAT54S-L44; SOT23
IC1: MEGA8-AI; TQFP32-08
IC2, IC4, IC6, IC8: LM833D; SO08
IC3, IC7, IC9, IC10, IC11: 4051D; SO16
IC5: LM339D; SO14
IN-A: 3,17/1,1
IN-B: 3,17/1,1
IN-C: 3,17/1,1
IN-D: 3,17/1,1
INSYNC?: 3,17/1,1
ISP: PINHD-1X6; 1X06
Q1: 20Mhz; HC49UP
R1, R2, R20, R21, R22, R24, R25, R28: 3k; R1206
R3: 1k5; R1206
R4, R7, R11, R17, R501: 47k; R1206
R5, R6, R9, R10, R12, R13, R502, R503: 100; R1206
R8, R14, R15, R16: 75; R1206
R18, R26: 6k8; R1206
R19, R27: 470; R1206
R23, R100: 15k; R1206
R29: 1k8; R1206
R30, R31, R32, R33, R34, R35, R36, R37: 300; R1206
RAMP-IN: 3,17/1,1
RESET: 3,17/1,1
SYNC: 22-23-2041
T1, T2, T3, T4, T5, T6, T7, T8: LSP13
TP2: TPSPAD1-13; P1-13
TRIGGER: 3,17/1,1
TRIM1: 500; RTRIM64Y
X1: 22-23-2031
Y-OUT, Y-OUT1, Y-OUT2, Y-OUT3: 3,17/1,1

Connections:
+5V: BUTTONS.2, C1.1, C3.1, C4.2, C6.+, C9.1, C11.1, C13.2, C15.2, C17.2, C22.2, C23.2, C24.1, D2.2 (C), D3.2 (C), D4.2 (C), D501.2 (C), IC1.4 (VCC), IC1.6 (VCC), IC1.18 (AVCC), IC2.8 (V+), IC3.16 (VCC), IC4.8 (V+), IC5.3 (V+), IC6.8 (V+), IC7.16 (VCC), IC8.8 (V+), IC9.16 (VCC), IC10.16 (VCC), IC11.16 (VCC), ISP.2, R2.1, R3.2, R18.1, R20.1, R22.1, R25.1, R26.1, R28.1, R29.2, X1.3
-5V: C2.2, C5.2, C7.+, C8.2, C10.2, C12.2, C14.2, C16.2, C18.2, C25.2, IC2.4 (V-), IC3.7 (VEE), IC4.4 (V-), IC6.4 (V-), IC7.7 (VEE), IC8.4 (V-), IC9.7 (VEE), IC10.7 (VEE), IC11.7 (VEE), X1.1
GND: ADDRESS.4, BUTTONS.1, C1.2, C2.1, C3.2, C4.1, C5.1, C6.-, C7.-, C8.1, C9.2, C10.1, C11.2, C12.1, C13.1, C14.1, C15.1, C16.1, C17.1, C18.1, C19.2, C20.1, C21.1, C22.1, C23.1, C24.2, C25.1, D2.1 (A), D3.1 (A), D4.1 (A), D501.1 (A), IC1.3 (GND), IC1.5 (GND), IC1.21 (GND), IC3.1 (X4), IC3.2 (X6), IC3.4 (X7), IC3.5 (X5), IC3.6 (INH), IC3.8 (GND), IC3.9 (C), IC5.12 (GND), IC7.1 (X4), IC7.2 (X6), IC7.4 (X7), IC7.5 (X5), IC7.6 (INH), IC7.8 (GND), IC7.9 (C), IC9.1 (X4), IC9.2 (X6), IC9.4 (X7), IC9.5 (X5), IC9.6 (INH), IC9.8 (GND), IC9.9 (C), IC10.6 (INH), IC10.8 (GND), IC11.1 (X4), IC11.2 (X6), IC11.4 (X7), IC11.5 (X5), IC11.6 (INH), IC11.8 (GND), IC11.9 (C), ISP.1, R4.2, R7.2, R11.2, R17.1, R19.1, R21.2, R23.2, R27.1, R30.2, R31.2, R32.2, R33.2, R34.1, R35.1, R36.2, R37.2, R100.2, R501.2, TRIM1.1 (E), X1.2
IN: IC3.12 (X3), IC6.1 (OUT), IC6.2 (-IN), IC7.12 (X3), IC9.12 (X3), IC11.12 (X3)
IN1: IC3.13 (X0), IC4.6 (-IN), IC4.7 (OUT), IC7.13 (X0), IC9.13 (X0), IC11.13 (X0)
IN2: IC3.14 (X1), IC4.1 (OUT), IC4.2 (-IN), IC7.14 (X1), IC9.14 (X1), IC11.14 (X1)
IN3: IC3.15 (X2), IC6.6 (-IN), IC6.7 (OUT), IC7.15 (X2), IC9.15 (X2), IC11.15 (X2)
LATCH: BUTTONS.6, IC1.14 (PB2(SS/OC1B))
MISO: BUTTONS.5, IC1.16 (PB4(MISO)), ISP.5
MOSI: IC1.15 (PB3(MOSI/OC2)), ISP.6
unnamed: IC2.3 (+IN), IC3.3 (X)
unnamed: IC4.5 (+IN), R503.2
unnamed: IC1.28 (PC5(ADC5/SCL)), INSYNC?.1
unnamed: IC1.12 (PB0(ICP)), SYNC.1
unnamed: R3.1, TRIM1.3 (A)
unnamed: ADDRESS.1, IC1.23 (PC0(ADC0)), IC10.11 (A)
unnamed: IN-B.1, R4.1, R5.1
unnamed: D2.3 (AC), R5.2, R6.1
unnamed: IC4.3 (+IN), R6.2
unnamed: IN-A.1, R501.1, R502.1
unnamed: D501.3 (AC), R502.2, R503.1
unnamed: R8.1, Y-OUT.1
unnamed: IC5.4 (-IN), R100.1, TRIGGER.1
unnamed: IC2.1 (OUT), IC2.2 (-IN), R8.2
unnamed: IN-C.1, R7.1, R9.1
unnamed: D3.3 (AC), R9.2, R10.1
unnamed: IC6.5 (+IN), R10.2
unnamed: IC1.30 (PD0(RXD)), IC3.11 (A)
unnamed: IN-D.1, R11.1, R12.1
unnamed: D4.3 (AC), R12.2, R13.1
unnamed: IC6.3 (+IN), R13.2
unnamed: IC5.2 (OUT), IC5.6 (-IN), R1.2, R2.2
unnamed: IC2.6 (-IN), IC2.7 (OUT), R14.2
unnamed: R14.1, Y-OUT1.1
unnamed: IC2.5 (+IN), IC7.3 (X)
unnamed: IC8.1 (OUT), IC8.2 (-IN), R15.2
unnamed: R15.1, Y-OUT2.1
unnamed: IC8.3 (+IN), IC9.3 (X)
unnamed: IC8.6 (-IN), IC8.7 (OUT), R16.2
unnamed: R16.1, Y-OUT3.1
unnamed: IC8.5 (+IN), IC11.3 (X)
unnamed: IC5.5 (+IN), R1.1, R18.2, R19.2
unnamed: IC1.31 (PD1(TXD)), IC3.10 (B)
unnamed: IC1.32 (PD2(INT0)), IC7.11 (A)
unnamed: IC1.1 (PD3(INT1)), IC7.10 (B)
unnamed: IC1.2 (PD4(XCK/T0)), IC9.11 (A)
unnamed: IC1.9 (PD5(T1)), IC9.10 (B)
unnamed: IC1.10 (PD6(AIN0)), IC11.11 (A)
unnamed: IC1.11 (PD7(AIN1)), IC11.10 (B)
unnamed: IC1.22 (ADC7), R17.2, RAMP-IN.1
unnamed: ADDRESS.2, IC1.24 (PC1(ADC1)), IC10.10 (B)
unnamed: ADDRESS.3, IC1.25 (PC2(ADC2)), IC10.9 (C)
unnamed: C21.2, IC1.7 (PB6(XTAL1/TOSC1)), Q1.2
unnamed: C20.2, IC1.8 (PB7(XTAL2/TOSC2)), Q1.1
unnamed: IC1.26 (PC3(ADC3)), IC5.1 (OUT), R20.2
unnamed: IC5.7 (+IN), IC5.9 (+IN), R21.1, R22.2
unnamed: IC5.10 (-IN), R23.1, RESET.1
unnamed: IC5.8 (-IN), IC5.13 (OUT), R24.2, R25.2
unnamed: IC5.11 (+IN), R24.1, R26.2, R27.2
unnamed: IC1.27 (PC4(ADC4/SDA)), IC5.14 (OUT), R28.2
unnamed: IC10.13 (X0), R30.1, T1.MP
unnamed: IC10.14 (X1), R31.1, T2.MP
unnamed: IC10.15 (X2), R32.1, T3.MP
unnamed: IC10.12 (X3), R33.1, T4.MP
unnamed: IC10.1 (X4), R34.2, T5.MP
unnamed: IC10.5 (X5), R35.2, T6.MP
unnamed: IC10.2 (X6), R36.1, T7.MP
unnamed: IC10.4 (X7), R37.1, T8.MP
unnamed: C19.1, IC1.20 (AREF), TP2.TP, TRIM1.2 (S)
unnamed: IC10.3 (X), R29.1
PIXELS: BUTTONS.3, IC1.13 (PB1(OC1A))
RESET: IC1.29 (PC6(/RESET)), ISP.3
SCK: BUTTONS.4, IC1.17 (PB5(SCK)), ISP.4

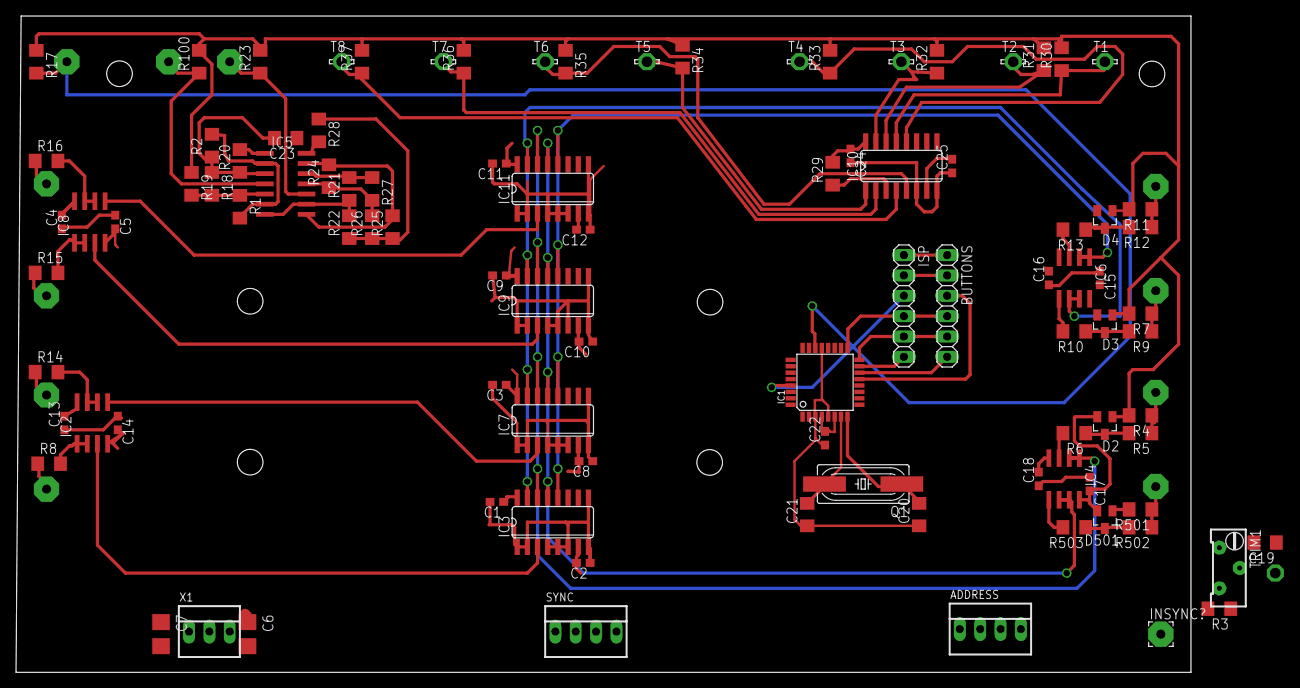
[picture p221: board sk720-step-sequencer.brd from above]

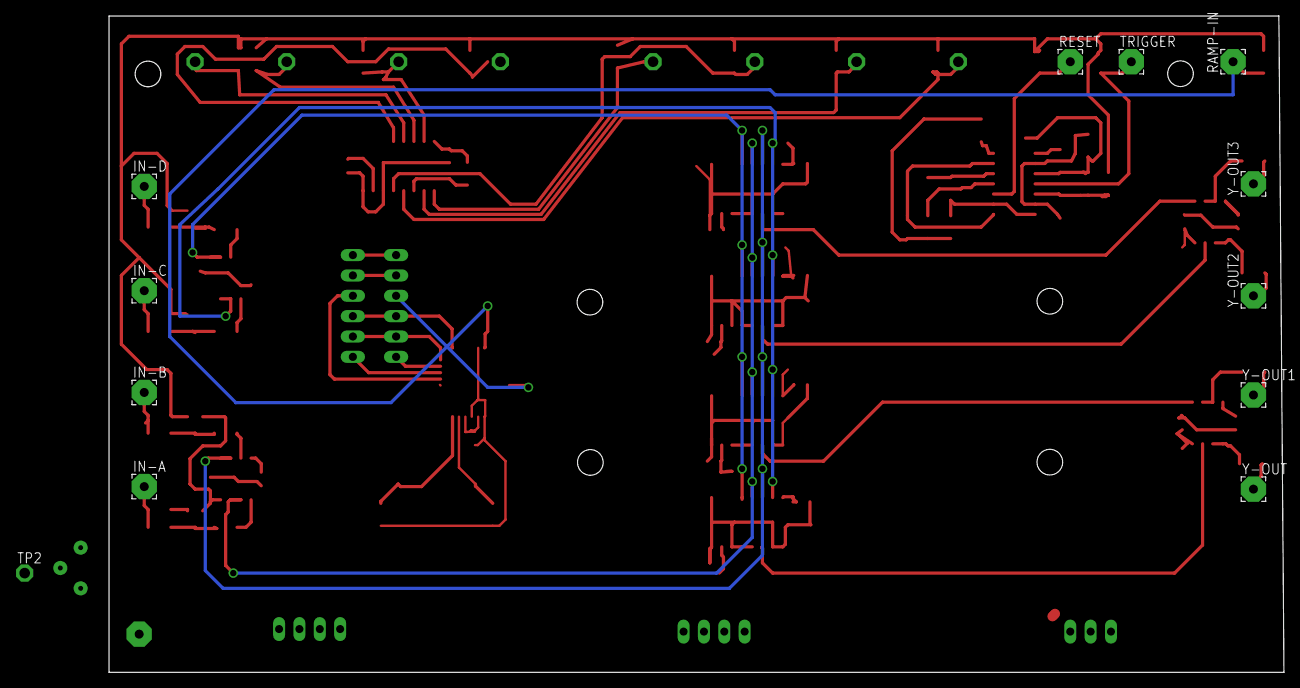
[picture p222: board sk720-step-sequencer.brd from below]

Board: 2 copper layers, 146.6 x 81.9 mm, 109 parts (12 on the bottom side), 73 nets.
