mirdej/synkie/eagle/sk720-step-sequencer/sk720-trig_out.brd

## EAGLE design eagle/sk720-step-sequencer/sk720-trig_out.brd (2017-11-06)

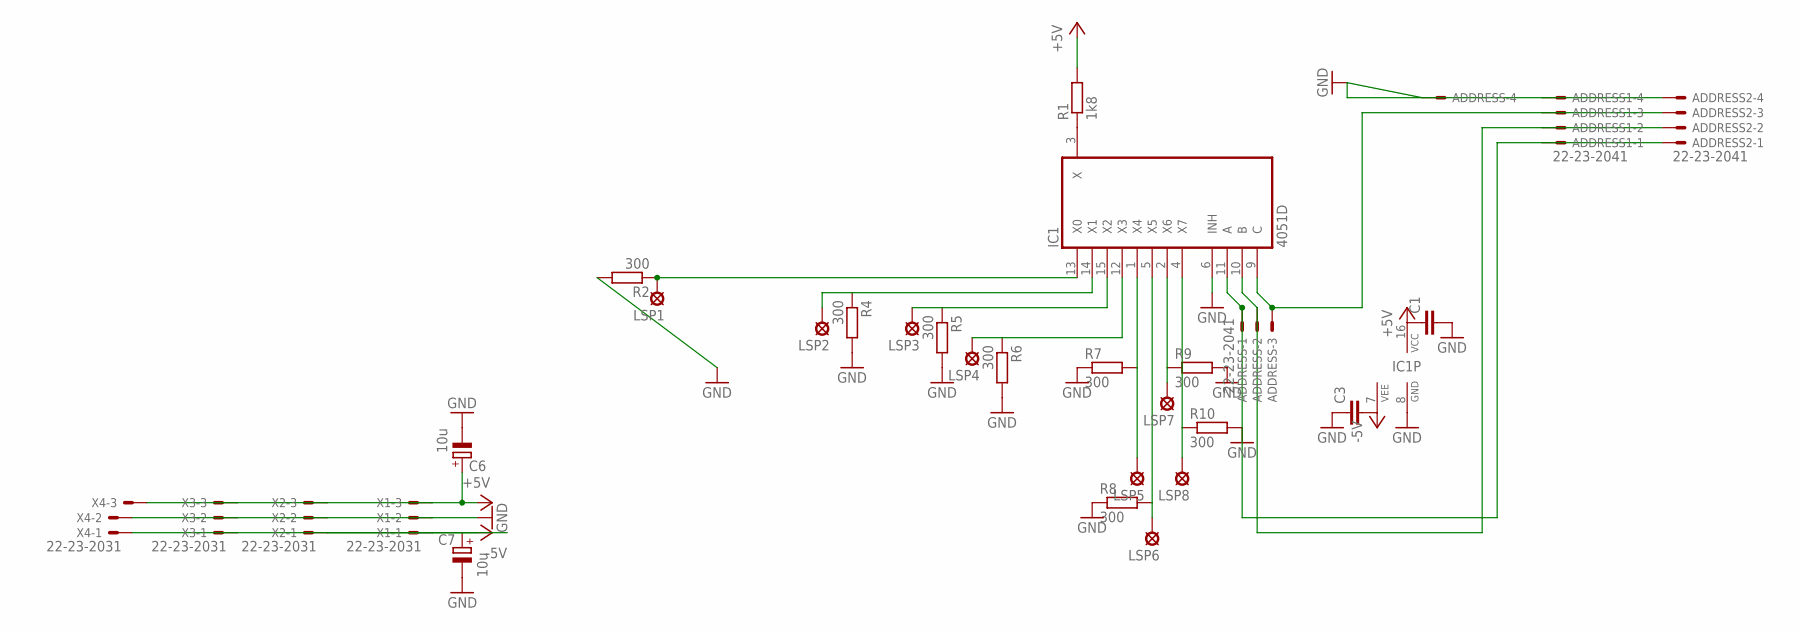
[picture p223: schematic sk720-trig_out.sch]

Parts:
ADDRESS, ADDRESS1, ADDRESS2: 22-23-2041
C1, C3: C-EUC0603; C0603
C6, C7: 10u; CT3528
IC1: 4051D; SO16
LSP1, LSP2, LSP3, LSP4, LSP5, LSP6, LSP7, LSP8: LSP13
R1: 1k8; R1206
R2, R4, R5, R6, R7, R8, R9, R10: 300; R1206
X1, X2, X3, X4: 22-23-2031

Connections:
+5V: C1.1, C6.+, IC1.16 (VCC), R1.2, X1.3, X2.3, X3.3, X4.3
-5V: C3.2, C7.+, IC1.7 (VEE), X1.1, X2.1, X3.1, X4.1
GND: ADDRESS.4, ADDRESS1.4, ADDRESS2.4, C1.2, C3.1, C6.-, C7.-, IC1.6 (INH), IC1.8 (GND), R2.2, R4.2, R5.2, R6.2, R7.1, R8.1, R9.2, R10.2, X1.2, X2.2, X3.2, X4.2
unnamed: IC1.1 (X4), LSP5.MP, R7.2
unnamed: IC1.5 (X5), LSP6.MP, R8.2
unnamed: IC1.2 (X6), LSP7.MP, R9.1
unnamed: IC1.4 (X7), LSP8.MP, R10.1
unnamed: IC1.3 (X), R1.1
unnamed: ADDRESS.1, ADDRESS1.1, ADDRESS2.1, IC1.11 (A)
unnamed: ADDRESS.2, ADDRESS1.2, ADDRESS2.2, IC1.10 (B)
unnamed: IC1.13 (X0), LSP1.MP, R2.1
unnamed: IC1.14 (X1), LSP2.MP, R4.1
unnamed: IC1.15 (X2), LSP3.MP, R5.1
unnamed: IC1.12 (X3), LSP4.MP, R6.1
unnamed: ADDRESS.3, ADDRESS1.3, ADDRESS2.3, IC1.9 (C)

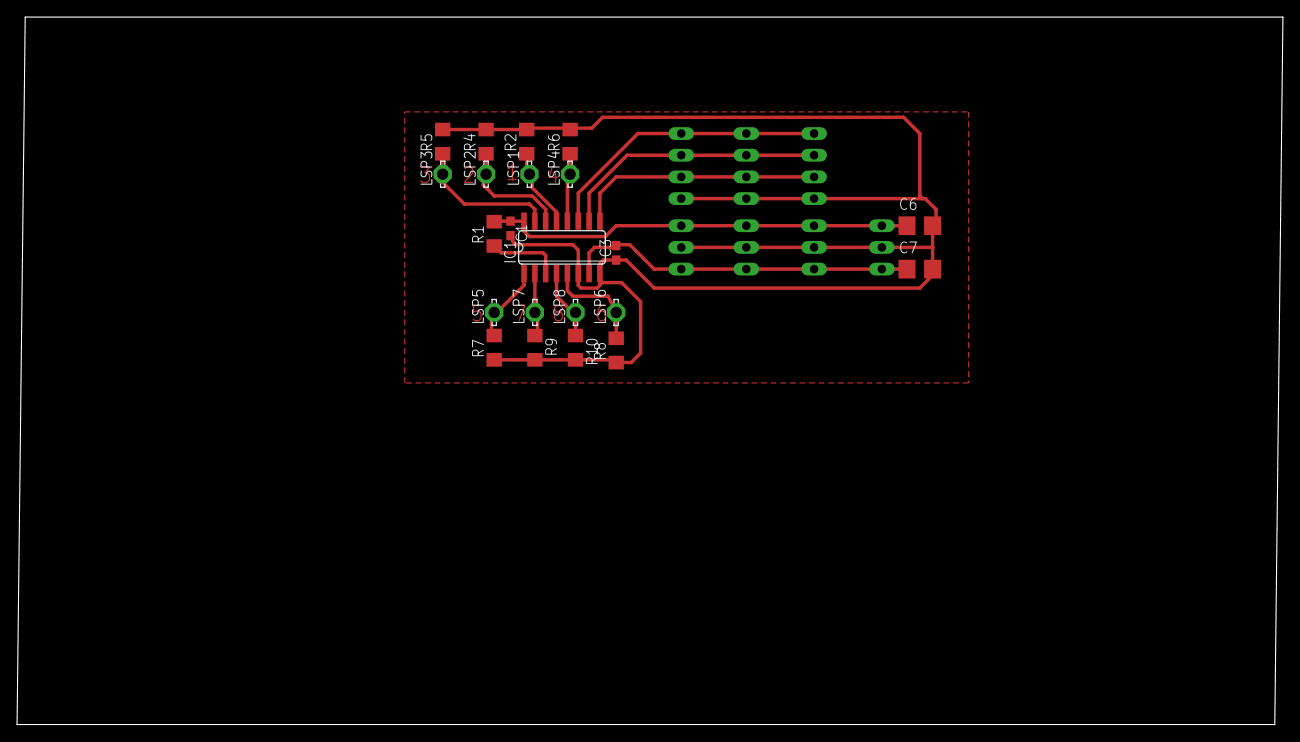
[picture p224: board sk720-trig_out.brd from above]

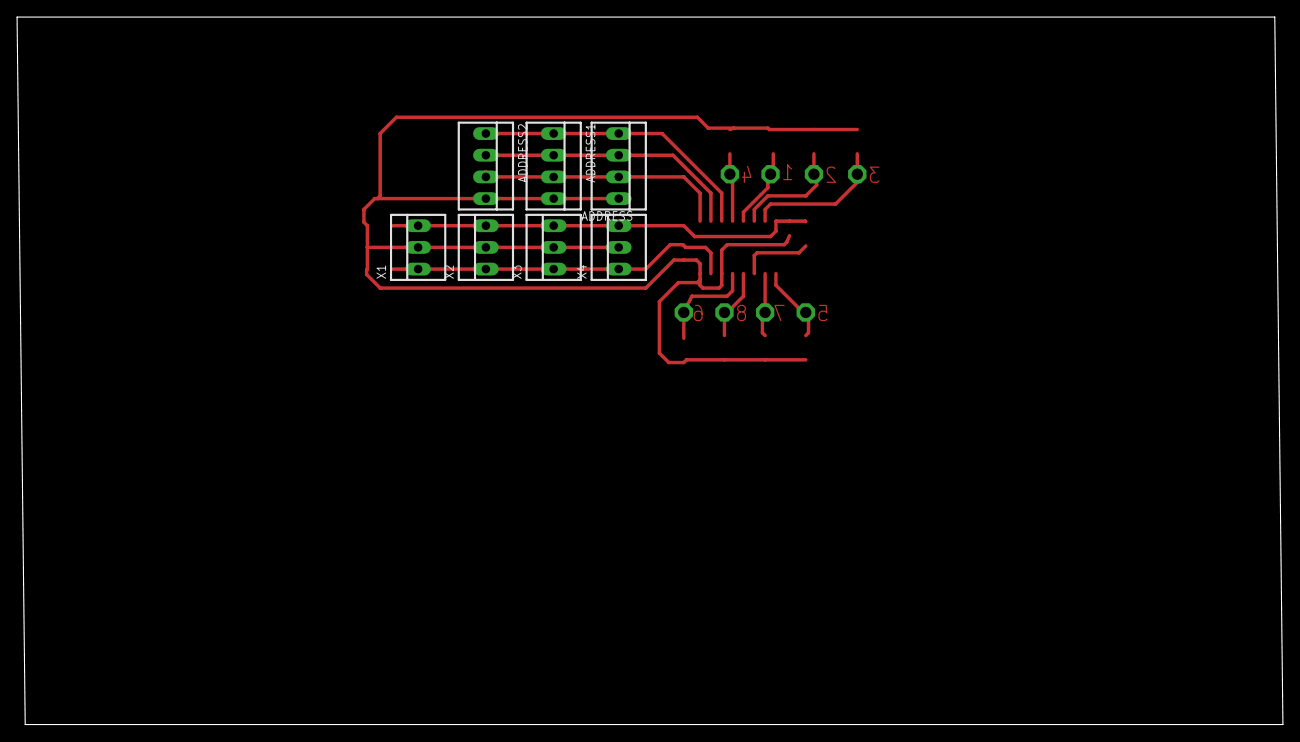
[picture p225: board sk720-trig_out.brd from below]

Board: 2 copper layers, 148.3 x 82.9 mm, 29 parts (7 on the bottom side), 15 nets.
