mirdej/synkie/eagle/sk911-waveshape/sk911-waveshape.brd

## EAGLE design eagle/sk911-waveshape/sk911-waveshape.brd (2017-11-06)

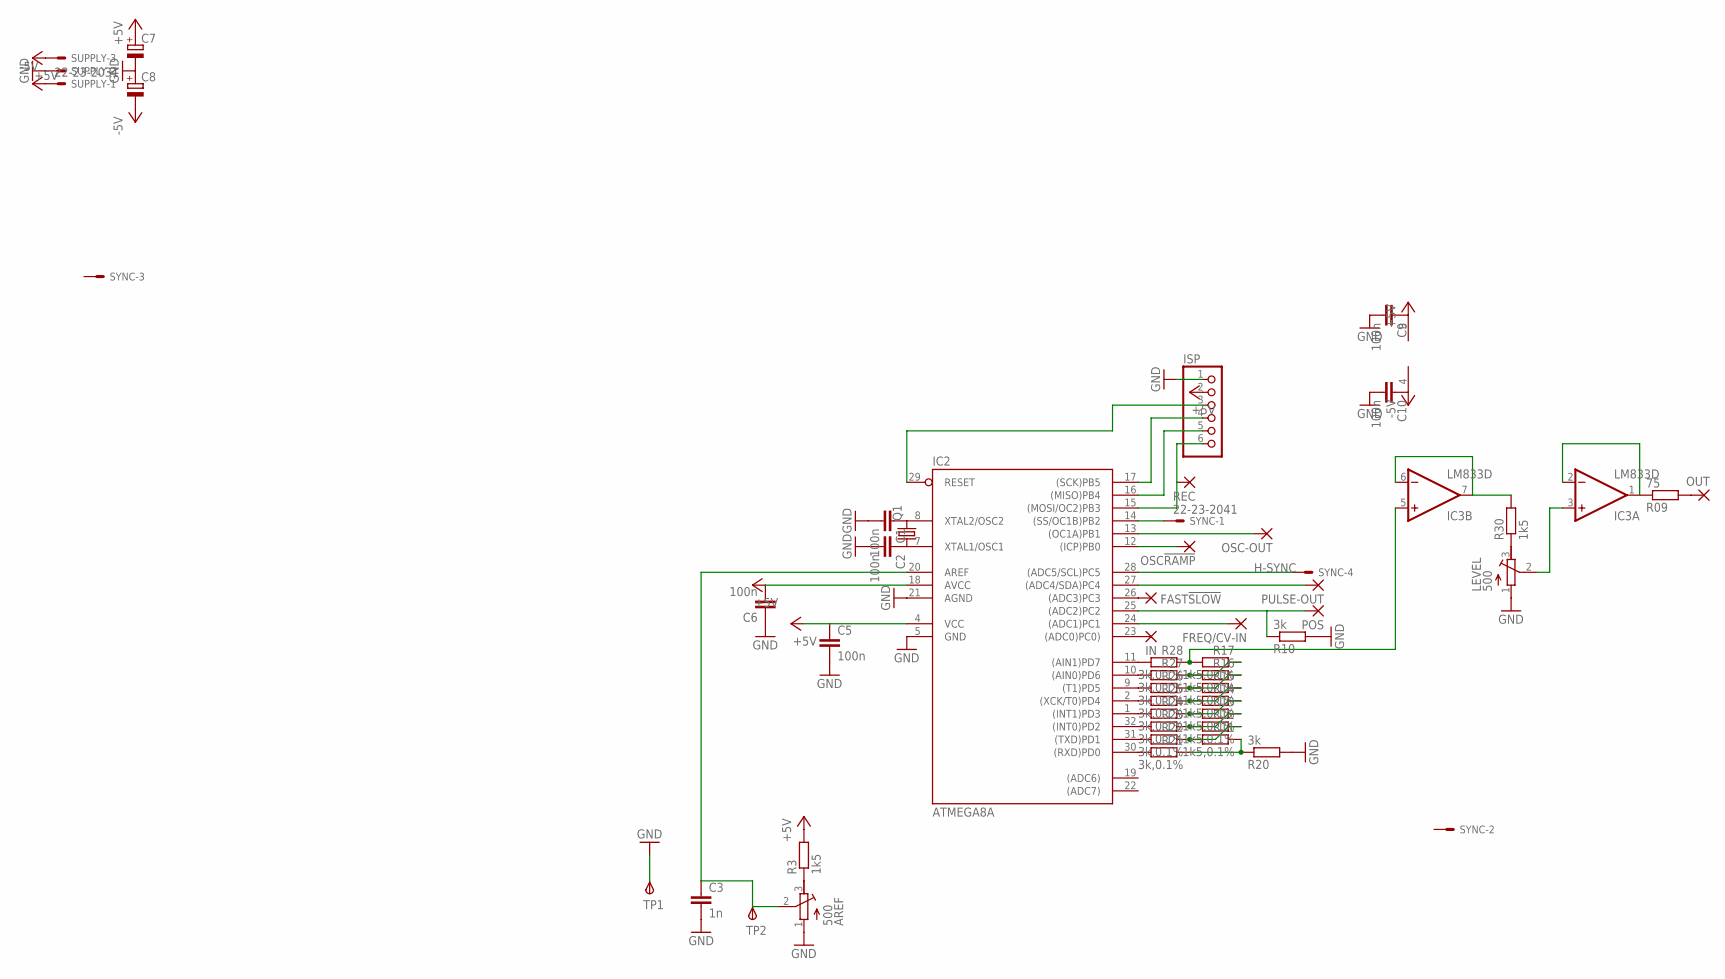
[picture p226: schematic sk911-waveshape.sch]

Parts:
AREF: 500; RTRIM64Y
C1, C2: 100n; C0805
C3: 1n; C1206
C5, C6, C9, C10: 100n; C0603
C7, C8: CPOL-EUCT6032; CT6032
FAST!SLOW: 3,17/1,1
FREQ/CV-IN: 3,17/1,1
IC2: ATMEGA8A; TQFP32-08
IC3: LM833D; SO08
IN: 3,17/1,1
ISP: PINHD-1X6; 1X06
LEVEL: 500; RTRIM64Y
OSC!RAMP: 3,17/1,1
OSC-OUT: 3,17/1,1
OUT: 3,17/1,1
POS: 3,17/1,1
PULSE-OUT: 3,17/1,1
Q1: CRYSTALHC49UP; HC49UP
R3, R30: 1k5; R1206
R09: 75; R1206
R10: 3k; R1206
R11, R12, R13, R14, R15, R16, R17: 1k5,0.1%; R0603
R20: 3k; R0603
R21, R22, R23, R24, R25, R26, R27, R28: 3k,0.1%; R0603
REC: 3,17/1,1
SUPPLY: 22-23-2031
SYNC: 22-23-2041
TP1, TP2: TPSPAD1-13; P1-13

Connections:
+5V: C5.1, C6.2, C7.+, C9.1, IC2.4 (VCC), IC2.18 (AVCC), IC3.8 (V+), ISP.2, R3.2, SUPPLY.3
-5V: C8.-, C10.1, IC3.4 (V-), SUPPLY.1
GND: AREF.1 (E), C1.2, C2.2, C3.2, C5.2, C6.1, C7.-, C8.+, C9.2, C10.2, IC2.5 (GND), IC2.21 (AGND), ISP.1, LEVEL.1 (E), R10.2, R20.2, SUPPLY.2, TP1.TP
H-SYNC: IC2.28 ((ADC5/SCL)PC5), SYNC.4
unnamed: C1.1, IC2.8 (XTAL2/OSC2), Q1.2
unnamed: IC2.25 ((ADC2)PC2), POS.1, R10.1
unnamed: C2.1, IC2.7 (XTAL1/OSC1), Q1.1
unnamed: IC2.31 ((TXD)PD1), R22.2
unnamed: IC2.23 ((ADC0)PC0)), IN.1
unnamed: IC2.1 ((INT1)PD3), R24.2
unnamed: IC2.2 ((XCK/T0)PD4), R25.2
unnamed: AREF.3 (A), R3.1
unnamed: FREQ/CV-IN.1, IC2.24 ((ADC1)PC1)
unnamed: IC2.29 (RESET), ISP.3
unnamed: IC2.17 ((SCK)PB5), ISP.4
unnamed: IC2.9 ((T1)PD5), R26.2
unnamed: IC2.10 ((AIN0)PD6), R27.2
unnamed: IC2.16 ((MISO)PB4), ISP.5
unnamed: IC2.15 ((MOSI/OC2)PB3), ISP.6, REC.1
unnamed: IC2.11 ((AIN1)PD7), R28.2
unnamed: IC2.30 ((RXD)PD0), R21.2
unnamed: IC2.13 ((OC1A)PB1), OSC-OUT.1
unnamed: IC2.12 ((ICP)PB0), OSC!RAMP.1
unnamed: IC2.32 ((INT0)PD2), R23.2
unnamed: R11.2, R12.1, R22.1
unnamed: R11.1, R20.1, R21.1
unnamed: R12.2, R13.1, R23.1
unnamed: R13.2, R14.1, R24.1
unnamed: R14.2, R15.1, R25.1
unnamed: R15.2, R16.1, R26.1
unnamed: R16.2, R17.1, R27.1
unnamed: IC3.5 (+IN), R17.2, R28.1
unnamed: IC3.6 (-IN), IC3.7 (OUT), R30.2
unnamed: LEVEL.3 (A), R30.1
unnamed: IC3.1 (OUT), IC3.2 (-IN), R09.1
unnamed: IC3.3 (+IN), LEVEL.2 (S)
unnamed: FAST!SLOW.1, IC2.26 ((ADC3)PC3)
unnamed: IC2.27 ((ADC4/SDA)PC4), PULSE-OUT.1
unnamed: OUT.1, R09.2
unnamed: AREF.2 (S), C3.1, IC2.20 (AREF), TP2.TP
ODD!EVEN: IC2.14 ((SS/OC1B)PB2), SYNC.1

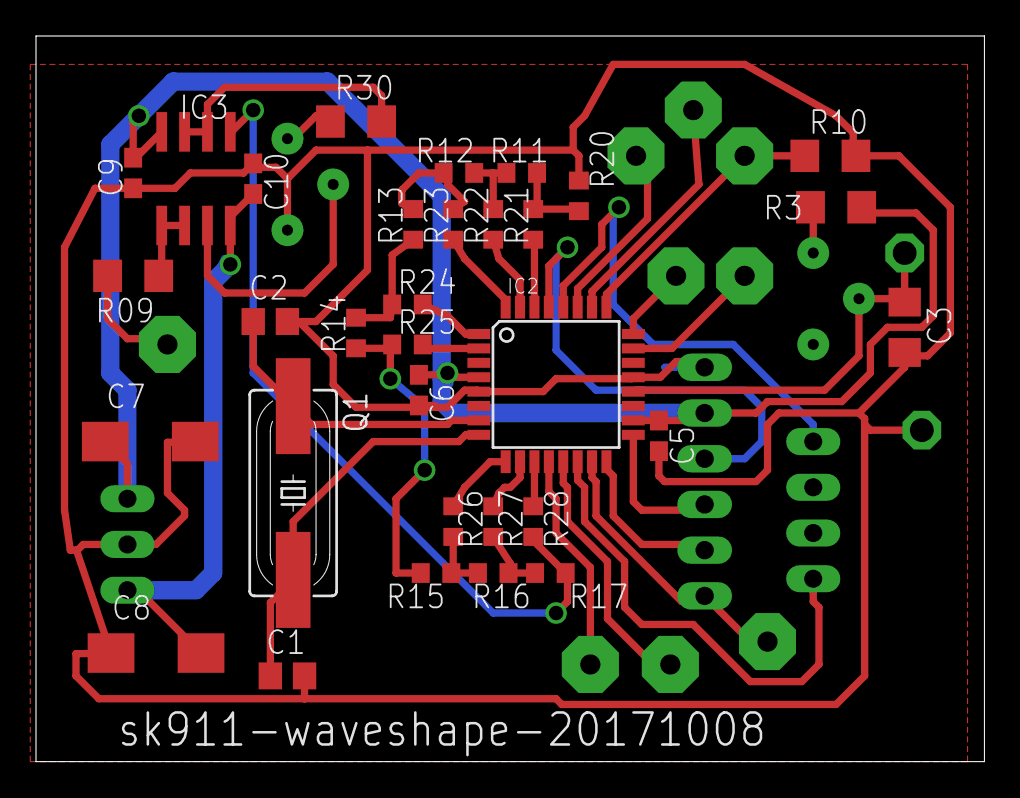
[picture p227: board sk911-waveshape.brd from above]

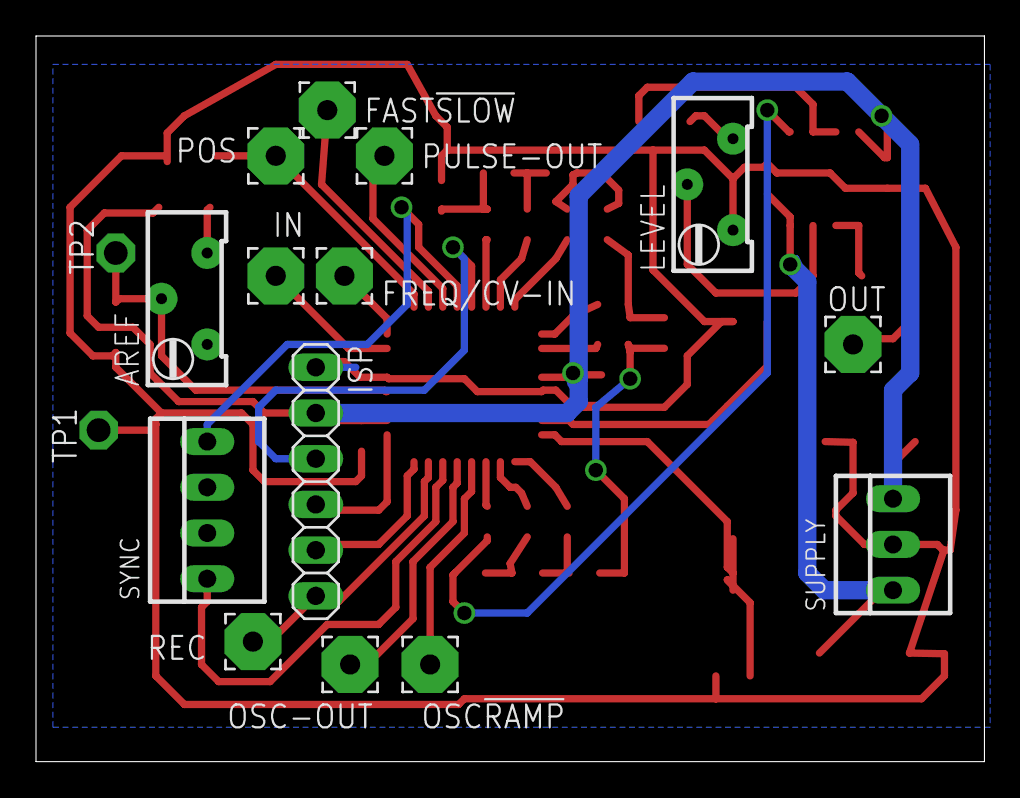
[picture p228: board sk911-waveshape.brd from below]

Board: 2 copper layers, 52.7 x 40.3 mm, 48 parts (16 on the bottom side), 41 nets.
