mirdej/synkie/eagle/sk720-step-sequencer/sk720-pots.brd

## EAGLE design eagle/sk720-step-sequencer/sk720-pots.brd (2017-11-06)

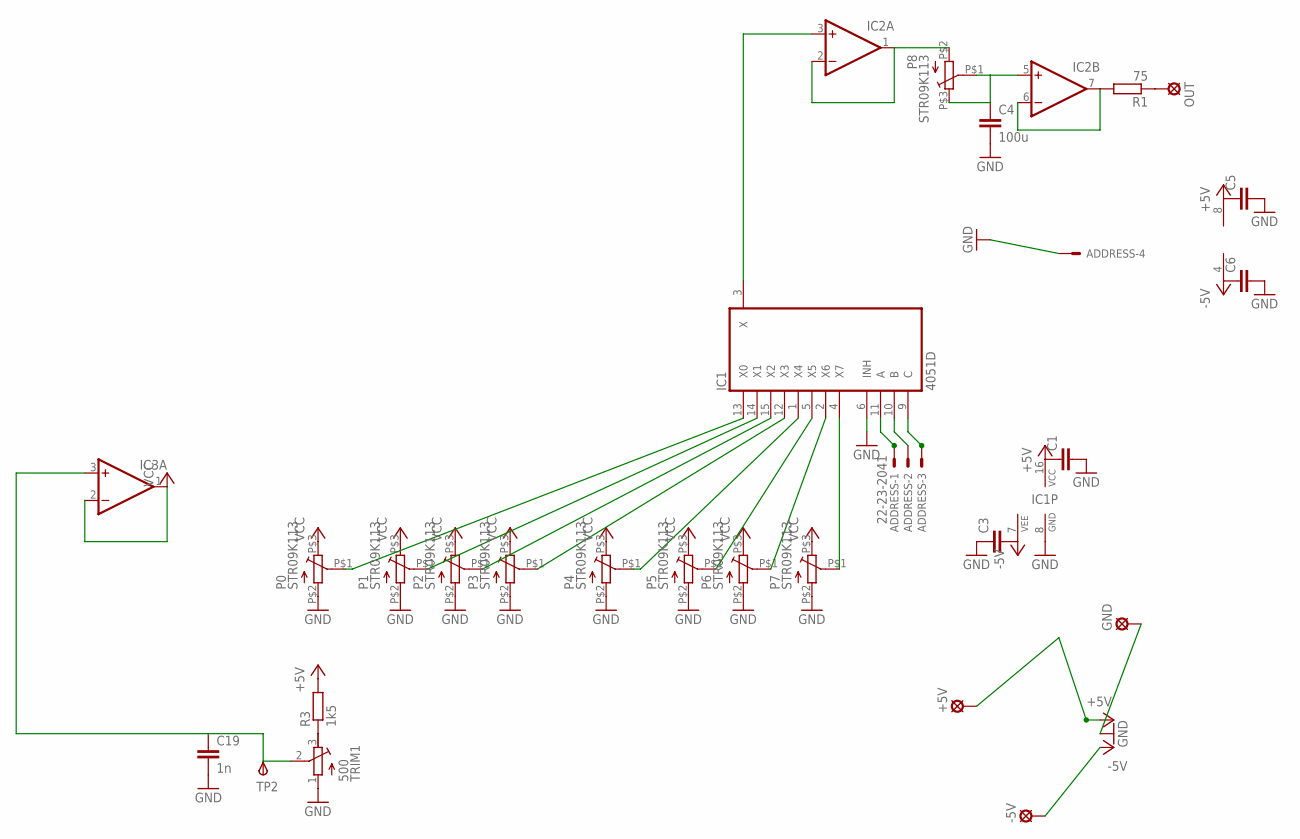
[picture p229: schematic sk720-pots.sch]

Parts:
+5V: LSP13
-5V: LSP13
ADDRESS: 22-23-2041
C1, C3, C5, C6: C-EUC0603; C0603
C4: 100u; C1608
C19: 1n; C1206
GND: LSP13
IC1: 4051D; SO16
IC2, IC3: DUAL_OPAMPD; SO08
OUT: LSP13
P0, P1, P2, P3, P4, P5, P6, P7, P8: STR09K113
R1: 75; R1206
R3: 1k5; R1206
TP2: TPSPAD1-13; P1-13
TRIM1: 500; RTRIM64Y

Connections:
+5V: +5V.MP, C1.1, C5.1, IC1.16 (VCC), IC2.8 (V+), R3.2
-5V: -5V.MP, C3.2, C6.1, IC1.7 (VEE), IC2.4 (V-)
GND: ADDRESS.4, C1.2, C3.1, C4.2, C5.2, C6.2, C19.2, GND.MP, IC1.6 (INH), IC1.8 (GND), P0.P$2 (ANFANG), P1.P$2 (ANFANG), P2.P$2 (ANFANG), P3.P$2 (ANFANG), P4.P$2 (ANFANG), P5.P$2 (ANFANG), P6.P$2 (ANFANG), P7.P$2 (ANFANG), TRIM1.1 (E)
unnamed: IC1.1 (X4), P4.P$1 (SCHLEIFER)
unnamed: IC1.5 (X5), P5.P$1 (SCHLEIFER)
unnamed: IC1.2 (X6), P6.P$1 (SCHLEIFER)
unnamed: IC1.4 (X7), P7.P$1 (SCHLEIFER)
unnamed: OUT.MP, R1.1
unnamed: ADDRESS.1, IC1.11 (A)
unnamed: R3.1, TRIM1.3 (A)
unnamed: IC2.6 (-IN), IC2.7 (OUT), R1.2
unnamed: IC1.3 (X), IC2.3 (+IN)
unnamed: IC2.1 (OUT), IC2.2 (-IN), P8.P$2 (ANFANG)
unnamed: C4.1, IC2.5 (+IN), P8.P$1 (SCHLEIFER), P8.P$3 (ENDE)
unnamed: ADDRESS.2, IC1.10 (B)
unnamed: C19.1, IC3.3 (+IN), TP2.TP, TRIM1.2 (S)
unnamed: IC1.13 (X0), P0.P$1 (SCHLEIFER)
unnamed: IC1.14 (X1), P1.P$1 (SCHLEIFER)
unnamed: IC1.15 (X2), P2.P$1 (SCHLEIFER)
unnamed: IC1.12 (X3), P3.P$1 (SCHLEIFER)
unnamed: ADDRESS.3, IC1.9 (C)
V+: IC3.8 (V+)
V-: IC3.4 (V-)
VCC: IC3.1 (OUT), IC3.2 (-IN), P0.P$3 (ENDE), P1.P$3 (ENDE), P2.P$3 (ENDE), P3.P$3 (ENDE), P4.P$3 (ENDE), P5.P$3 (ENDE), P6.P$3 (ENDE), P7.P$3 (ENDE)

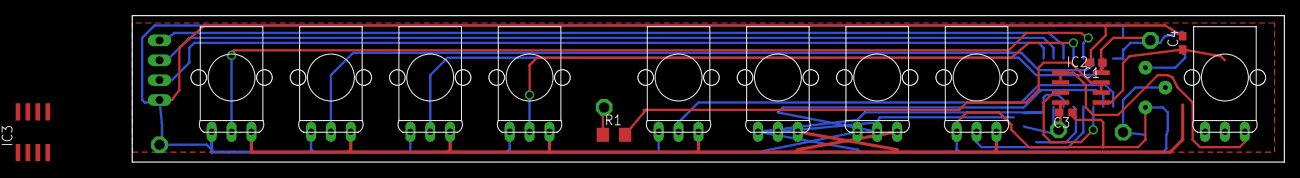
[picture p230: board sk720-pots.brd from above]

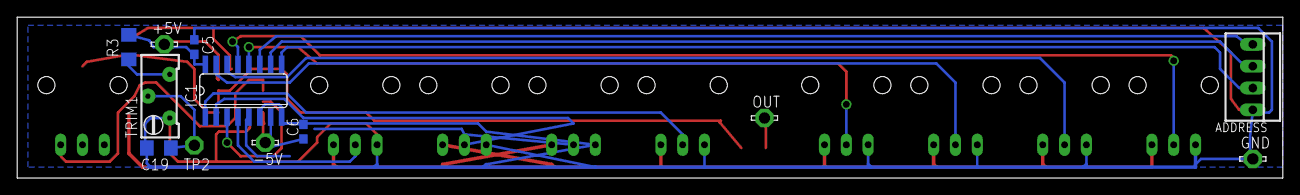
[picture p231: board sk720-pots.brd from below]

Board: 2 copper layers, 147.3 x 18.7 mm, 27 parts (12 on the bottom side), 22 nets.
