mirdej/synkie/eagle/sk720-step-sequencer/sk720-8btns.brd

## EAGLE design eagle/sk720-step-sequencer/sk720-8btns.brd (2017-11-06)

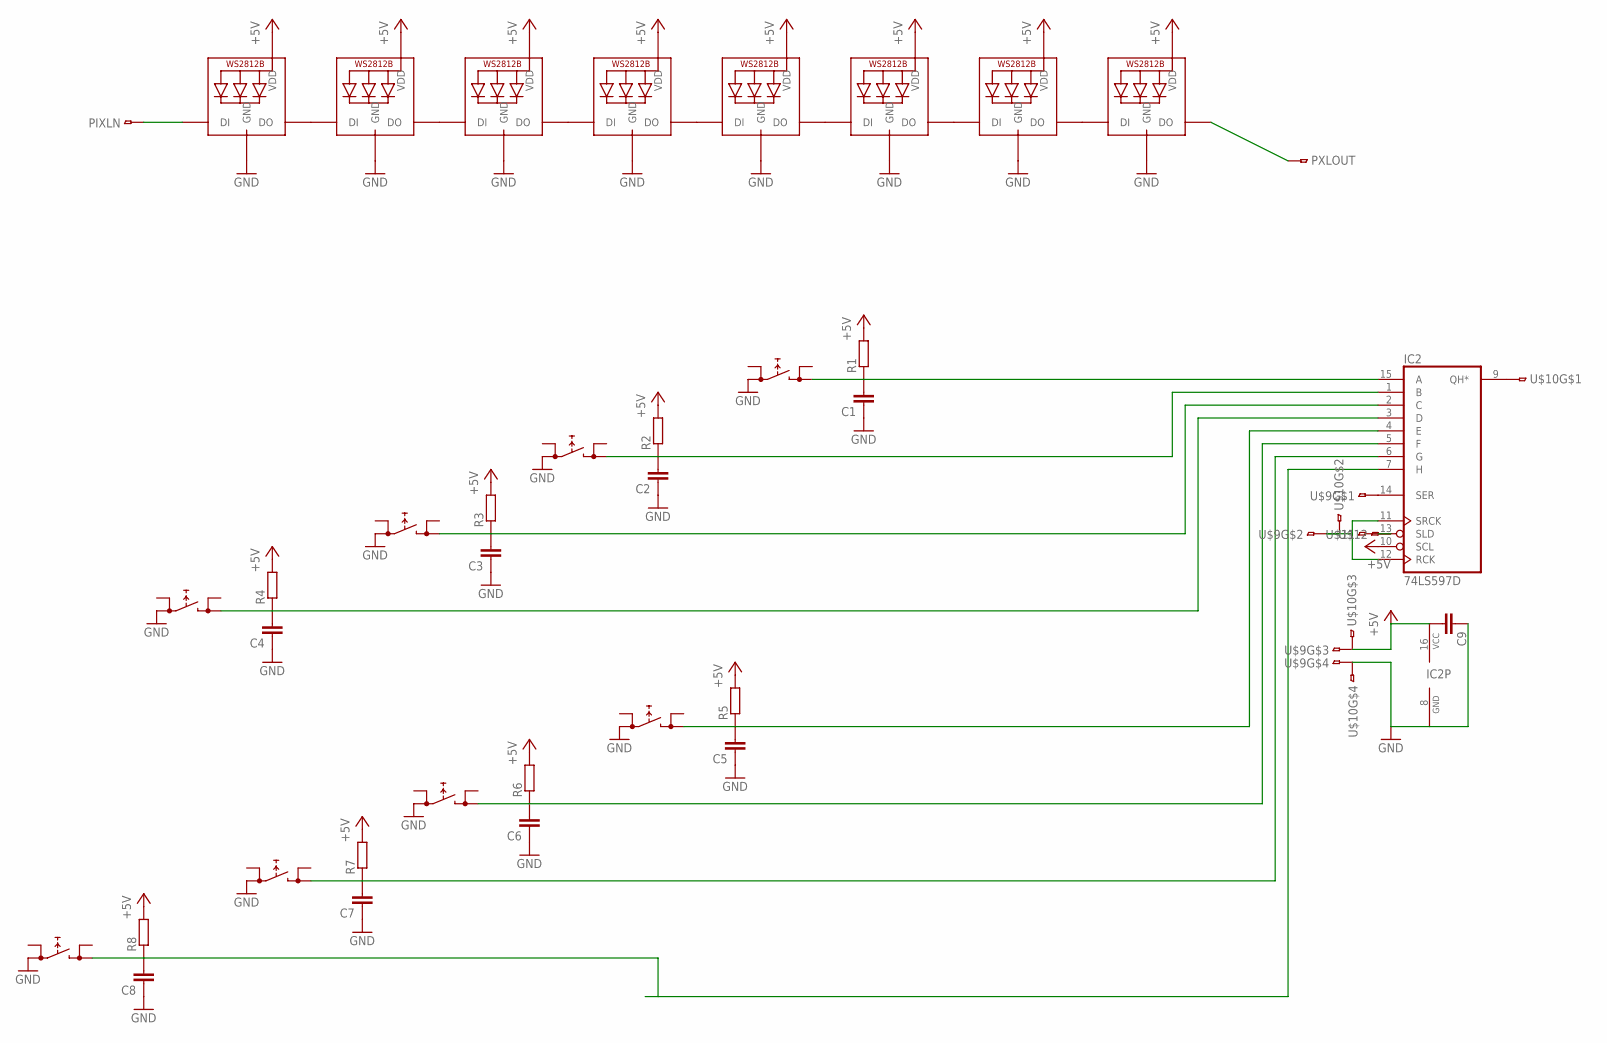
[picture p232: schematic sk720-8btns.sch]

Parts:
C1, C2, C3, C4, C5, C6, C7, C8: C-EUC0603; C0603
C9: C-EUC1206; C1206
IC2: 74LS597D; SO16
LED1, LED2, LED3, LED4, LED5, LED6, LED7, LED8: WS2812B5050; WS2812B
PIXLN: 1PINSMD
PXLOUT: 1PINSMD
R1, R2, R3, R4, R5, R6, R7, R8: R-EU_R1206; R1206
U$1, U$2, U$3, U$4, U$5, U$6, U$7, U$8: PRINTTASTER_SMDALPS-SKQ; SKQGAKE010
U$9, U$10: 4PIN-SMD; 4PIN-SMD-2.54
U$11, U$12: 1PINSMD

Connections:
+5V: C9.2, IC2.10 (SCL), IC2.16 (VCC), LED1.1-VDD (VDD), LED2.1-VDD (VDD), LED3.1-VDD (VDD), LED4.1-VDD (VDD), LED5.1-VDD (VDD), LED6.1-VDD (VDD), LED7.1-VDD (VDD), LED8.1-VDD (VDD), R1.2, R2.2, R3.2, R4.2, R5.2, R6.2, R7.2, R8.2, U$9.3, U$10.3
CLK: IC2.11 (SRCK), IC2.12 (RCK), U$9.2, U$10.2
GND: C1.1, C2.1, C3.1, C4.1, C5.1, C6.1, C7.1, C8.1, C9.1, IC2.8 (GND), LED1.3-GND (GND), LED2.3-GND (GND), LED3.3-GND (GND), LED4.3-GND (GND), LED5.3-GND (GND), LED6.3-GND (GND), LED7.3-GND (GND), LED8.3-GND (GND), U$1.2 (0), U$2.2 (0), U$3.2 (0), U$4.2 (0), U$5.2 (0), U$6.2 (0), U$7.2 (0), U$8.2 (0), U$9.4, U$10.4
LATCH: IC2.13 (SLD), U$11.2, U$12.2
MISO: IC2.9 (QH*), U$10.1
unnamed: C1.2, IC2.15 (A), R1.1, U$1.4 (1)
unnamed: C2.2, IC2.1 (B), R2.1, U$2.4 (1)
unnamed: C3.2, IC2.2 (C), R3.1, U$3.4 (1)
unnamed: C4.2, IC2.3 (D), R4.1, U$4.4 (1)
unnamed: C5.2, IC2.4 (E), R5.1, U$5.4 (1)
unnamed: C6.2, IC2.5 (F), R6.1, U$6.4 (1)
unnamed: C7.2, IC2.6 (G), R7.1, U$7.4 (1)
unnamed: IC2.14 (SER), U$9.1
unnamed: LED1.2-DOUT (DO), LED2.4-DIN (DI)
unnamed: C8.2, IC2.7 (H), R8.1, U$8.4 (1)
unnamed: LED2.2-DOUT (DO), LED3.4-DIN (DI)
unnamed: LED3.2-DOUT (DO), LED4.4-DIN (DI)
unnamed: LED4.2-DOUT (DO), LED5.4-DIN (DI)
unnamed: LED5.2-DOUT (DO), LED6.4-DIN (DI)
unnamed: LED6.2-DOUT (DO), LED7.4-DIN (DI)
unnamed: LED7.2-DOUT (DO), LED8.4-DIN (DI)
PXLIN: LED1.4-DIN (DI), PIXLN.2
PXLOUT: LED8.2-DOUT (DO), PXLOUT.2

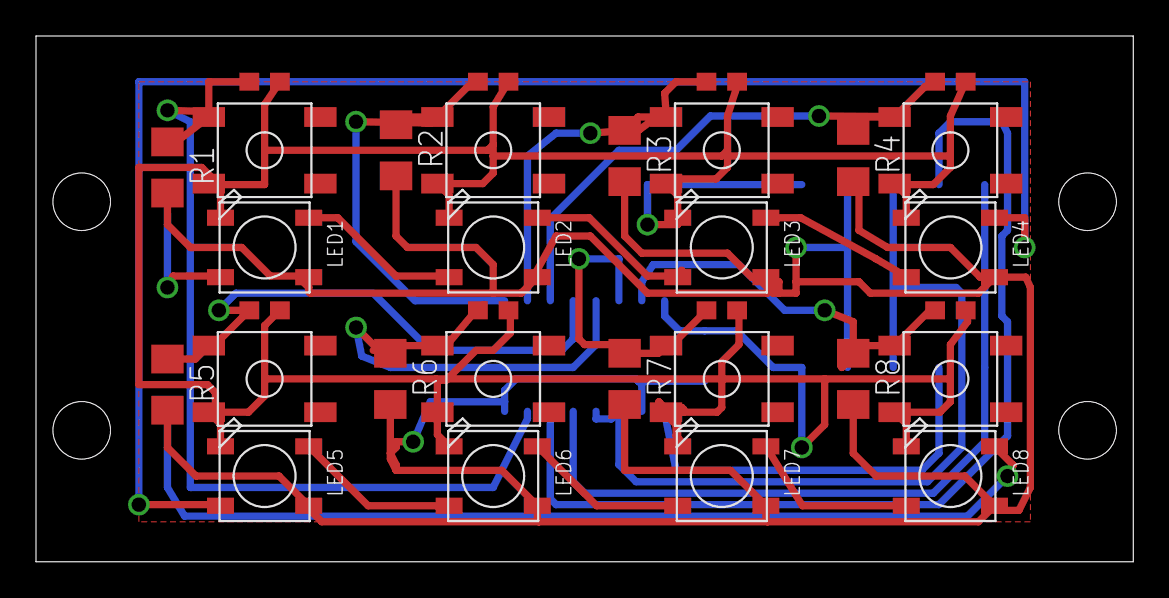
[picture p233: board sk720-8btns.brd from above]

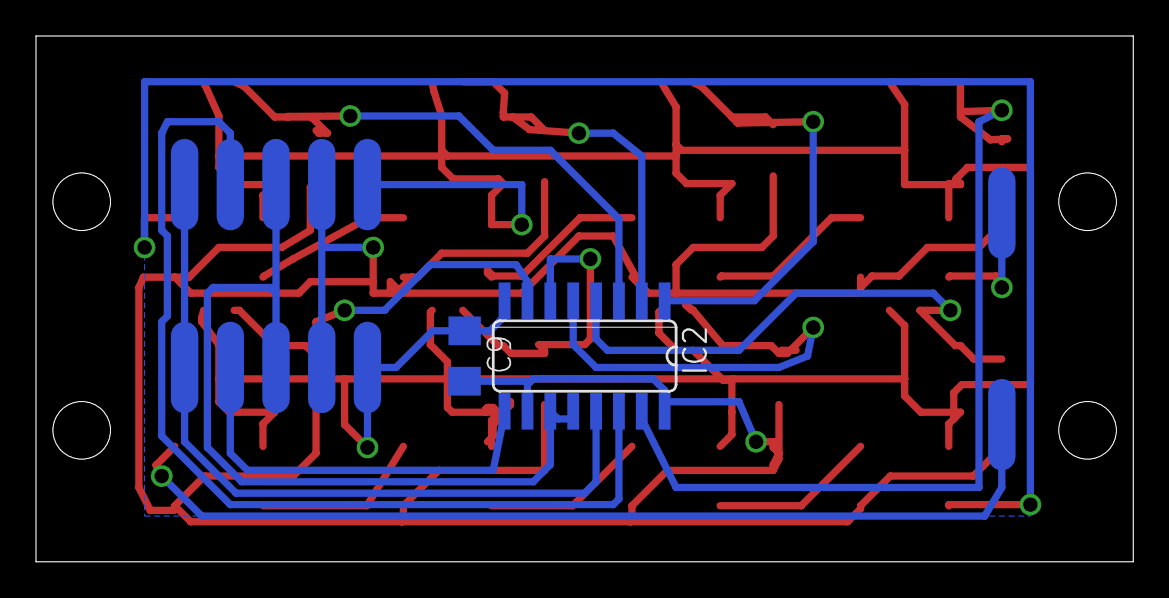
[picture p234: board sk720-8btns.brd from below]

Board: 2 copper layers, 61.0 x 29.2 mm, 40 parts (8 on the bottom side), 23 nets.
