mirdej/synkie/eagle/sk900-audio-out/sk900-audio-out.brd

## EAGLE design eagle/sk900-audio-out/sk900-audio-out.brd (2017-10-27)

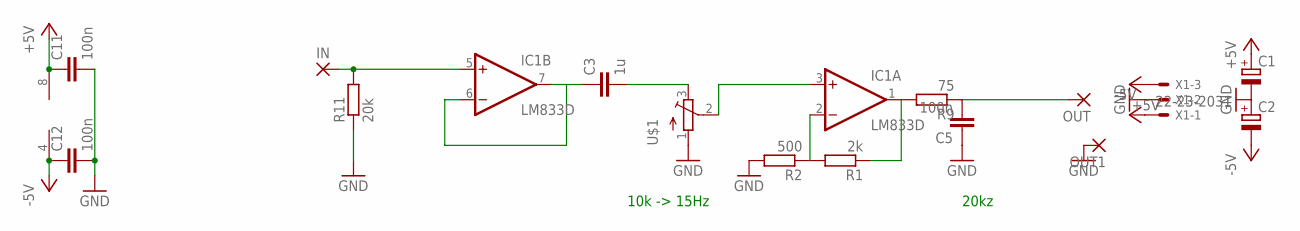
[picture p235: schematic sk900-audio-out.sch]

Parts:
C1, C2: CPOL-EUCT6032; CT6032
C3: 1u; C1206
C5, C11, C12: 100n; C1206
IC1: LM833D; SO08
IN: 3,17/1,1
OUT, OUT1: 3,17/1,1
R1: 2k; R1206
R2: 500; R1206
R9: 75; R1206
R11: 20k; R1206
U$1: 10k; ALPS_RK09K111_H
X1: 22-23-2031

Connections:
+5V: C1.+, C11.1, IC1.8 (V+), X1.3
-5V: C2.-, C12.1, IC1.4 (V-), X1.1
GND: C1.-, C2.+, C5.1, C11.2, C12.2, OUT1.1, R2.2, R11.1, U$1.1 (S), X1.2
unnamed: IC1.5 (+IN), IN.1, R11.2
unnamed: C3.2, U$1.3 (E)
unnamed: C3.1, IC1.6 (-IN), IC1.7 (OUT)
unnamed: IC1.3 (+IN), U$1.2 (W)
unnamed: IC1.1 (OUT), R1.1, R9.2
unnamed: C5.2, OUT.1, R9.1
unnamed: IC1.2 (-IN), R1.2, R2.1

Notes on the sheet:
10k -> 15Hz
20kz

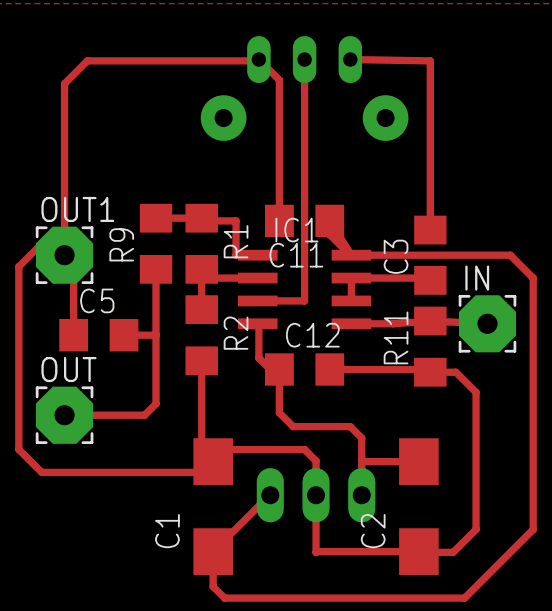
[picture p236: board sk900-audio-out.brd from above]

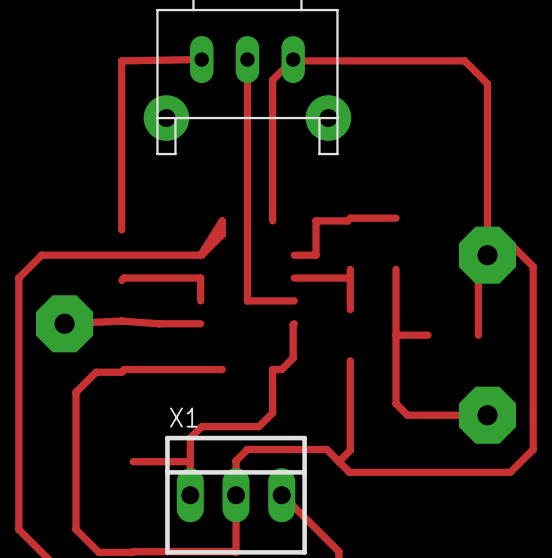
[picture p237: board sk900-audio-out.brd from below]

Board: 2 copper layers, 16 parts (2 on the bottom side), 10 nets.
