mirdej/synkie/eagle/sk020-bypass/sk020-bypass.brd

## EAGLE design eagle/sk020-bypass/sk020-bypass.brd (2017-10-27)

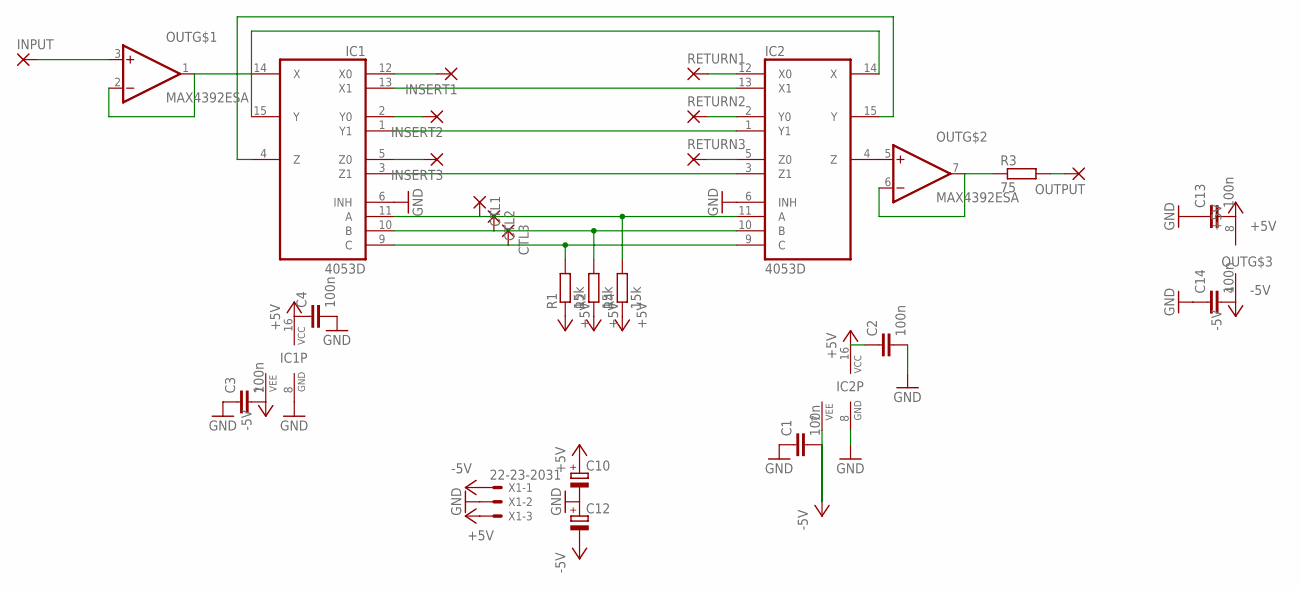
[picture p238: schematic sk020-bypass.sch]

Parts:
C1, C2, C3, C4, C13, C14: 100n; C0805
C10, C12: CPOL-EUSMCB; SMC_B
CTL1, CTL2, CTL3: 3,17/1,1
IC1, IC2: 4053D; SO16
INPUT: 3,17/1,1
INSERT1, INSERT2, INSERT3: 3,17/1,1
OUT: MAX4392ESA; SO08
OUTPUT: 3,17/1,1
R1, R2, R4: 15k; R1206
R3: 75; R1206
RETURN1, RETURN2, RETURN3: 3,17/1,1
X1: 22-23-2031

Connections:
+5V: C2.1, C4.1, C10.+, C13.2, IC1.16 (VCC), IC2.16 (VCC), OUT.8 (+5V), R1.1, R2.1, R4.1, X1.3
-5V: C1.2, C3.2, C12.-, C14.2, IC1.7 (VEE), IC2.7 (VEE), OUT.4 (-5V), X1.1
GND: C1.1, C2.2, C3.1, C4.2, C10.-, C12.+, C13.1, C14.1, IC1.6 (INH), IC1.8 (GND), IC2.6 (INH), IC2.8 (GND), X1.2
unnamed: IC1.12 (X0), INSERT1.1
unnamed: INPUT.1, OUT.3 (+IN)
unnamed: IC1.15 (Y), IC2.14 (X)
unnamed: IC1.2 (Y0), INSERT2.1
unnamed: IC1.5 (Z0), INSERT3.1
unnamed: IC1.4 (Z), IC2.15 (Y)
unnamed: IC2.12 (X0), RETURN1.1
unnamed: IC1.14 (X), OUT.1 (OUT), OUT.2 (-IN)
unnamed: OUTPUT.1, R3.2
unnamed: IC2.4 (Z), OUT.5 (+IN)
unnamed: IC2.2 (Y0), RETURN2.1
unnamed: IC2.5 (Z0), RETURN3.1
unnamed: IC1.13 (X1), IC2.13 (X1)
unnamed: IC1.1 (Y1), IC2.1 (Y1)
unnamed: IC1.3 (Z1), IC2.3 (Z1)
unnamed: CTL1.1, IC1.11 (A), IC2.11 (A), R4.2
unnamed: CTL2.1, IC1.10 (B), IC2.10 (B), R2.2
unnamed: CTL3.1, IC1.9 (C), IC2.9 (C), R1.2
unnamed: OUT.6 (-IN), OUT.7 (OUT), R3.1

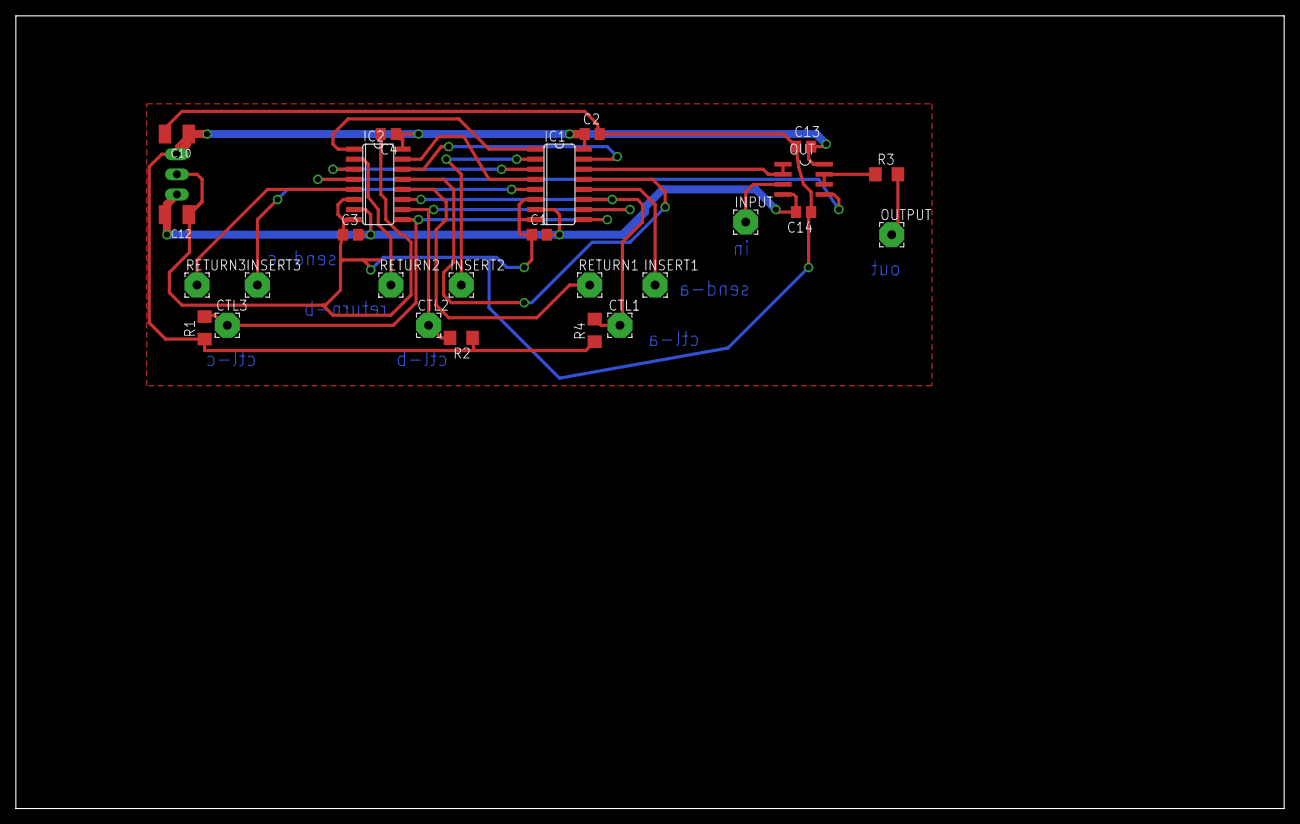
[picture p239: board sk020-bypass.brd from above]

Board: 2 copper layers, 160.0 x 100.0 mm, 27 parts (1 on the bottom side), 22 nets.
