mirdej/synkie/eagle/sk530-vco/sk530-vco.brd

## EAGLE design eagle/sk530-vco/sk530-vco.brd (2017-08-04)

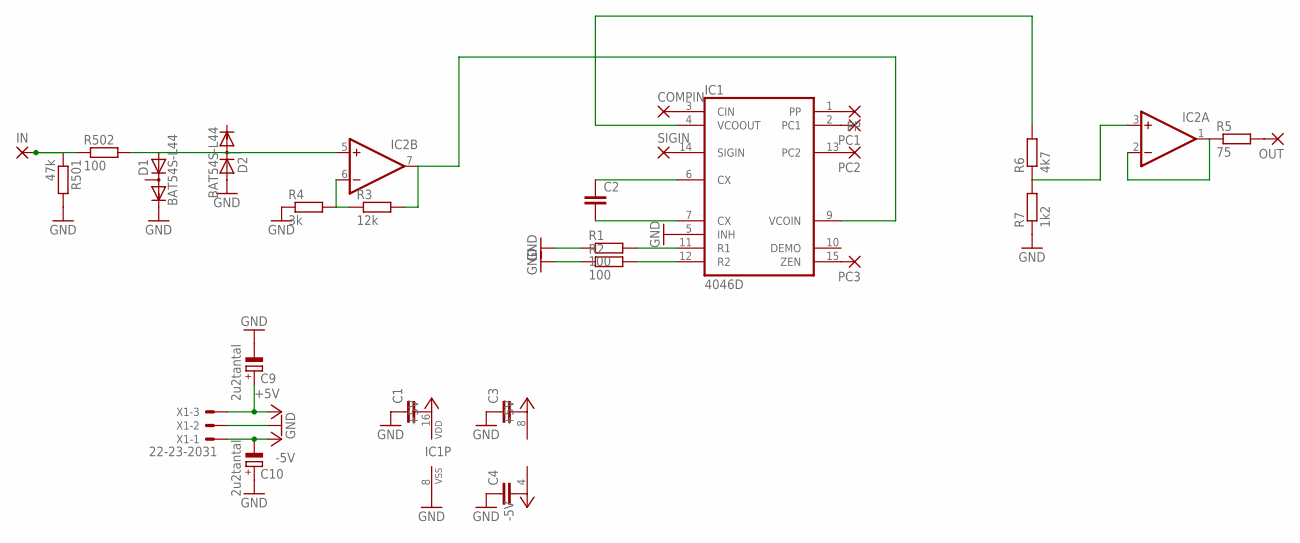
[picture p240: schematic sk530-vco.sch]

Parts:
C1, C2, C3, C4: C-EUC1206; C1206
C9, C10: 2u2tantal; CT3528
COMPIN: 3,17/1,1
D1, D2: BAT54S-L44; SOT23
IC1: 4046D; SO16
IC2: DUAL_OPAMPD; SO08
IN: 3,17/1,1
OUT: 3,17/1,1
PC1, PC2, PC3: 3,17/1,1
PP: 3,17/1,1
R1, R2, R502: 100; R1206
R3: 12k; R1206
R4: 3k; R1206
R5: 75; R1206
R6: 4k7; R1206
R7: 1k2; R1206
R501: 47k; R1206
SIGIN: 3,17/1,1
X1: 22-23-2031

Connections:
+5V: C1.2, C3.2, C9.+, IC1.16 (VDD), IC2.8 (V+), X1.3
-5V: C4.2, C10.-, IC2.4 (V-), X1.1
GND: C1.1, C3.1, C4.1, C9.-, C10.+, D1.2 (C), D2.1 (A), IC1.5 (INH), IC1.8 (VSS), R1.1, R2.1, R4.1, R7.1, R501.2, X1.2
unnamed: IC1.2 (PC1), PC1.1
unnamed: OUT.1, R5.2
unnamed: IC1.1 (PP), PP.1
unnamed: IC1.13 (PC2), PC2.1
unnamed: IC1.15 (ZEN), PC3.1
unnamed: IC1.14 (SIGIN), SIGIN.1
unnamed: COMPIN.1, IC1.3 (CIN)
unnamed: C2.1, IC1.6 (CX)
unnamed: C2.2, IC1.7 (CX)
unnamed: IN.1, R501.1, R502.1
unnamed: D1.1 (A), D2.3 (AC), IC2.5 (+IN), R502.2
unnamed: IC1.11 (R1), R1.2
unnamed: IC1.12 (R2), R2.2
unnamed: IC2.6 (-IN), R3.1, R4.2
unnamed: IC1.9 (VCOIN), IC2.7 (OUT), R3.2
unnamed: IC2.1 (OUT), IC2.2 (-IN), R5.1
unnamed: IC1.4 (VCOOUT), R6.2
unnamed: IC2.3 (+IN), R6.1, R7.2

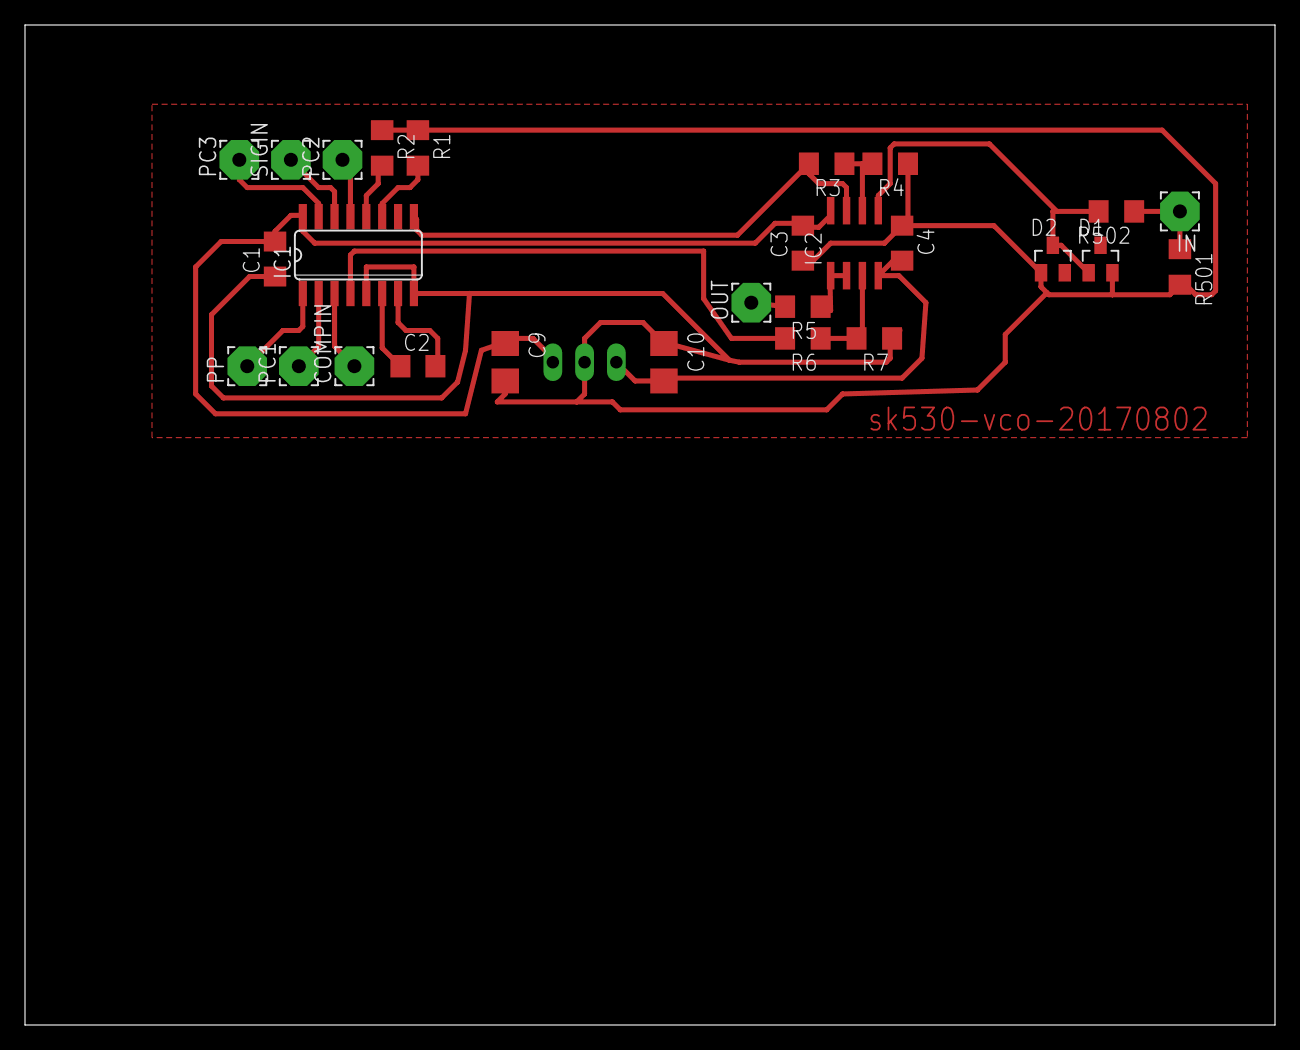
[picture p241: board sk530-vco.brd from above]

Board: 2 copper layers, 100.0 x 80.0 mm, 28 parts (1 on the bottom side), 21 nets.
