mirdej/synkie/eagle/sk302-samplehold/sk302-samplehold.brd

## EAGLE design eagle/sk302-samplehold/sk302-samplehold.brd (2017-08-04)

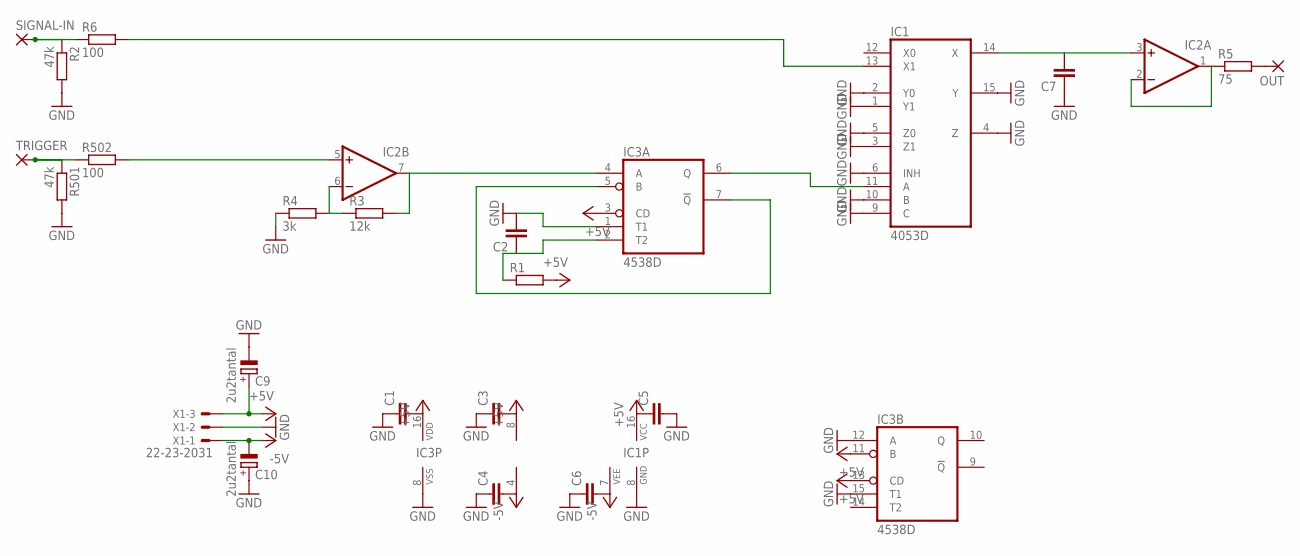
[picture p242: schematic sk302-samplehold.sch]

Parts:
C1, C2, C3, C4, C5, C6, C7: C-EUC1206; C1206
C9, C10: 2u2tantal; CT3528
IC1: 4053D; SO16
IC2: DUAL_OPAMPD; SO08
IC3: 4538D; SO16
OUT: 3,17/1,1
R1: R-EU_R1206; R1206
R2, R501: 47k; R1206
R3: 12k; R1206
R4: 3k; R1206
R5: 75; R1206
R6, R502: 100; R1206
SIGNAL-IN: 3,17/1,1
TRIGGER: 3,17/1,1
X1: 22-23-2031

Connections:
+5V: C1.2, C3.2, C5.1, C9.+, IC1.16 (VCC), IC2.8 (V+), IC3.3 (CD), IC3.11 (B), IC3.13 (CD), IC3.16 (VDD), R1.2, X1.3
-5V: C4.2, C6.2, C10.-, IC1.7 (VEE), IC2.4 (V-), X1.1
GND: C1.1, C2.2, C3.1, C4.1, C5.2, C6.1, C7.1, C9.-, C10.+, IC1.1 (Y1), IC1.2 (Y0), IC1.3 (Z1), IC1.4 (Z), IC1.5 (Z0), IC1.6 (INH), IC1.8 (GND), IC1.9 (C), IC1.10 (B), IC1.15 (Y), IC3.1 (T1), IC3.8 (VSS), IC3.12 (A), IC3.15 (T1), R2.2, R4.1, R501.2, X1.2
unnamed: IC2.7 (OUT), IC3.4 (A), R3.2
unnamed: OUT.1, R5.2
unnamed: C2.1, IC3.2 (T2), R1.1
unnamed: R2.1, R6.1, SIGNAL-IN.1
unnamed: IC1.13 (X1), R6.2
unnamed: C7.2, IC1.14 (X), IC2.3 (+IN)
unnamed: IC1.11 (A), IC3.6 (Q)
unnamed: R501.1, R502.1, TRIGGER.1
unnamed: IC2.5 (+IN), R502.2
unnamed: IC2.6 (-IN), R3.1, R4.2
unnamed: IC2.1 (OUT), IC2.2 (-IN), R5.1
unnamed: IC3.5 (B), IC3.7 (!Q)

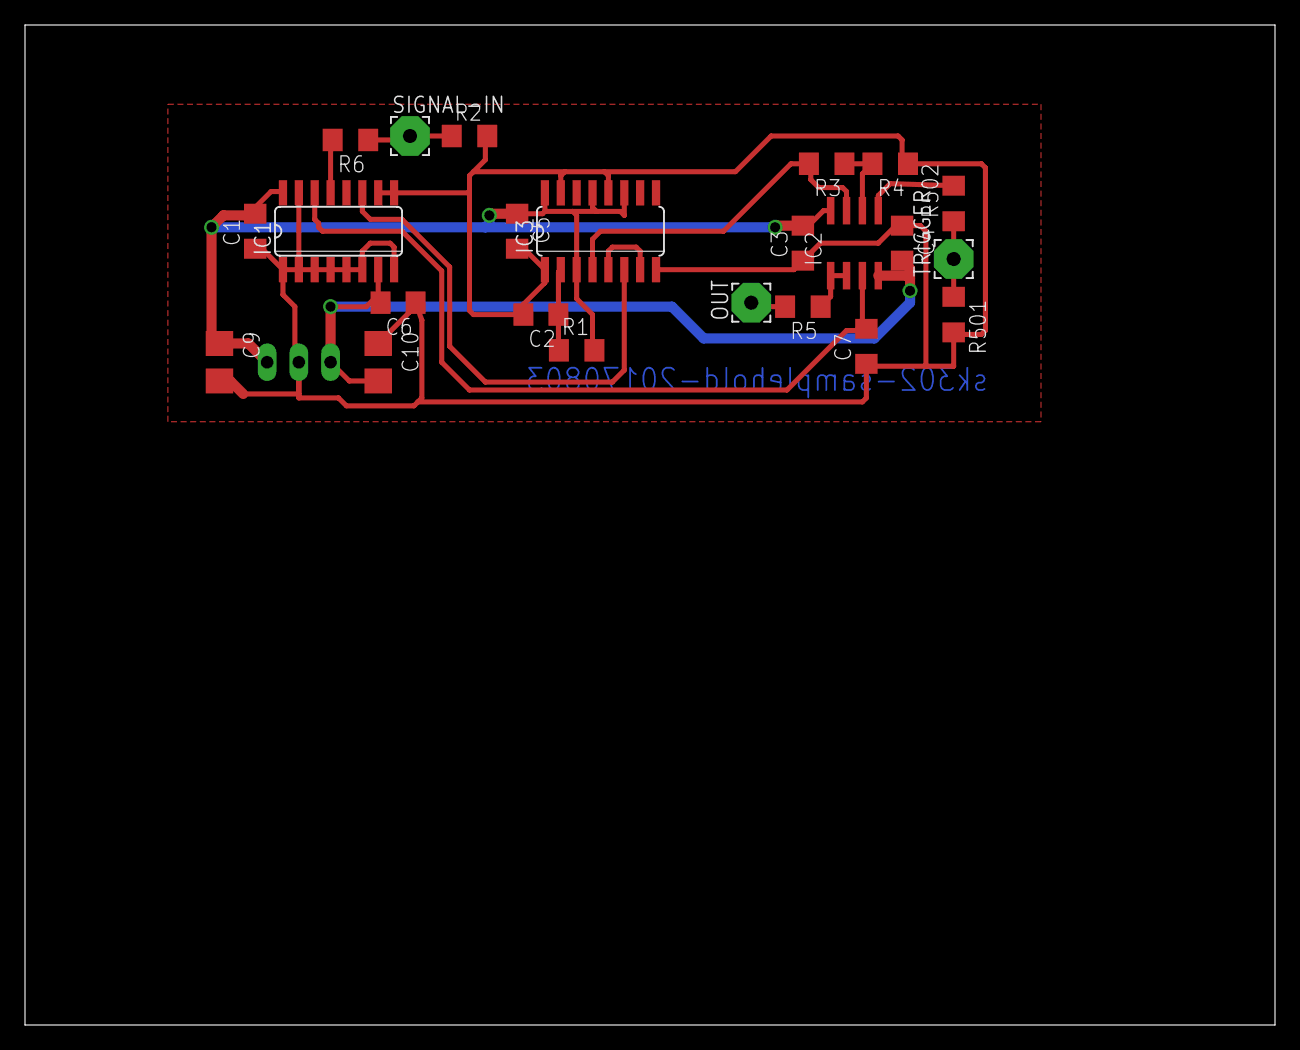
[picture p243: board sk302-samplehold.brd from above]

Board: 2 copper layers, 100.0 x 80.0 mm, 24 parts (1 on the bottom side), 15 nets.
