mirdej/synkie/eagle/sk810-subcarrier/sk810-subcarrier.brd

## EAGLE design eagle/sk810-subcarrier/sk810-subcarrier.brd (2017-08-04)

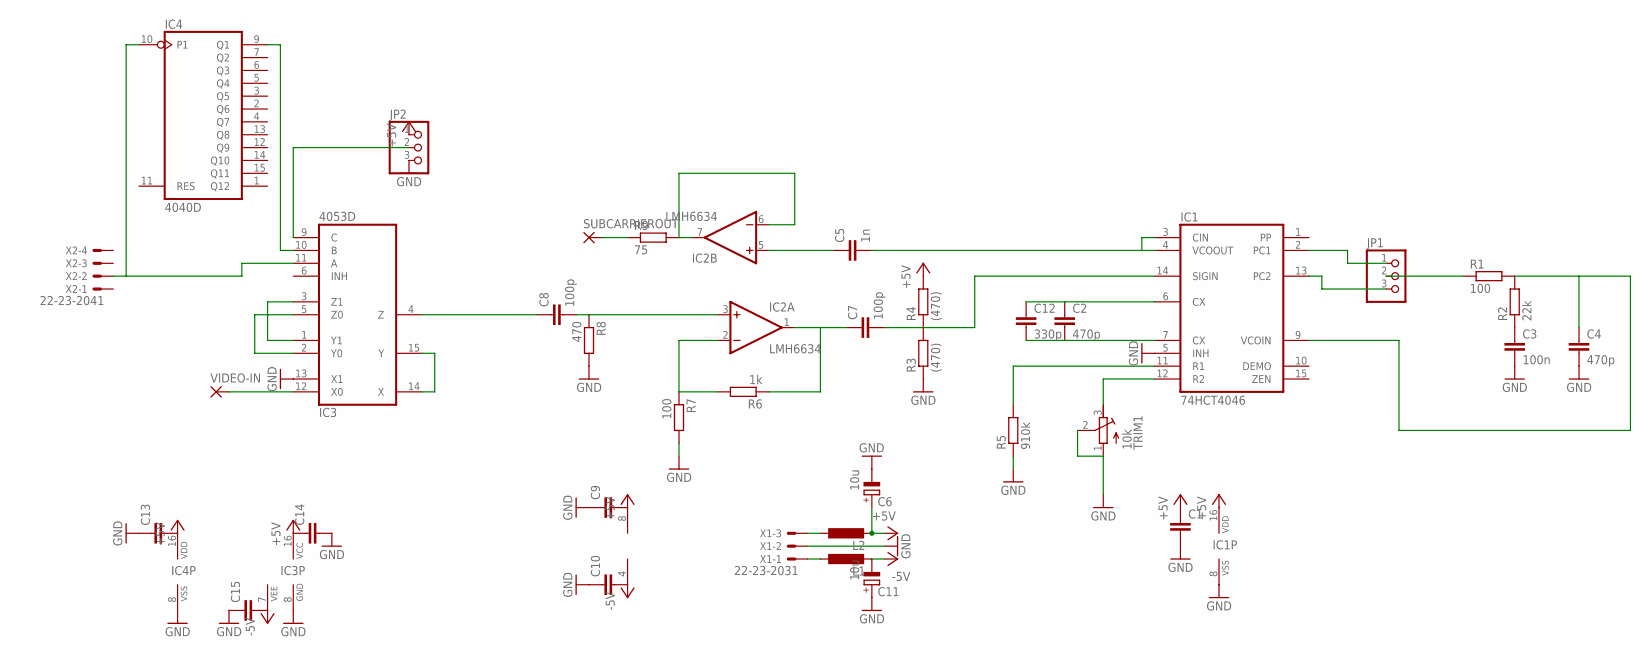
[picture p244: schematic sk810-subcarrier.sch]

Parts:
C1, C9, C10: C-EUC0603; C0603
C2, C4: 470p; C1206
C3: 100n; C1206
C5: 1n; C1206
C6, C11: 10u; CT3528
C7, C8: 100p; C1206
C12: 330p; C1206
C13, C14, C15: C-EUC1206; C1206
IC1: 74HCT4046; SO16
IC2: LMH6634; SO08
IC3: 4053D; SO16
IC4: 4040D; SO16
JP1, JP2: PINHD-1X3; 1X03
L1, L2: L-EUL5038P; L5038P
R1, R7: 100; R1206
R2: 22k; R1206
R3, R4: (470); R1206
R5: 910k; R1206
R6: 1k; R1206
R8: 470; R1206
R9: 75; R1206
SUBCARRIEROUT: 3,17/1,1
TRIM1: 10k; RTRIM64Y
VIDEO-IN: 3,17/1,1
X1: 22-23-2031
X2: 22-23-2041

Connections:
+5V: C1.1, C6.+, C9.2, C13.2, C14.1, IC1.16 (VDD), IC2.8 (V+), IC3.16 (VCC), IC4.16 (VDD), JP2.1, L2.2, R4.2
-5V: C10.2, C11.-, C15.2, IC2.4 (V-), IC3.7 (VEE), L1.2
GND: C1.2, C3.2, C4.2, C6.-, C9.1, C10.1, C11.+, C13.1, C14.2, C15.1, IC1.5 (INH), IC1.8 (VSS), IC3.8 (GND), IC3.13 (X1), IC4.8 (VSS), JP2.3, R3.1, R5.1, R7.2, R8.2, TRIM1.1 (E), TRIM1.2 (S), X1.2
unnamed: C2.1, C12.1, IC1.6 (CX)
unnamed: C2.2, C12.2, IC1.7 (CX)
unnamed: IC1.11 (R1), R5.2
unnamed: IC1.12 (R2), TRIM1.3 (A)
unnamed: IC1.2 (PC1), JP1.1
unnamed: IC1.13 (PC2), JP1.3
unnamed: JP1.2, R1.1
unnamed: C4.1, IC1.9 (VCOIN), R1.2, R2.2
unnamed: C3.1, R2.1
unnamed: C5.2, IC1.3 (CIN), IC1.4 (VCOOUT)
unnamed: L2.1, X1.3
unnamed: C5.1, IC2.5 (+IN)
unnamed: IC3.14 (X), IC3.15 (Y)
unnamed: C8.2, IC2.3 (+IN), R8.1
unnamed: IC2.2 (-IN), R6.2, R7.1
unnamed: C7.2, IC1.14 (SIGIN), R3.2, R4.1
unnamed: C7.1, IC2.1 (OUT), R6.1
unnamed: IC2.6 (-IN), IC2.7 (OUT), R9.2
unnamed: R9.1, SUBCARRIEROUT.1
unnamed: L1.1, X1.1
unnamed: IC3.11 (A), IC4.10 (P1), X2.2
unnamed: IC3.12 (X0), VIDEO-IN.1
unnamed: IC3.2 (Y0), IC3.5 (Z0)
unnamed: IC3.1 (Y1), IC3.3 (Z1)
unnamed: C8.1, IC3.4 (Z)
unnamed: IC3.10 (B), IC4.9 (Q1)
unnamed: IC3.9 (C), JP2.2

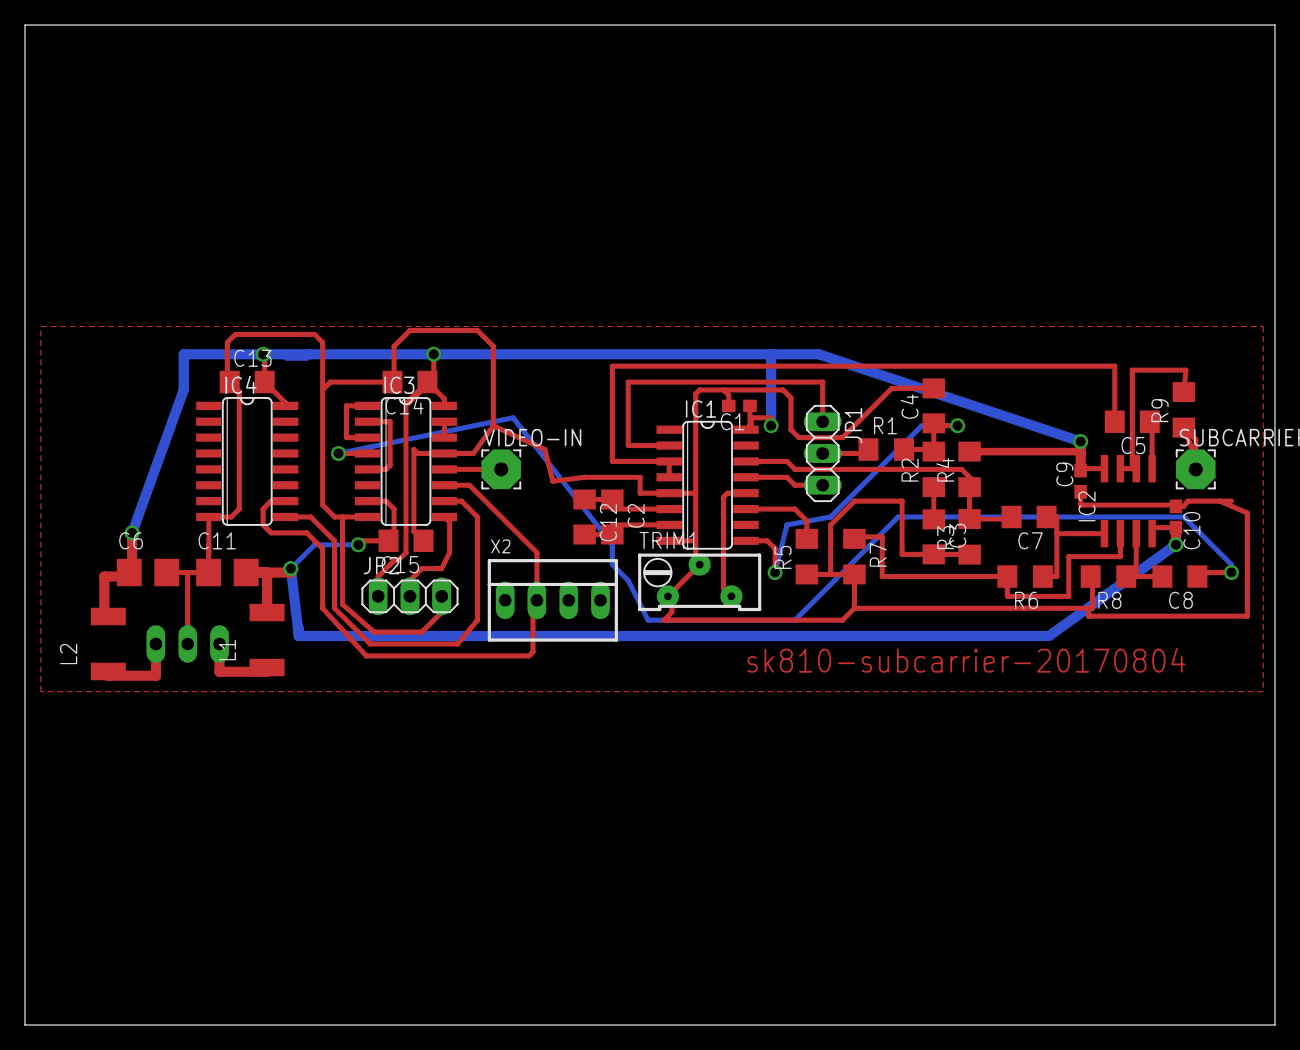
[picture p245: board sk810-subcarrier.brd from above]

Board: 2 copper layers, 100.0 x 80.0 mm, 37 parts (1 on the bottom side), 30 nets.
