mirdej/synkie/eagle/sk008-vga-breakout/sk008-vga-breakout.brd

## EAGLE design eagle/sk008-vga-breakout/sk008-vga-breakout.brd (2017-06-06)

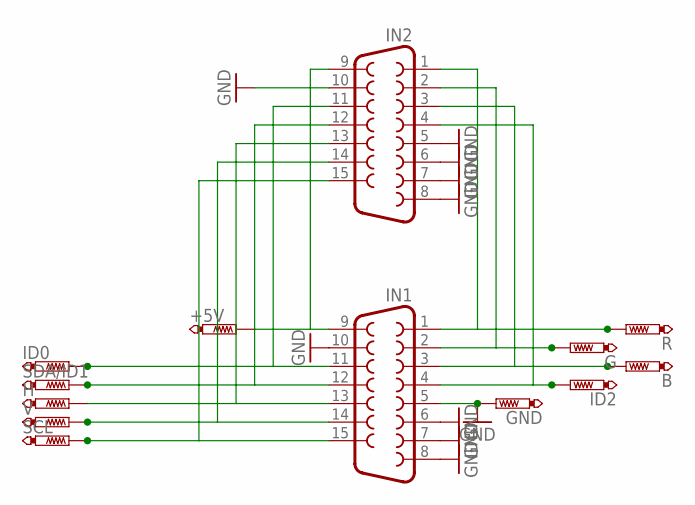
[picture p246: schematic sk008-vga-breakout.sch]

Parts:
+5V: PTR1PAD1-17Y; P1-17Y
B: PTR1PAD1-17Y; P1-17Y
G: PTR1PAD1-17Y; P1-17Y
GND: PTR1PAD1-17Y; P1-17Y
H: PTR1PAD1-17Y; P1-17Y
ID0, ID2: PTR1PAD1-17Y; P1-17Y
IN1, IN2: F15HDH; HDF15H
R: PTR1PAD1-17Y; P1-17Y
SCL: PTR1PAD1-17Y; P1-17Y
SDA/ID1: PTR1PAD1-17Y; P1-17Y
V: PTR1PAD1-17Y; P1-17Y

Connections:
GND: GND.TP, IN1.5, IN1.6, IN1.7, IN1.8, IN1.10, IN2.5, IN2.6, IN2.7, IN2.8, IN2.10
unnamed: IN1.1, IN2.1, R.TP
unnamed: G.TP, IN1.2, IN2.2
unnamed: B.TP, IN1.3, IN2.3
unnamed: H.TP, IN1.13, IN2.13
unnamed: IN1.12, IN2.12, SDA/ID1.TP
unnamed: IN1.14, IN2.14, V.TP
unnamed: IN1.15, IN2.15, SCL.TP
unnamed: +5V.TP, IN1.9, IN2.9
unnamed: ID2.TP, IN1.4, IN2.4
unnamed: ID0.TP, IN1.11, IN2.11

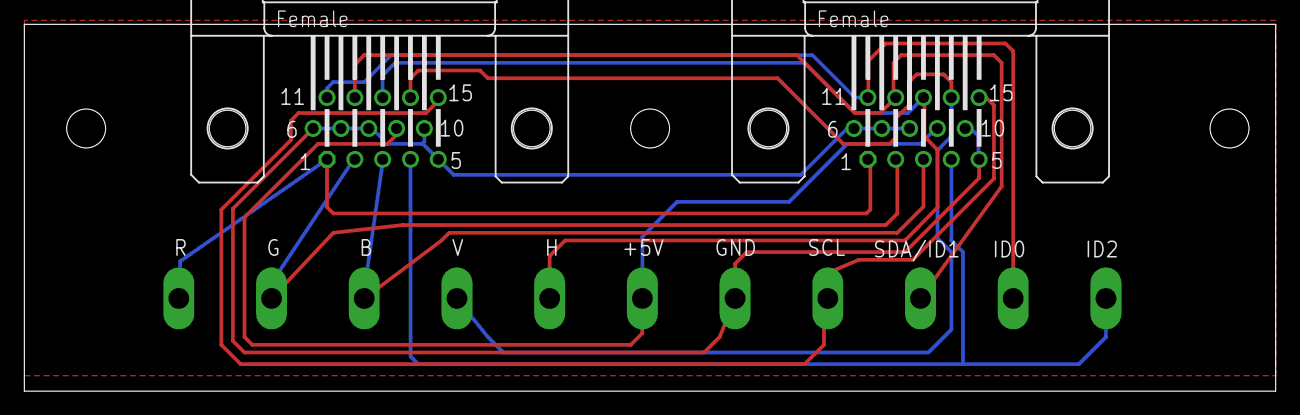
[picture p247: board sk008-vga-breakout.brd from above]

Board: 2 copper layers, 102.8 x 30.2 mm, 13 parts (0 on the bottom side), 11 nets.
