mirdej/synkie/eagle/sk009-multiple/sk009-multiple.brd

## EAGLE design eagle/sk009-multiple/sk009-multiple.brd (2017-06-06)

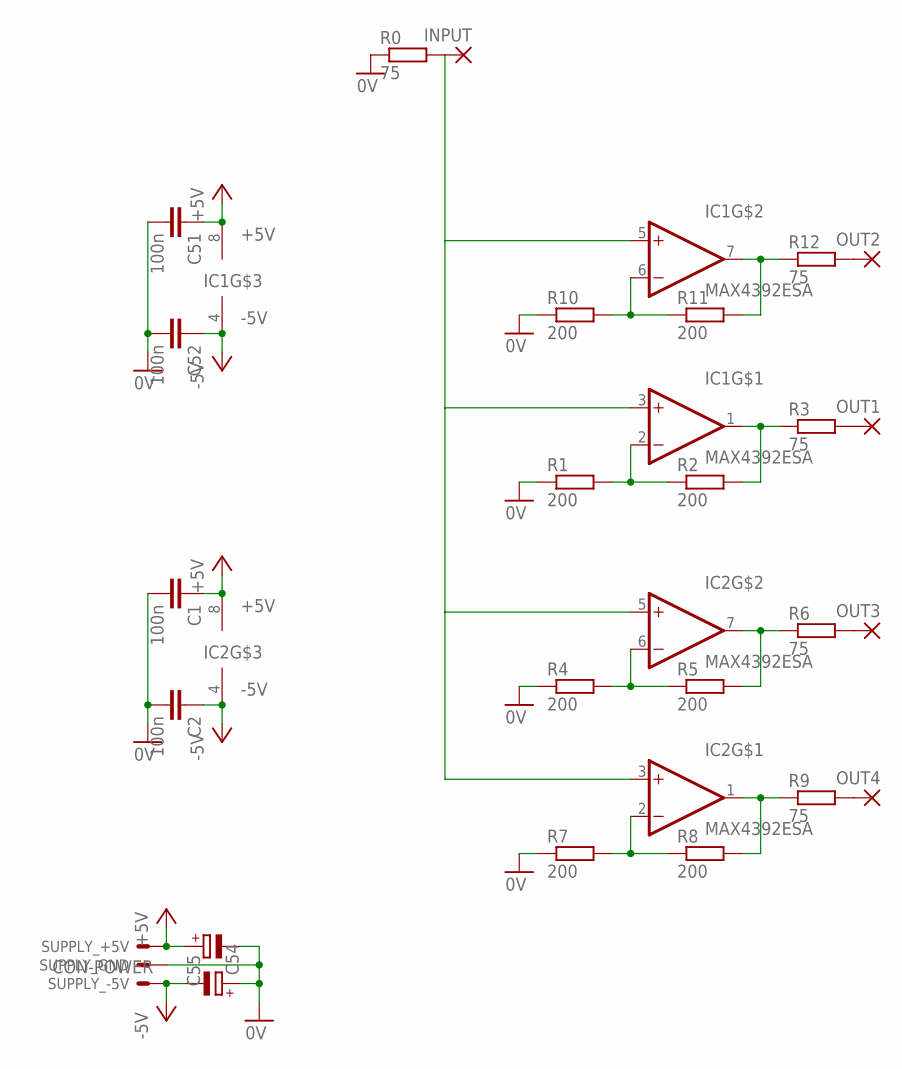
[picture p248: schematic sk009-multiple.sch]

Parts:
C1, C2, C51, C52: 100n; C0805
C54, C55: CPOL-EUCT3528; CT3528
IC1, IC2: MAX4392ESA; SO08
INPUT: 3,17/1,1
OUT1, OUT2, OUT3, OUT4: 3,17/1,1
R0, R3, R6, R9, R12: 75; R0805
R1, R2, R4, R5, R7, R8, R10, R11: 200; R0805
SUPPLY: CON-POWER; 22-23-2031

Connections:
0V: C1.2, C2.2, C51.2, C52.2, C54.+, C55.-, R0.1, R1.1, R4.1, R7.1, R10.1, SUPPLY.2
+5V: C1.1, C51.1, C55.+, IC1.8 (+5V), IC2.8 (+5V), SUPPLY.3
-5V: C2.1, C52.1, C54.-, IC1.4 (-5V), IC2.4 (-5V), SUPPLY.1
unnamed: IC1.2 (-IN), R1.2, R2.1
unnamed: IC1.1 (OUT), R2.2, R3.1
unnamed: OUT1.1, R3.2
unnamed: IC2.6 (-IN), R4.2, R5.1
unnamed: IC2.7 (OUT), R5.2, R6.1
unnamed: OUT3.1, R6.2
unnamed: IC2.2 (-IN), R7.2, R8.1
unnamed: IC2.1 (OUT), R8.2, R9.1
unnamed: OUT4.1, R9.2
unnamed: IC1.3 (+IN), IC1.5 (+IN), IC2.3 (+IN), IC2.5 (+IN), INPUT.1, R0.2
unnamed: IC1.6 (-IN), R10.2, R11.1
unnamed: IC1.7 (OUT), R11.2, R12.1
unnamed: OUT2.1, R12.2

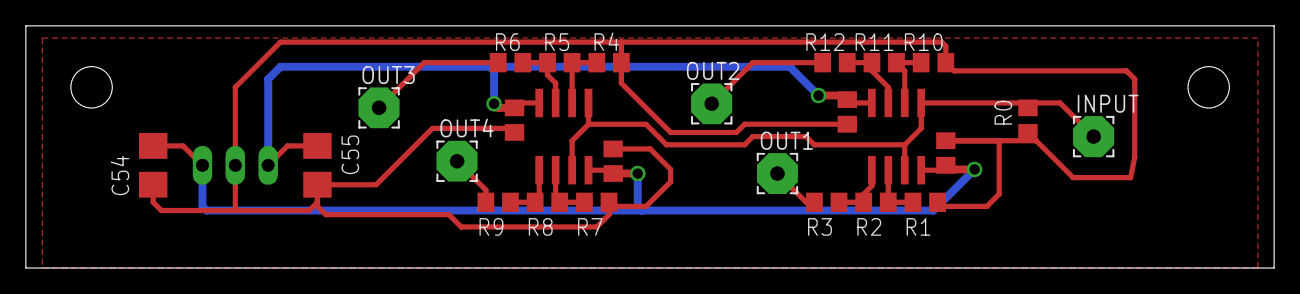
[picture p249: board sk009-multiple.brd from above]

Board: 2 copper layers, 96.5 x 18.7 mm, 27 parts (1 on the bottom side), 16 nets.
