mirdej/synkie/eagle/sk800-rgb/sk800-rgb.brd

## EAGLE design eagle/sk800-rgb/sk800-rgb.brd (2016-02-06)

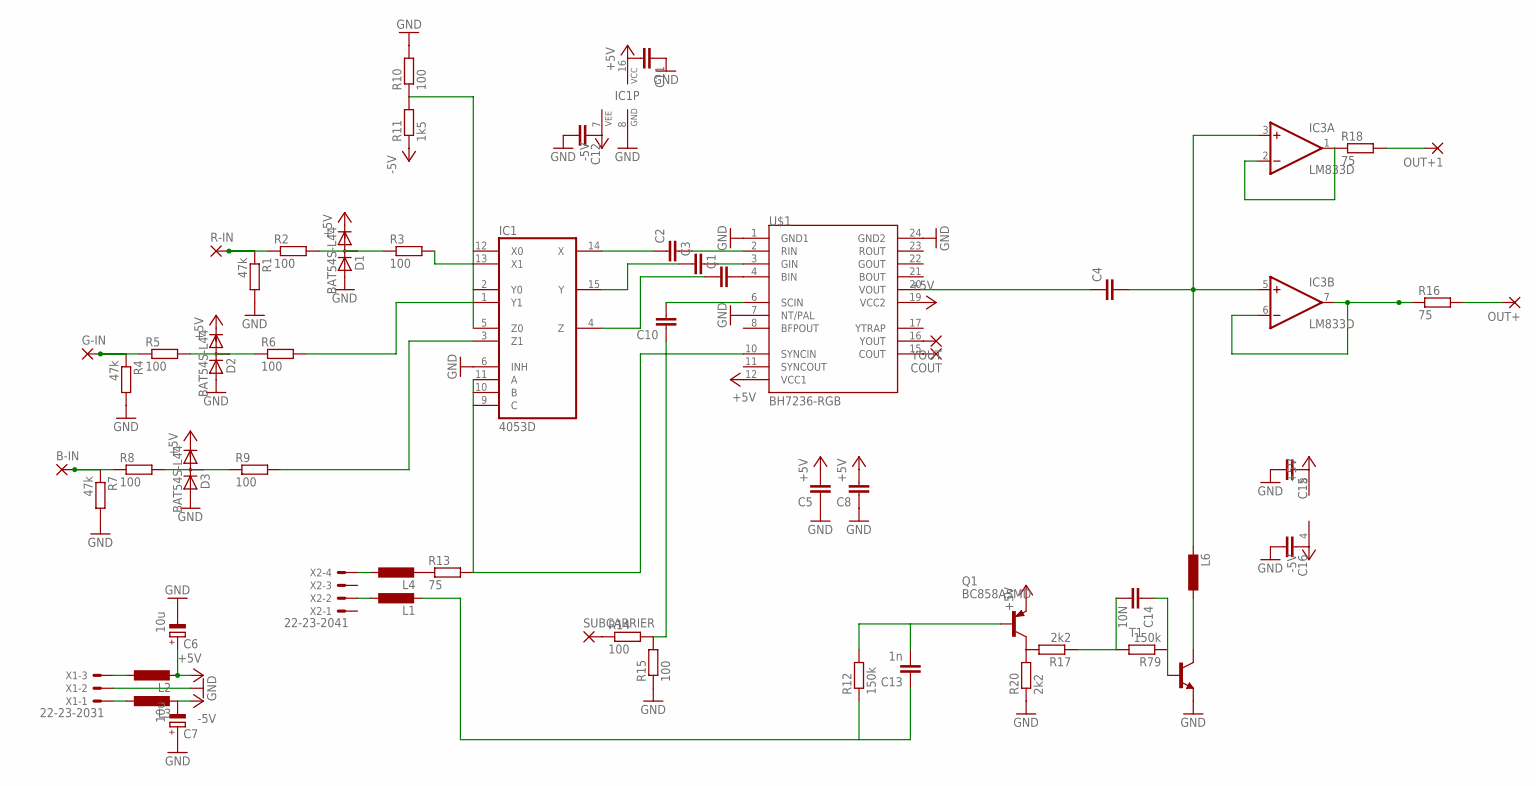
[picture p250: schematic sk800-rgb.sch]

Parts:
B-IN: 3,17/1,1
C1, C2, C3, C4, C10: C-EUC1206; C1206
C5, C8, C11, C12, C15, C16: C-EUC0603; C0603
C6, C7: 10u; CT3528
C13: 1n; C1206
C14: 10N; C1206
COUT: 3,17/1,1
D1, D2, D3: BAT54S-L44; SOT23
G-IN: 3,17/1,1
IC1: 4053D; SO16
IC3: LM833D; SO08
L1, L2, L3, L4, L6: L-EUL5038P; L5038P
OUT+, OUT+1: 3,17/1,1
Q1: BC858ASMD; SOT23-BEC
R1, R4, R7: 47k; R1206
R2, R3, R5, R6, R8, R9, R10, R14, R15: 100; R1206
R11: 1k5; R1206
R12, R79: 150k; R1206
R13, R16, R18: 75; R1206
R17, R20: 2k2; R1206
R-IN: 3,17/1,1
SUBCARRIER: 3,17/1,1
T1: BC847ALT1-NPN-SOT23-BEC; SOT23-BEC
U$1: BH7236-RGB; SO24N
X1: 22-23-2031
X2: 22-23-2041
YOUT: 3,17/1,1

Connections:
+5V: C5.2, C6.+, C8.2, C11.2, C15.1, D1.2 (C), D2.2 (C), D3.2 (C), IC1.16 (VCC), IC3.8 (V+), L2.2, Q1.E, U$1.12 (VCC1), U$1.19 (VCC2)
-5V: C7.-, C12.1, C16.1, IC1.7 (VEE), IC3.4 (V-), L3.2, R11.1
GND: C5.1, C6.-, C7.+, C8.1, C11.1, C12.2, C15.2, C16.2, D1.1 (A), D2.1 (A), D3.1 (A), IC1.6 (INH), IC1.8 (GND), R1.2, R4.2, R7.2, R10.2, R15.1, R20.1, T1.E, U$1.1 (GND1), U$1.7 (NT/PAL), U$1.24 (GND2), X1.2
unnamed: C1.2, U$1.4 (BIN)
unnamed: C2.1, IC1.14 (X)
unnamed: C2.2, U$1.2 (RIN)
unnamed: C3.2, U$1.3 (GIN)
unnamed: R1.1, R2.1, R-IN.1
unnamed: D1.3 (AC), R2.2, R3.1
unnamed: IC1.13 (X1), R3.2
unnamed: C3.1, IC1.15 (Y)
unnamed: C1.1, IC1.4 (Z)
unnamed: C10.2, U$1.6 (SCIN)
unnamed: L2.1, X1.3
unnamed: L1.1, X2.2
unnamed: L4.1, X2.4
unnamed: G-IN.1, R4.1, R5.1
unnamed: L3.1, X1.1
unnamed: D2.3 (AC), R5.2, R6.1
unnamed: IC1.1 (Y1), R6.2
unnamed: B-IN.1, R7.1, R8.1
unnamed: D3.3 (AC), R8.2, R9.1
unnamed: IC1.3 (Z1), R9.2
unnamed: IC1.9 (C), IC1.10 (B), IC1.11 (A), R13.2, U$1.10 (SYNCIN)
unnamed: IC1.2 (Y0), IC1.5 (Z0), IC1.12 (X0), R10.1, R11.2
unnamed: C4.1, U$1.20 (VOUT)
unnamed: C13.1, L1.2, R12.1
unnamed: U$1.16 (YOUT), YOUT.1
unnamed: L4.2, R13.1
unnamed: COUT.1, U$1.15 (COUT)
unnamed: R14.1, SUBCARRIER.1
unnamed: C10.1, R14.2, R15.2
unnamed: OUT+.1, R16.2
unnamed: IC3.6 (-IN), IC3.7 (OUT), R16.1
unnamed: C4.2, IC3.3 (+IN), IC3.5 (+IN), L6.2
unnamed: L6.1, T1.C
unnamed: C14.1, R79.1, T1.B
unnamed: C13.2, Q1.B, R12.2
unnamed: Q1.C, R17.2, R20.2
unnamed: C14.2, R17.1, R79.2
unnamed: OUT+1.1, R18.2
unnamed: IC3.1 (OUT), IC3.2 (-IN), R18.1

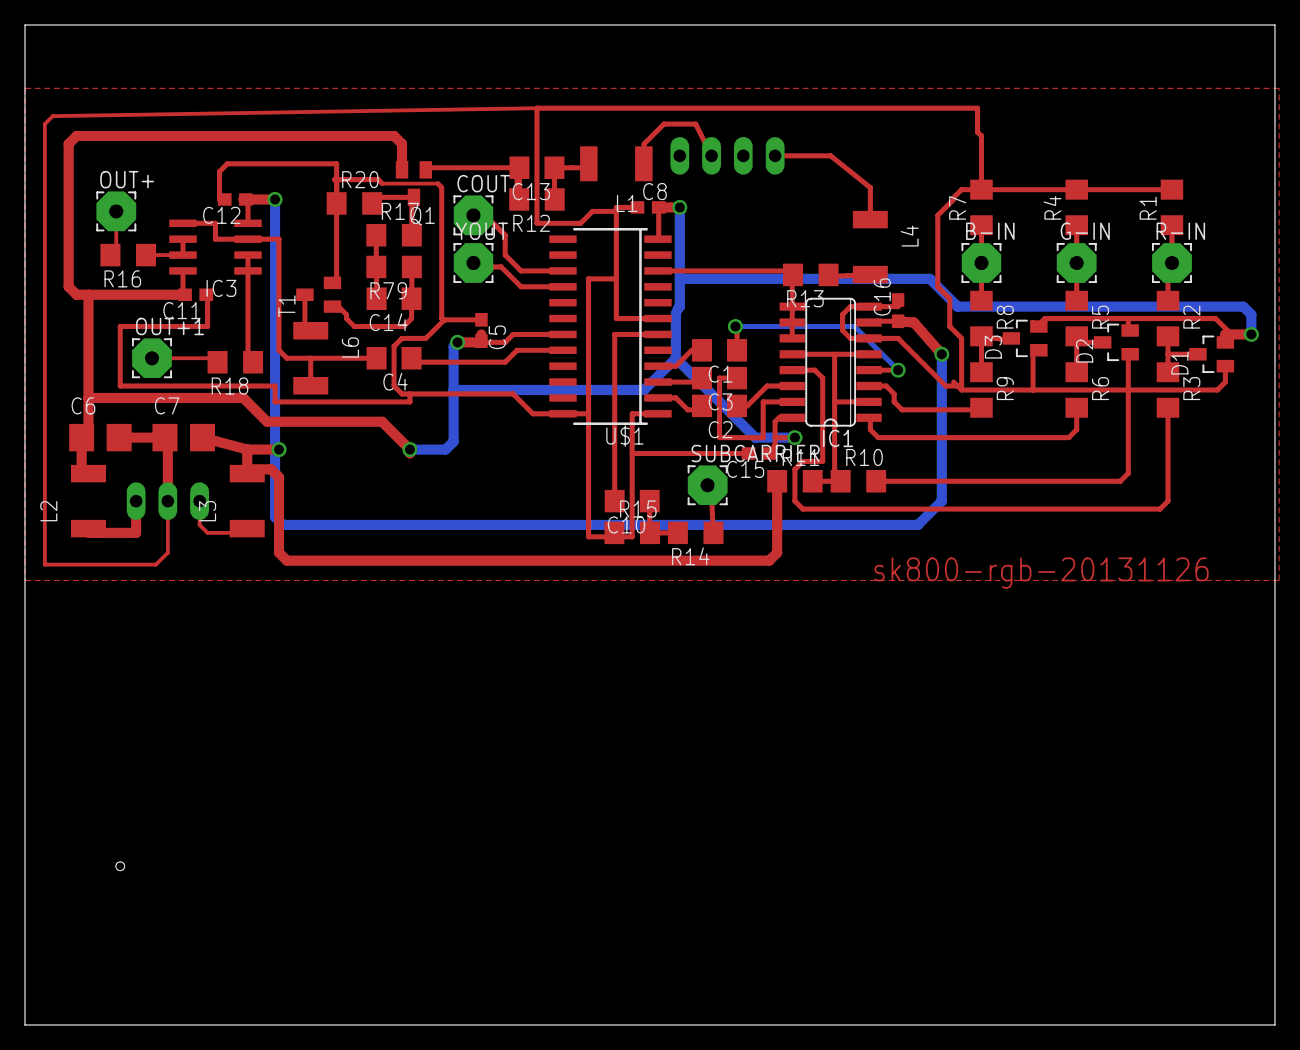
[picture p251: board sk800-rgb.brd from above]

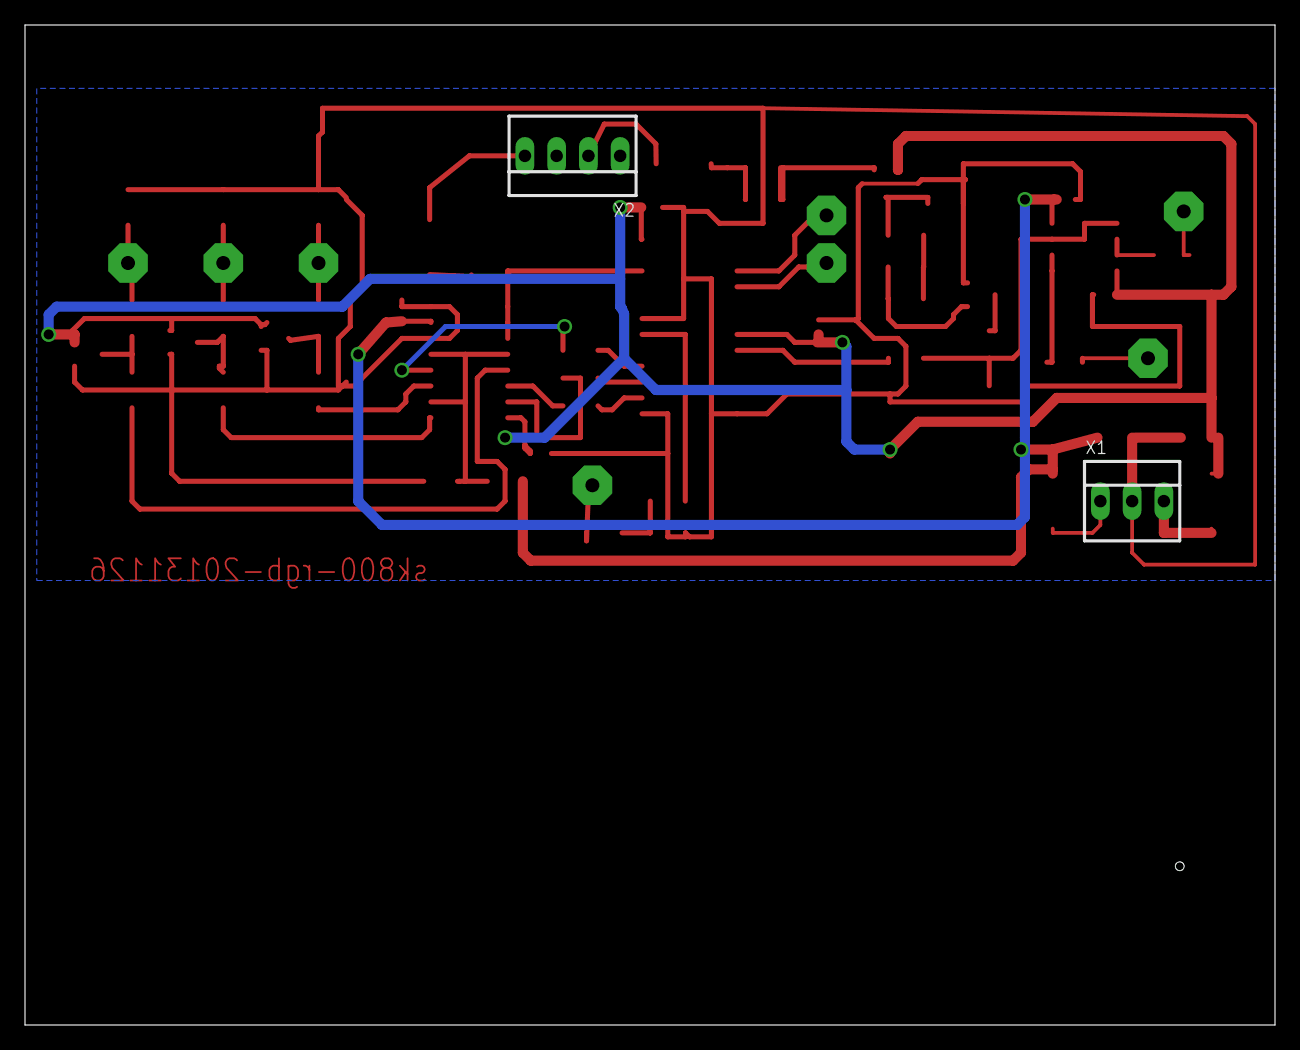
[picture p252: board sk800-rgb.brd from below]

Board: 2 copper layers, 100.0 x 80.0 mm, 58 parts (2 on the bottom side), 42 nets.
