mirdej/synkie/eagle/sk010-refgen2-study/subcarrier-proto2.brd

## EAGLE design eagle/sk010-refgen2-study/subcarrier-proto2.brd (2016-01-08)

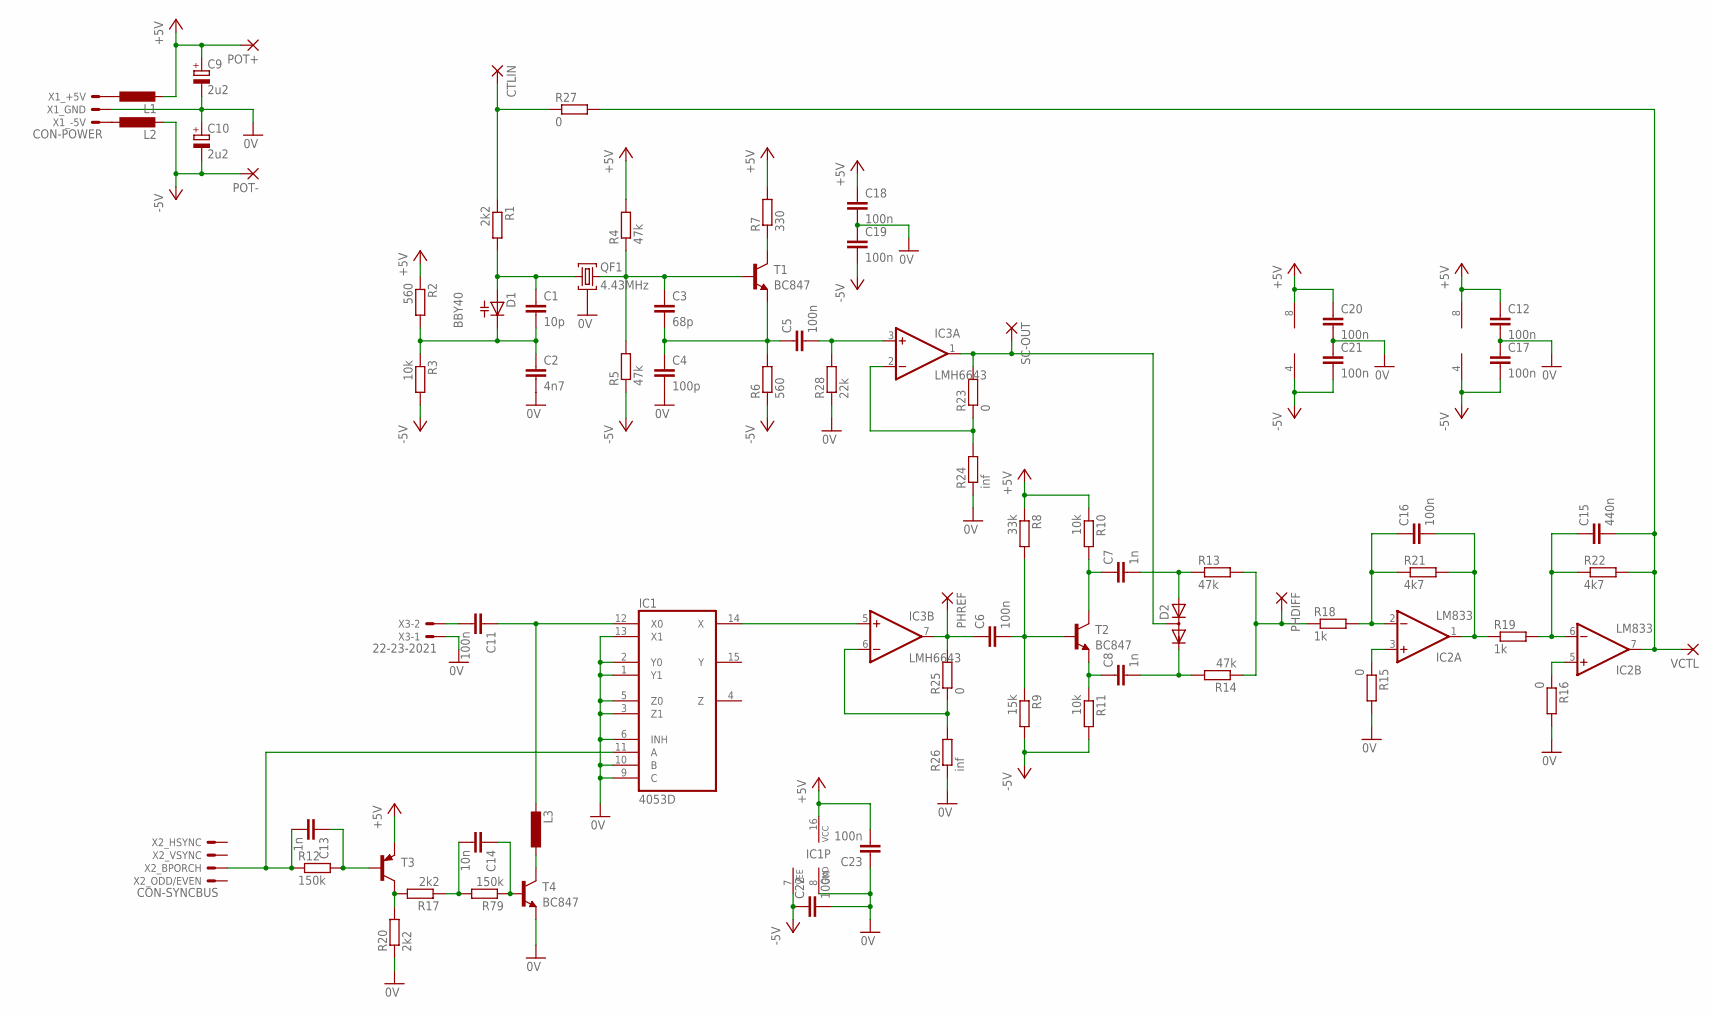
[picture p253: schematic subcarrier-proto2.sch]

Parts:
C1: 10p; C1206
C2: 4n7; C1206
C3: 68p; C1206
C4: 100p; C1206
C5, C6, C11, C12, C16, C17, C18, C19, C20, C21, C22, C23: 100n; C1206
C7, C8, C13: 1n; C1206
C9, C10: 2u2; CT3528
C14: 10n; C1206
C15: 440n; C1206
CTLIN: 3,17/1,1
D1: BBY40; SOT23
D2: DIODE_2CACA-SOT23; SOT23
IC1: 4053D; SO16
IC2: LM833; SO08
IC3: LMH6643; SO08
L1, L2, L3: L-EUL5038P; L5038P
PHDIFF: 3,17/1,1
PHREF: 3,17/1,1
POT+: 3,17/1,1
POT-: 3,17/1,1
QF1: 4.43MHz; SMD-CRYSTAL-GND
R1, R17, R20: 2k2; R1206
R2, R6: 560; R1206
R3, R10, R11: 10k; R1206
R4, R5, R13, R14: 47k; R1206
R7: 330; R1206
R8: 33k; R1206
R9: 15k; R1206
R12, R79: 150k; R1206
R15, R16, R23, R25, R27: 0; R1206
R18, R19: 1k; R1206
R21, R22: 4k7; R1206
R24, R26: inf; R1206
R28: 22k; R1206
SC-OUT: 3,17/1,1
T1, T2, T4: BC847; SOT23-BEC
T3: TRANS-PNPSOT23-BEC; SOT23-BEC
VCTL: 3,17/1,1
X1: CON-POWER; 22-23-2031
X2: CON-SYNCBUS; 22-23-2041
X3: 22-23-2021

Connections:
0V: C2.2, C4.2, C9.-, C10.+, C12.2, C17.1, C18.2, C19.1, C20.2, C21.1, C22.2, C23.1, IC1.1 (Y1), IC1.2 (Y0), IC1.3 (Z1), IC1.5 (Z0), IC1.6 (INH), IC1.8 (GND), IC1.9 (C), IC1.10 (B), IC1.13 (X1), QF1.P$3 (2), R15.2, R16.2, R20.1, R24.1, R26.1, R28.1, T4.E, X1.2, X3.1
+5V: C9.+, C12.1, C18.1, C20.1, C23.2, IC1.16 (VCC), IC2.8 (V+), IC3.8 (V+), L1.2, POT+.1, R2.1, R4.2, R7.2, R8.1, R10.1, T3.E
-5V: C10.-, C17.2, C19.2, C21.2, C22.1, IC1.7 (VEE), IC2.4 (V-), IC3.4 (V-), L2.2, POT-.1, R3.2, R5.1, R6.1, R9.2, R11.2
unnamed: C13.1, R12.2, T3.B
unnamed: C13.2, IC1.11 (A), R12.1, X2.2
unnamed: C1.1, D1.1 (A1), QF1.P$1 (1), R1.2
unnamed: C3.1, QF1.P$2 (3), R4.1, R5.2, T1.B
unnamed: C1.2, C2.1, D1.3 (C), R2.2, R3.1
unnamed: C3.2, C4.1, C5.1, R6.2, T1.E
unnamed: C5.2, IC3.3 (+IN), R28.2
unnamed: R7.1, T1.C
unnamed: C6.2, R8.2, R9.1, T2.B
unnamed: C8.1, R11.1, T2.E
unnamed: C7.1, R10.2, T2.C
unnamed: PHDIFF.1, R13.2, R14.1, R18.1
unnamed: C7.2, D2.1 (A), R13.1
unnamed: C8.2, D2.2 (C), R14.2
unnamed: C6.1, IC3.7 (OUT), PHREF.1, R25.2
unnamed: C11.2, X3.2
unnamed: C11.1, IC1.12 (X0), L3.2
unnamed: C16.1, IC2.2 (-IN), R18.2, R21.1
unnamed: IC2.3 (+IN), R15.1
unnamed: IC2.5 (+IN), R16.1
unnamed: C16.2, IC2.1 (OUT), R19.1, R21.2
unnamed: C15.1, IC2.6 (-IN), R19.2, R22.1
unnamed: C15.2, IC2.7 (OUT), R22.2, R27.2, VCTL.1
unnamed: L1.1, X1.3
unnamed: L2.1, X1.1
unnamed: CTLIN.1, R1.1, R27.1
unnamed: D2.3 (AC), IC3.1 (OUT), R23.2, SC-OUT.1
unnamed: IC3.2 (-IN), R23.1, R24.2
unnamed: IC3.6 (-IN), R25.1, R26.2
unnamed: IC1.14 (X), IC3.5 (+IN)
unnamed: L3.1, T4.C
unnamed: C14.1, R79.1, T4.B
unnamed: R17.2, R20.2, T3.C
unnamed: C14.2, R17.1, R79.2

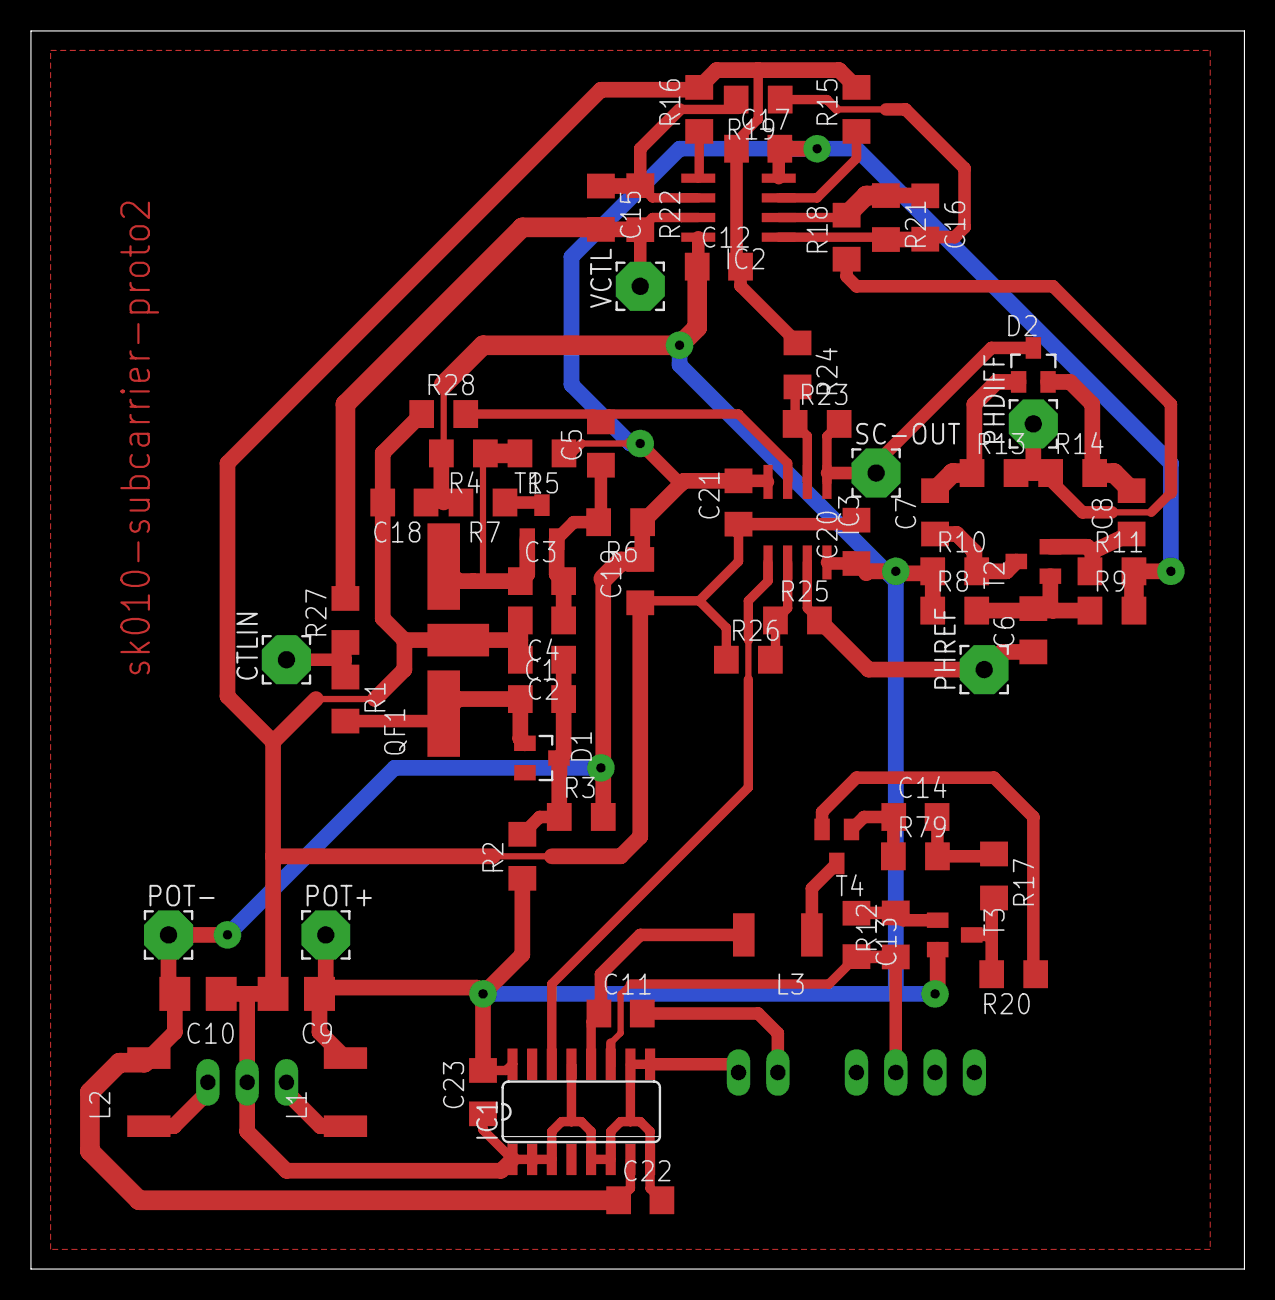
[picture p254: board subcarrier-proto2.brd from above]

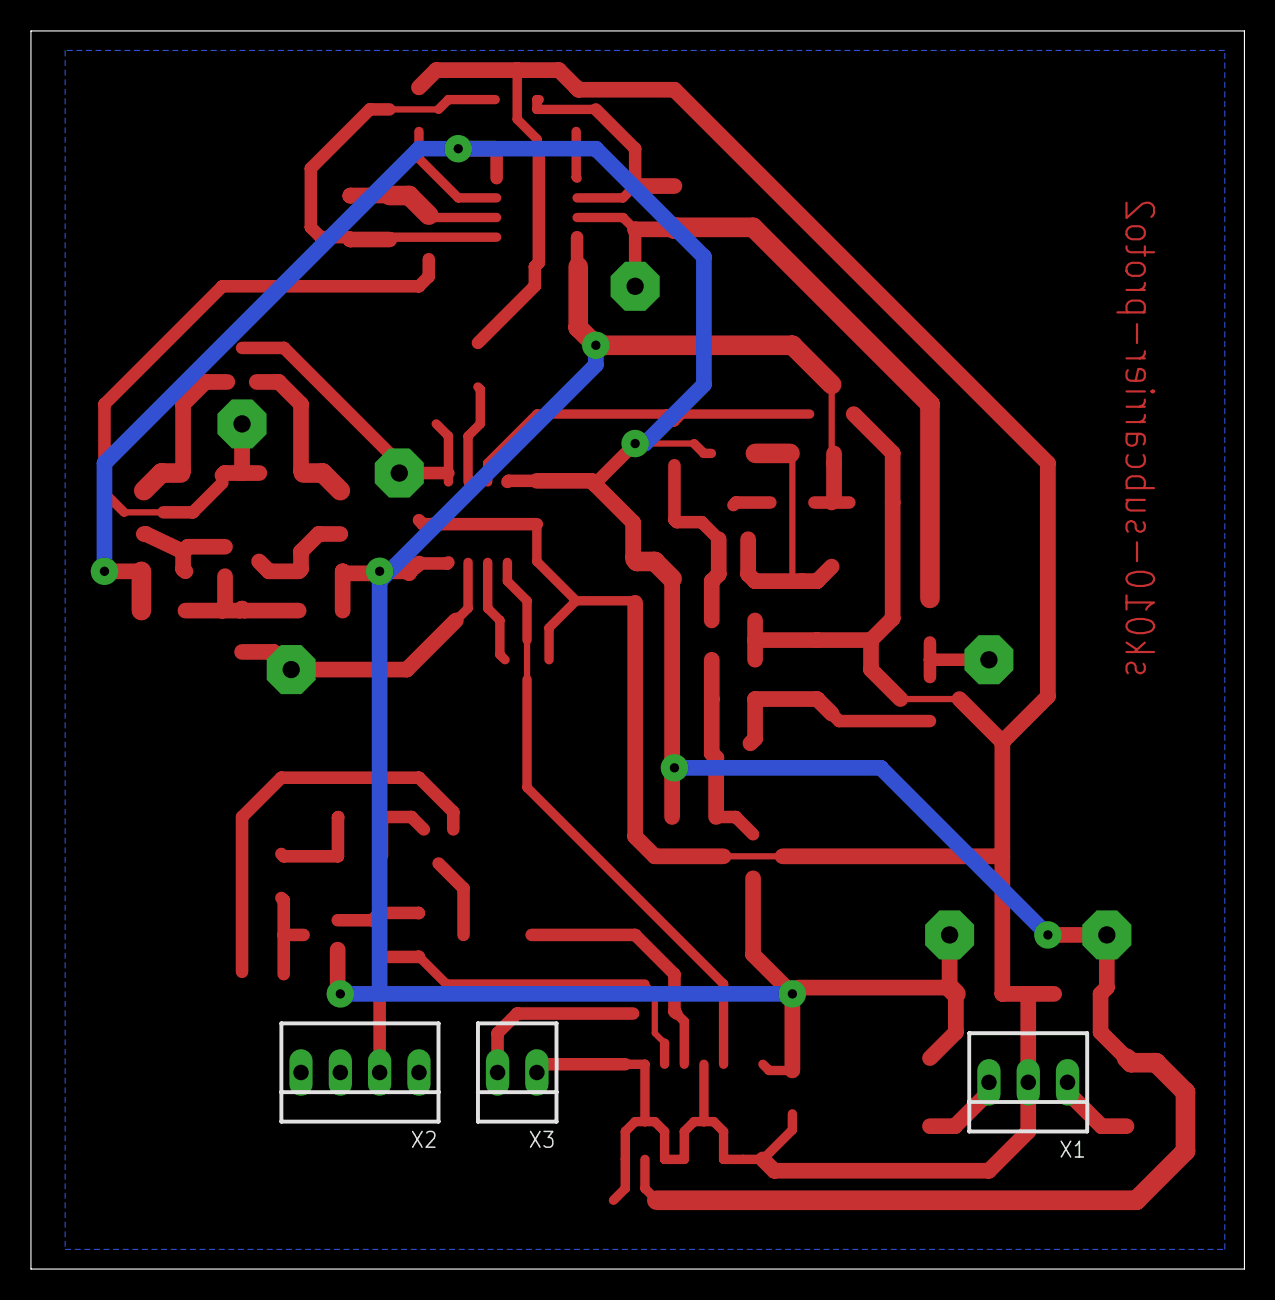
[picture p255: board subcarrier-proto2.brd from below]

Board: 2 copper layers, 78.4 x 80.0 mm, 75 parts (3 on the bottom side), 37 nets.
