mirdej/synkie/eagle/sk010-refgen2-study/ampli.brd

## EAGLE design eagle/sk010-refgen2-study/ampli.brd (2016-01-08)

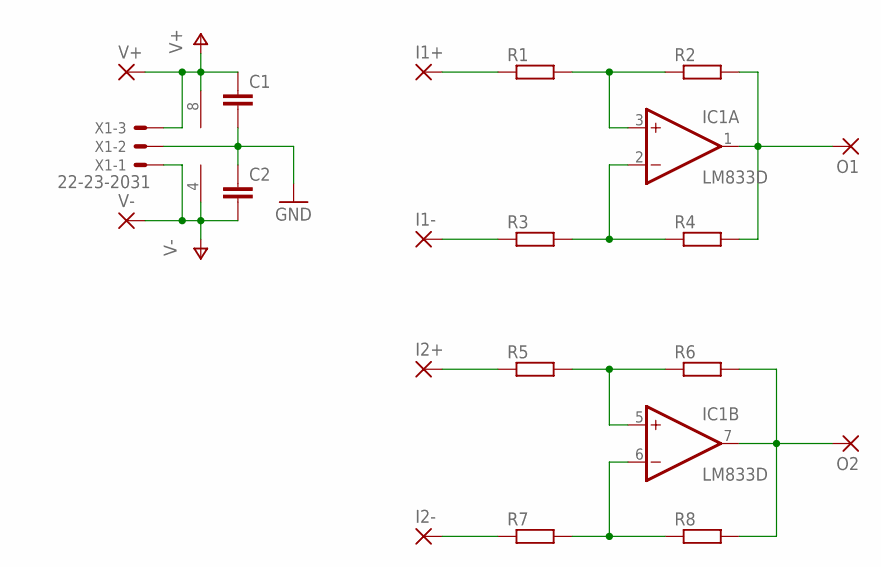
[picture p256: schematic ampli.sch]

Parts:
C1, C2: C-EUC0805; C0805
I1+, I1-, I2+, I2-: 3,17/1,1
IC1: LM833D; SO08
O1, O2: 3,17/1,1
R1, R2, R3, R4, R5, R6, R7, R8: R-EU_R1206; R1206
V+: 3,17/1,1
V-: 3,17/1,1
X1: 22-23-2031

Connections:
GND: C1.2, C2.1, X1.2
unnamed: IC1.3 (+IN), R1.2, R2.1
unnamed: IC1.1 (OUT), O1.1, R2.2, R4.2
unnamed: IC1.2 (-IN), R3.2, R4.1
unnamed: I1+.1, R1.1
unnamed: I1-.1, R3.1
unnamed: I2+.1, R5.1
unnamed: IC1.5 (+IN), R5.2, R6.1
unnamed: IC1.7 (OUT), O2.1, R6.2, R8.2
unnamed: IC1.6 (-IN), R7.2, R8.1
unnamed: I2-.1, R7.1
V+: C1.1, IC1.8 (V+), V+.1, X1.3
V-: C2.2, IC1.4 (V-), V-.1, X1.1

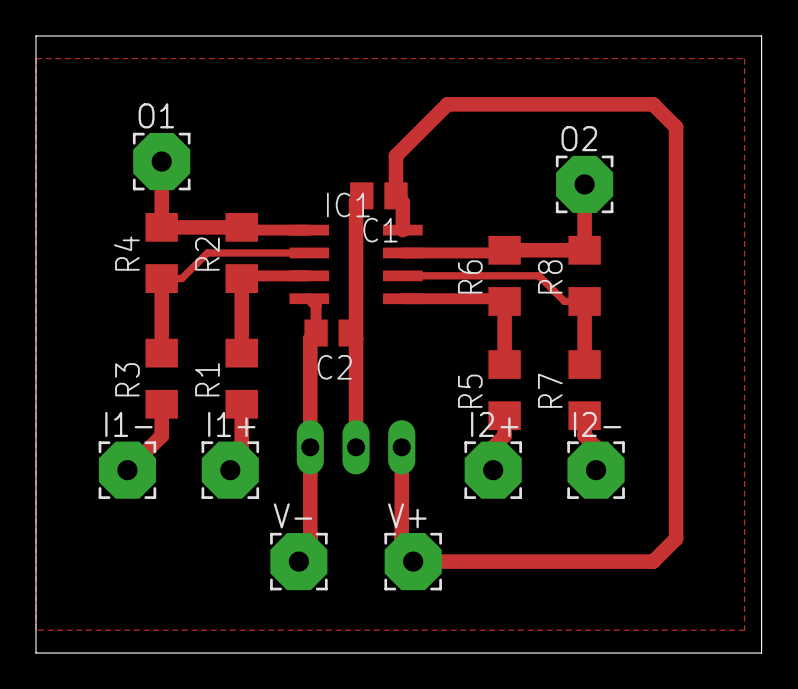
[picture p257: board ampli.brd from above]

Board: 2 copper layers, 40.3 x 34.3 mm, 20 parts (1 on the bottom side), 13 nets.
