mirdej/synkie/eagle/sk590-audio-inject/sk590-audio-inject.brd

## EAGLE design eagle/sk590-audio-inject/sk590-audio-inject.brd (2016-01-06)

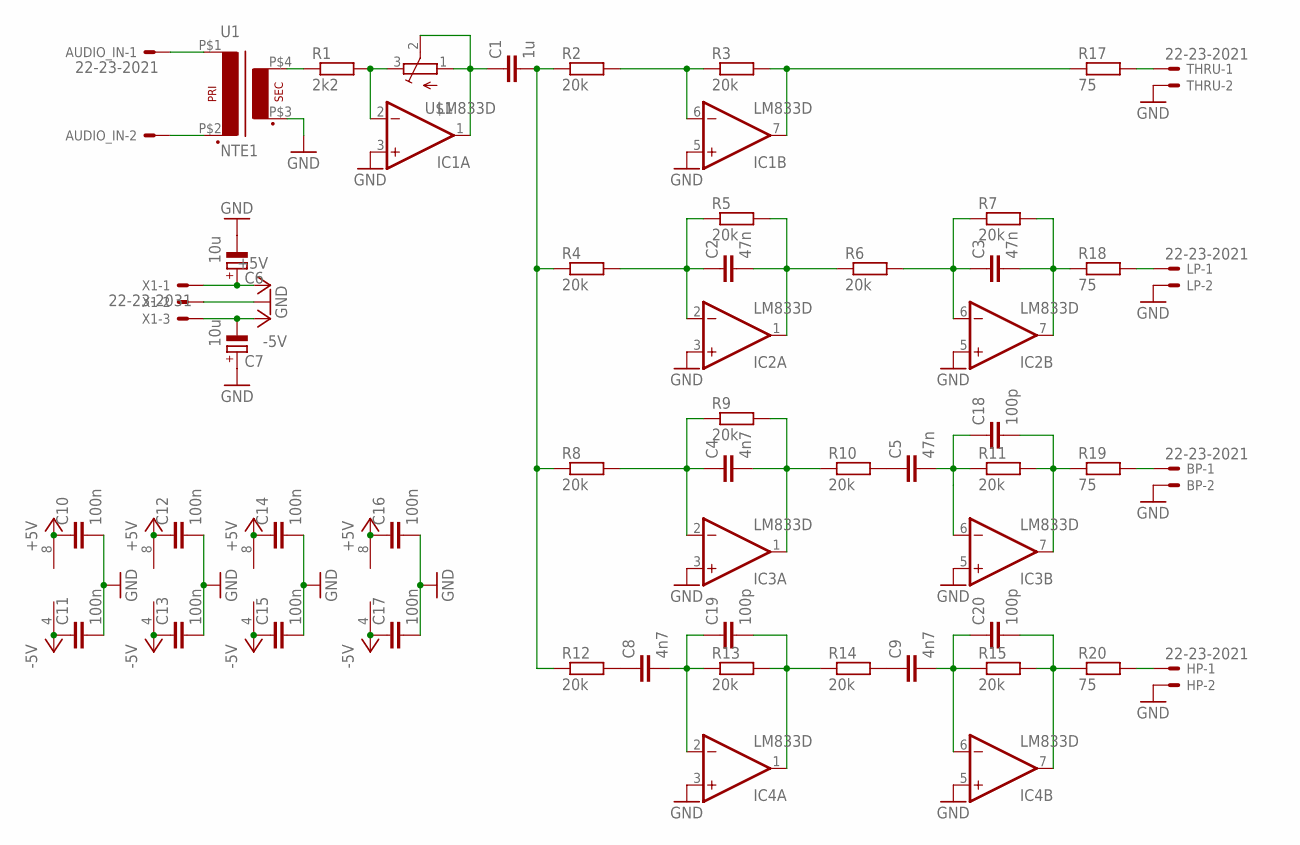
[picture p258: schematic sk590-audio-inject.sch]

Parts:
AUDIO_IN: 22-23-2021
BP: 22-23-2021
C1: 1u; C1206
C2, C3, C5: 47n; C1206
C4, C8, C9: 4n7; C1206
C6, C7: 10u; CT3528
C10, C11, C12, C13, C14, C15, C16, C17: 100n; C1206
C18, C19, C20: 100p; C1206
HP: 22-23-2021
IC1, IC2, IC3, IC4: LM833D; SO08
LP: 22-23-2021
R1: 2k2; R1206
R2, R3, R4, R5, R6, R7, R8, R9, R10, R11, R12, R13, R14, R15: 20k; R1206
R17, R18, R19, R20: 75; R1206
THRU: 22-23-2021
U1: NTE1; AUDIOTRAFO
U$1: ALPS_RK09K111_HOHNE-FüSSE; ALPS_RK09K111
X1: 22-23-2031

Connections:
+5V: C6.+, C10.1, C12.1, C14.1, C16.1, IC1.8 (V+), IC2.8 (V+), IC3.8 (V+), IC4.8 (V+), X1.1
-5V: C7.-, C11.1, C13.1, C15.1, C17.1, IC1.4 (V-), IC2.4 (V-), IC3.4 (V-), IC4.4 (V-), X1.3
GND: BP.2, C6.-, C7.+, C10.2, C11.2, C12.2, C13.2, C14.2, C15.2, C16.2, C17.2, HP.2, IC1.3 (+IN), IC1.5 (+IN), IC2.3 (+IN), IC2.5 (+IN), IC3.3 (+IN), IC3.5 (+IN), IC4.3 (+IN), IC4.5 (+IN), LP.2, THRU.2, U1.P$3 (S3), X1.2
unnamed: R1.1, U1.P$4 (S4)
unnamed: AUDIO_IN.1, U1.P$1 (P1)
unnamed: AUDIO_IN.2, U1.P$2 (P2)
unnamed: IC1.2 (-IN), R1.2, U$1.3 (E)
unnamed: C1.1, IC1.1 (OUT), U$1.1 (S), U$1.2 (W)
unnamed: C1.2, R2.1, R4.1, R8.1, R12.1
unnamed: IC1.6 (-IN), R2.2, R3.1
unnamed: IC1.7 (OUT), R3.2, R17.1
unnamed: C2.1, IC2.2 (-IN), R4.2, R5.1
unnamed: C2.2, IC2.1 (OUT), R5.2, R6.1
unnamed: C3.1, IC2.6 (-IN), R6.2, R7.1
unnamed: C3.2, IC2.7 (OUT), R7.2, R18.1
unnamed: C5.1, R10.2
unnamed: C8.1, R12.2
unnamed: C4.1, IC3.2 (-IN), R8.2, R9.1
unnamed: C8.2, C19.1, IC4.2 (-IN), R13.1
unnamed: C19.2, IC4.1 (OUT), R13.2, R14.1
unnamed: C4.2, IC3.1 (OUT), R9.2, R10.1
unnamed: C5.2, C18.1, IC3.6 (-IN), R11.1
unnamed: C18.2, IC3.7 (OUT), R11.2, R19.1
unnamed: C9.1, R14.2
unnamed: C9.2, C20.1, IC4.6 (-IN), R15.1
unnamed: C20.2, IC4.7 (OUT), R15.2, R20.1
unnamed: R17.2, THRU.1
unnamed: LP.1, R18.2
unnamed: BP.1, R19.2
unnamed: HP.1, R20.2

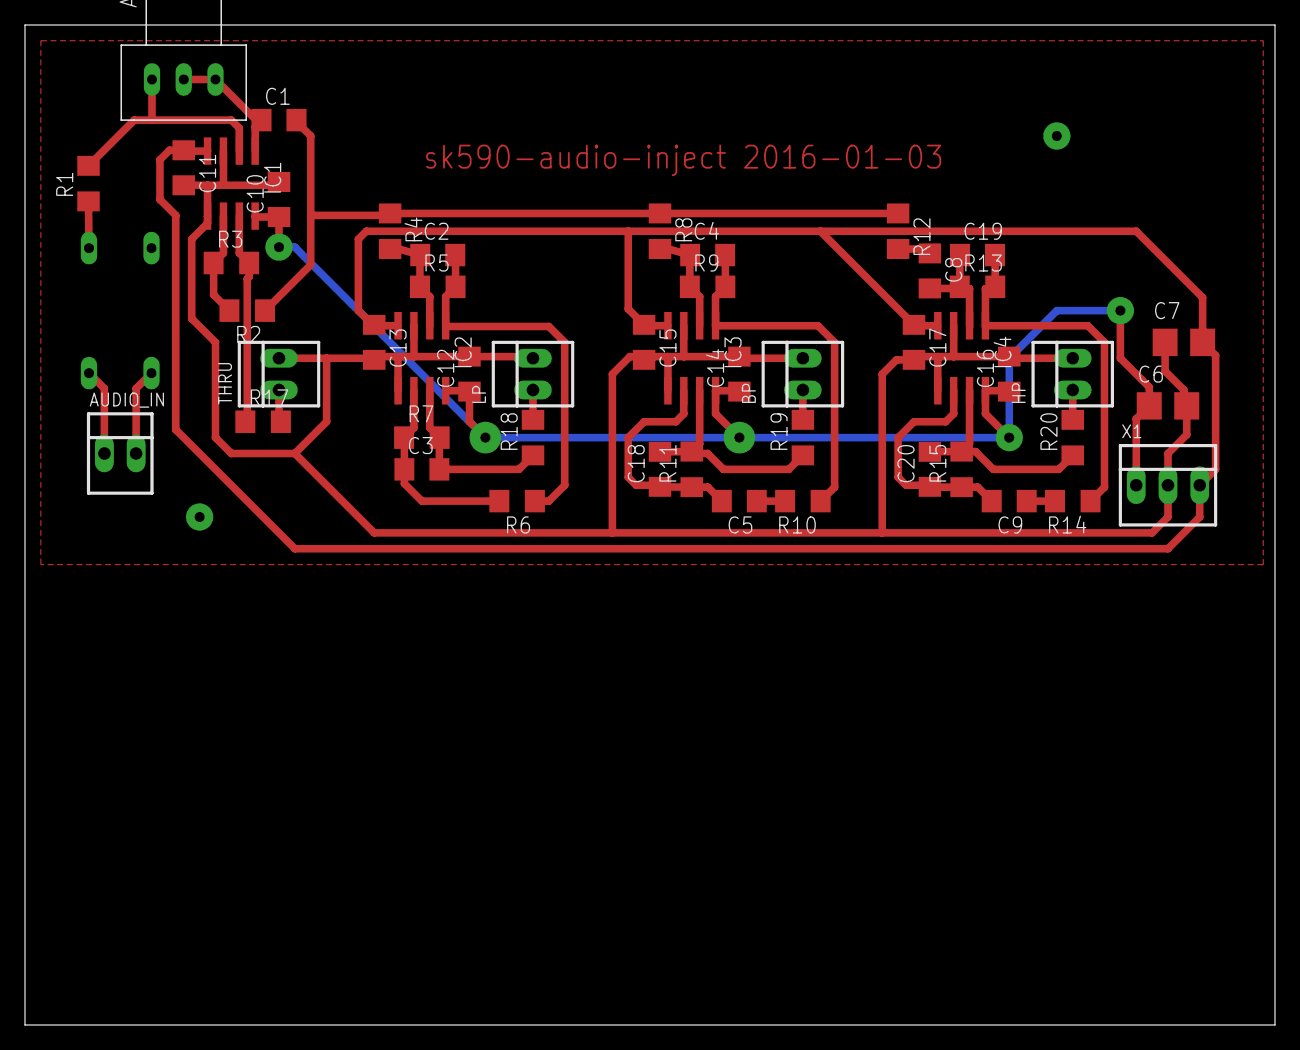
[picture p259: board sk590-audio-inject.brd from above]

Board: 2 copper layers, 100.0 x 80.0 mm, 51 parts (0 on the bottom side), 30 nets.
