mirdej/synkie/eagle/sk010-refgen2-study/subcarrier-proto.brd

## EAGLE design eagle/sk010-refgen2-study/subcarrier-proto.brd (2015-05-24)

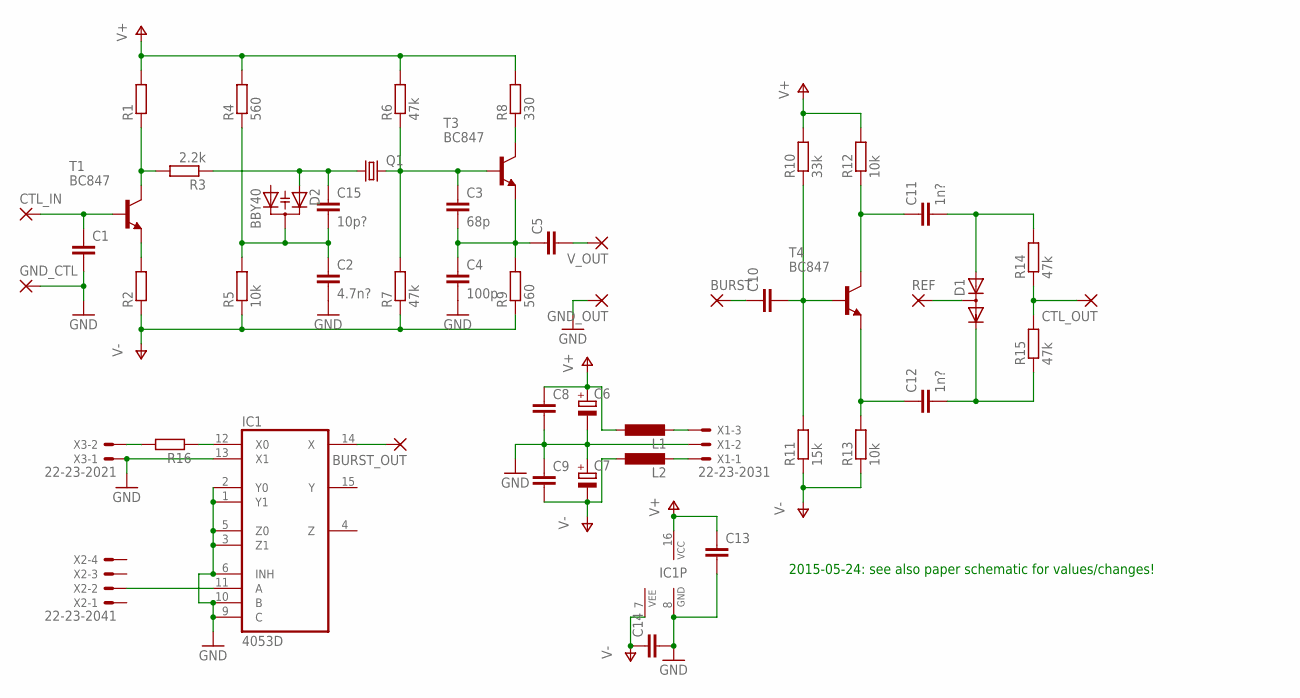
[picture p260: schematic subcarrier-proto.sch]

Parts:
BURST: WIREPAD3,17/1,1; 3,17/1,1
BURST_OUT: 3,17/1,1
C1, C5, C10: C-EUC1210; C1210
C2: 4.7n?; C1210
C3: 68p; C1210
C4: 100p; C1210
C6, C7: CPOL-EUCT3528; CT3528
C8, C9, C13, C14: C-EUC0805; C0805
C11, C12: 1n?; C1210
C15: 10p?; C1210
CTL_IN: WIREPAD3,17/1,1; 3,17/1,1
CTL_OUT: 3,17/1,1
D1: DIODE_2CACA-SOT23; SOT23
D2: BBY40; SOT23
GND_CTL: WIREPAD3,17/1,1; 3,17/1,1
GND_OUT: 3,17/1,1
IC1: 4053D; SO16
L1, L2: L-EUL5038P; L5038P
Q1: CRYSTALHC49UP; HC49UP
R1, R2, R16: R-EU_R1210; R1210
R3: 2.2k; R1210
R4, R9: 560; R1210
R5, R12, R13: 10k; R1210
R6, R7, R14, R15: 47k; R1210
R8: 330; R1210
R10: 33k; R1210
R11: 15k; R1210
REF: 3,17/1,1
T1, T3, T4: BC847; SOT23
V_OUT: 3,17/1,1
X1: 22-23-2031
X2: 22-23-2041
X3: 22-23-2021

Connections:
GND: C1.2, C2.2, C4.2, C6.-, C7.+, C8.2, C9.1, C13.2, C14.2, GND_CTL.1, GND_OUT.1, IC1.1 (Y1), IC1.2 (Y0), IC1.3 (Z1), IC1.5 (Z0), IC1.6 (INH), IC1.8 (GND), IC1.9 (C), IC1.10 (B), IC1.13 (X1), X1.2, X3.1
unnamed: C1.1, CTL_IN.1, T1.1 (B)
unnamed: C5.2, V_OUT.1
unnamed: R1.1, R3.2, T1.3 (C)
unnamed: R2.2, T1.2 (E)
unnamed: C2.1, C15.2, D2.3 (C), R4.1, R5.2
unnamed: C15.1, D2.1 (A1), Q1.1, R3.1
unnamed: L1.2, X1.3
unnamed: L2.2, X1.1
unnamed: C3.1, Q1.2, R6.1, R7.2, T3.1 (B)
unnamed: R8.1, T3.3 (C)
unnamed: C3.2, C4.1, C5.1, R9.2, T3.2 (E)
unnamed: BURST.1, C10.1
unnamed: C10.2, R10.1, R11.2, T4.1 (B)
unnamed: C12.1, R13.2, T4.2 (E)
unnamed: C11.1, R12.1, T4.3 (C)
unnamed: C11.2, D1.1 (A), R14.2
unnamed: C12.2, D1.2 (C), R15.1
unnamed: CTL_OUT.1, R14.1, R15.2
unnamed: IC1.12 (X0), R16.1
unnamed: D1.3 (AC), REF.1
unnamed: R16.2, X3.2
unnamed: IC1.11 (A), X2.2
unnamed: BURST_OUT.1, IC1.14 (X)
V+: C6.+, C8.1, C13.1, IC1.16 (VCC), L1.1, R1.2, R4.2, R6.2, R8.2, R10.2, R12.2
V-: C7.-, C9.2, C14.1, IC1.7 (VEE), L2.1, R2.1, R5.1, R7.1, R9.1, R11.1, R13.1

Notes on the sheet:
2015-05-24: see also paper schematic for values/changes!

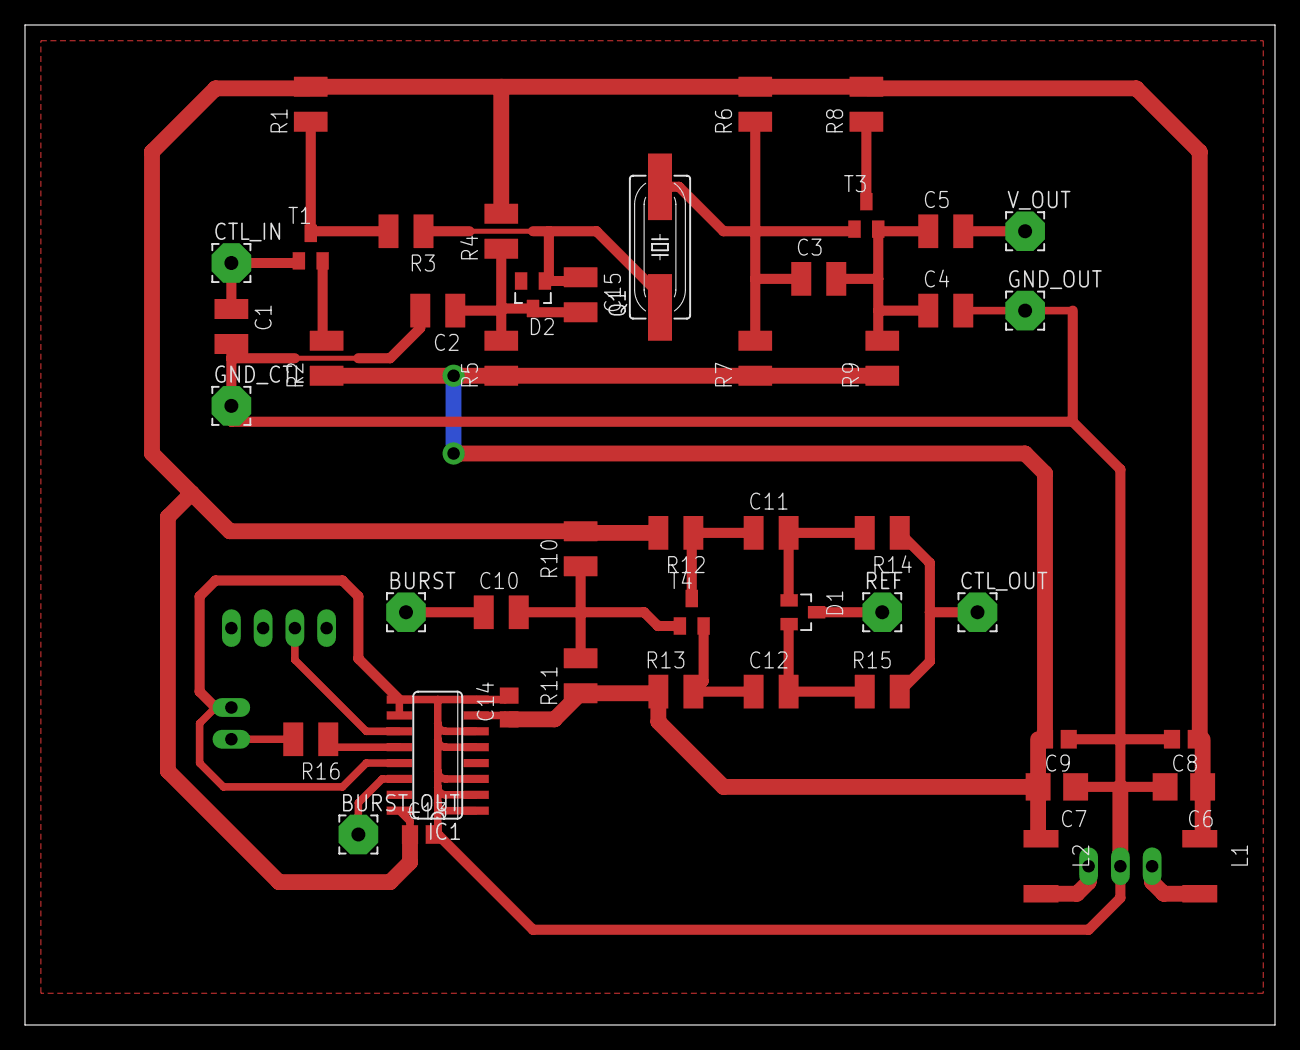
[picture p261: board subcarrier-proto.brd from above]

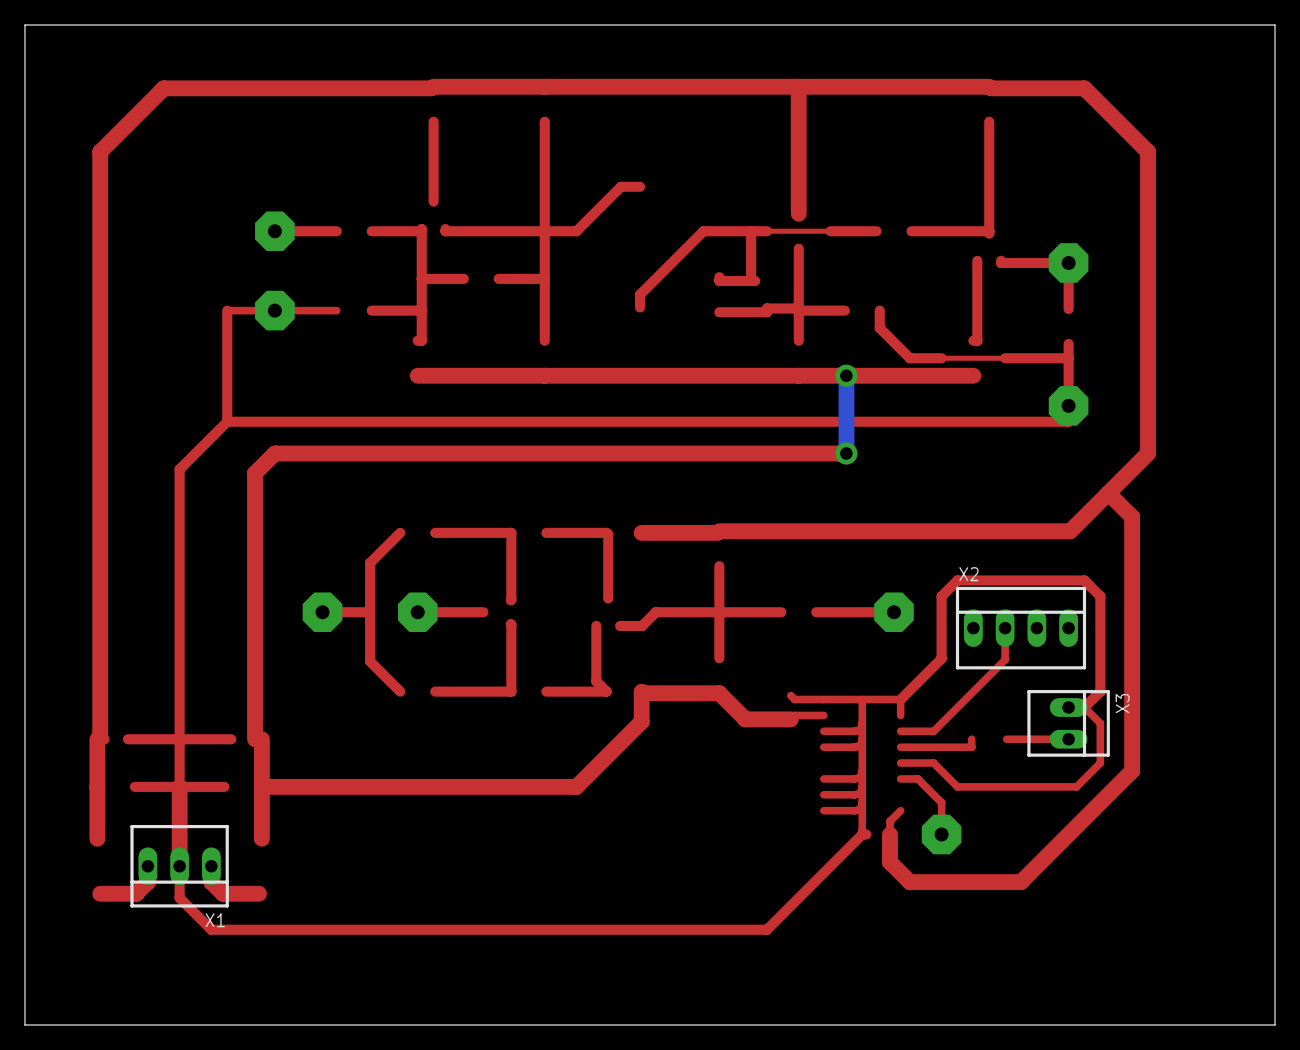
[picture p262: board subcarrier-proto.brd from below]

Board: 2 copper layers, 100.0 x 80.0 mm, 51 parts (3 on the bottom side), 26 nets.
