mirdej/synkie/eagle/sk556-time/sk556-audiopreamp.brd

## EAGLE design eagle/sk556-time/sk556-audiopreamp.brd (2014-12-29)

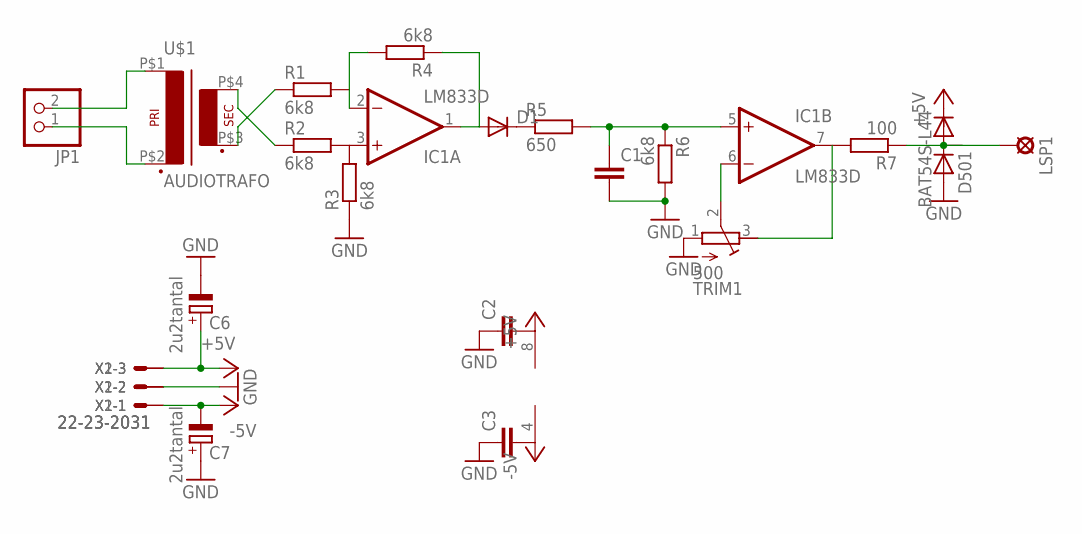
[picture p263: schematic sk556-audiopreamp.sch]

Parts:
C1, C2, C3: C-EUC1206; C1206
C6, C7: 2u2tantal; CT3528
D1: DIODE-MINIMELF; MINIMELF
D501: BAT54S-L44; SOT23
IC1: LM833D; SO08
JP1: PINHD-1X2; 1X02
LSP1: SE11
R1, R2, R3, R4, R6: 6k8; R1206
R5: 650; R1206
R7: 100; R1206
TRIM1: 500; RTRIM64Y
U$1: AUDIOTRAFO
X1, X2: 22-23-2031

Connections:
+5V: C2.2, C6.+, D501.2 (C), IC1.8 (V+), X1.3, X2.3
-5V: C3.2, C7.-, IC1.4 (V-), X1.1, X2.1
GND: C1.2, C2.1, C3.1, C6.-, C7.+, D501.1 (A), R3.1, R6.2, TRIM1.1 (E), X1.2, X2.2
unnamed: JP1.2, U$1.P$1 (P1)
unnamed: JP1.1, U$1.P$2 (P2)
unnamed: R1.1, U$1.P$3 (S3)
unnamed: R2.1, U$1.P$4 (S4)
unnamed: IC1.3 (+IN), R2.2, R3.2
unnamed: IC1.2 (-IN), R1.2, R4.2
unnamed: D1.A, IC1.1 (OUT), R4.1
unnamed: C1.1, IC1.5 (+IN), R5.2, R6.1
unnamed: IC1.6 (-IN), TRIM1.2 (S)
unnamed: IC1.7 (OUT), R7.2, TRIM1.3 (A)
unnamed: D501.3 (AC), LSP1.MP, R7.1
unnamed: D1.C, R5.1

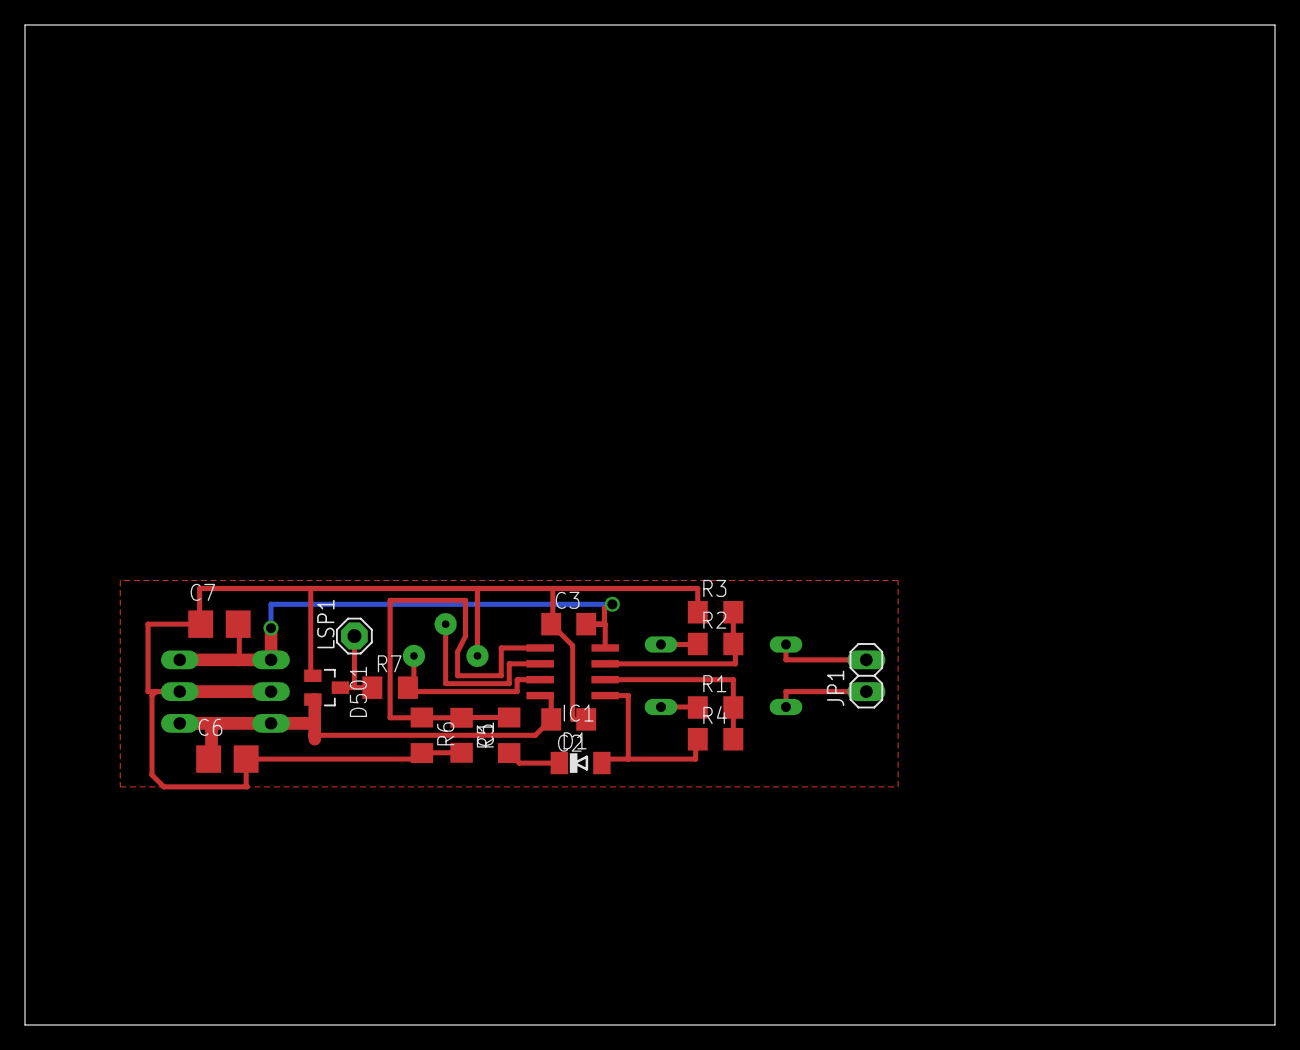
[picture p264: board sk556-audiopreamp.brd from above]

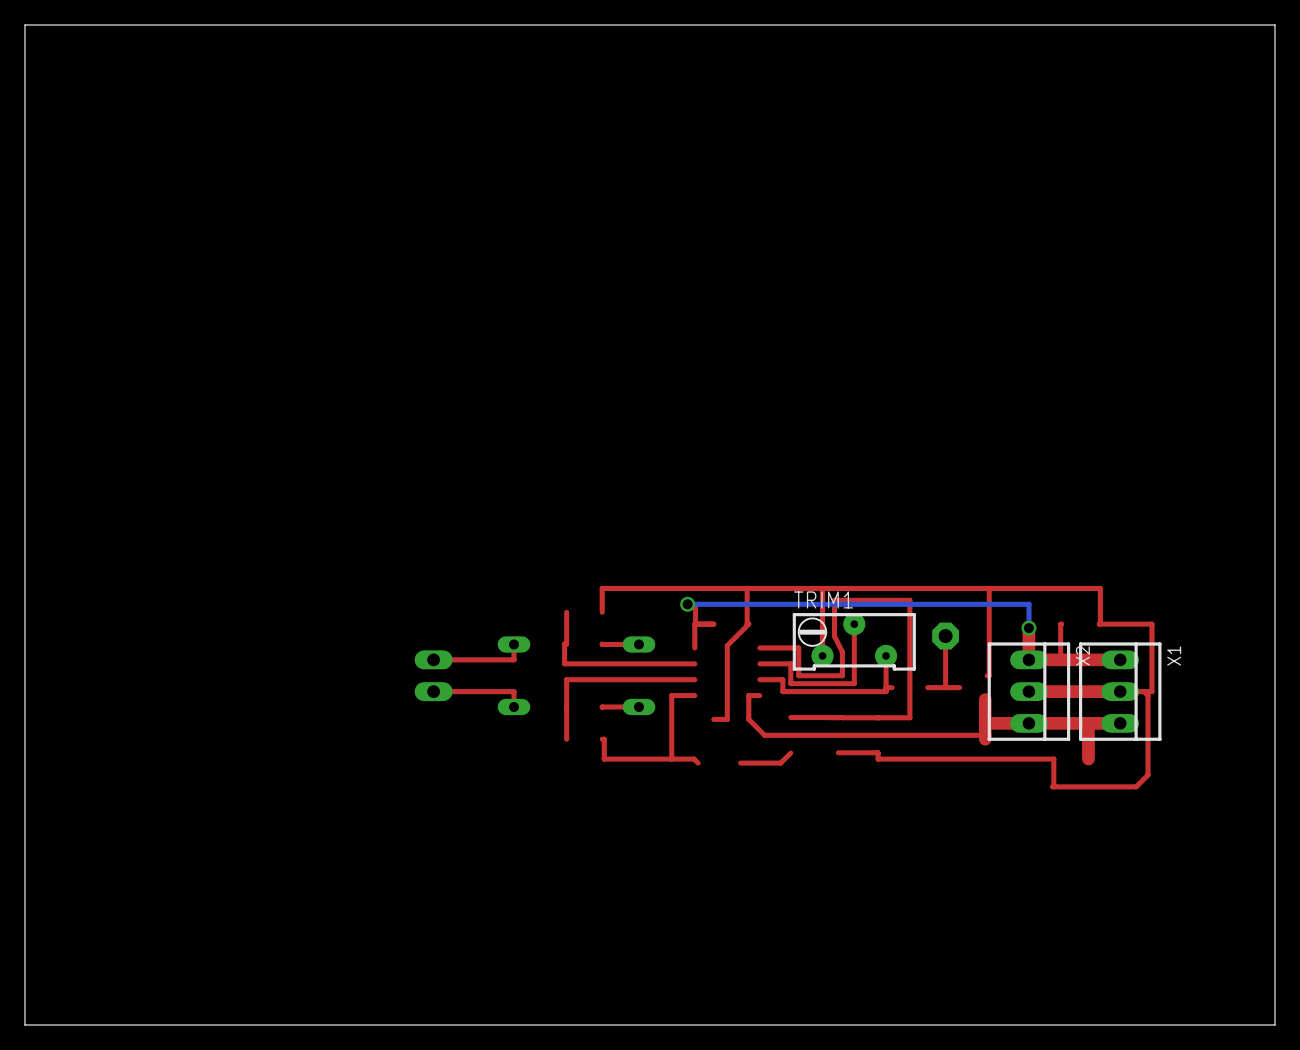
[picture p265: board sk556-audiopreamp.brd from below]

Board: 2 copper layers, 100.0 x 80.0 mm, 21 parts (4 on the bottom side), 15 nets.
