mirdej/synkie/eagle/sk-base-busdrv/sk-base-busdrv.brd

## EAGLE design eagle/sk-base-busdrv/sk-base-busdrv.brd (2014-12-29)

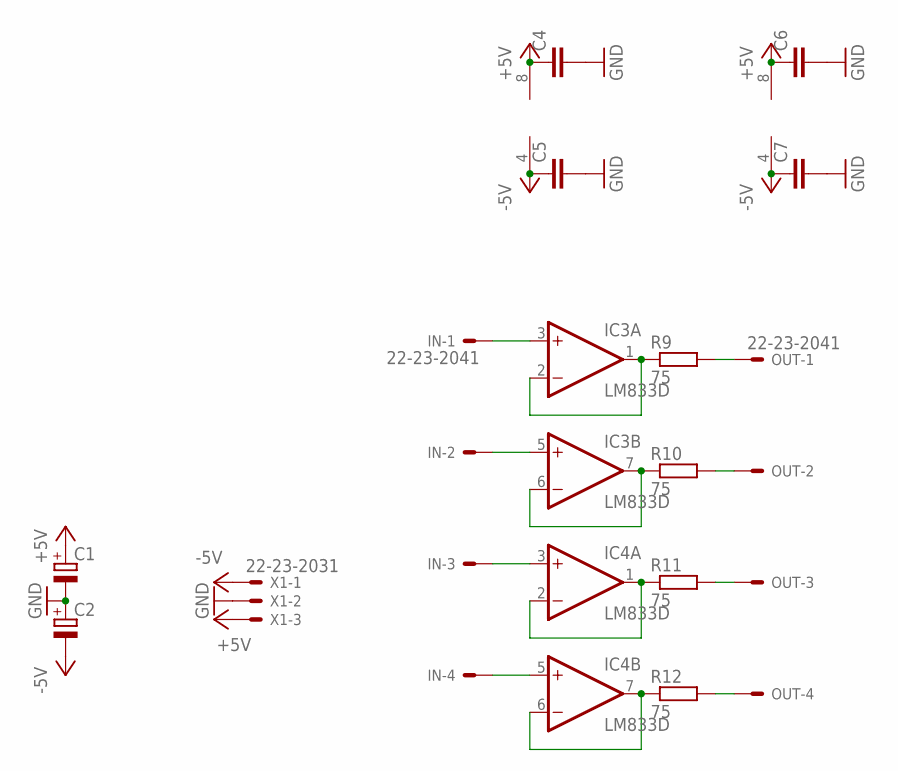
[picture p266: schematic sk-base-busdrv.sch]

Parts:
C1, C2: CPOL-EUCT6032; CT6032
C4, C5, C6, C7: C-EUC1206; C1206
IC3, IC4: LM833D; SO08
IN: 22-23-2041
OUT: 22-23-2041
R9, R10, R11, R12: 75; R1206
X1: 22-23-2031

Connections:
+5V: C1.+, C4.1, C6.1, IC3.8 (V+), IC4.8 (V+), X1.3
-5V: C2.-, C5.1, C7.1, IC3.4 (V-), IC4.4 (V-), X1.1
GND: C1.-, C2.+, C4.2, C5.2, C6.2, C7.2, X1.2
unnamed: OUT.1, R9.2
unnamed: OUT.2, R10.2
unnamed: OUT.3, R11.2
unnamed: OUT.4, R12.2
unnamed: IC4.5 (+IN), IN.4
unnamed: IC4.3 (+IN), IN.3
unnamed: IC3.5 (+IN), IN.2
unnamed: IC3.3 (+IN), IN.1
unnamed: IC3.1 (OUT), IC3.2 (-IN), R9.1
unnamed: IC3.6 (-IN), IC3.7 (OUT), R10.1
unnamed: IC4.1 (OUT), IC4.2 (-IN), R11.1
unnamed: IC4.6 (-IN), IC4.7 (OUT), R12.1

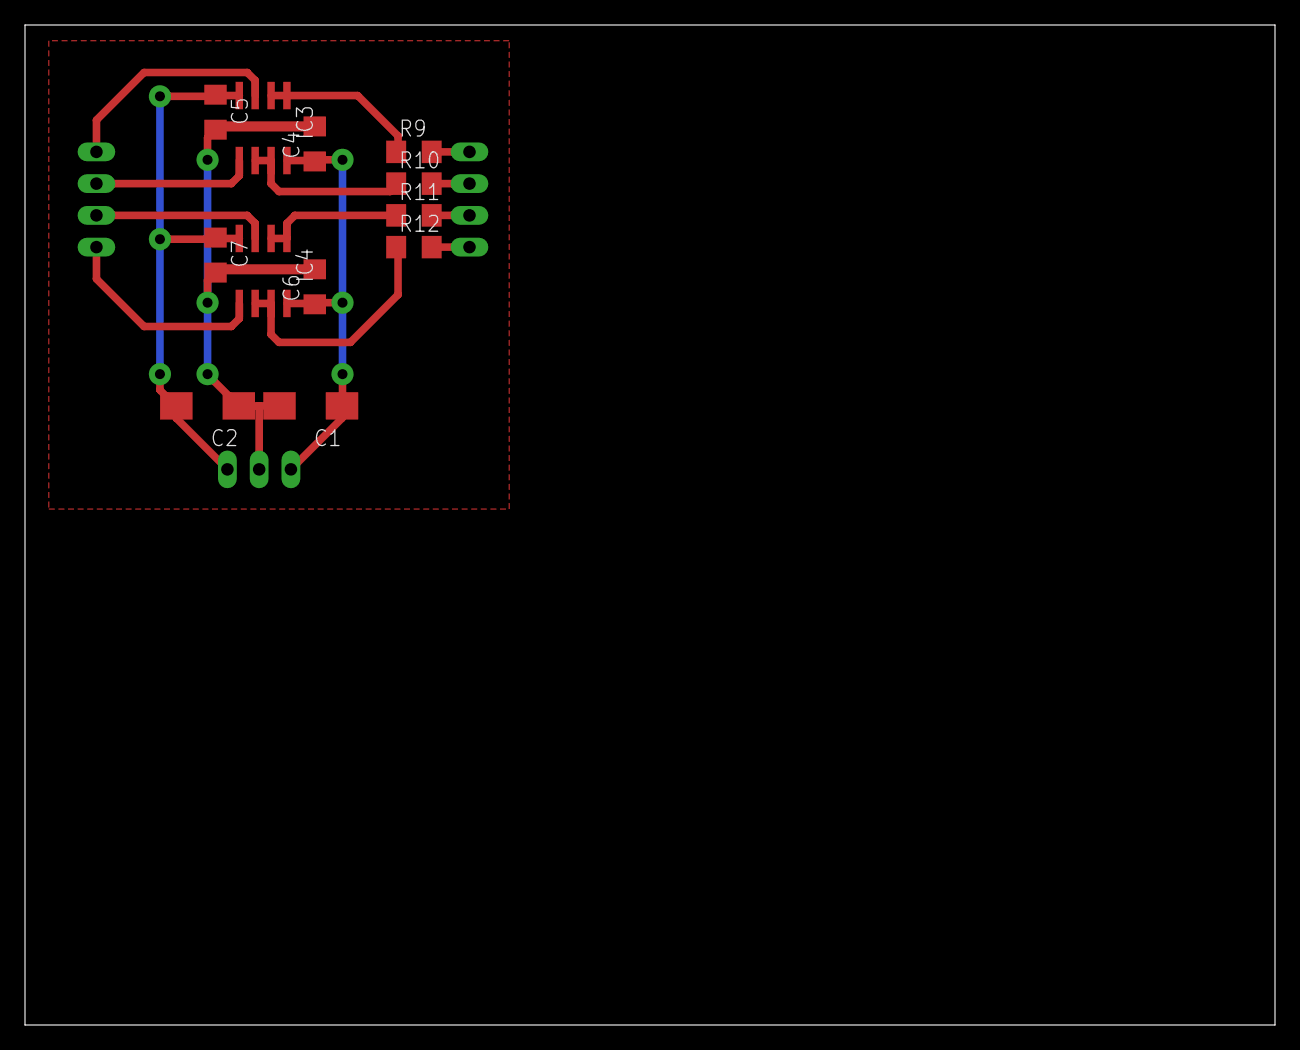
[picture p267: board sk-base-busdrv.brd from above]

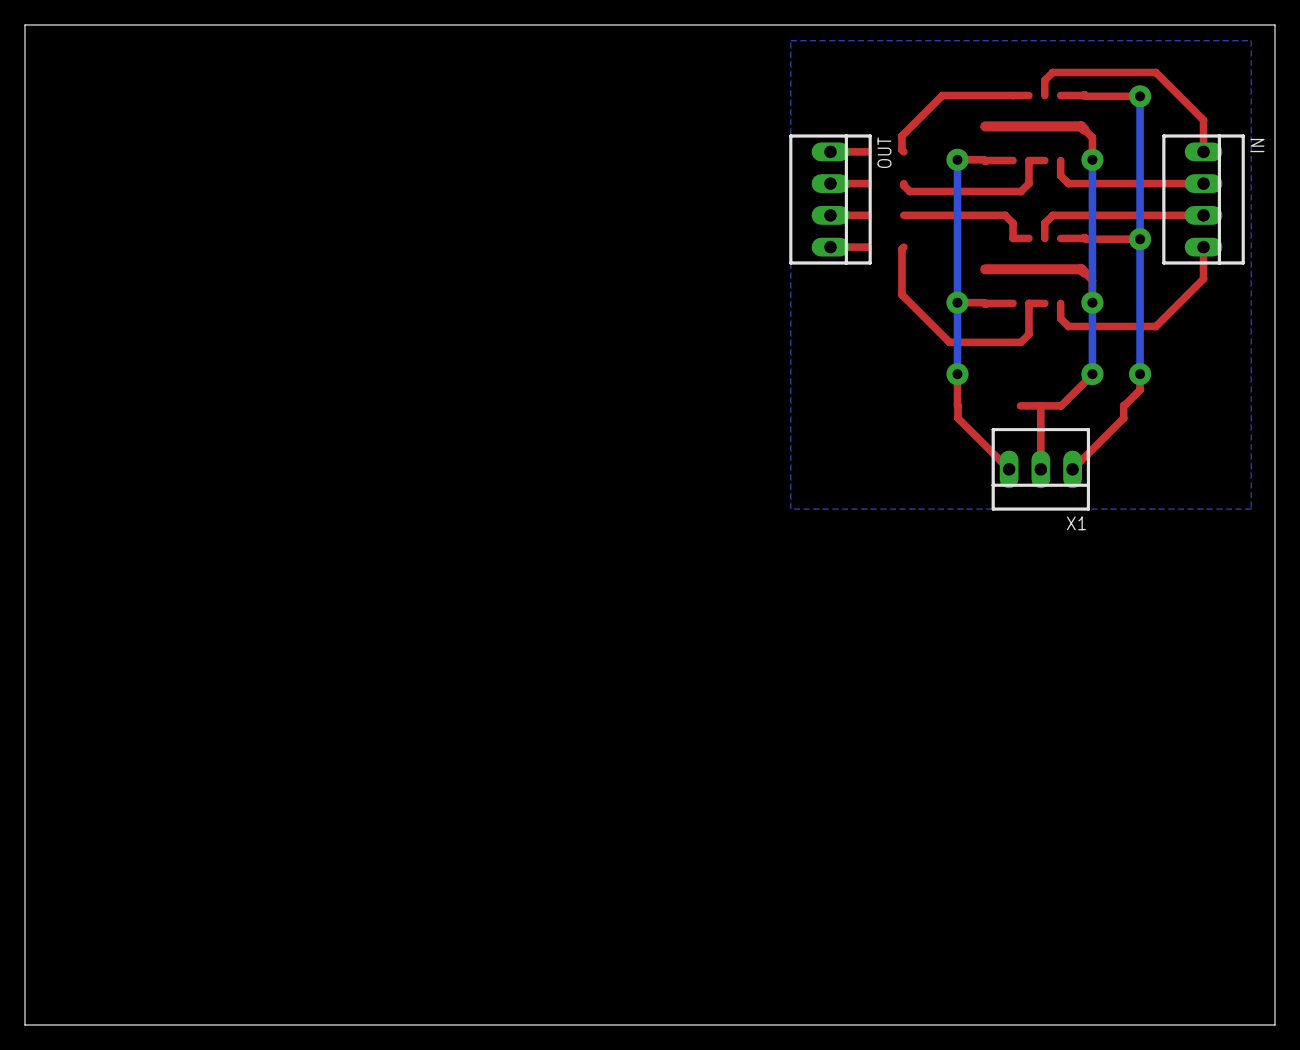
[picture p268: board sk-base-busdrv.brd from below]

Board: 2 copper layers, 100.0 x 80.0 mm, 15 parts (3 on the bottom side), 15 nets.
