mirdej/synkie/eagle/sk53-audio2cv/sk53-audio2cv.brd

## EAGLE design eagle/sk53-audio2cv/sk53-audio2cv.brd (2014-10-14)

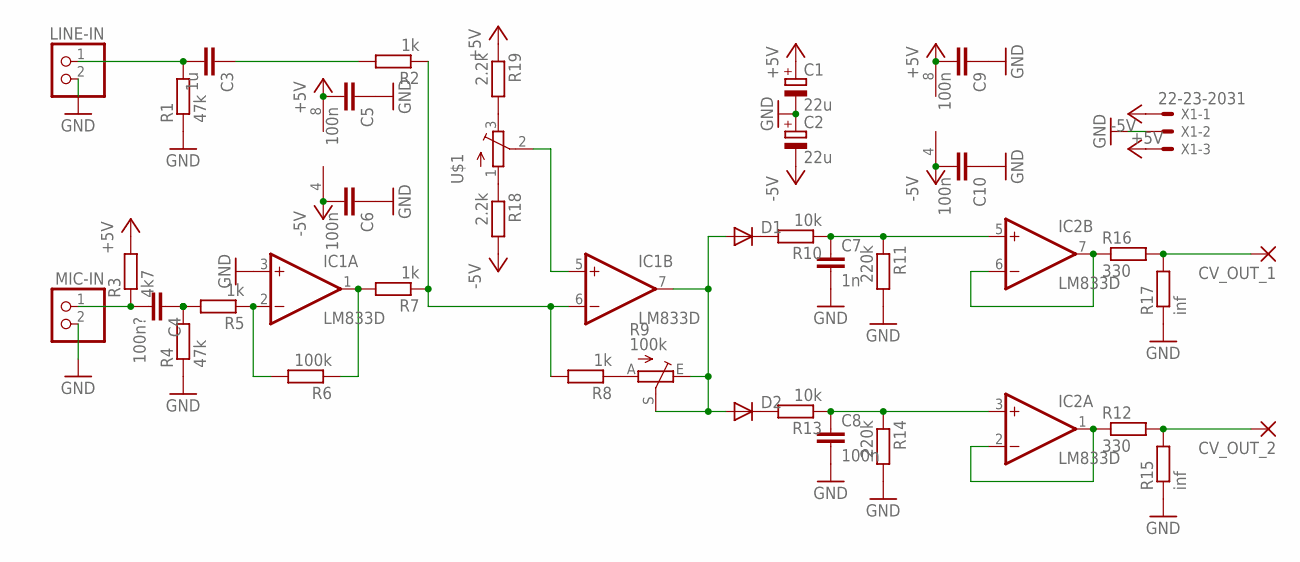
[picture p269: schematic sk53-audio2cv.sch]

Parts:
C1, C2: 22u; CT3528
C3: 1u; C1206
C4: 100n?; C1206
C5, C6, C8, C9, C10: 100n; C1206
C7: 1n; C1206
CV_OUT_1, CV_OUT_2: 3,17/1,1
D1, D2: DIODE-SMB; SMB
IC1, IC2: LM833D; SO08
LINE-IN: PINHD-1X2; 1X02
MIC-IN: PINHD-1X2; 1X02
R1, R4: 47k; R1206
R2, R5, R7, R8: 1k; R1206
R3: 4k7; R1206
R6: 100k; R1206
R9: 100k; CIP20C-6MM
R10, R13: 10k; R1206
R11, R14: 220k; R1206
R12, R16: 330; R1206
R15, R17: inf; R1206
R18, R19: 2.2k; R1206
U$1: 1k; ALPS_RK09K111
X1: 22-23-2031

Connections:
+5V: C1.+, C5.2, C9.2, IC1.8 (V+), IC2.8 (V+), R3.2, R19.1, X1.1
-5V: C2.-, C6.2, C10.2, IC1.4 (V-), IC2.4 (V-), R18.2, X1.3
GND: C1.-, C2.+, C5.1, C6.1, C7.2, C8.2, C9.1, C10.1, IC1.3 (+IN), LINE-IN.2, MIC-IN.2, R1.1, R4.1, R11.2, R14.2, R15.1, R17.1, X1.2
unnamed: C3.2, LINE-IN.1, R1.2
unnamed: C3.1, R2.2
unnamed: C4.2, MIC-IN.1, R3.1
unnamed: C4.1, R4.2, R5.2
unnamed: IC1.2 (-IN), R5.1, R6.2
unnamed: IC1.1 (OUT), R6.1, R7.2
unnamed: R19.2, U$1.3 (E)
unnamed: R8.1, R9.A
unnamed: D1.A, D2.A, IC1.7 (OUT), R9.E, R9.S
unnamed: D1.C, R10.2
unnamed: C7.1, IC2.5 (+IN), R10.1, R11.1
unnamed: IC2.6 (-IN), IC2.7 (OUT), R16.1
unnamed: CV_OUT_2.1, R12.2, R15.2
unnamed: D2.C, R13.2
unnamed: C8.1, IC2.3 (+IN), R13.1, R14.1
unnamed: IC2.1 (OUT), IC2.2 (-IN), R12.1
unnamed: CV_OUT_1.1, R16.2, R17.2
unnamed: R18.1, U$1.1 (S)
unnamed: IC1.5 (+IN), U$1.2 (W)
unnamed: IC1.6 (-IN), R2.1, R7.1, R8.2

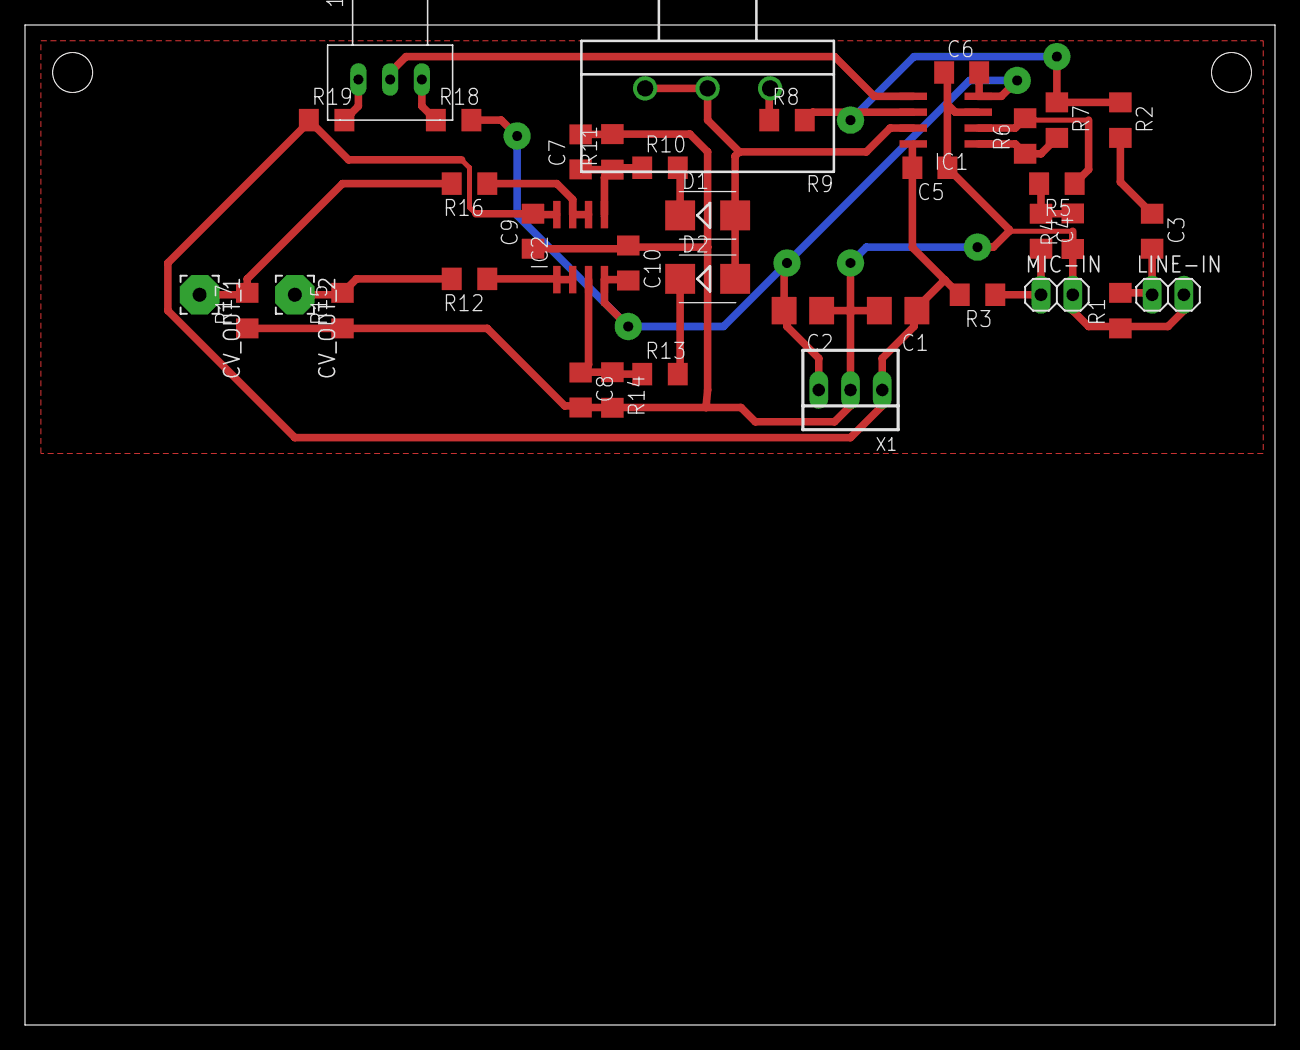
[picture p270: board sk53-audio2cv.brd from above]

Board: 2 copper layers, 100.0 x 80.0 mm, 39 parts (0 on the bottom side), 23 nets.
