mirdej/synkie/eagle/sk610-delay/vhdl/logic-schema.sch

## EAGLE design eagle/sk610-delay/vhdl/logic-schema.sch (2013-10-28)

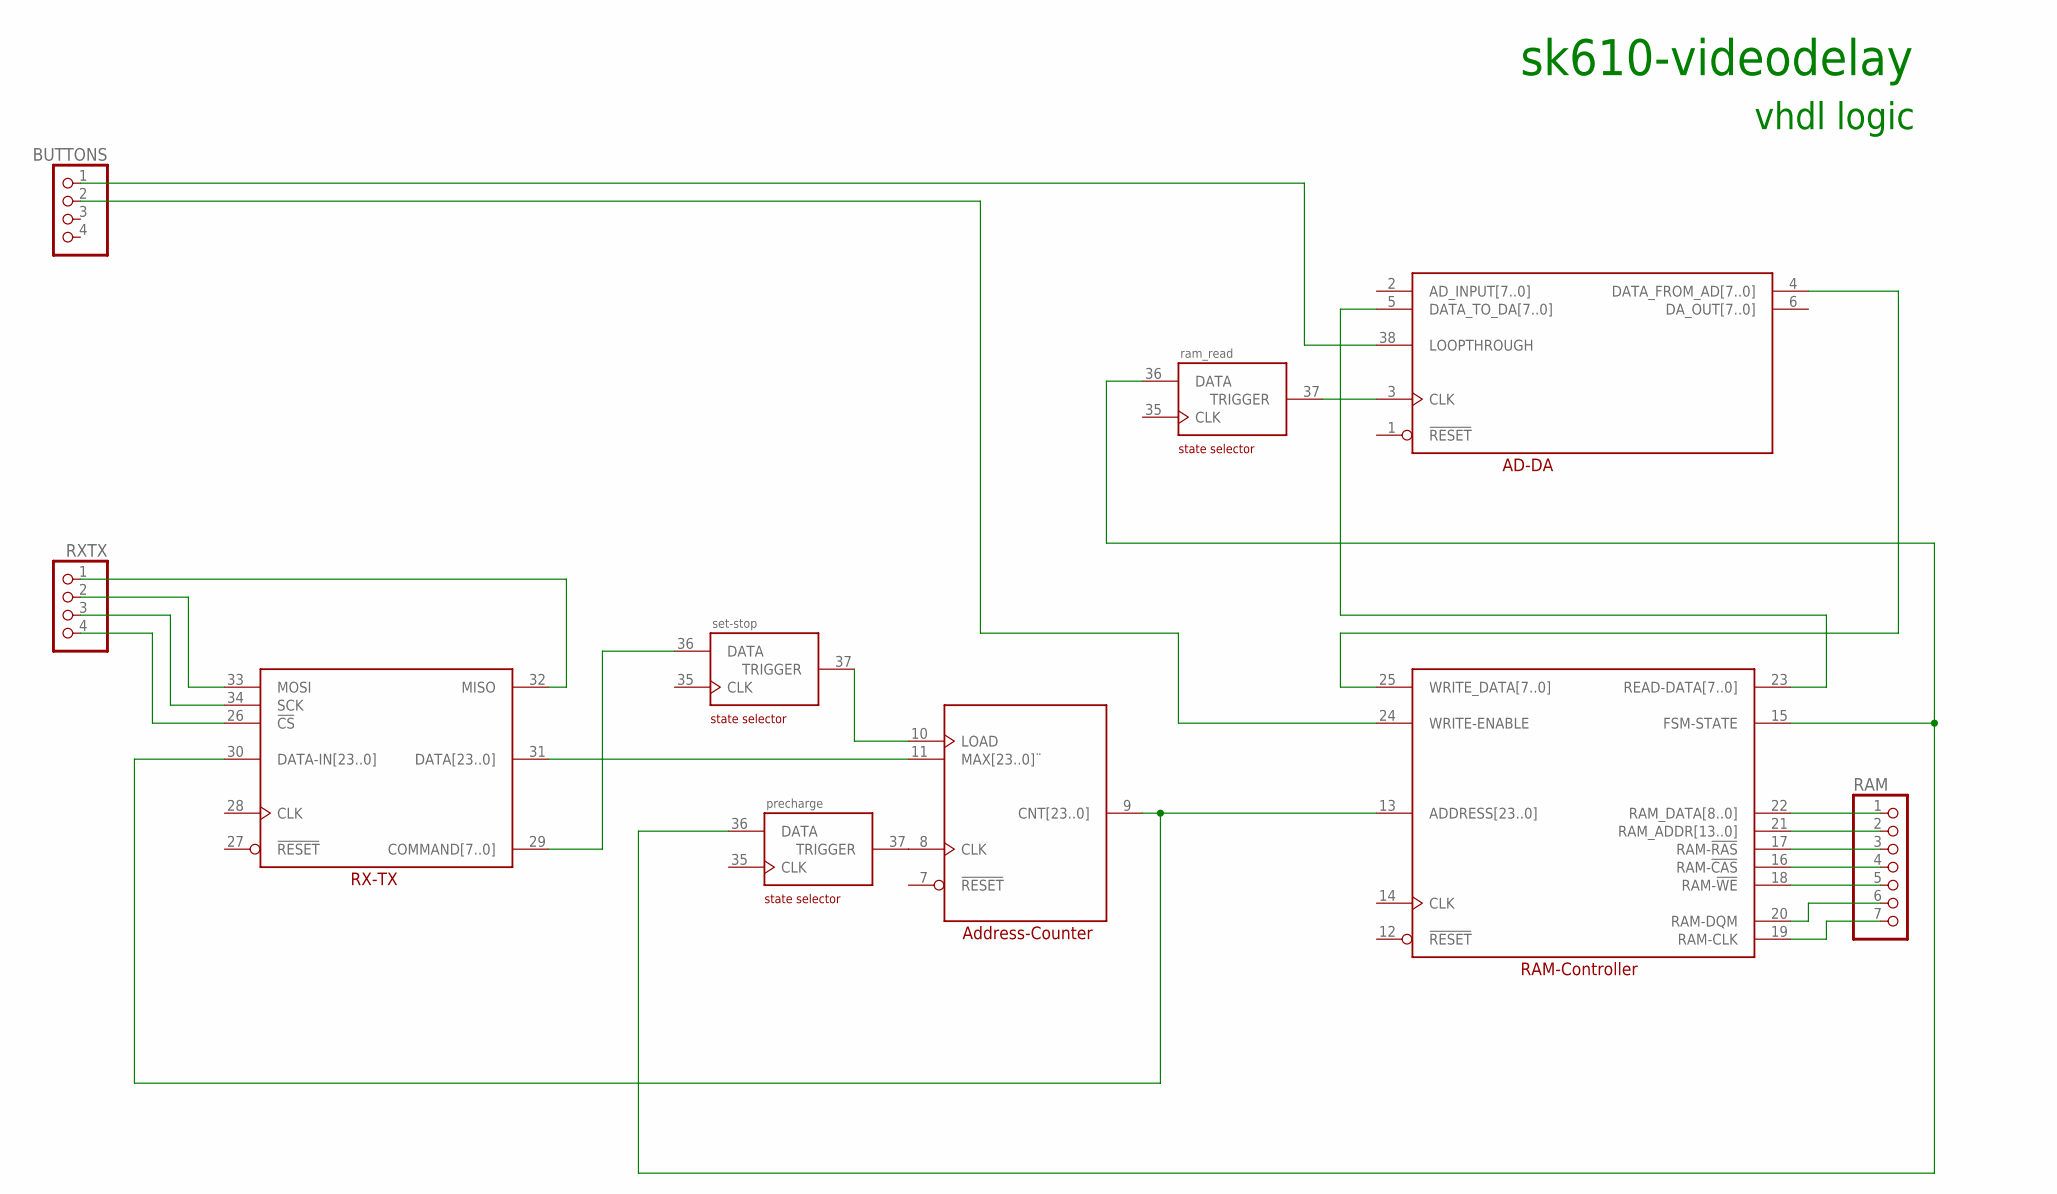
[picture p271: schematic logic-schema.sch]

Parts:
BUTTONS: PINHD-1X4; 1X04
RAM: PINHD-1X7; 1X07
RXTX: PINHD-1X4; 1X04
U$1: precharge; TQFP100
U$2: ram_read; TQFP100
U$3: set-stop; TQFP100

Connections:
unnamed: U$1.11 (MAX[23..0]¨), U$1.31 (DATA[23..0])
unnamed: U$1.8 (CLK), U$1.37 (TRIGGER)
unnamed: U$1.15 (FSM-STATE), U$1.36 (DATA), U$2.36 (DATA)
unnamed: U$1.9 (CNT[23..0]), U$1.13 (ADDRESS[23..0]), U$1.30 (DATA-IN[23..0])
unnamed: U$1.3 (CLK), U$2.37 (TRIGGER)
unnamed: U$1.4 (DATA_FROM_AD[7..0]), U$1.25 (WRITE_DATA[7..0])
unnamed: U$1.5 (DATA_TO_DA[7..0]), U$1.23 (READ-DATA[7..0])
unnamed: U$1.29 (COMMAND[7..0]), U$3.36 (DATA)
unnamed: U$1.10 (LOAD), U$3.37 (TRIGGER)
unnamed: RXTX.1, U$1.32 (MISO)
unnamed: RXTX.2, U$1.33 (MOSI)
unnamed: RXTX.3, U$1.34 (SCK)
unnamed: RXTX.4, U$1.26 (!CS)
unnamed: RAM.1, U$1.22 (RAM_DATA[8..0])
unnamed: RAM.2, U$1.21 (RAM_ADDR[13..0])
unnamed: RAM.3, U$1.17 (RAM-!RAS)
unnamed: RAM.4, U$1.16 (RAM-!CAS)
unnamed: RAM.5, U$1.18 (RAM-!WE)
unnamed: RAM.6, U$1.20 (RAM-DQM)
unnamed: RAM.7, U$1.19 (RAM-CLK)
unnamed: BUTTONS.1, U$1.38 (LOOPTHROUGH)
unnamed: BUTTONS.2, U$1.24 (WRITE-ENABLE)

Notes on the sheet:
sk610-videodelay
vhdl logic
