mirdej/synkie/kicad/experiments/sk034-allpass/sk034-allpass.sch

## KiCad design kicad/experiments/sk034-allpass/sk034-allpass.sch (2019-11-18)

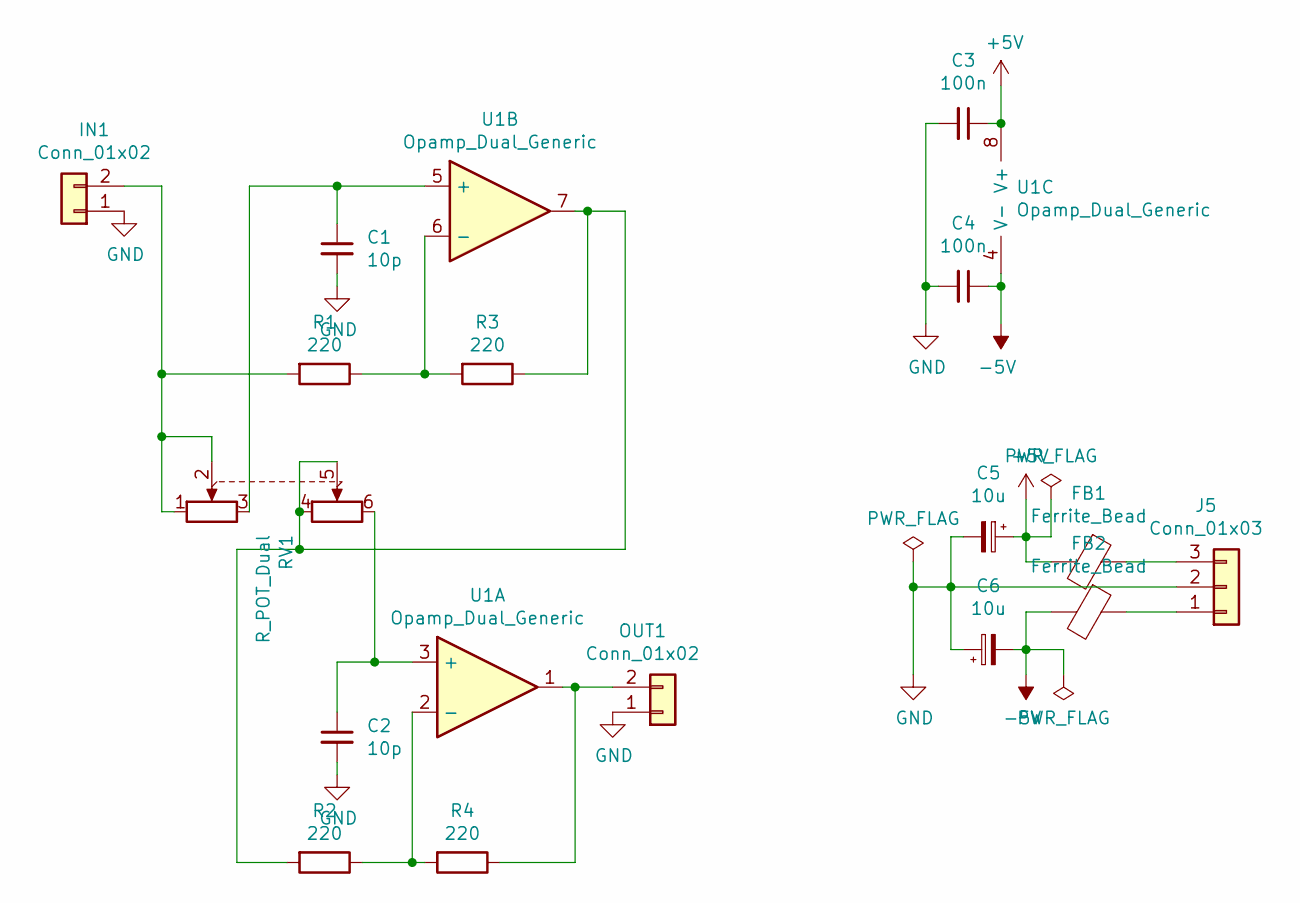
[picture p272: schematic sk034-allpass.sch]

Parts:
C1, C2: 10p; C_0805_2012Metric_Pad1.15x1.40mm_HandSolder
C3, C4: 100n; C_0603_1608Metric_Pad1.05x0.95mm_HandSolder
C5, C6: 10u; CP_EIA-3528-21_Kemet-B_Pad1.50x2.35mm_HandSolder
FB1, FB2: Ferrite_Bead; L_0805_2012Metric_Pad1.15x1.40mm_HandSolder
IN1: Conn_01x02; Molex_KK-254_AE-6410-02A_1x02_P2.54mm_Vertical
J5: Conn_01x03; Molex_KK-254_AE-6410-03A_1x03_P2.54mm_Vertical
OUT1: Conn_01x02; Molex_KK-254_AE-6410-02A_1x02_P2.54mm_Vertical
R1, R2, R3, R4: 220; R_0805_2012Metric_Pad1.15x1.40mm_HandSolder
RV1: R_POT_Dual; RK12L123
U1: Opamp_Dual_Generic; SOIC-8_3.9x4.9mm_P1.27mm

Connections:
+5V: C3.1, C5.1, FB1.2, U1.8 (V+)
-5V: C4.1, C6.2, FB2.2, U1.4 (V-)
GND: C1.2, C2.2, C3.2, C4.2, C5.2, C6.1, IN1.1, J5.2, OUT1.1
unnamed: C1.1, RV1.3, U1.5 (+)
unnamed: C2.1, RV1.6, U1.3 (+)
unnamed: FB1.1, J5.3
unnamed: FB2.1, J5.1
unnamed: IN1.2, R1.2, RV1.1, RV1.2
unnamed: OUT1.2, R4.1, U1.1
unnamed: R1.1, R3.2, U1.6 (-)
unnamed: R2.1, R4.2, U1.2 (-)
unnamed: R2.2, R3.1, RV1.4, RV1.5, U1.7
