mirdej/synkie/kicad/experiments/sk035-bwlim/sk035-bwlim.sch

## KiCad design kicad/experiments/sk035-bwlim/sk035-bwlim.sch (2019-11-11)

Schematic: sk035-bwlim.sch

Parts:
C1, C2: 100n; C_0805_2012Metric_Pad1.15x1.40mm_HandSolder
C3, C7: 47p; C_0805_2012Metric_Pad1.15x1.40mm_HandSolder
C4: 10p; C_0805_2012Metric_Pad1.15x1.40mm_HandSolder
C5, C6: 10u; CP_EIA-3528-21_Kemet-B_Pad1.50x2.35mm_HandSolder
FB1, FB2: Ferrite_Bead; L_1206_3216Metric_Pad1.42x1.75mm_HandSolder
J1, J2, J4, J5: Conn_01x01; Solderpad_1mm
J3: Conn_01x03; Molex_KK-254_AE-6410-03A_1x03_P2.54mm_Vertical
R1: 75; C_0805_2012Metric_Pad1.15x1.40mm_HandSolder
R2, R3: 220; R_0805_2012Metric_Pad1.15x1.40mm_HandSolder
R4, R6: 330; R_0805_2012Metric_Pad1.15x1.40mm_HandSolder
R5: 1k; R_0805_2012Metric_Pad1.15x1.40mm_HandSolder
R7: 75; R_0805_2012Metric_Pad1.15x1.40mm_HandSolder
U1: Opamp_Dual_Generic; SOIC-8_3.9x4.9mm_P1.27mm
