mirdej/synkie/kicad/sk161-modular-mixer/channel/sk161-modular-mixer-channel.sch

## KiCad design kicad/sk161-modular-mixer/channel/sk161-modular-mixer-channel.sch (2019-12-08)

Schematic: sk161-modular-mixer-channel.sch

Parts:
C1, C7, C8, C9: 100n; C_0603_1608Metric_Pad1.05x0.95mm_HandSolder
C2, C4: 10u; CP_EIA-3528-21_Kemet-B_Pad1.50x2.35mm_HandSolder
C3, C6: 4u7; CP_EIA-3528-21_Kemet-B_Pad1.50x2.35mm_HandSolder
C5, C10: 1u; C_0603_1608Metric_Pad1.05x0.95mm_HandSolder
D1, D2: BAT54S; SOT-23
FB1, FB2: 330u; L_0805_2012Metric_Pad1.15x1.40mm_HandSolder
J1: Conn_01x10; IDC-Header_2x05_P2.54mm_Vertical
J2: In_1; Solderpad_1mm
J5: CV_1; Solderpad_1mm
Q1: PNP; SOT-23_BEC
R1, R7, R8, R14: 100; R_0805_2012Metric_Pad1.15x1.40mm_HandSolder
R2, R10: 1k; R_0805_2012Metric_Pad1.15x1.40mm_HandSolder
R3, R16: 47k; R_0805_2012Metric_Pad1.15x1.40mm_HandSolder
R4: 120; R_0805_2012Metric_Pad1.15x1.40mm_HandSolder
R11: 1k5; R_0805_2012Metric_Pad1.15x1.40mm_HandSolder
R12: 100k; R_0805_2012Metric_Pad1.15x1.40mm_HandSolder
R13: 20k; R_0805_2012Metric_Pad1.15x1.40mm_HandSolder
R15: 15k; R_0805_2012Metric_Pad1.15x1.40mm_HandSolder
R17: 22k56; R_0805_2012Metric_Pad1.15x1.40mm_HandSolder
R18, R19, R20: 3k; R_0805_2012Metric_Pad1.15x1.40mm_HandSolder
RV1: 10k; Potentiometer_Alps_RS6011xP_Slide
RV2: 500; Potentiometer_Bourns_3296Y_Vertical
U1: LT1228; SOIC-8_3.9x4.9mm_P1.27mm
U2: LMH6643; SOIC-8_3.9x4.9mm_P1.27mm

Notes on the sheet:
black level
gain control
video
