mirdej/synkie/kicad/sk162-herd-mixer/channel/channel.kicad_sch

## KiCad design kicad/sk162-herd-mixer/channel/channel.kicad_sch (2025-10-21)

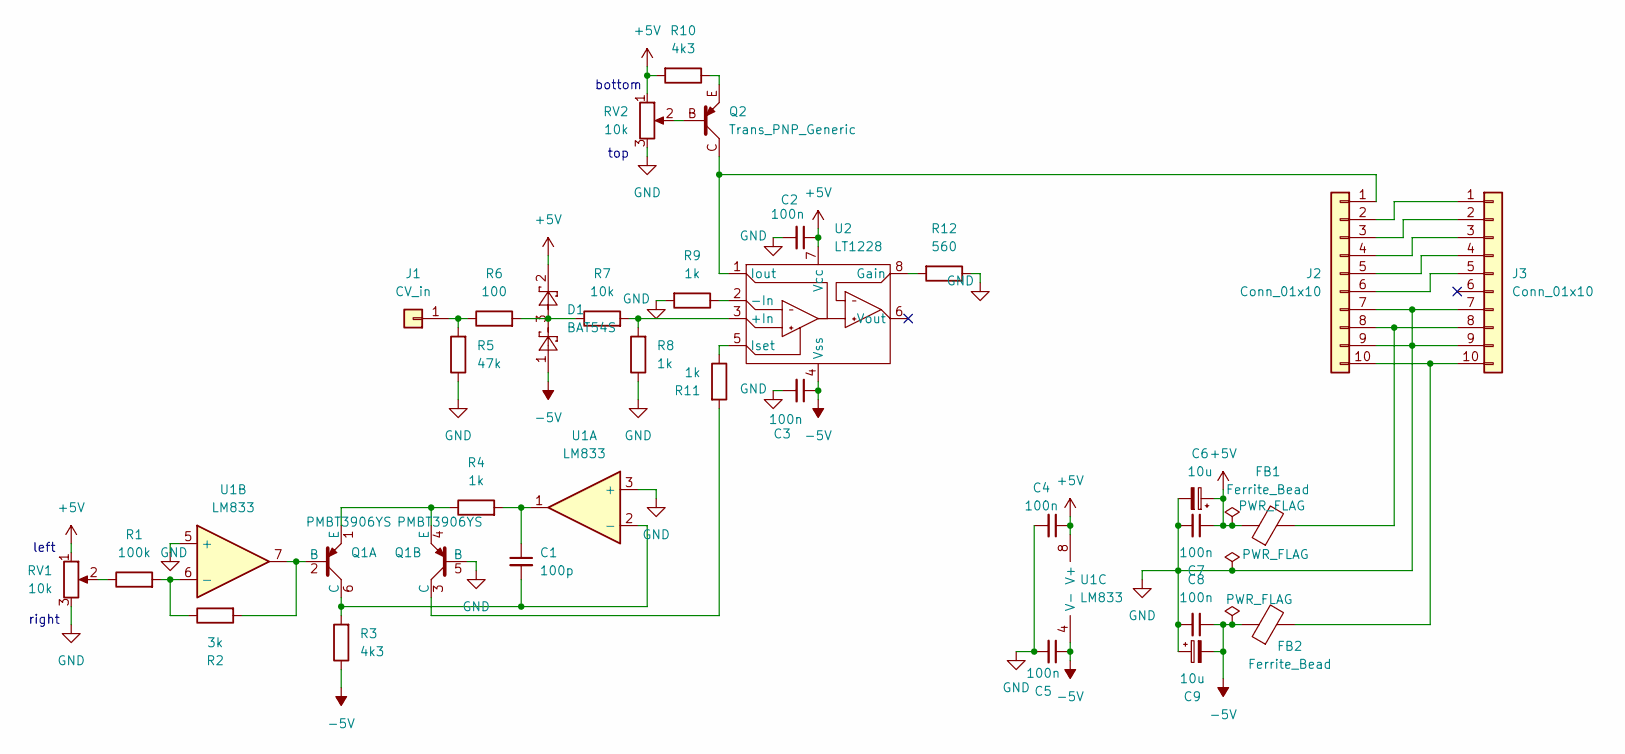
[picture p273: schematic channel.kicad_sch]

Parts:
C1: 100p
C2, C3, C4, C5, C7, C8: 100n
C6, C9: 10u
D1: BAT54S; SOT-23
FB1, FB2: Ferrite_Bead
J1: CV_in
J2, J3: Conn_01x10
Q1: PMBT3906YS
Q2: Trans_PNP_Generic
R1: 100k
R2: 3k
R3, R10: 4k3
R4, R8, R9, R11: 1k
R5: 47k
R6: 100
R7: 10k
R12: 560
RV1: 10k; Potentiometer_Alps_RK09K_Single_Vertical
RV2: 10k; Potentiometer_Alps_RS6011xP_Slide
U1: LM833; SOIC-8_3.9x4.9mm_P1.27mm
U2: LT1228; SOIC-8_3.9x4.9mm_P1.27mm

Connections:
+5V: C2.1, C4.1, C6.1, C7.1, D1.2, FB1.1, R10.2, RV1.1, RV2.1, U1.8 (V+), U2.7 (Vcc)
-5V: C3.1, C5.1, C8.1, C9.2, D1.1, FB2.1, R3.1, U1.4 (V-), U2.4 (Vss)
GND: C2.2, C3.2, C4.2, C5.2, C6.2, C7.2, C8.2, C9.1, J2.7, J2.9, J3.7, J3.9, Q1.5 (B), R5.1, R8.1, R9.2, R12.1, RV1.3, RV2.3, U1.3 (+), U1.5 (+)
unnamed: C1.1, R4.2, U1.1
unnamed: C1.2, Q1.6 (C), R3.2, U1.2 (-)
unnamed: D1.3, R6.2, R7.1
unnamed: FB1.2, J2.8, J3.8
unnamed: FB2.2, J2.10, J3.10
unnamed: J1.1, R5.2, R6.1
unnamed: J2.1, Q2.C, U2.1 (Iout)
unnamed: J2.2, J3.1
unnamed: J2.3, J3.2
unnamed: J2.4, J3.3
unnamed: J2.5, J3.4
unnamed: J2.6, J3.5
unnamed: Q1.1 (E), Q1.4 (E), R4.1
unnamed: Q1.2 (B), R2.2, U1.7
unnamed: Q1.3 (C), R11.2
unnamed: Q2.B, RV2.2
unnamed: Q2.E, R10.1
unnamed: R1.1, RV1.2
unnamed: R1.2, R2.1, U1.6 (-)
unnamed: R7.2, R8.2, U2.3 (+In)
unnamed: R9.1, U2.2 (-In)
unnamed: R11.1, U2.5 (Iset)
unnamed: R12.2, U2.8 (Gain)

Notes on the sheet:
bottom
top
left
right
