mirdej/synkie/kicad/sk162-herd-mixer/mixer/black-level-a.kicad_sch

## KiCad design kicad/sk162-herd-mixer/mixer/black-level-a.kicad_sch (2025-10-21)

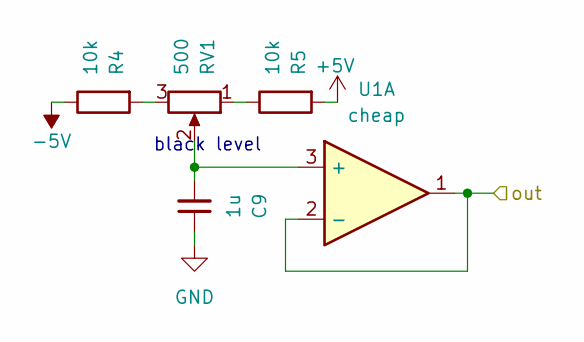
[picture p274: schematic black-level-a.kicad_sch]

Parts:
C9: 1u; C_0805_2012Metric_Pad1.15x1.40mm_HandSolder
R4, R5: 10k; R_0805_2012Metric_Pad1.15x1.40mm_HandSolder
RV1: 500; Potentiometer_Bourns_3296Y_Vertical
U1: cheap; SOIC-8_3.9x4.9mm_P1.27mm

Connections:
+5V: R5.2
-5V: R4.1
GND: C9.1
unnamed: C9.2, RV1.2, U1.3 (+)
unnamed: R4.2, RV1.3
unnamed: R5.1, RV1.1
out: U1.1, U1.2 (-)

Notes on the sheet:
black level
