mirdej/synkie/kicad/sk162-herd-mixer/mixer/black-level-b.kicad_sch

## KiCad design kicad/sk162-herd-mixer/mixer/black-level-b.kicad_sch (2025-10-21)

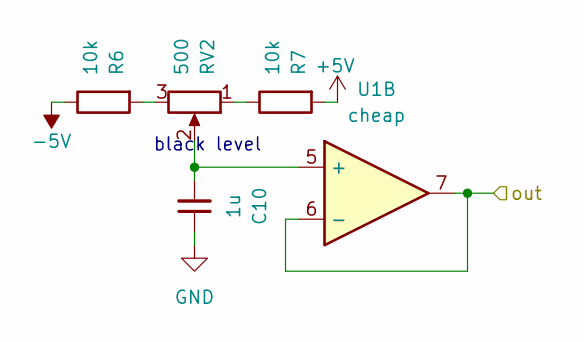
[picture p275: schematic black-level-b.kicad_sch]

Parts:
C10: 1u; C_0805_2012Metric_Pad1.15x1.40mm_HandSolder
R6, R7: 10k; R_0805_2012Metric_Pad1.15x1.40mm_HandSolder
RV2: 500; Potentiometer_Bourns_3296Y_Vertical
U1: cheap; SOIC-8_3.9x4.9mm_P1.27mm

Connections:
+5V: R7.2
-5V: R6.1
GND: C10.1
unnamed: C10.2, RV2.2, U1.5 (+)
unnamed: R6.2, RV2.3
unnamed: R7.1, RV2.1
out: U1.6 (-), U1.7

Notes on the sheet:
black level
