mirdej/synkie/kicad/sk162-herd-mixer/mixer/mixer-channel.kicad_sch

## KiCad design kicad/sk162-herd-mixer/mixer/mixer-channel.kicad_sch (2025-10-21)


Parts:
C11: 1u; C_0805_2012Metric_Pad1.15x1.40mm_HandSolder
C12, C13: 100n; C_0603_1608Metric_Pad1.05x0.95mm_HandSolder
D1: BAT54S; SOT-23
R8: 100; R_0805_2012Metric_Pad1.15x1.40mm_HandSolder
R9, R11: 10k; R_0805_2012Metric_Pad1.15x1.40mm_HandSolder
R10, R12, R13: 1k; R_0805_2012Metric_Pad1.15x1.40mm_HandSolder
R14: 560; R_0805_2012Metric_Pad1.15x1.40mm_HandSolder
U4: LT1228; SOIC-8_3.9x4.9mm_P1.27mm

Connections:
+5V: C12.2, D1.2, U4.7 (Vcc)
-5V: C13.2, D1.1, U4.4 (Vss)
GND: C11.1, C12.1, C13.1, R10.1, R12.1, R14.1
unnamed: C11.2, R11.2, R12.2, U4.2 (-In)
unnamed: D1.3, R8.2, R9.1
unnamed: R9.2, R10.2, U4.3 (+In)
unnamed: R13.2, U4.5 (Iset)
black: R11.1
fb: R14.2, U4.8 (Gain)
in: R8.1
iset: R13.1
mix: U4.1 (Iout)
out: U4.6 (Vout)
