mirdej/synkie/kicad/sk162-herd-mixer/mixer/mixer.kicad_sch

## KiCad design kicad/sk162-herd-mixer/mixer/mixer.kicad_sch (2025-10-21)


Parts:
C1, C2, C3, C4, C5, C6: 100n; C_0603_1608Metric_Pad1.05x0.95mm_HandSolder
C7, C8: 10u; CP_EIA-3528-21_Kemet-B_Pad1.50x2.35mm_HandSolder
FB1, FB2: 330u; L_0805_2012Metric_Pad1.15x1.40mm_HandSolder
J1: CH1; Solderpad_1mm
J2: CH2; Solderpad_1mm
J3: CH3; Solderpad_1mm
J4: CH4; Solderpad_1mm
J5: CH5; Solderpad_1mm
J6: CH6; Solderpad_1mm
J7: Out; Solderpad_1mm
J8: Conn_01x10; PinHeader_1x10_P2.54mm_Vertical
J9: Power; Molex_KK-254_AE-6410-03A_1x03_P2.54mm_Vertical
R1, R2: 560; R_0805_2012Metric_Pad1.15x1.40mm_HandSolder
R3: 75; R_0805_2012Metric_Pad1.15x1.40mm_HandSolder
U1, U2, U3: cheap; SOIC-8_3.9x4.9mm_P1.27mm

Connections:
+5V: C1.2, C3.2, C5.2, C7.1, FB1.2, U1.8 (V+), U2.8 (V+), U3.8 (V+)
-5V: C2.2, C4.2, C6.2, C8.2, FB2.2, U1.4 (V-), U2.4 (V-), U3.4 (V-)
GND: C1.1, C2.1, C3.1, C4.1, C5.1, C6.1, C7.2, C8.1, J8.7, J8.9, J9.2, R1.2
unnamed: FB1.1, J8.8, J9.3
unnamed: FB2.1, J8.10, J9.1
unnamed: J7.1, R3.1
fb: R2.1
in: J1.1, J2.1, J3.1, J4.1, J5.1, J6.1
iset: J8.1, J8.2, J8.3, J8.4, J8.5, J8.6
mix: R1.1
out: R2.2, R3.2
