mirdej/synkie/kicad/sk245-oscar-vcf-vca/sk245-oscar-cv-in/sk245-oscar-cv-in.sch

## KiCad design kicad/sk245-oscar-vcf-vca/sk245-oscar-cv-in/sk245-oscar-cv-in.sch (2021-10-15)


Parts:
C1, C2, C3, C4, C5, C6, C7, C8: 100n; C_0603_1608Metric_Pad1.05x0.95mm_HandSolder
FB1, FB2: Ferrite_Bead; L_0805_2012Metric_Pad1.15x1.40mm_HandSolder
H1, H2: MountingHole_Pad; MountingHole_3.2mm_M3_Pad
J1, J4: Conn_01x03; Molex_KK-254_AE-6410-03A_1x03_P2.54mm_Vertical
J2, J5, J7, J9: CV-IN-(0V-1V); Solderpad_1mm
J3, J6, J8, J10: CV-OUT(-5V to +5V); Solderpad_1mm
R1, R5, R8, R11, R14, R17, R20, R23: 100k; R_0805_2012Metric_Pad1.15x1.40mm_HandSolder
R2, R3, R4, R6, R7, R9, R10, R12, R13, R15, R16, R18, R19, R21, R22, R24, R25: 10k; R_0805_2012Metric_Pad1.15x1.40mm_HandSolder
RV1, RV2, RV3, RV4: R_POT; Potentiometer_Alps_RK09K_Single_Horizontal
U1, U3, U4, U5: TLV272; SOIC-8_3.9x4.9mm_P1.27mm
U2: ADR510; SOT-23

Connections:
+1V0: R2.1, RV1.3, RV2.3, RV3.3, RV4.3, U2.1 (V+)
+5V: C1.1, C3.1, C5.1, C7.1, FB1.2, R1.2, R2.2, R8.2, R14.2, R20.2, U1.8 (V+), U3.8 (V+), U4.8 (V+), U5.8 (V+)
-5V: C2.1, C4.1, C6.1, C8.1, FB2.2, U1.4 (V-), U3.4 (V-), U4.4 (V-), U5.4 (V-)
GND: C1.2, C2.2, C3.2, C4.2, C5.2, C6.2, C7.2, C8.2, H1.1, H2.1, J1.2, J4.2, RV1.1, RV2.1, RV3.1, RV4.1, U1.3 (+), U1.5 (+), U2.2 (V-), U3.3 (+), U3.5 (+), U4.3 (+), U4.5 (+), U5.3 (+), U5.5 (+)
unnamed: FB1.1, J1.1, J4.1
unnamed: FB2.1, J1.3, J4.3
unnamed: J2.1, R3.2
unnamed: J3.1, R5.1, U1.7
unnamed: J5.1, R9.2
unnamed: J6.1, R11.1, U3.7
unnamed: J7.1, R15.2
unnamed: J8.1, R17.1, U4.7
unnamed: J9.1, R21.2
unnamed: J10.1, R23.1, U5.7
unnamed: R1.1, R5.2, R6.1, U1.6 (-)
unnamed: R3.1, R4.2, R7.1, U1.2 (-)
unnamed: R4.1, R6.2, U1.1
unnamed: R7.2, RV1.2
unnamed: R10.1, R12.2, U3.1
unnamed: R9.1, R10.2, R13.1, U3.2 (-)
unnamed: R8.1, R11.2, R12.1, U3.6 (-)
unnamed: R13.2, RV2.2
unnamed: R14.1, R17.2, R18.1, U4.6 (-)
unnamed: R15.1, R16.2, R19.1, U4.2 (-)
unnamed: R16.1, R18.2, U4.1
unnamed: R19.2, RV3.2
unnamed: R20.1, R23.2, R24.1, U5.6 (-)
unnamed: R21.1, R22.2, R25.1, U5.2 (-)
unnamed: R22.1, R24.2, U5.1
unnamed: R25.2, RV4.2
