mirdej/synkie/eagle/sk720-step-sequencer/firmware/main.c

//---------------------------------------------------------------------------------------------
//	SK720	8 Step Sequencer										ATMEGA88
//
//
//
// 	Part of the Synkie Project: www.synkie.net
//
// 	© 2017 Michael Egger, Licensed under GNU GPLv3
//
//--------------------------------------------------------------------------------------------
// ==============================================================================
// includes
// ------------------------------------------------------------------------------
// AVR Libc (see http://www.nongnu.org/avr-libc/)
#include <avr/io.h>			// include I/O definitions (port names, pin names, etc)
#include <avr/wdt.h>		// include watchdog timer support
#include <avr/interrupt.h>	// include interrupt support
#include "light_ws2812.h"
#include <util/delay.h>

// ==============================================================================
// Globals
// ------------------------------------------------------------------------------

unsigned char insync; 			// flag if we're changing outputs synced to video frame rate
unsigned char step_idx;
unsigned char steps[8];
unsigned char last_buttons[5];
unsigned char last_pinc;

unsigned char bank;

#define PIXELS 36
#define COLORLENGTH (PIXELS/2)
#define FADE (256/COLORLENGTH)
struct cRGB colors[8];
struct cRGB led[PIXELS];
unsigned char leds_changed;
unsigned char trigger_inhibit;

// ==============================================================================
// Functions
// ------------------------------------------------------------------------------

void output() {
	PORTC = (PORTC & 0XF8) | (step_idx & 0x07);	// output address
	PORTD = steps[step_idx];						// set muxes
	leds_changed = 1;
}

void trigger() {	
	step_idx++;
	step_idx %=8;
	if (!insync) {
		output();
	}
}


//------------------------------------------ check SPI

unsigned char SPI_transmit(unsigned char cData) {
	SPDR = cData;
	while(!(SPSR & (1 << SPIF))){ ; }
	return SPDR;
}

void checkSPI(void) {
	unsigned char i,j,triggers,temp,step,mux;

	PORTB |= (1 << 2); // latch
	for (j = 0; j<5; j++ ) {
		temp = SPI_transmit(0);
		temp = ~temp;

		if (temp != last_buttons[j]) {
			
			triggers = temp & ~last_buttons[j];

			for (i = 0; i < 8; i++) {
				if (triggers & (1 << i)) {
					leds_changed = 1;
					
					if (j == 4) {				// bank select
						if (i > 3) {				// don't look at unconnected row
							bank = i - 4;
						}
					} else {					// set step
						step = j*2;
						if (i > 3) {
							step++;
							mux = i-4;
						} else {
							mux = i;
						}
						
						steps[step] &= ~(0x03 	<< (bank*2));		// mask
						steps[step] |= (mux 	<< (bank*2));		// set new value
					}
				}
			}	
		}
		last_buttons[j] = temp;
	}
	PORTB &= ~(1 << 2); // unlatch
}


void update_leds() {
	if (!leds_changed) return;
	leds_changed = 0;
	
	unsigned char i,a;
	struct cRGB color1,color2;
	color1 		= colors[bank+2];
	color2.r 	= 15;
	color2.g 	= 15;	
	color2.b 	= 15;
	
	for (i = 0; i < 36; i++) { // set all to black first, I'm too lazy
		led[i] = colors[0]; 		// black
	}

	for (i = 0; i < 8; i++ ) {
		if (i == step_idx) {
			led[(i*4)] 		= color2;
			led[(i*4) + 1] 	= color2;
			led[(i*4) + 2] 	= color2;
			led[(i*4) + 3] 	= color2;
		}
		
		a = steps[i] >> (bank * 2);
		a &= 0x03;
		led[(i*4)+a] = color1;
	}
	
	led[32 + bank] = color1; 			// bank color
}

// ------------------------------------------------------------------------------
// Init
// ------------------------------------------------------------------------------
void init (void) {
	step_idx = 0;
	
	
	//Rainbowcolors
    colors[0].r=0; colors[0].g=0; colors[0].b=0;	// black
    colors[1].r=64; colors[1].g=000; colors[1].b=000;//red
    colors[2].r=64; colors[2].g=25; colors[2].b=000;//orange
    colors[3].r=64; colors[3].g=64; colors[3].b=000;//yellow
    colors[4].r=000; colors[4].g=64; colors[4].b=000;//green
    colors[5].r=000; colors[5].g=25; colors[5].b=64;//light blue (türkis)
    colors[6].r=000; colors[6].g=000; colors[6].b=64;//blue
    colors[7].r=25; colors[7].g=000; colors[7].b=64;//violet


	//PORTB:  ODD/even input, SPI
	DDRB 	= (1 << PB5) |(1 << PB2) | (1 << PB1);	// PB1: Neopixels, PB2: Latch for buttonsPB5 SCK
	PORTB 	= (1 << PC0);	//pull up sync in??
	SPCR 	= (1<<SPE)|(1<<MSTR)|(1<<SPR1)|(0<<SPR0); 		//  enable SPI in Master Mode, clk = fcpu/64 
	//PORTC
	DDRC 	= (1 << PC2) | (1 << PC1) | (1 << PC0); 		// Address Output
	PORTC 	= (1 << PC5) ; 						// pullup for in-sync input


	//PORTD:	Muxes
	DDRD 	= 0xff;
	// ------------------		Pin change Interrupts:
	// Trigger on PC3 = PCINT11
	// Reset on PC4 = PCINT12	
	// Odd/EVEN on PB0 = PCINT0
	PCICR 	= (1 << PCIE1) | (1 << PCIE0);
	PCMSK1 	= (1 << PCINT12) |(1 << PCINT11);
	PCMSK0  = (1 << PCINT0);


	// ------------------		ADC -> 0-0.7V Ramp input on ADC7	
	ADCSRA 	= (1 << ADEN | 1 << ADATE | 1 << ADIE);						// Enable ADC, free running mode, ADC Interrupt
	ADCSRA |= (1 << ADPS2) | (1 << ADPS1);								// prescaler 64
	ADMUX 	= (1 << ADLAR) | 0x07;										// ADC7, we're only reading 8bits, so left adjust result
	ADCSRA |= (1 << ADSC);												// Start Conversion
	

	wdt_enable(WDTO_2S);			// enable watchdog timer
}


// ------------------------------------------------------------------------------
// Interrupts
// ------------------------------------------------------------------------------


// ------------------------------------------------------------------------------
// 													odd/even - vertical blanking 25Hz
// 											
//	check buttons, output steps if in sync with video

ISR (PCINT0_vect) {  	
	// check switches
	if (trigger_inhibit > 0) trigger_inhibit--;
	
	insync = PINC & (1 << PC5);
	
	// check buttons
	checkSPI();
	
	// set leds
	ws2812_sendarray((uint8_t *)led,PIXELS*3);

	// set muxes and address output
	output();
}

// ------------------------------------------------------------------------------
// 													Trigger / Reset

ISR (PCINT1_vect) {
	unsigned char pinstate = PINC;
	if (~last_pinc & (1 << 3)) {
		if (pinstate & (1 << 3)) {					// positive edge only
		//	led[35] = colors[1];
			trigger();
		}
	}
	
	if (~last_pinc & (1 << 4)) {
		if (pinstate & (1 << 4)) {					// positive edge only
			step_idx = 0;
			if (!insync) {
				output();
			}
		}
	}
	last_pinc = pinstate;
}  

// ------------------------------------------------------------------------------
// 														ADC complete interrupt

ISR (ADC_vect) {
	unsigned int ramp_in = ADCH;
	static unsigned int last_ramp_in;
	//ramp_in += 4;		//margin at top
	if (ramp_in > 255) ramp_in = 255;
	
	ramp_in = (3 * last_ramp_in + ramp_in) / 4;
	
	last_ramp_in = ramp_in;

//	if (ramp_in > 2) {step_idx = ramp_in / 32; }
	
/*	unsigned char ramp_in = ADCH;
	static unsigned char last_ramp_in;
	static unsigned char ups[8] 		= {34,66,98,130,162,194,226,255};	// add some hysteresis
	static unsigned char downs[8] 		= {0,30,62,94,126,158,190,222};
	
	if ((last_ramp_in > downs[step_idx]) && (last_ramp_in < ups[step_idx])) {
	
		if ((step_idx == 0) && (ramp_in > 250)) 	{ step_down();  	}	// special circle wrap case
		if ((step_idx == 7) && (ramp_in < 3)) 		{ step_up();  		} 	// special circle wrap case
		if (ramp_in > ups[step_idx]) 				{ step_up();  		}
		if (ramp_in < downs[step_idx]) 				{ step_down();  	}	
		
	}
	
	last_ramp_in = ramp_in;
	*/
}

// ------------------------------------------------------------------------------
// 														Display Stuff


void black() {
    uint8_t i;
    for(i=0; i < PIXELS; i++)
    {    
        led[i].r=0;led[i].g=0;led[i].b=0;
    }
	ws2812_sendarray((uint8_t *)led,PIXELS*3);
	_delay_ms(10);
}

void welcome() {
	unsigned char i;
	unsigned char j;
	unsigned int n;

	for (i=0;i<2;i++) {
		wdt_reset();	
		for(j=0;j<64;j++) {
			led[0].g=j;
			led[PIXELS-1].g=j;
			ws2812_sendarray((uint8_t *)led,PIXELS*3);
			wdt_reset();
			_delay_ms(1);
		}
		for(j=64;j>0;j--) {
			led[0].g=j-1;
			led[PIXELS-1].g=j-1;
			ws2812_sendarray((uint8_t *)led,PIXELS*3);
			wdt_reset();
			_delay_ms(1);
		}
	}
	for (i=0;i<2;i++) {
		wdt_reset();	
		for(j=0;j<64;j++) {
			led[3].g=j;
			led[PIXELS-4].g=j;
			ws2812_sendarray((uint8_t *)led,PIXELS*3);
			wdt_reset();
			_delay_ms(1);
		}
		for(j=64;j>0;j--) {
			led[3].g=j-1;
			led[PIXELS-4].g=j-1;
			ws2812_sendarray((uint8_t *)led,PIXELS*3);
			wdt_reset();
			_delay_ms(1);
		}
	}
		uint8_t k = 1;
	
	for (n=0;n<100;n++) 
    {
    	wdt_reset();
        //shift all vallues by one led
        for(i=PIXELS; i>1; i--) 
            led[i-1]=led[i-2];
        //change colour when colourlength is reached   
        if(k>COLORLENGTH)
        {
            j++;
            if(j>7)
            {
              j=0;
            }

            k=0;
        }
        k++;
        //loop colouers
        
        //fade red
        if(led[0].r<(colors[j].r-FADE))
            led[0].r+=FADE;
            
        if(led[0].r>(colors[j].r+FADE))
            led[0].r-=FADE;

        if(led[0].g<(colors[j].g-FADE))
            led[0].g+=FADE;
            
        if(led[0].g>(colors[j].g+FADE))
            led[0].g-=FADE;

        if(led[0].b<(colors[j].b-FADE))
            led[0].b+=FADE;
            
        if(led[0].b>(colors[j].b+FADE))
            led[0].b-=FADE;

		 _delay_ms(10);
		 ws2812_sendarray((uint8_t *)led,PIXELS*3);
    }
	_delay_ms(10);
}


// ==============================================================================
// main
// ------------------------------------------------------------------------------

int main (void) {



	init();
	welcome();
    black();
	sei();
	
	while(1) {
		wdt_reset();	
		update_leds();		// low priority led update;	
	}
	return 0;
}	
