mirdej/synkie/kicad/sk562-cv2light/sk562-firmware/sk562-firmware.ino

//----------------------------------------------------------------------------------------
//
//	sk562  Firmware		
//						
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
//----------------------------------------------------------------------------------------

#include <FastLED.h>


#define PIN_PIX 1
CRGB                        pixel[1];



void setup() {
    FastLED.addLeds<SK6812, PIN_PIX, GRB>(pixel, 1);
//	FastLED.setBrightness(20);

	for (int hue = 0; hue < 360; hue++) {
    	fill_rainbow( pixel, 1, hue, 7);
	    delay(3);
    	FastLED.show(); 
  	}


}


void loop() {
    int r = analogRead(A0)/4;
    int g = analogRead(A1)/4;
    int b = analogRead(A2)/4;
    
    r += analogRead(A3);
    g += analogRead(A4);
    b += analogRead(A5);
    
    pixel[0]= CRGB(r,g,b);
    FastLED.show(); 
    delay(10);
}
