mirdej/synkie/kicad/sk950-teensy-osc/sk950-teensy-osc-firmware/Logo.h

/**
 * Made with Marlin Bitmap Converter
 * http://marlinfw.org/tools/u8glib/converter.html
 *
 * This bitmap from the file 'anyma-128x16px.gif'
 */
#define SXX7ND_BMPWIDTH  128
#define SXX7ND_BMPHEIGHT 16
const unsigned char bitmap_anyma[] PROGMEM = {
  0x0C,0x00,0x00,0x00,0x00,0x00,0x00,0x00,0x00,0x00,0x00,0x00,0x00,0x00,0x00,0x30, // ....##....................................................................................................................##....
  0x08,0x00,0x00,0x00,0x00,0x00,0x00,0x00,0x00,0x00,0x00,0x00,0x00,0x00,0x00,0x10, // ....#......................................................................................................................#....
  0x08,0x00,0x00,0x00,0x00,0x00,0x00,0x00,0x00,0x00,0x00,0x00,0x00,0x00,0x00,0x10, // ....#......................................................................................................................#....
  0x08,0x00,0x00,0x00,0x00,0x00,0x00,0x00,0x00,0x00,0x00,0x00,0x00,0x00,0x00,0x10, // ....#......................................................................................................................#....
  0x08,0x00,0x0F,0x00,0x07,0xF0,0x00,0xC1,0x80,0x0D,0xEF,0x00,0x01,0xE0,0x00,0x10, // ....#...............####.............#######............##.....##...........##.####.####...............####................#....
  0x08,0x00,0x01,0x80,0x06,0x38,0x00,0x61,0x80,0x0C,0x71,0x80,0x00,0x30,0x00,0x10, // ....#..................##............##...###............##....##...........##...###...##.................##...............#....
  0x08,0x00,0x01,0x80,0x06,0x18,0x00,0x61,0x80,0x0C,0x71,0x80,0x00,0x30,0x00,0x10, // ....#..................##............##....##............##....##...........##...###...##.................##...............#....
  0x08,0x00,0x07,0x80,0x06,0x18,0x00,0x73,0x00,0x0C,0x31,0x80,0x00,0xF0,0x00,0x10, // ....#................####............##....##............###..##............##....##...##...............####...............#....
  0x08,0x00,0x11,0x80,0x06,0x18,0x00,0x33,0x00,0x0C,0x31,0x80,0x02,0x30,0x00,0x10, // ....#..............#...##............##....##.............##..##............##....##...##.............#...##...............#....
  0x08,0x00,0x31,0x80,0x06,0x18,0x00,0x3C,0x00,0x0C,0x31,0x80,0x06,0x30,0x00,0x10, // ....#.............##...##............##....##.............####..............##....##...##............##...##...............#....
  0x08,0x00,0x31,0x80,0x06,0x18,0x00,0x1C,0x00,0x0C,0x31,0x80,0x06,0x30,0x00,0x10, // ....#.............##...##............##....##..............###..............##....##...##............##...##...............#....
  0x08,0x00,0x1C,0xC0,0x06,0x18,0x00,0x18,0x00,0x0C,0x31,0x80,0x03,0x98,0x00,0x10, // ....#..............###..##...........##....##..............##...............##....##...##.............###..##..............#....
  0x08,0x00,0x00,0x00,0x00,0x00,0x00,0x08,0x00,0x00,0x00,0x00,0x00,0x00,0x00,0x10, // ....#.......................................................#..............................................................#....
  0x08,0x00,0x00,0x00,0x00,0x00,0x00,0x18,0x00,0x00,0x00,0x00,0x00,0x00,0x00,0x10, // ....#......................................................##..............................................................#....
  0x08,0x00,0x00,0x00,0x00,0x00,0x00,0xE0,0x00,0x00,0x00,0x00,0x00,0x00,0x00,0x10, // ....#...................................................###................................................................#....
  0x0C,0x00,0x00,0x00,0x00,0x00,0x00,0xE0,0x00,0x00,0x00,0x00,0x00,0x00,0x00,0x70  // ....##..................................................###..............................................................###....
};
